andrasfuchs/BioBalanceDetector/Business/Bio_Balance_Detector_-_Business_Model_Canvas_v4.pdf

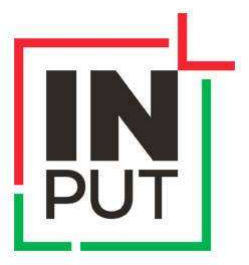
[picture p4: figure]

# Business Canvas Model

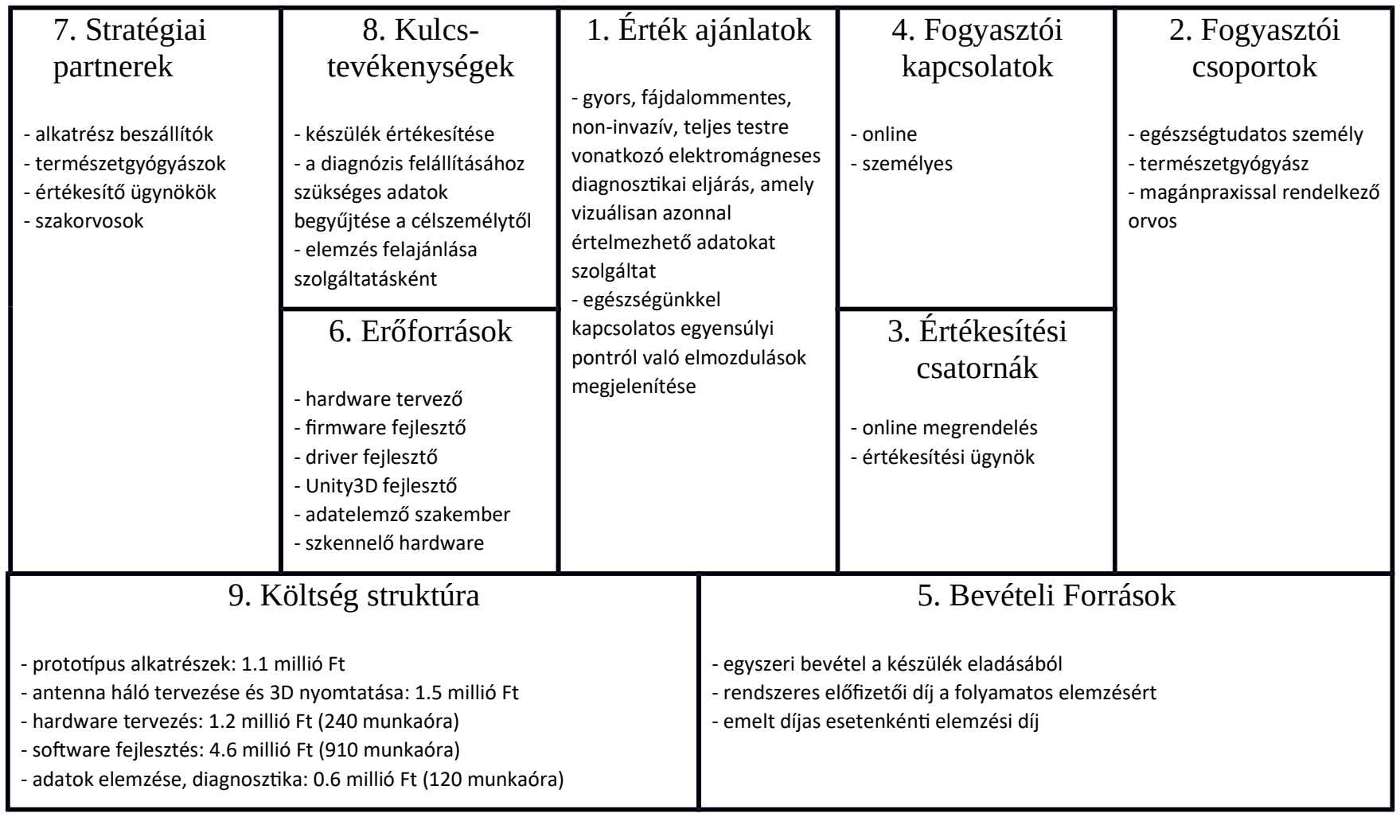
[picture p5: figure]
7. Stratégiai partnerek; - alkatrész beszállítók - természetgyógyászok - értékesítő ügynökök - szakorvosok; 8. Kulcs- tevékenységek; - készülék értékesítése - a diagnózis felállításához szükséges adatok begyűjtése a célszemélytől - elemzés felajánlása szolgáltatásként; 1. Érték ajánlatok; - gyors, fájdalommentes, non-invazív, teljes testre vonatkozó elektromágneses diagnoszkai eljárás, amely vizuálisan azonnal értelmezhető adatokat szolgáltat - egészségünkkel kapcsolatos egyensúlyi pontról való elmozdulások megjelenítése; 4. Fogyasztói kapcsolatok; - online - személyes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

- antenna háló tervezése és 3D nyomtatása: 1.5 millió Ft
- hardware tervezés: 1.2 millió Ft (240 munkaóra)
- soware fejlesztés: 4.6 millió Ft (910 munkaóra)
- adatok elemzése, diagnoszka: 0.6 millió Ft (120 munkaóra)
- egyszeri bevétel a készülék eladásából
- rendszeres előfizetői díj a folyamatos elemzésért
