andrasfuchs/BioBalanceDetector/Business/INPUT-BizDev_201804/INPUT-BizDev-Munkafuzet03_v1_KPI.pdf

### Végső célközönség: Természetgyógyászok

## KPI-ok

### Akvizíció

A fogyasztók figyelmének felkeltése, megszerzése, organikus és nem organikus módon.
Releváns KPIk: Forgalom, említések száma, kattintások költsége, keresési találatok, egy fogyasztó megszerzési költsége, megnyitása ráta

### Aktiváció

A látogatók aktív felhasználóvá tétele.
Releváns KPIk: Regisztrációk, bejelentkezések, befejezett onboarding folyamatok, szolgáltatás legalább egyszeri használata, feliratkozások, előfizetések

### Retention

A fogyasztók meggyőzése, hogy visszatérjenek, folyamatos felhasználói legyenek a terméknek/szolgáltatásnak.
Releváns KPIk: Engagement, legutóbbi látogatás óta eltelt idő, napi - heti aktív használók száma, lemorzsolódás.

### Bevétel

Az üzleti modell függvényében a bevétel keletkezése.
Releváns KPIk: Customer Lifetime Value, bevásárló kosár mérete, konverziós ráta, átkattintási ráta, sikeres vásárlások száma.

### Referálás

“Vírusos” Word of Mouth kommunikáció fogyasztók között. Egymásnak ajánlják a terméket. Releváns KPIk: Elküldött meghívók, Vírus terjedési ciklus, Vírus terjedési együttható?.

## Lean Canvas

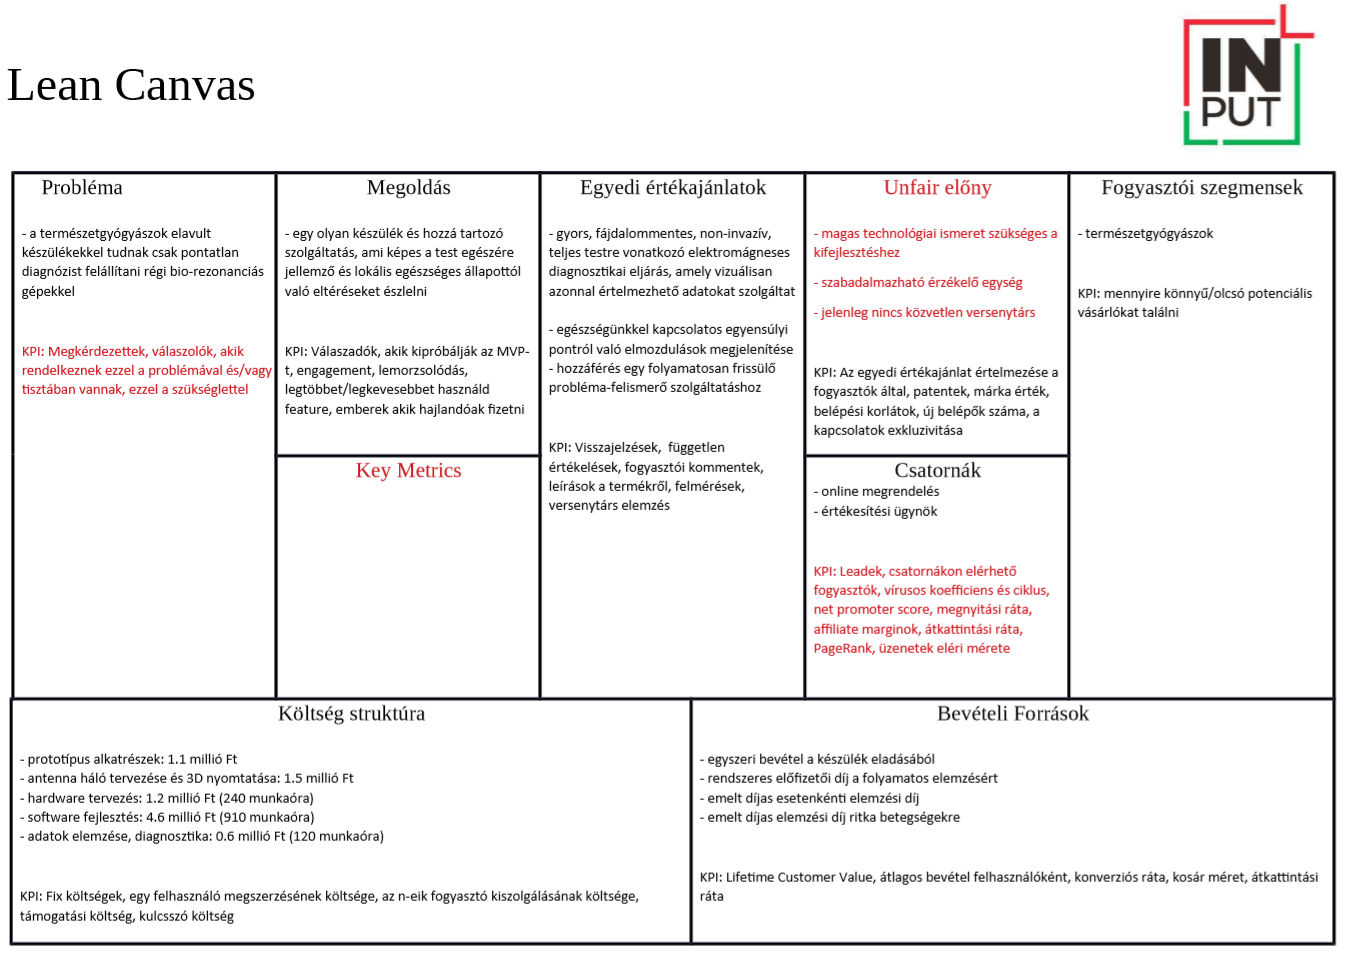
[picture p19: figure]

## Positioning

USP (Unique Selling Proposition)

Abszolút USP:
Gyors, fájdalommentes, non-invazív, teljes testre vonatkozó elektromágneses diagnosztikai eljárás, amely vizuálisan azonnal értelmezhető adatokat szolgáltat. A készülékhez tartozó szolgáltatás folyamatosan frissülő diagnosztikai paramétereknek köszönhetően egyre nagyobb biztonsággal egyre több betegséget egyre korábban képes felismerni.

Relatív UPS: a jelenleg versenytársnak tekinthető bio-rezonanciás készülékek nagyon drágák, 10 éves technológiára épülnek, lassúak, nem vizualizálják az eredményeket, és nem alkalmasak lokális diagnosztikára. Hozzájuk tartozó szolgáltatás nem létezik, vagy minimális hibajavítási ügyfélszolgálat.

## Online kampány
