andrasfuchs/BioBalanceDetector/Business/INPUT-BizDev_201804/INPUT-BizDev-Munkafuzet03_v3.pdf

### Elemek (Természetgyógyászok - magyar)

1. Főcím, alcím, emlékeztető (Unique Selling Proposition, USP)
a. Biorezonancia a jövőből
b. Megérkezett a biorezonanciás készülékek új generációja
2. Felnagyított Wacom tablet függőlegesen, előtte egy alak és mellette egy monitoron a hőkép a testről
3. Űrlap: Értesülj első kézből
Iratkozz fel, hogy megtudd, mi is a fizikai jelenség, amit megjelenítünk. Az akcióinkról is a listáról kapsz majd értesítést.
4. Ajánlat:

A forradalmi Bio Balance Detector fali érzékelő megállapítja, ha:
- Hőemelkedésed van, de nem tudod mitől?
- Fáradékony vagy és nem tudod az okát?
- Allergiás reakciód van és nem múlik el?
- Ki szeretnél gyógyulni az ételérzékenységből?
- Orvosról orvosra jársz, és nem tudják megmondani hol a baj?
- Kiváncsi vagy, hogy milyen állapotban van a tested, mire kell jobban figyelned?

Ha beállsz a Bio Balance Detector elé, a képernyőn egyből láthatod a figyelmet igénylő szerveidet! A készülékhez akkreditált szakembereink diagnózisát is kérheted egyetlen gombnyomással.
5. Bizonyíték
a. A számok magukért beszélnek.
Eddig 3’393 mérés készült, és 43’221 potenciális betegségre hívtuk fel a figyelmet. Benned vajon mennyi kórokozó lapul támadásra várva?
b. Nálunk a biztonság az első.
A Bio Balance Detector megfelel az ide vonatkozó ISO és IEEE szabványoknak, ráadásul teljesen passzív, non-invazív módon térképezi fel a testet körülvevő gyenge tereket.
c. Azonnali diagnózis Mesterséges Intelligenciával.
Az általunk fejlesztett, de mindenki által elérhető (és ellenőrizhető) mesterséges intelligencia segít a betegségek korai felfedezésében.
d. Távoli segítségnyújtás.
Ha bármilyen kérdés merül fel a mérés során, minősített szakembereink várják a kérdéseidet és kérésedre a mérései adatok alapján akár távoli diagnózist is fel tudnak állítani.

Template?
http://preview.themeforest.net/item/aonomy-app-landing-page/full_screen_preview/21460999

Paletta?
http://paletton.com/#uid=12x050k9GeI5jEL9bn6e07Lkl4n

### Elemek (Természetgyógyászok - angol)

6. Főcím, alcím, emlékeztető (Unique Selling Proposition, USP)
a. Bioresonance of the future
b. Next generation bioresonance device with Artificial Intelligence assisted diagnostics
7. Felnagyított Wacom tablet függőlegesen, előtte egy alak és mellette egy monitoron a hőkép a testről
8. Űrlap: Be the first to know
Subscribe to our newsletter to know more about the device and physical phenomena. You will be the first to know about our members-only discounts!
9. Ajánlat:

The revolutionary wall-mounted Bio Balance Detector can:
- Detect the part of your body where you have an inflammation
- Investigate the reason of your fatigue
- Find the focal point of your allergies
- Tell you if you have a food allergy/poisoning reaction
- Help with a diagnosis if the doctors can’t find the reason of your sickness
- Generate a report on your body’s current health condition

Step in front of the Bio Balance Detector and let the computer do work on the diagnostics. You will get a visual image of your organs with an indication of the places where attention is needed. If you need special assistance, you can send your data to our accredited specialists with just one click.
10. Bizonyíték
a. Our Numbers
We have successfully completed 3’393 measurements so far and potentially prevented 43’221 health issues. Are you curious what kinds of pathogens are living inside you waiting for the right moment to strike?
b. Safety First
Bio Balance Detector is certified by both ISO and IEEE, and to the top of that it works in a totally passive and non-invasive way to map out the weak electromagnetic field around our bodies.
c. Instant Diagnostics with AI
Our Artificial Intelligence algorithm is a product of our hard work and we made it open source. This level of transparency means that anybody can verify or extend our findings so it can detect more and more health issues as it matures.
d. Remote Assistance
Ha bármilyen kérdés merül fel a mérés során, minősített szakembereink várják a kérdéseidet és kérésedre a mérései adatok alapján akár távoli diagnózist is fel tudnak állítani.

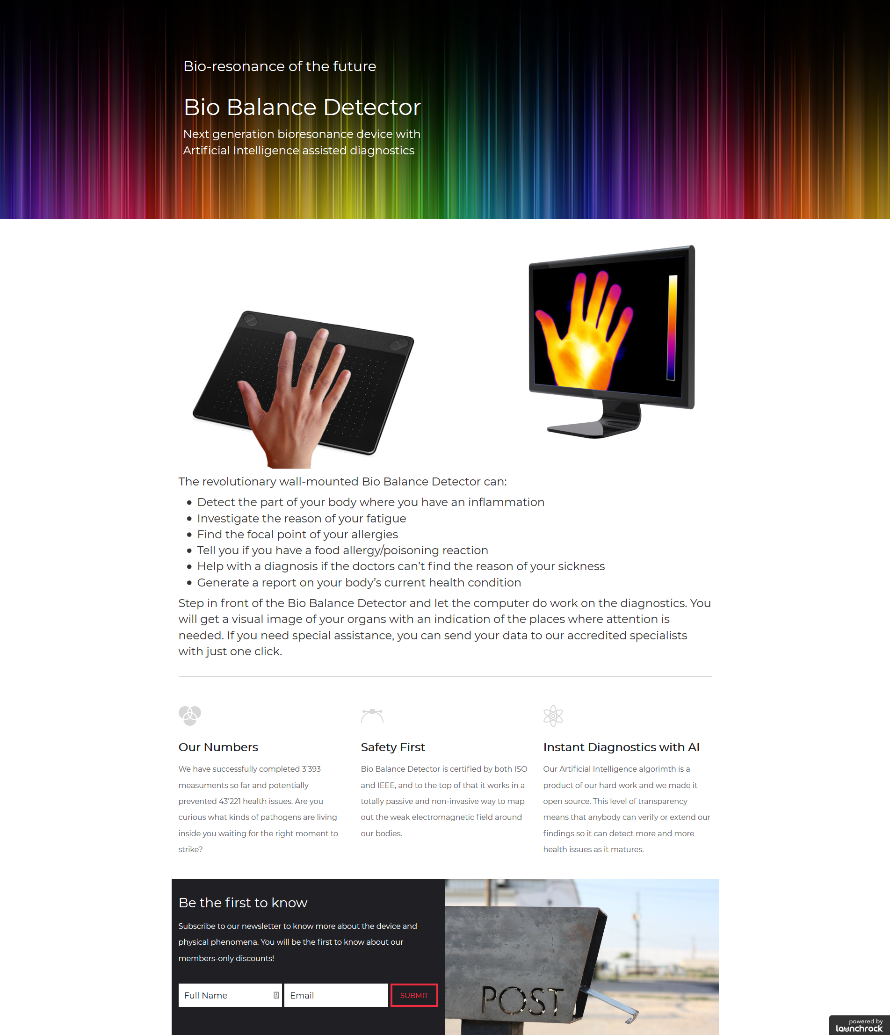
[picture p20: page 3]

http://biobalancedetector.launchrock.com/

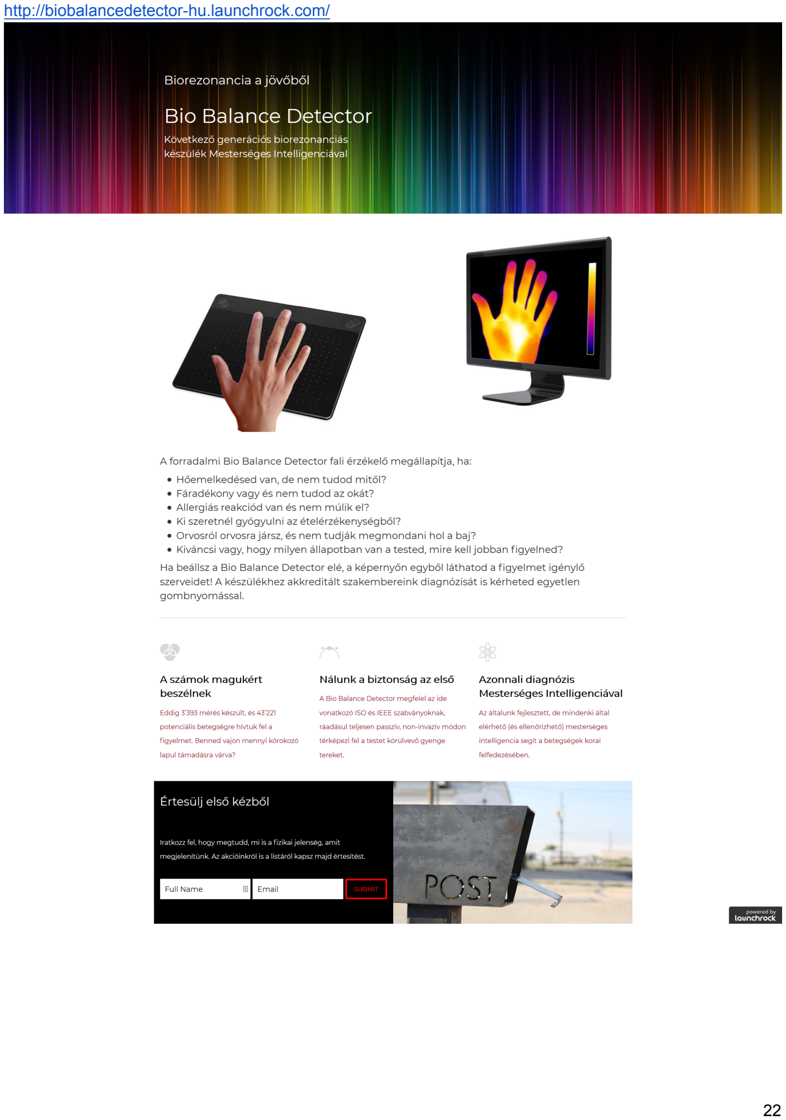
[picture p21: page 4]

http://biobalancedetector-hu.launchrock.com/

## KPI-ok

### Akvizíció

A fogyasztók figyelmének felkeltése, megszerzése, organikus és nem organikus módon.
Releváns KPIk: Forgalom, említések száma, kattintások költsége, keresési találatok, egy fogyasztó megszerzési költsége, megnyitása ráta

### Aktiváció

A látogatók aktív felhasználóvá tétele.
Releváns KPIk: Regisztrációk, bejelentkezések, befejezett onboarding folyamatok, szolgáltatás legalább egyszeri használata, feliratkozások, előfizetések

### Retention

A fogyasztók meggyőzése, hogy visszatérjenek, folyamatos felhasználói legyenek a terméknek/szolgáltatásnak.
Releváns KPIk: Engagement, legutóbbi látogatás óta eltelt idő, napi - heti aktív használók száma, lemorzsolódás.

### Bevétel

Az üzleti modell függvényében a bevétel keletkezése.
Releváns KPIk: Customer Lifetime Value, bevásárló kosár mérete, konverziós ráta, átkattintási ráta, sikeres vásárlások száma.

### Referálás

“Vírusos” Word of Mouth kommunikáció fogyasztók között. Egymásnak ajánlják a terméket. Releváns KPIk: Elküldött meghívók, Vírus terjedési ciklus, Vírus terjedési együttható?.

## Lean Canvas


## Positioning

USP (Unique Selling Proposition)

Abszolút USP:
Gyors, fájdalommentes, non-invazív, teljes testre vonatkozó elektromágneses diagnosztikai eljárás, amely vizuálisan azonnal értelmezhető adatokat szolgáltat. A készülékhez tartozó szolgáltatás folyamatosan frissülő diagnosztikai paramétereknek köszönhetően egyre nagyobb biztonsággal egyre több betegséget egyre korábban képes felismerni.

Relatív UPS: a jelenleg versenytársnak tekinthető bio-rezonanciás készülékek nagyon drágák, 10 éves technológiára épülnek, lassúak, nem vizualizálják az eredményeket, és nem alkalmasak lokális diagnosztikára. Hozzájuk tartozó szolgáltatás nem létezik, vagy minimális hibajavítási ügyfélszolgálat.

## Online kampány

### Google Adwords

Campaign: BBD LaunchRock Landing Page Test #1 [1,500.00 HUF/day]

Keywords (by Google Keyword Planner)
best bioresonance machine
bio resonance device
bio resonance testing machine bioresonance device
bioresonance machine
bioresonance machine for sale bioresonance machine price bioresonance scanning
bioresonance testing
bioresonance therapy
bioresonance therapy devices bioresonance therapy machine

Ad
biobalancedetector.launchrock.com/
Bio Balance Detector | Bioresonance Device
Quick, painless, non-invasive, whole body bio-resonance device with AI imaging

### Facebook Ads Manager

Az Ads Manager és a Power Editor most már egy alkalmazás és a jobb felső sarokban lévő háromszöggel lehet elővarázsolni.

TODO: Facebook Page is kell hozzá

TODO: fókuszáltabb célcsoport kellene: nem, életkor, érdeklődési körök -> vissza a Customer Persona Map-hez és Customer Empathy Map-hez

TODO: Facebook Form-oknál mik a jobban működő módszerek

Campaign:
BBD LaunchRock Landing Page Test #2

Ad Set ame:
US-UK - 45+ - Healthy Living (26M reach)

Audience
45-65+ Healthy living

Location:
United Kingdom, United States

Age:
45 - 65+

Language:
English (UK) or English (US)

People Who Match:
Interests: Organic food, Personal care, Healthy food, Living a Healthy Lifestyle, Health & wellness, Living Healthy, Detox, Diet food, Anti-aging cream, Healthy Life, Natural foods or Organic product, Behaviors: Natural and organics

Interest expansion:
Off

Ad

Text
Quick, painless, non-invasive, whole body bio-resonance device with AI imaging

Display Link
biobalancedetector.launchrock.com/

Headline
High-tech Bioresonance

News Feed Link Description Say no to drugs,get better faster!

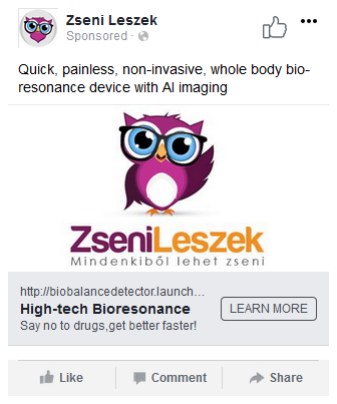
[picture p22: figure]
