andrasfuchs/BioBalanceDetector/Hardware/Design/BBD-Proto6-Functional_Diagram_v1.pdf

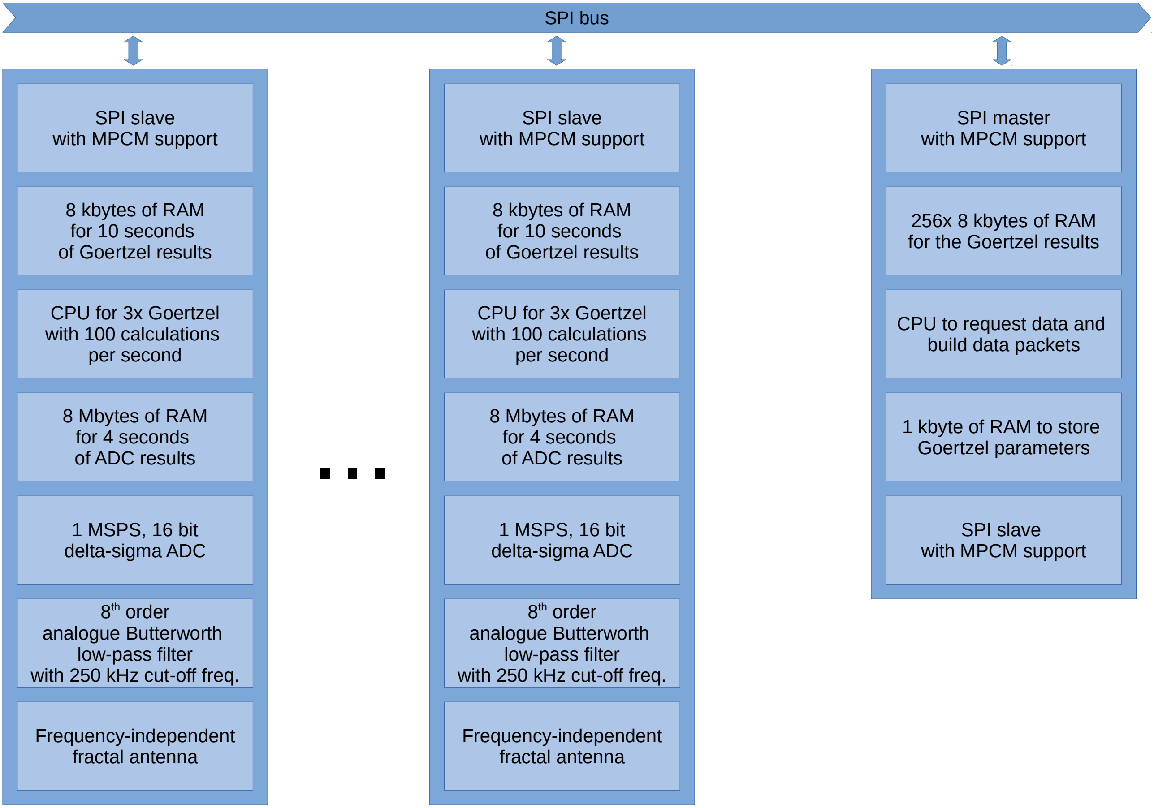
[picture p23: figure]
1 MSPS, 16 bit delta-sigma ADC; th order analogue Butterworth low-pass filter with 250 kHz cut-off freq.; Frequency-independent fractal antenna; 8 Mbytes of RAM for 4 seconds of ADC results; CPU for 3x Goertzel with 100 calculations per second; 8 kbytes of RAM for 10 seconds of Goertzel results; SPI slave with MPCM support; 1 kbyte of RAM to store Goertzel parameters; CPU to request data and build data packets; 256x 8 kbytes of RAM for the Goertzel results; SPI master with MPCM support; SPI bus
