andrasfuchs/BioBalanceDetector/Business/Bio_Balance_Detector_-_Business_Model_Canvas_v1.pdf

# Business Canvas Model

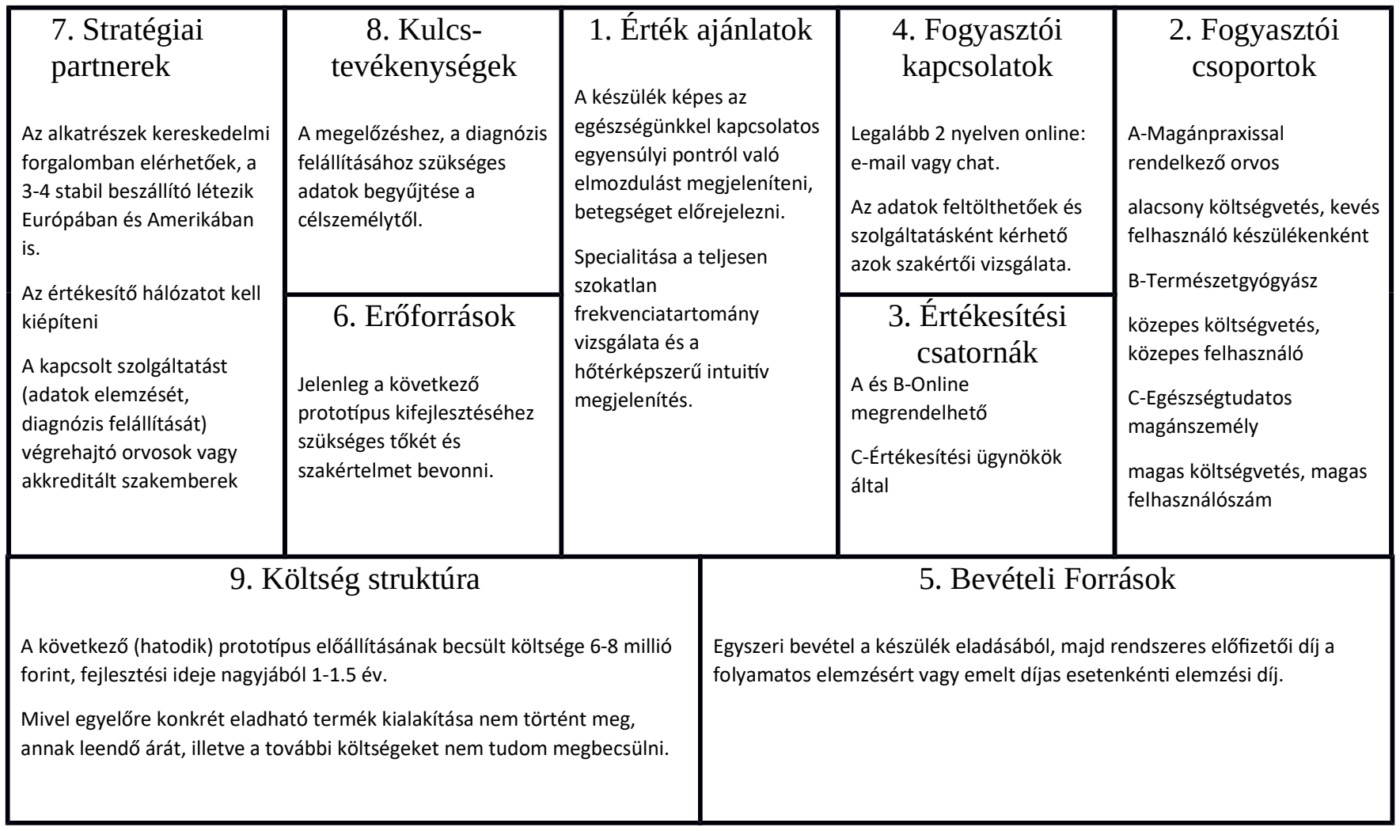
[picture p24: figure]
7. Stratégiai partnerek; Az alkatrészek kereskedelmi forgalomban elérhetőek, a 3-4 stabil beszállító létezik Európában és Amerikában is.; Az értékesítő hálózatot kell kiépíteni; A kapcsolt szolgáltatást (adatok elemzését, diagnózis felállítását) végrehajtó orvosok vagy akkreditált szakemberek; 8. Kulcs- tevékenységek; A megelőzéshez, a diagnózis felállításához szükséges adatok begyűjtése a célszemélytől.; 1. Érték ajánlatok; A készülék képes az egészségünkkel kapcsolatos egyensúlyi pontról való elmozdulást megjeleníteni, betegséget előrejelezni.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

A következő (hatodik) protopus előállításának becsült költsége 6-8 millió forint, fejlesztési ideje nagyjából 1-1.5 év.
Mivel egyelőre konkrét eladható termék kialakítása nem történt meg, annak leendő árát, illetve a további költségeket nem tudom megbecsülni.

Egyszeri bevétel a készülék eladásából, majd rendszeres előfizetői díj a folyamatos elemzésért vagy emelt díjas esetenkén elemzési díj.
