andrasfuchs/BioBalanceDetector/Business/Bio_Balance_Detector_-_Business_Model_Canvas_v2.pdf

# Business Canvas Model

### 7. Stratégiai partnerek

Az alkatrészek kereskedelmi forgalomban elérhetőek, 3-

### 4 stabil beszállító létezik

Európában és Amerikában
is.
Az értékesítő hálózatot kell kiépíteni, az ügynököket
jutalmazni.
A kapcsolt szolgáltatást
(adatok elemzését,
diagnózis felállítását)
végrehajtó orvosokat vagy
akkreditált szakembereket
ki kell képezni, és össze kell kötni az őket igénylőkkel.

### 8. Kulcstevékenységek

A megelőzéshez, a diagnózis felállításához szükséges
adatok begyűjtése a
célszemélytől.
Elemzés felajánlása
szolgáltatásként.

### 1. Érték ajánlatok

A készülék képes az
egészségünkkel kapcsolatos egyensúlyi pontról való
elmozdulást megjeleníteni, betegséget előrejelezni.
Specialitása a teljesen
szokatlan
frekvenciatartomány
vizsgálata és a
hőtérképszerű intuiv
megjelenítés.

### 4. Fogyasztói kapcsolatok

Több nyelven online: e-mailben vagy chat-en.
Az adatok feltölthetőek és szolgáltatásként kérhető
azok szakértői vizsgálata.


### 2. Fogyasztói csoportok

A-Egészségtudatos
magánszemély
alacsony költségvetés, kevés felhasználó készülékenként B-Természetgyógyász
közepes költségvetés,
közepes felhasználószám
C-Magánpraxissal
rendelkező orvos
magas költségvetés, magas
felhasználószám

### 6. Erőforrások

Jelenleg a következő
protopus kifejlesztéséhez szükséges tőkét és
szakértelmet szükséges
bevonni.

### 3. Értékesítési csatornák

A és B-Online
megrendelhető
C-Értékesítési ügynökök
segítségével (mint a
gyógyszereknél)

### 9. Költség struktúra

A következő (hatodik) protopus előállításának becsült költsége 6-8 millió forint, fejlesztési ideje nagyjából 1-1.5 év.
Mivel egyelőre konkrét eladható termék kialakítása nem történt meg, annak leendő árát, illetve a további költségeket nem tudom megbecsülni.

### 5. Bevételi Források

Egyszeri bevétel a készülék eladásából, majd rendszeres előfizetői díj a folyamatos elemzésért (nagy forgalmú helyeken, mint pl. orvosi rendelők) vagy emelt díjas esetenkén elemzési díj (magánszemélyeknek).
