andrasfuchs/BioBalanceDetector/Business/Bio_Balance_Detector_-_Pitch-deck_background.png

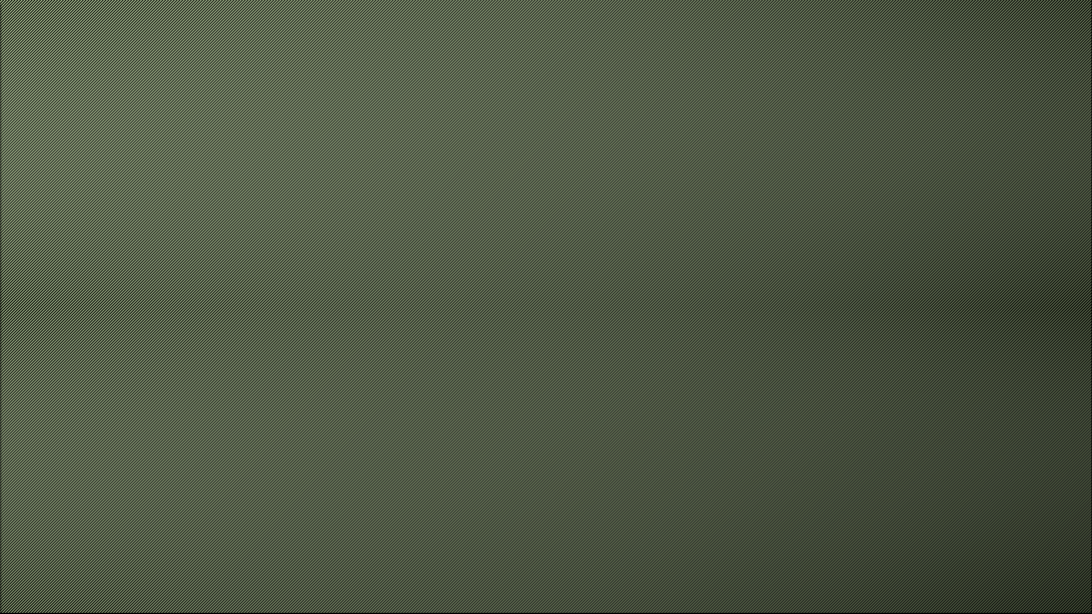
Business/Bio_Balance_Detector_-_Pitch-deck_background.png
