andrasfuchs/BioBalanceDetector/Business/INPUT-BizDev_201804/abstract-rainbow-colors.jpg

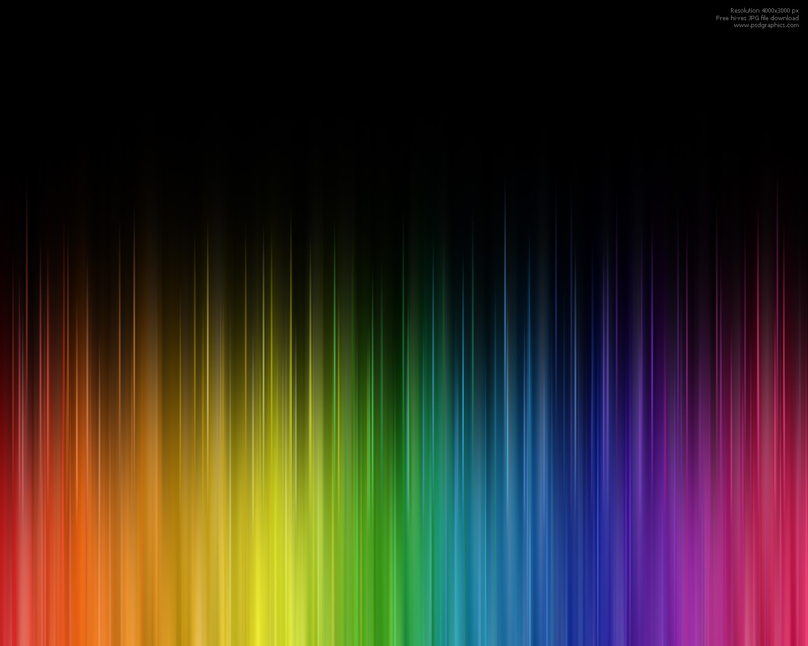
Business/INPUT-BizDev_201804/abstract-rainbow-colors.jpg
