andrasfuchs/BioBalanceDetector/Business/INPUT-BizDev_201804/TabletHandMonitor.jpg

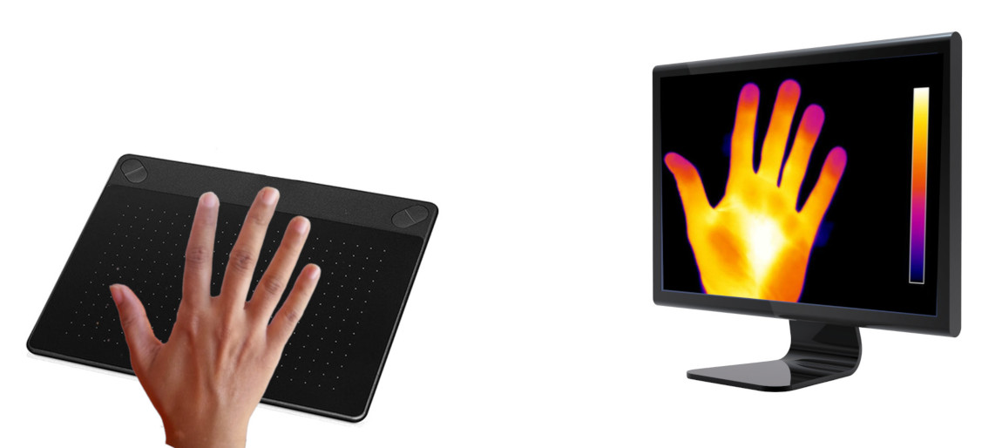
Business/INPUT-BizDev_201804/TabletHandMonitor.jpg
