andrasfuchs/BioBalanceDetector/Business/INPUT-BizDev_201804/TabletHandMonitor/InfraredHand.jpg

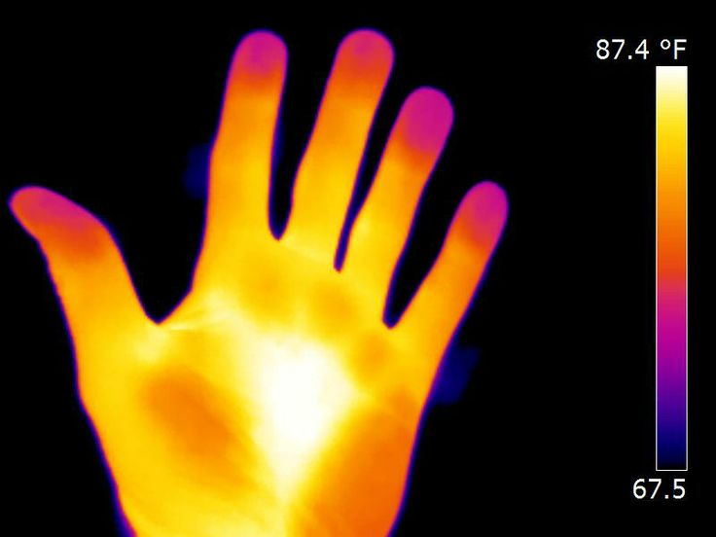
Business/INPUT-BizDev_201804/TabletHandMonitor/InfraredHand.jpg
