andrasfuchs/BioBalanceDetector/Hardware/Datasheets/Proto04/Arduino_Uno_Poster-1024x577.jpg

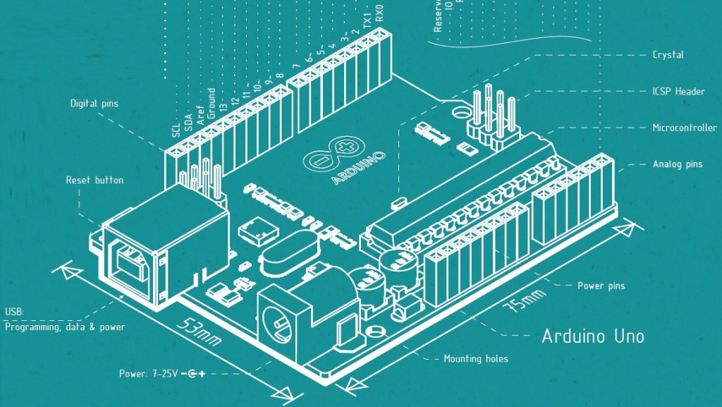
Hardware/Datasheets/Proto04/Arduino_Uno_Poster-1024x577.jpg
