andrasfuchs/BioBalanceDetector/Hardware/Datasheets/Proto04/BraveKit-AVR-ISPmk2-CL/USB_AVR_mkII_with_DIPprog-600x600.jpg

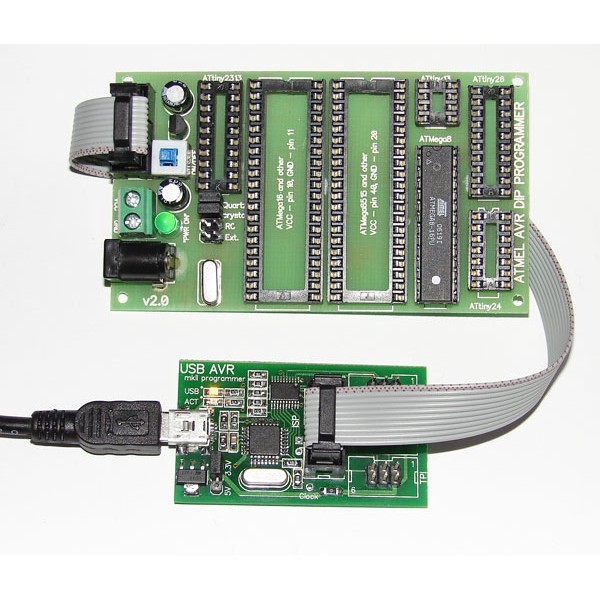
Hardware/Datasheets/Proto04/BraveKit-AVR-ISPmk2-CL/USB_AVR_mkII_with_DIPprog-600x600.jpg
