andrasfuchs/BioBalanceDetector/Hardware/Datasheets/Proto06/Analog_Devices_AD7616_functional_block_diagram.png

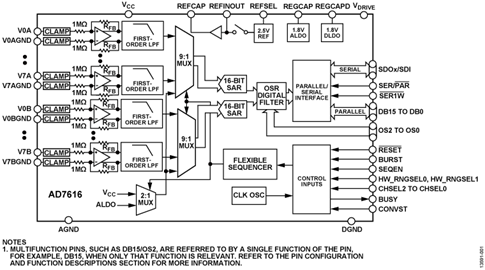
Hardware/Datasheets/Proto06/Analog_Devices_AD7616_functional_block_diagram.png
