andrasfuchs/BioBalanceDetector/Hardware/Design/Antenna/sierpinski_triangle_by_love1008.jpg

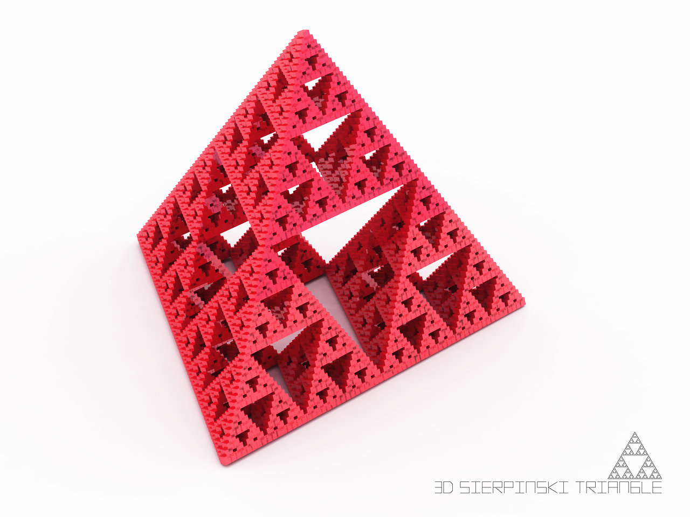
Hardware/Design/Antenna/sierpinski_triangle_by_love1008.jpg
