andrasfuchs/BioBalanceDetector/Hardware/Design/BBD-Proto6-Functional_Diagram_v2.png

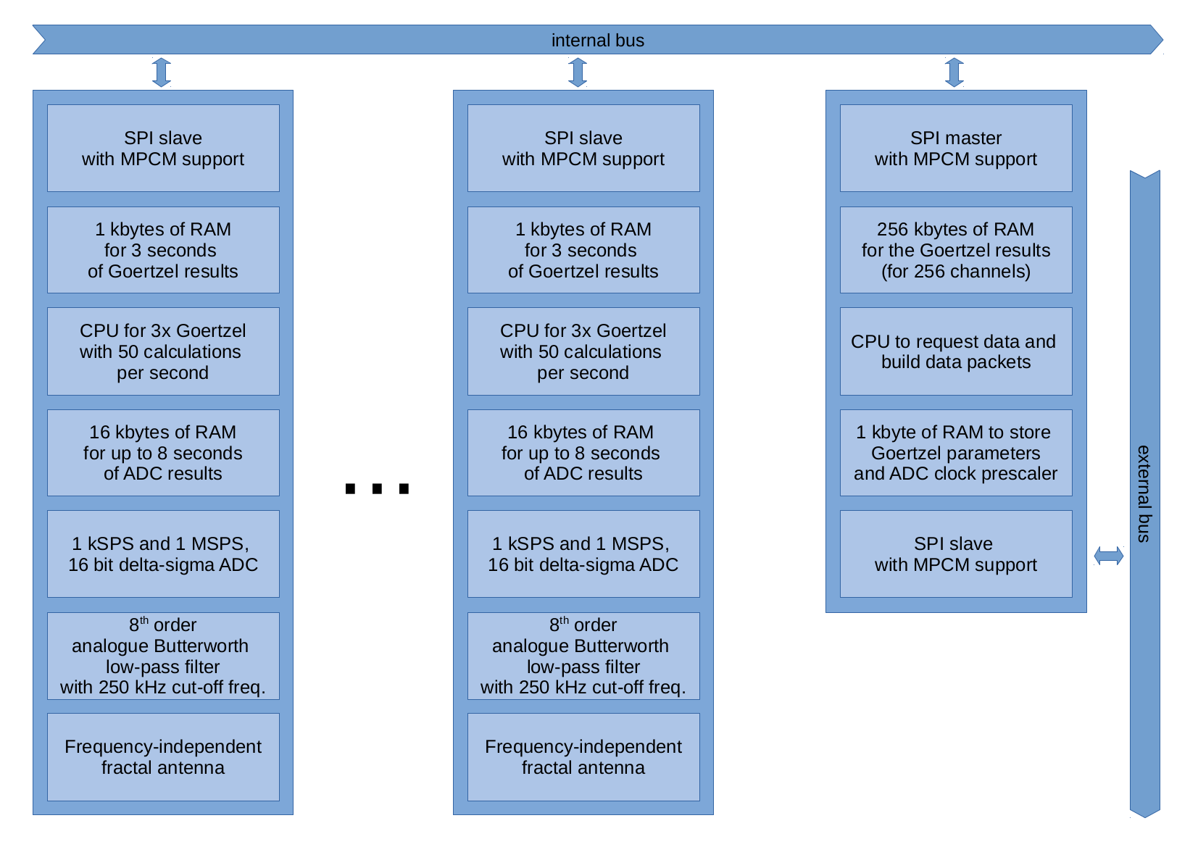
Hardware/Design/BBD-Proto6-Functional_Diagram_v2.png
