andrasfuchs/BioBalanceDetector/Hardware/Design/fractal-9-728.jpg

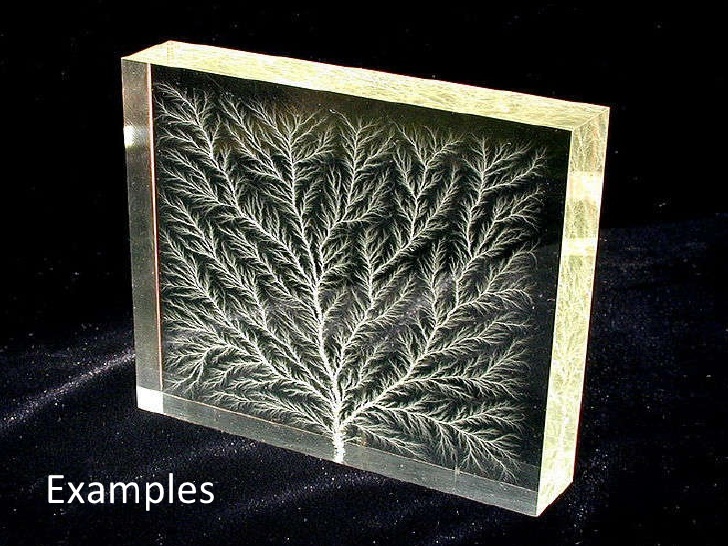
Hardware/Design/fractal-9-728.jpg
