andrasfuchs/BioBalanceDetector/Hardware/Design/fractals-in-nature-wallpapers-full-hd.jpg

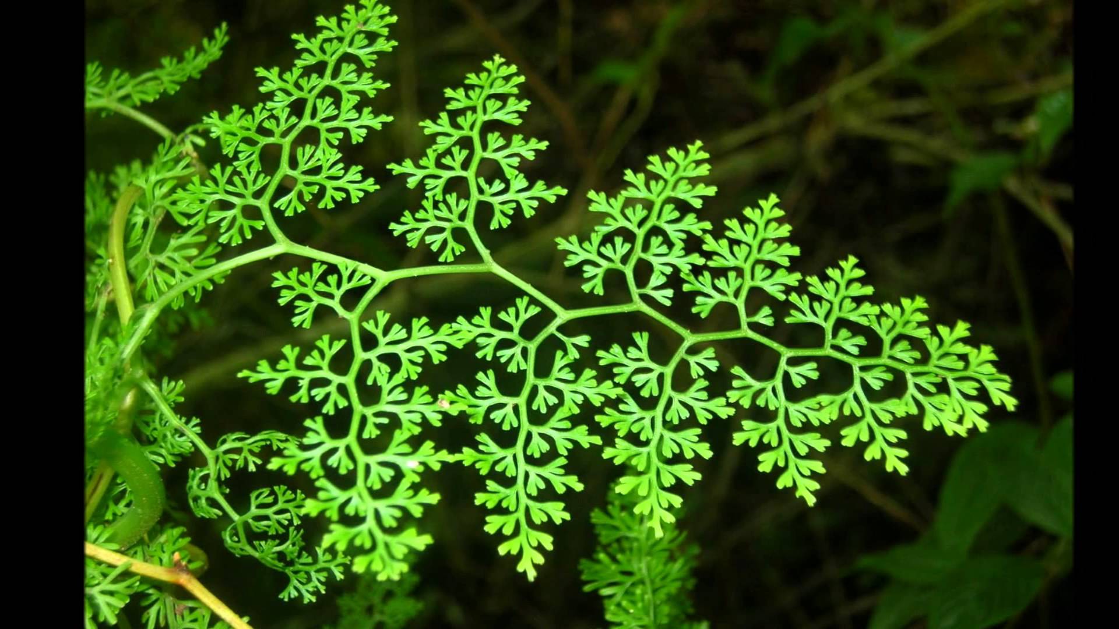
Hardware/Design/fractals-in-nature-wallpapers-full-hd.jpg
