andrasfuchs/BioBalanceDetector/Measurements/Spooky2/01_IrregularVoltageReport/02_AmbientRadiation-PowerAdapterDisconnected.png

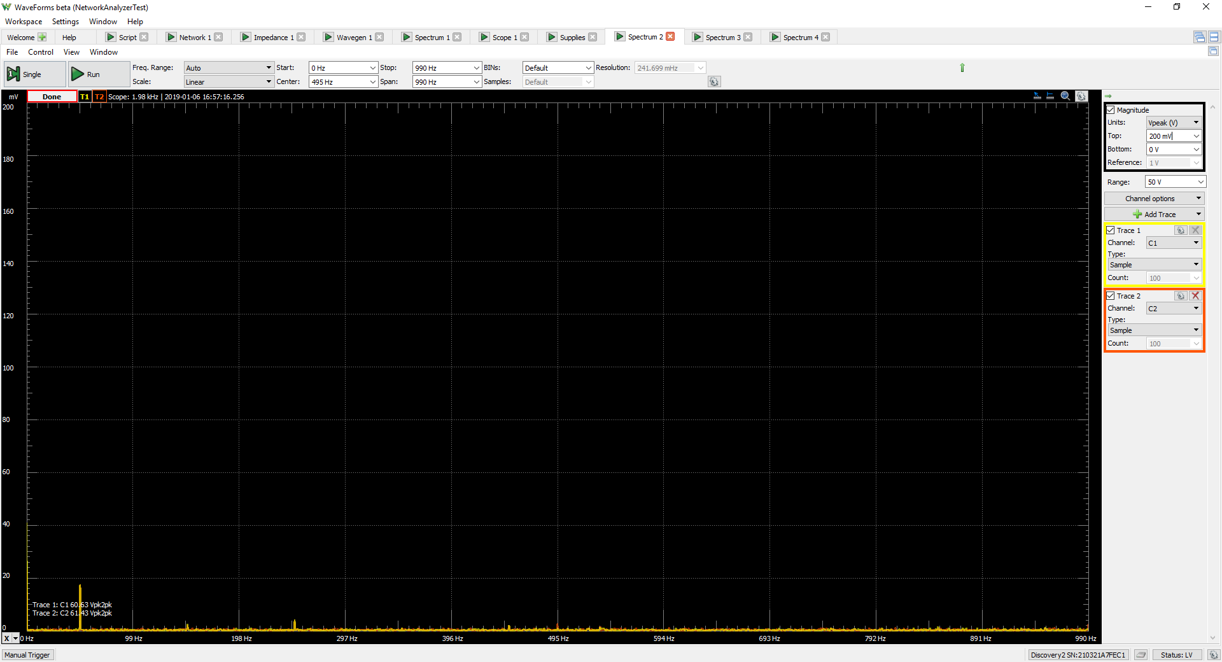
Measurements/Spooky2/01_IrregularVoltageReport/02_AmbientRadiation-PowerAdapterDisconnected.png
