andrasfuchs/BioBalanceDetector/Measurements/Spooky2/01_IrregularVoltageReport/04_PowerAdapterConnectedPoweredOff_200mV.png

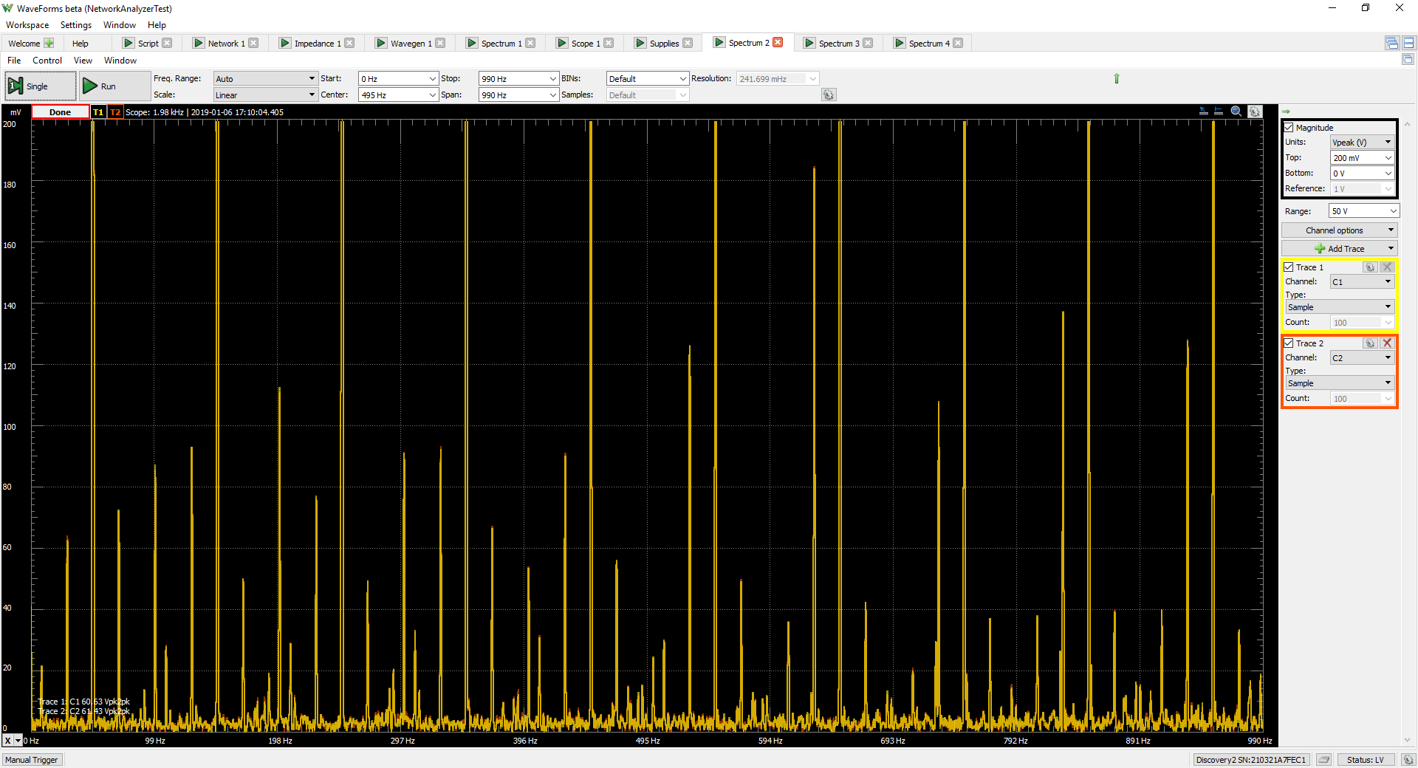
Measurements/Spooky2/01_IrregularVoltageReport/04_PowerAdapterConnectedPoweredOff_200mV.png
