andrasfuchs/BioBalanceDetector/Measurements/Spooky2/01_IrregularVoltageReport/05_PowerAdapterConnectedPoweredOff_25V.png

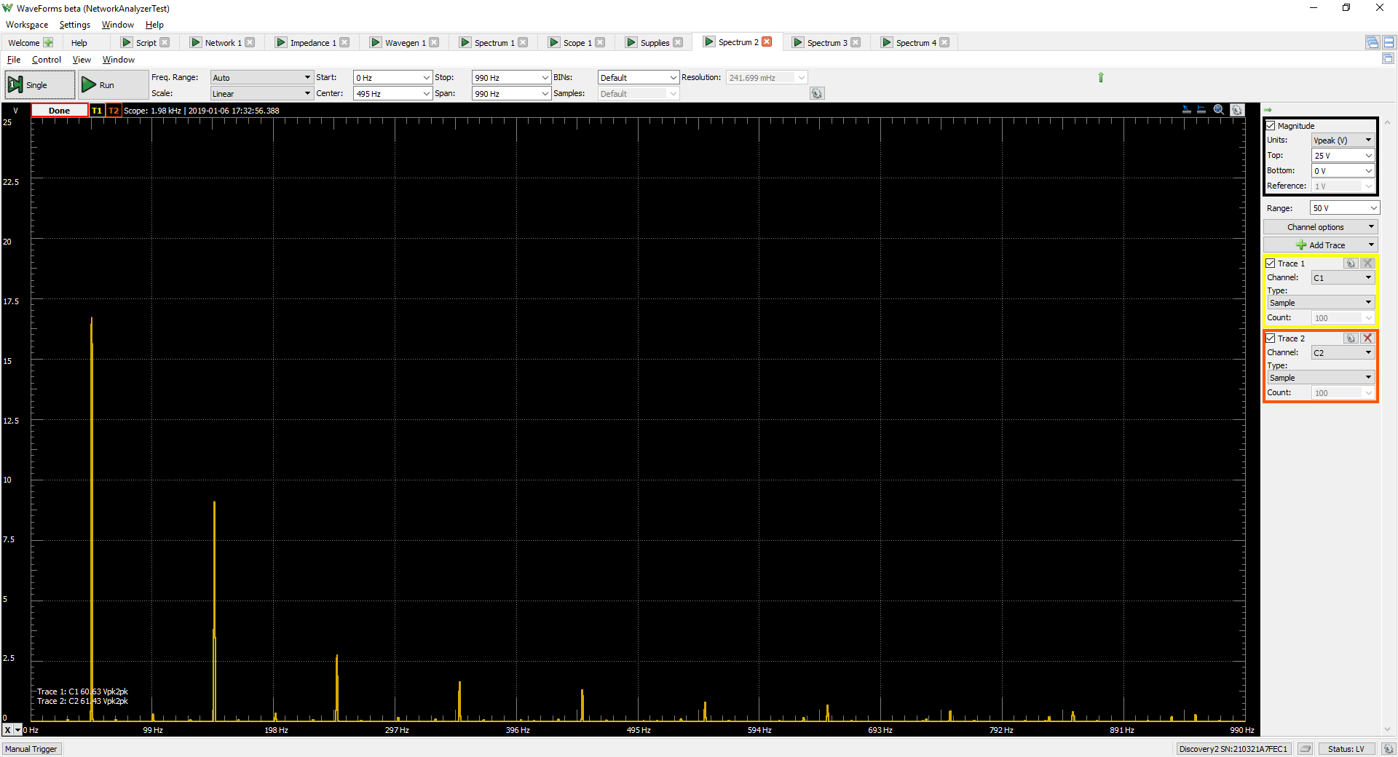
Measurements/Spooky2/01_IrregularVoltageReport/05_PowerAdapterConnectedPoweredOff_25V.png
