andrasfuchs/BioBalanceDetector/Measurements/Spooky2/01_IrregularVoltageReport/06_PowerAdapterConnectedPoweredOn_25V.png

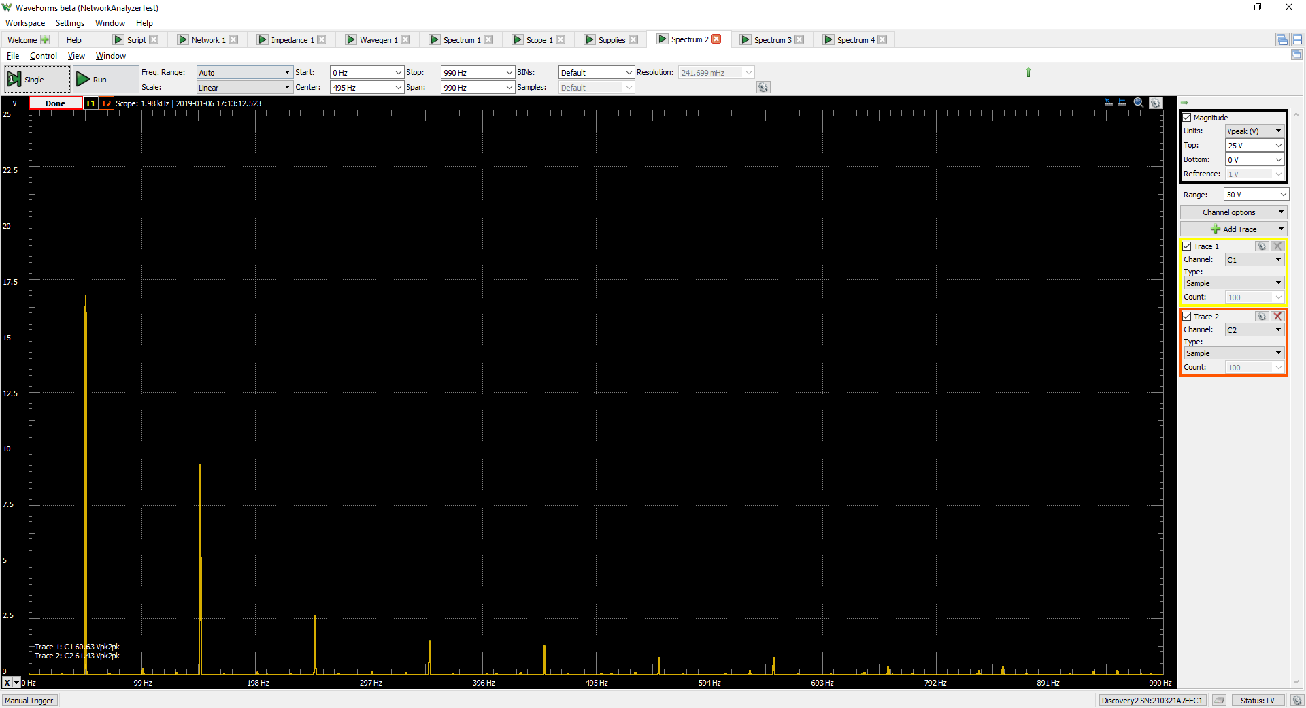
Measurements/Spooky2/01_IrregularVoltageReport/06_PowerAdapterConnectedPoweredOn_25V.png
