andrasfuchs/BioBalanceDetector/Measurements/Spooky2/01_IrregularVoltageReport/07_PowerAdapterConnectedPoweredOn_422-442Hz_2V.png

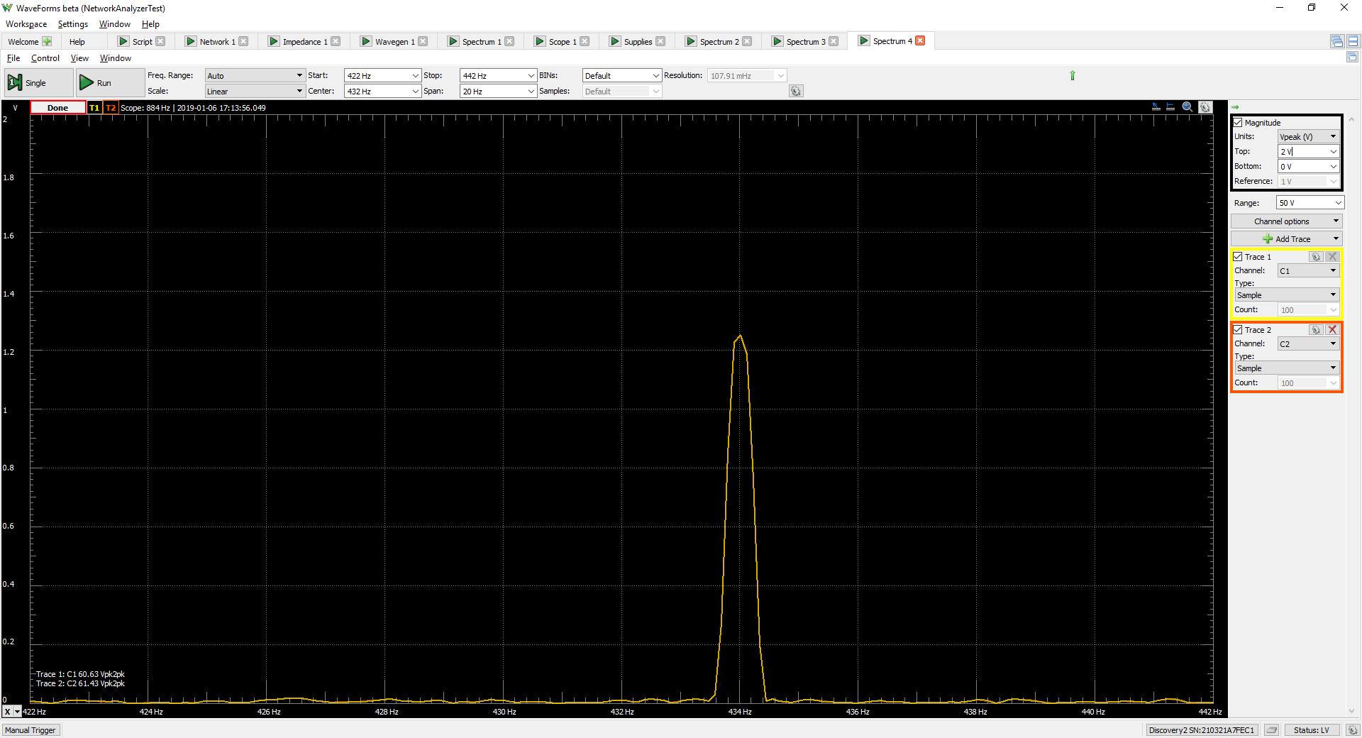
Measurements/Spooky2/01_IrregularVoltageReport/07_PowerAdapterConnectedPoweredOn_422-442Hz_2V.png
