andrasfuchs/BioBalanceDetector/Measurements/Spooky2/01_IrregularVoltageReport/08_Spooky2Settings.png

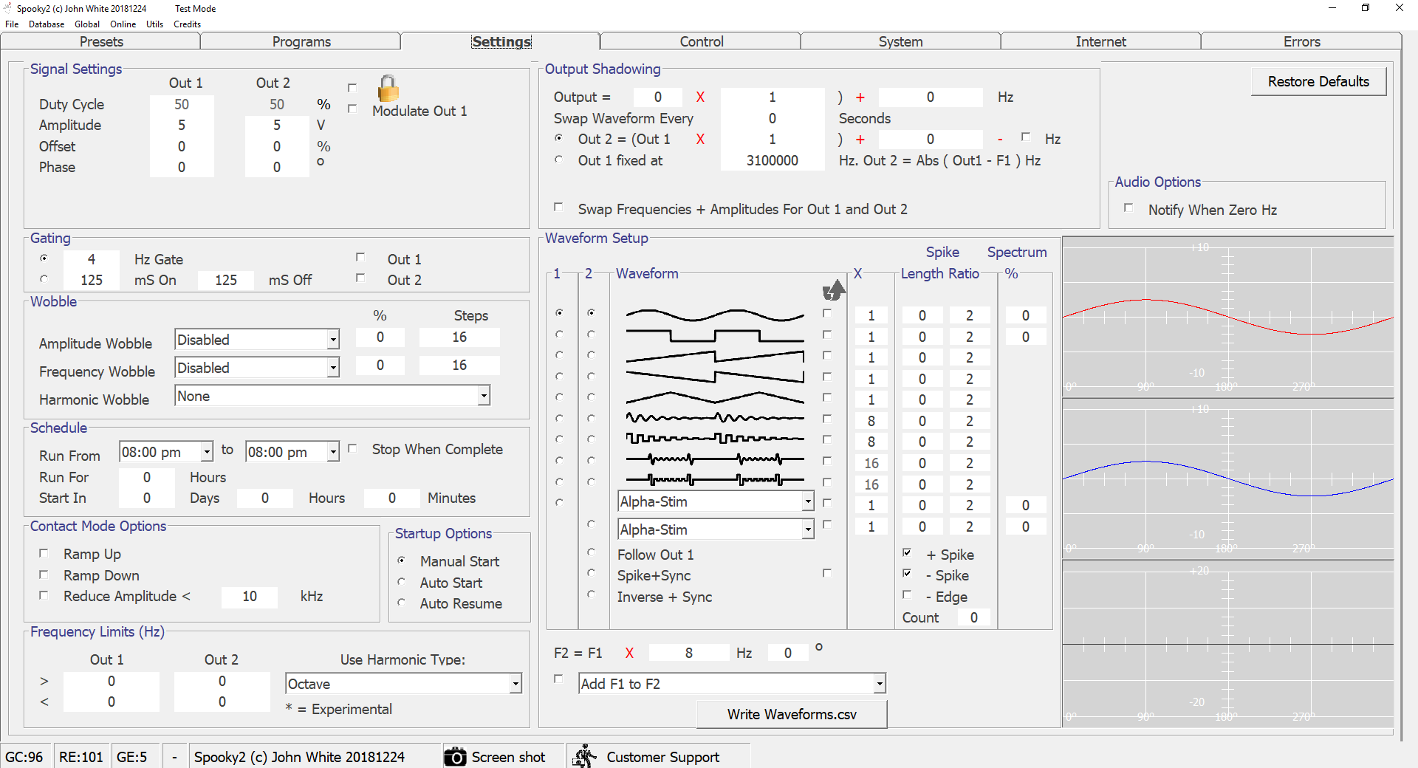
Measurements/Spooky2/01_IrregularVoltageReport/08_Spooky2Settings.png
