andrasfuchs/BioBalanceDetector/Measurements/Spooky2/01_IrregularVoltageReport/09_Spooky2Control_432Hz.png

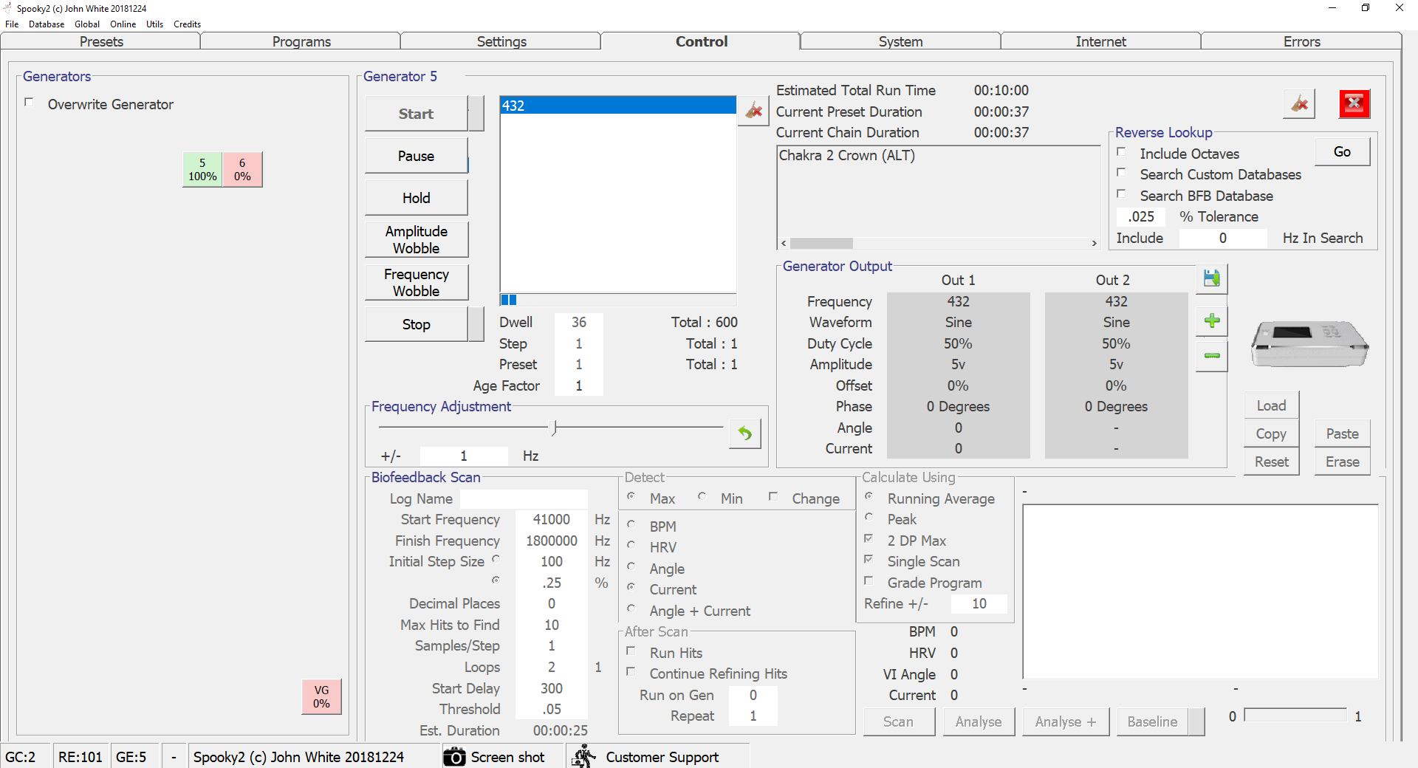
Measurements/Spooky2/01_IrregularVoltageReport/09_Spooky2Control_432Hz.png
