andrasfuchs/BioBalanceDetector/Measurements/Spooky2/01_IrregularVoltageReport/10_PowerAdapterConnectedPoweredOn-G1Sin432Hz_422-442Hz_2V.png

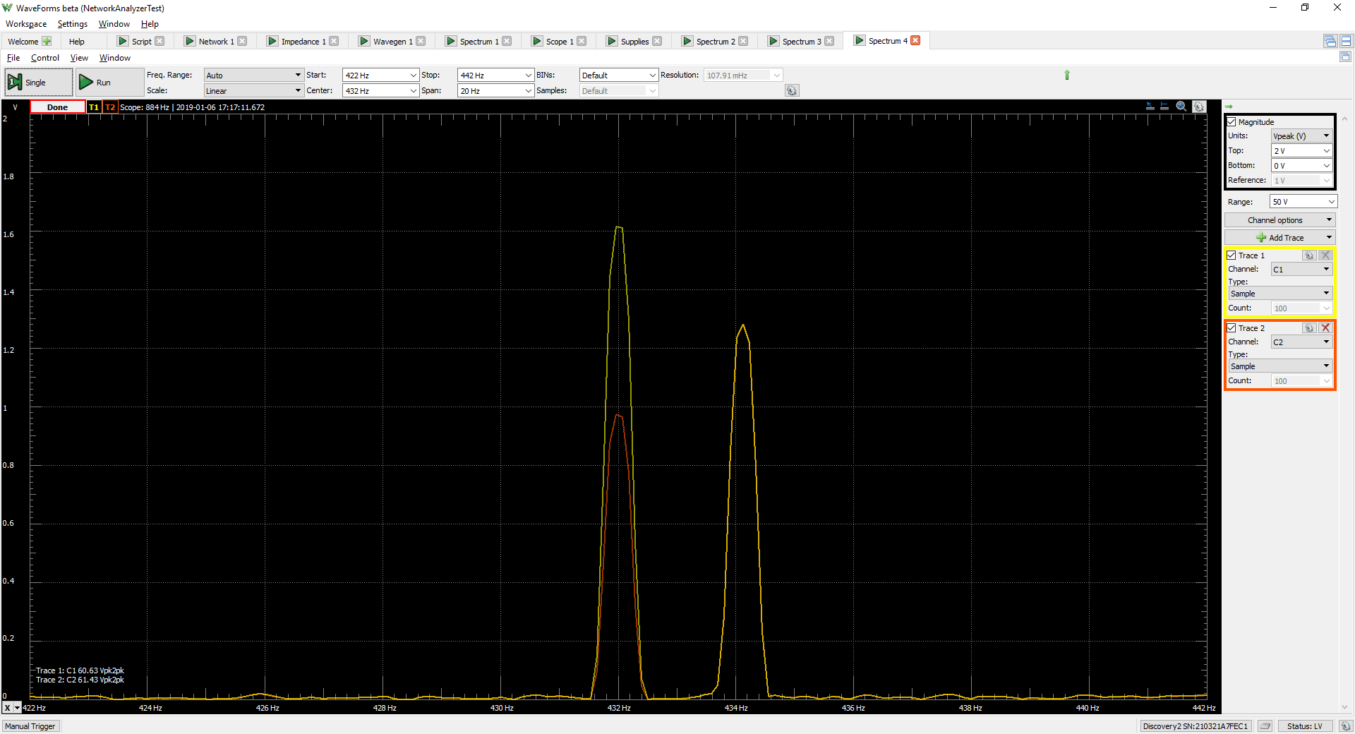
Measurements/Spooky2/01_IrregularVoltageReport/10_PowerAdapterConnectedPoweredOn-G1Sin432Hz_422-442Hz_2V.png
