andrasfuchs/BioBalanceDetector/Measurements/Spooky2/02_WithBatteryReport/01_BatteryConnectedPoweredOn_25V.png

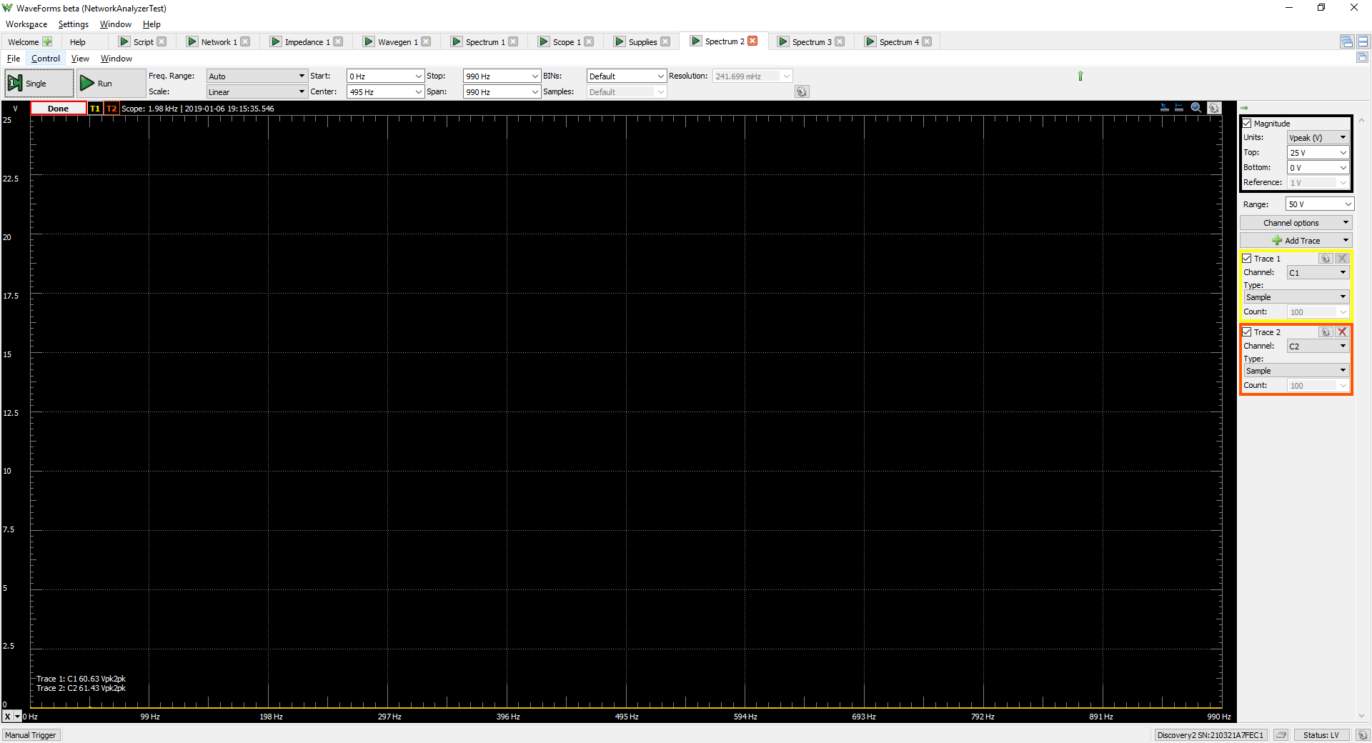
Measurements/Spooky2/02_WithBatteryReport/01_BatteryConnectedPoweredOn_25V.png
