andrasfuchs/BioBalanceDetector/Measurements/Spooky2/02_WithBatteryReport/03_BatteryConnectedPoweredOn_40-60Hz_200mV.png

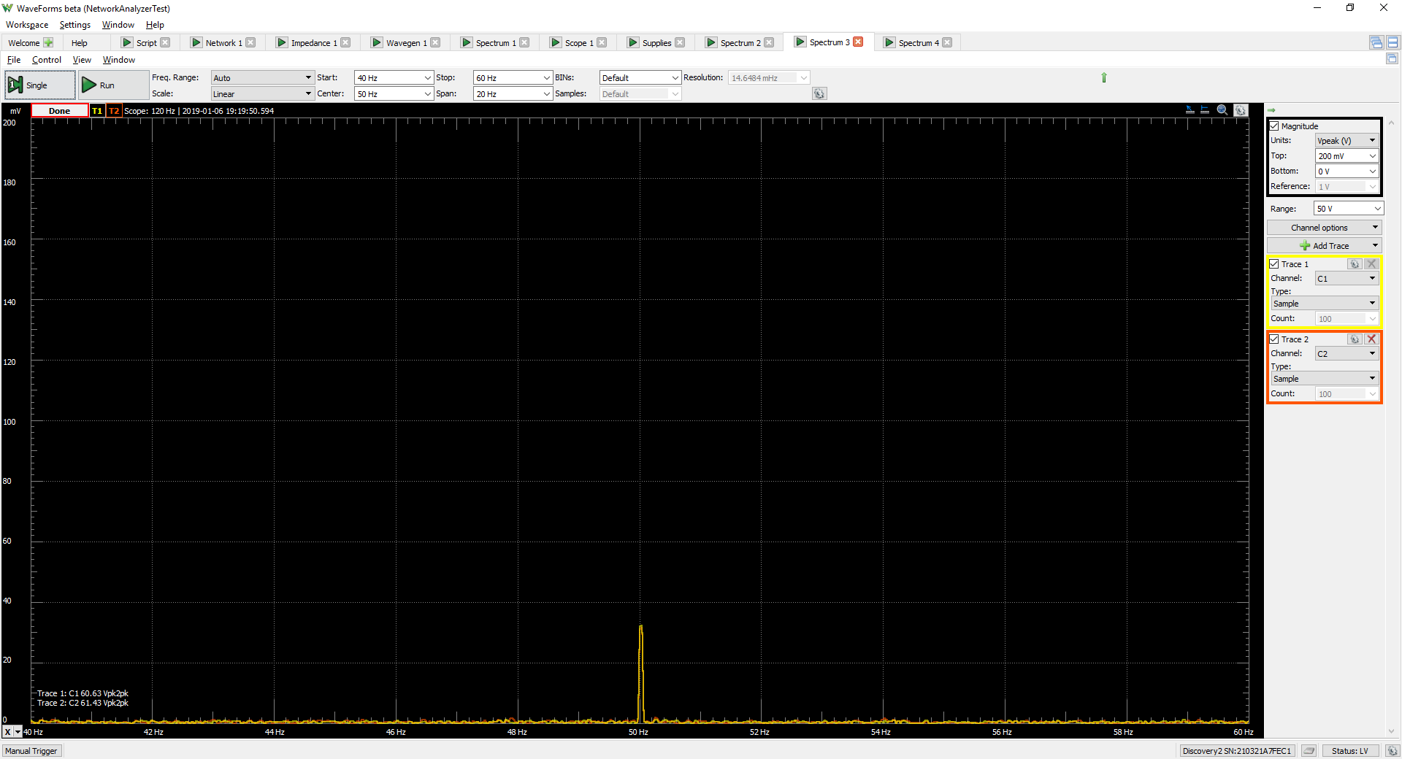
Measurements/Spooky2/02_WithBatteryReport/03_BatteryConnectedPoweredOn_40-60Hz_200mV.png
