andrasfuchs/BioBalanceDetector/Measurements/Spooky2/02_WithBatteryReport/07_BatteryConnectedPoweredOn-G1Sin432Hz_422-442Hz_2V.png

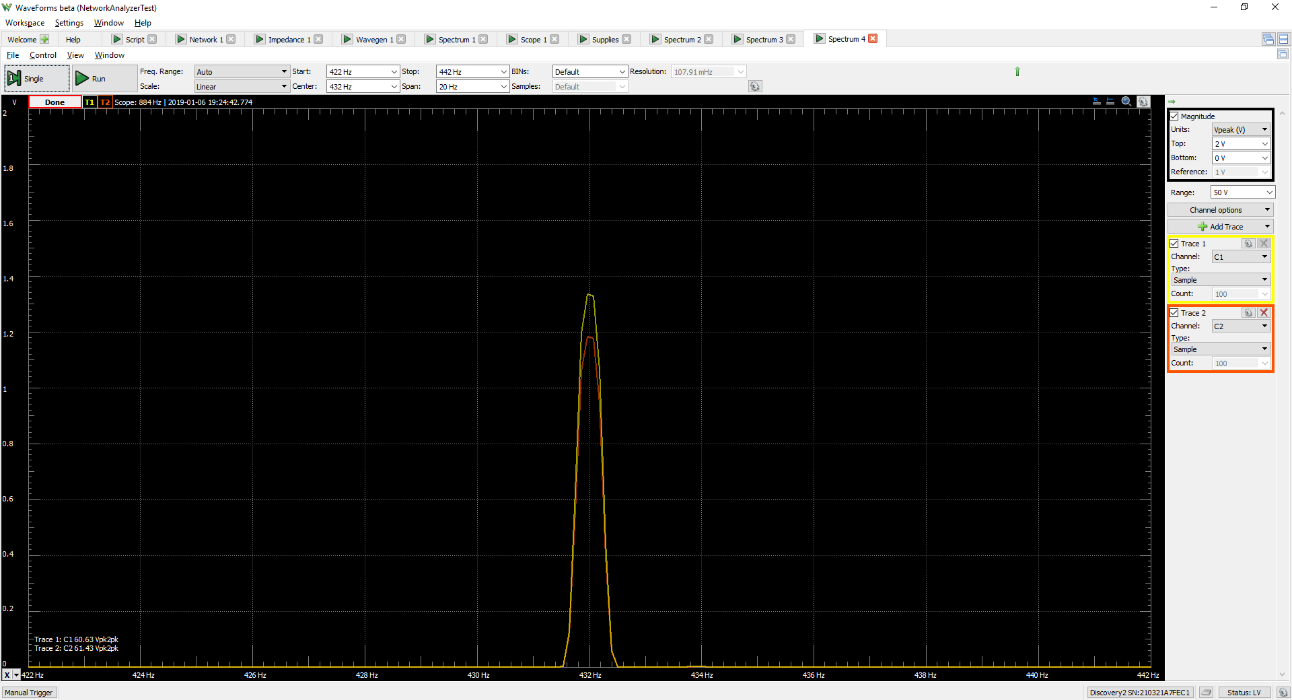
Measurements/Spooky2/02_WithBatteryReport/07_BatteryConnectedPoweredOn-G1Sin432Hz_422-442Hz_2V.png
