andrasfuchs/BioBalanceDetector/Measurements/Spooky2/02_WithBatteryReport/08_BatteryConnectedPoweredOn-G1BFB_10V.png

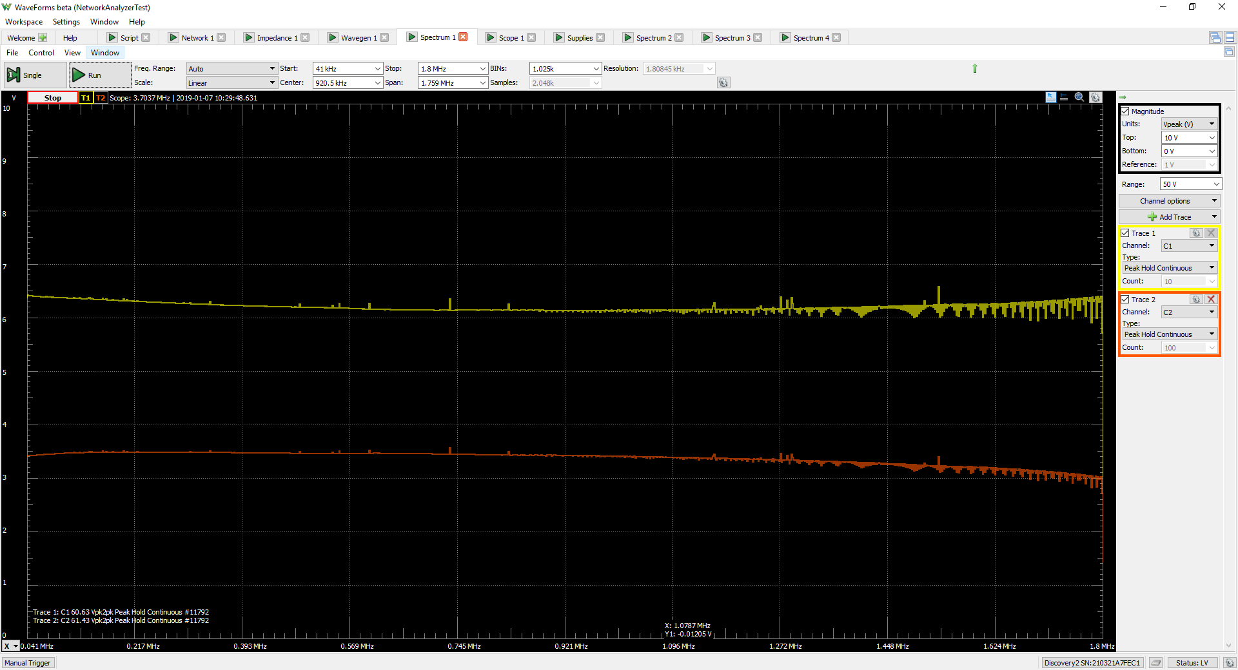
Measurements/Spooky2/02_WithBatteryReport/08_BatteryConnectedPoweredOn-G1BFB_10V.png
