andrasfuchs/BioBalanceDetector/Measurements/Spooky2/02_WithBatteryReport/09_ProfessionalSignalGenerator-BFBRange5V_10V.png

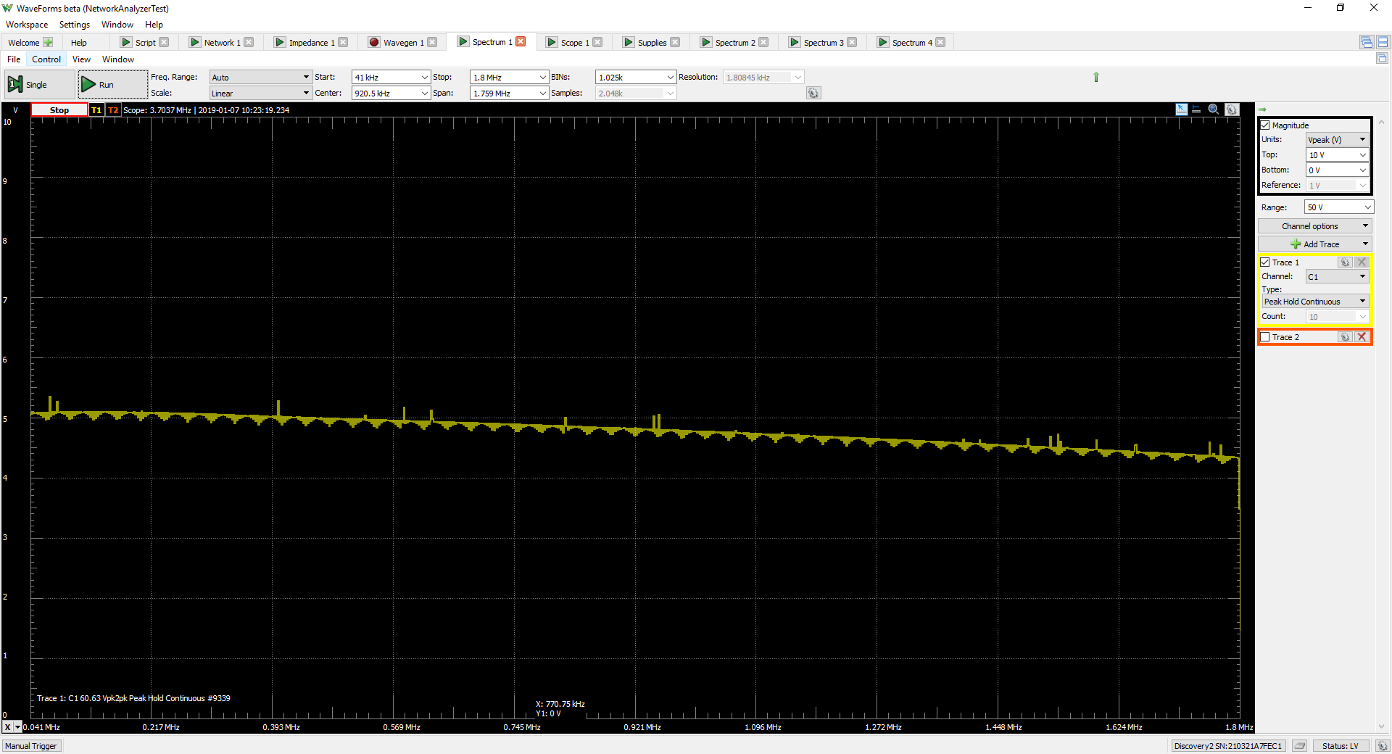
Measurements/Spooky2/02_WithBatteryReport/09_ProfessionalSignalGenerator-BFBRange5V_10V.png
