andrasfuchs/BioBalanceDetector/Measurements/Spooky2/02_WithBatteryReport/10_BatteryConnectedPoweredOn-G1BFB_GroundClipConnectedToCase_10V.png

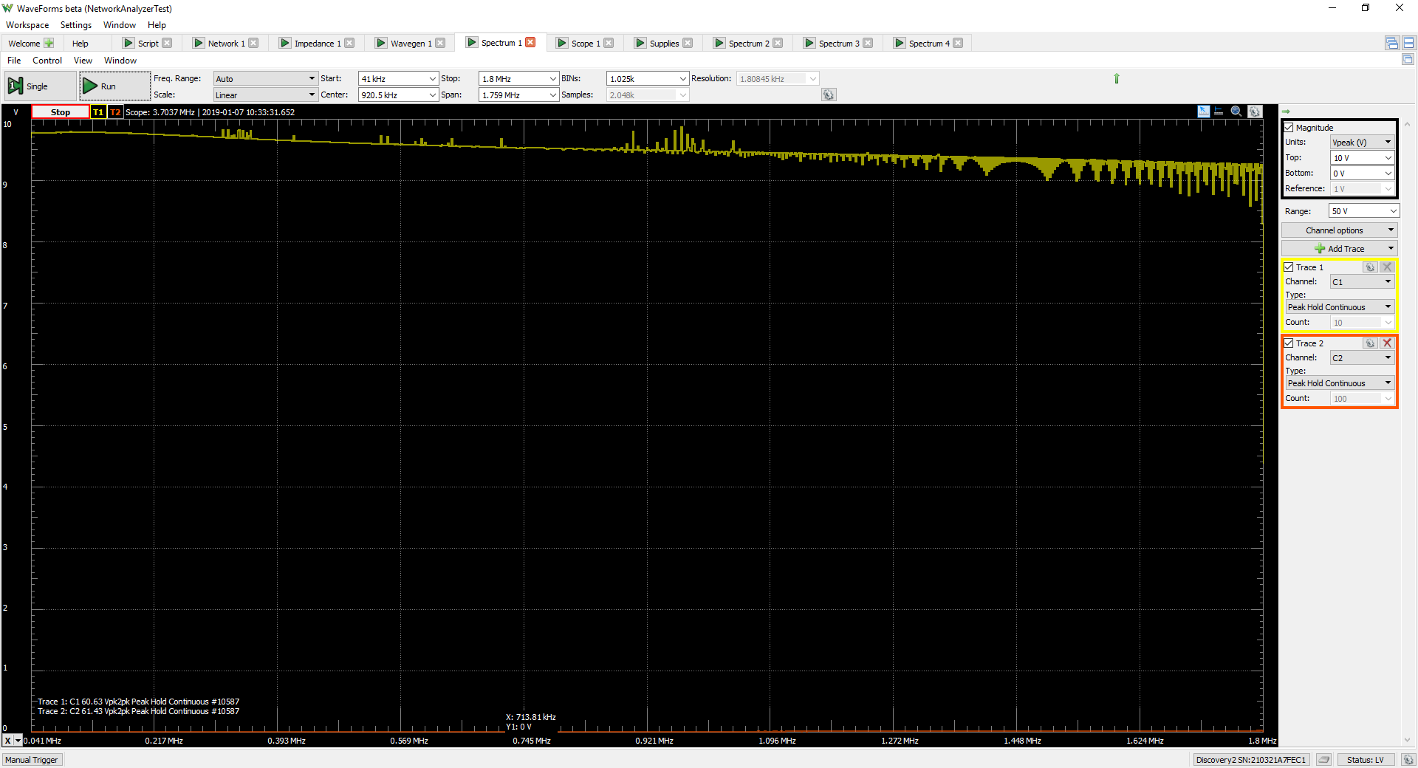
Measurements/Spooky2/02_WithBatteryReport/10_BatteryConnectedPoweredOn-G1BFB_GroundClipConnectedToCase_10V.png
