andrasfuchs/BioBalanceDetector/Measurements/Spooky2/02_WithBatteryReport/12_PowerAdapterConnectedPoweredOn-G1BFB_GroundClipConnectedToCase_10VZoomed.png

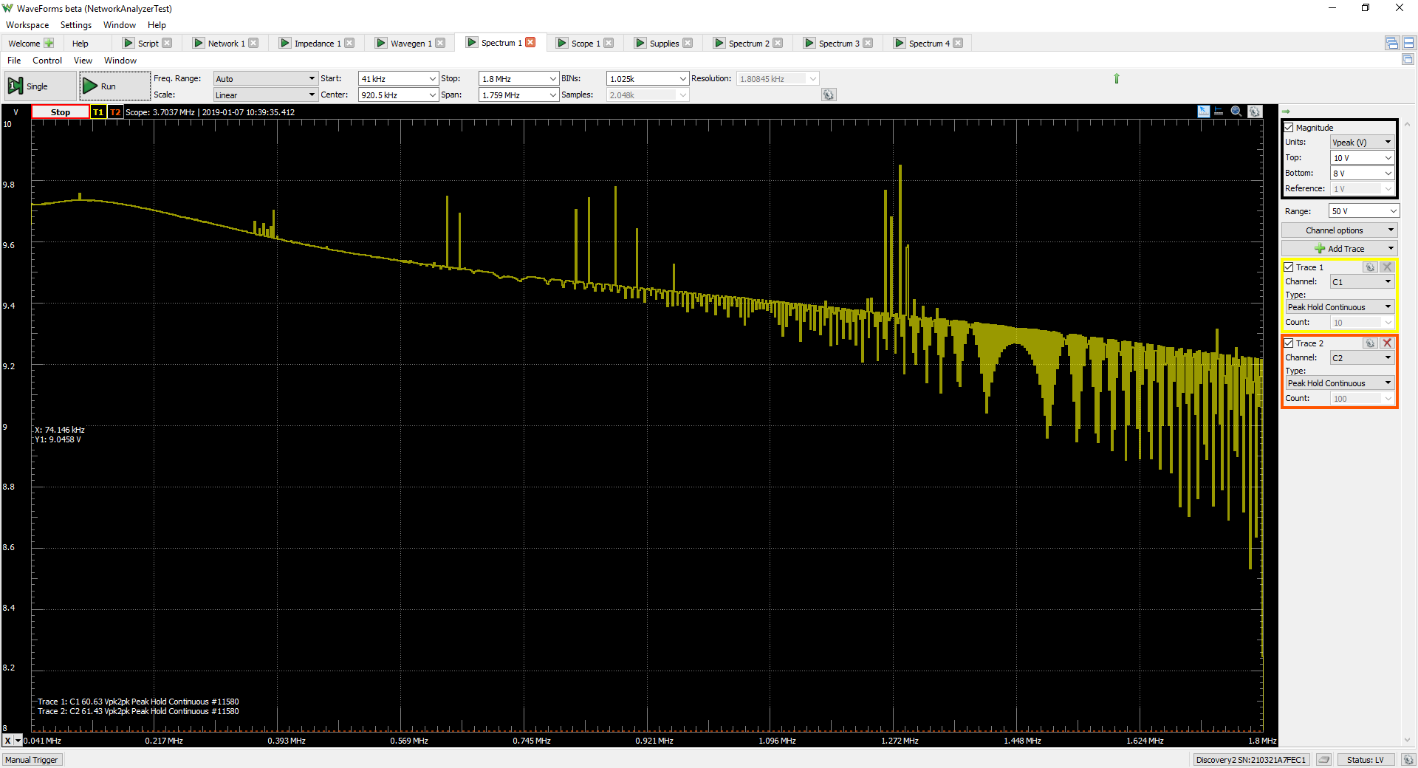
Measurements/Spooky2/02_WithBatteryReport/12_PowerAdapterConnectedPoweredOn-G1BFB_GroundClipConnectedToCase_10VZoomed.png
