andrasfuchs/BioBalanceDetector/Photos/Proto01/USBASP/IMG_20151212_162907.jpg

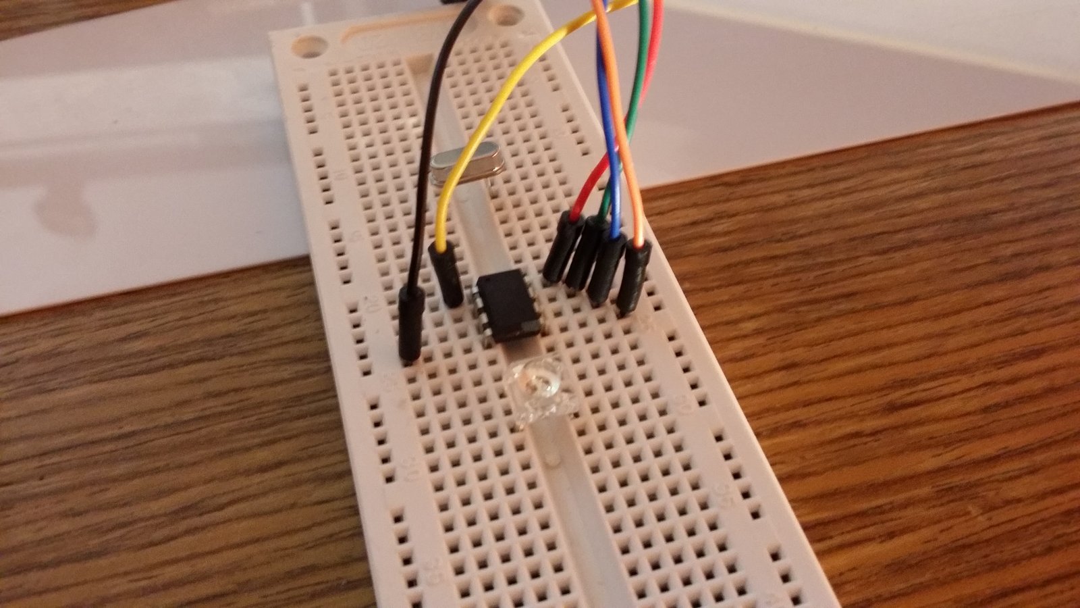
Photos/Proto01/USBASP/IMG_20151212_162907.jpg
