andrasfuchs/BioBalanceDetector/Photos/Proto01/USBASP/IMG_20151212_162941.jpg

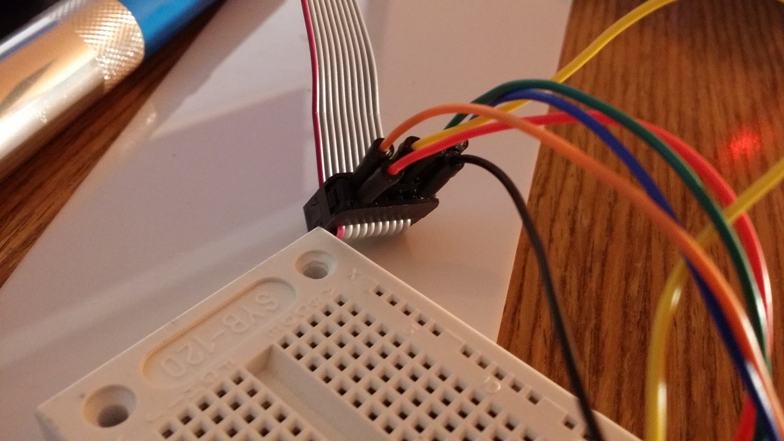
Photos/Proto01/USBASP/IMG_20151212_162941.jpg
