andrasfuchs/BioBalanceDetector/Photos/Proto01/USBASP/IMG_20151214_171512.jpg

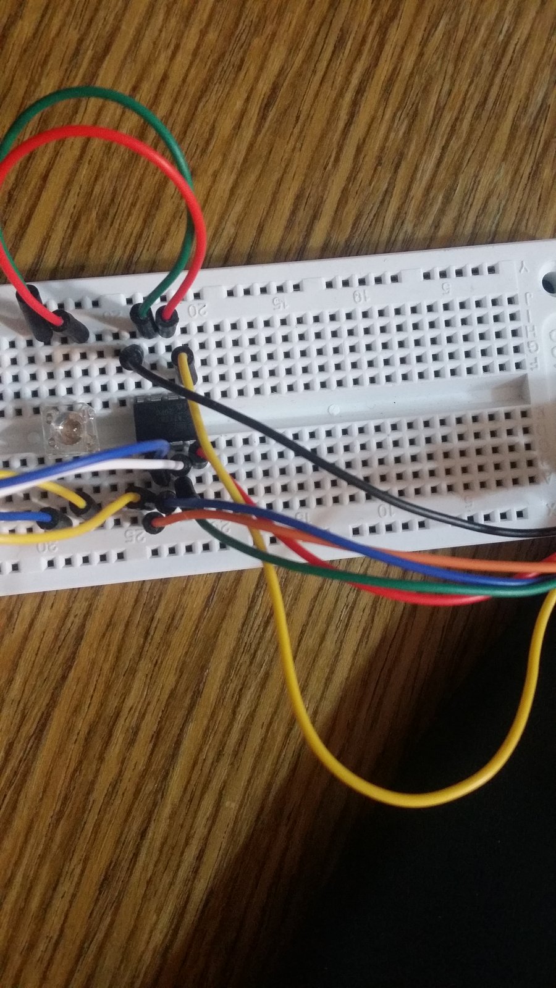
Photos/Proto01/USBASP/IMG_20151214_171512.jpg
