andrasfuchs/BioBalanceDetector/Photos/Proto01/USBASP/USBASP_ATtiny85.png

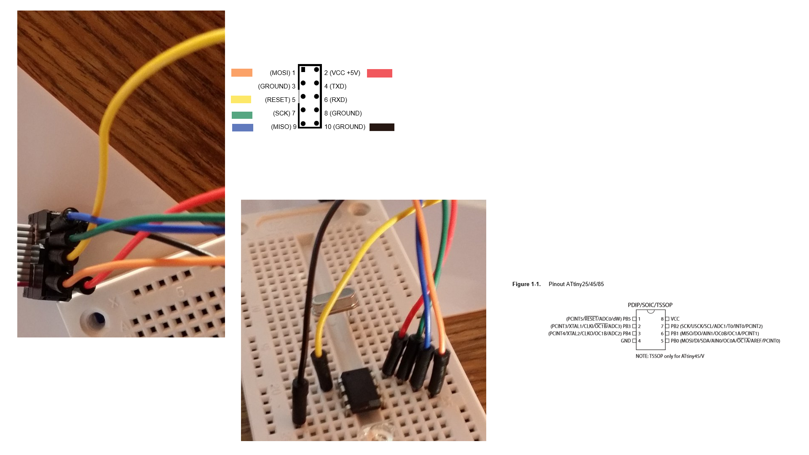
Photos/Proto01/USBASP/USBASP_ATtiny85.png
