andrasfuchs/BioBalanceDetector/Photos/Proto02/BreadBoard/IMG_20160310_215353.jpg

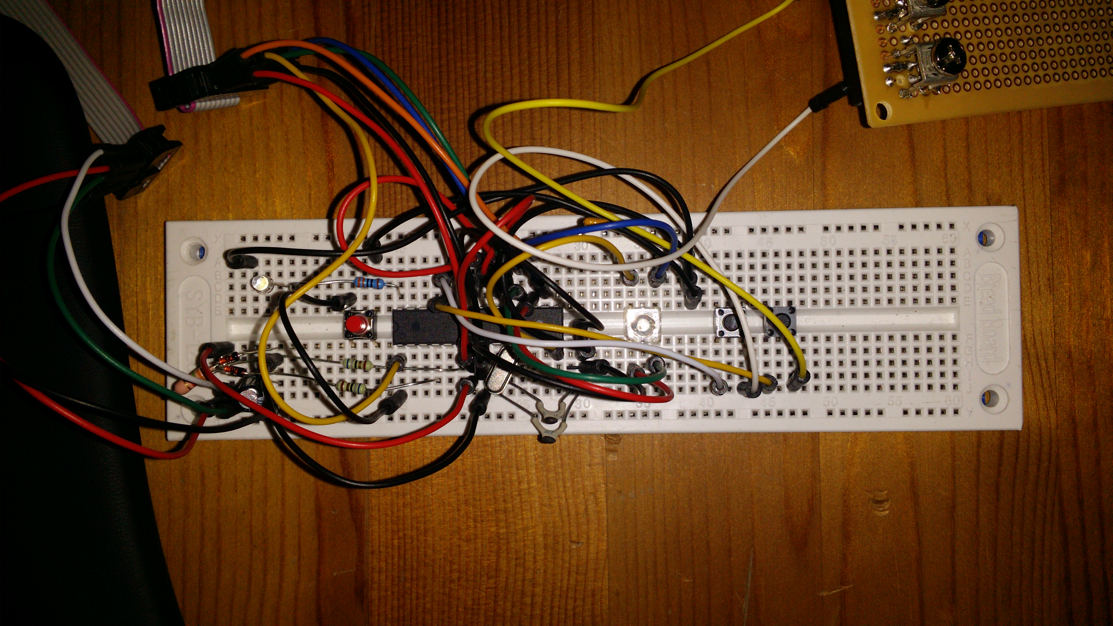
Photos/Proto02/BreadBoard/IMG_20160310_215353.jpg
