andrasfuchs/BioBalanceDetector/Photos/Proto02/BreadBoard/IMG_20160310_215741.jpg

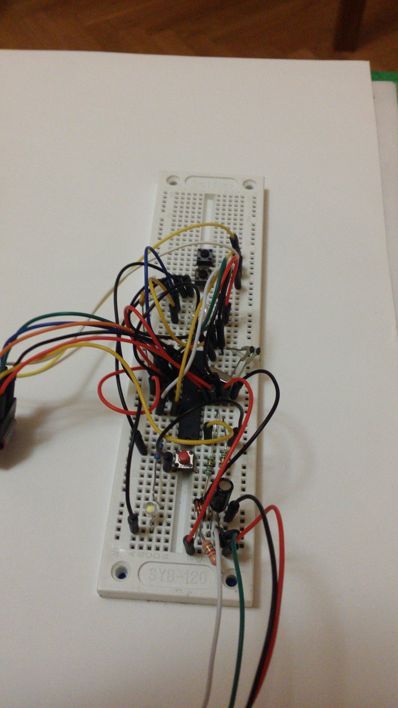
Photos/Proto02/BreadBoard/IMG_20160310_215741.jpg
