andrasfuchs/BioBalanceDetector/Photos/Proto02/BreadBoard/IMG_20160325_091432.jpg

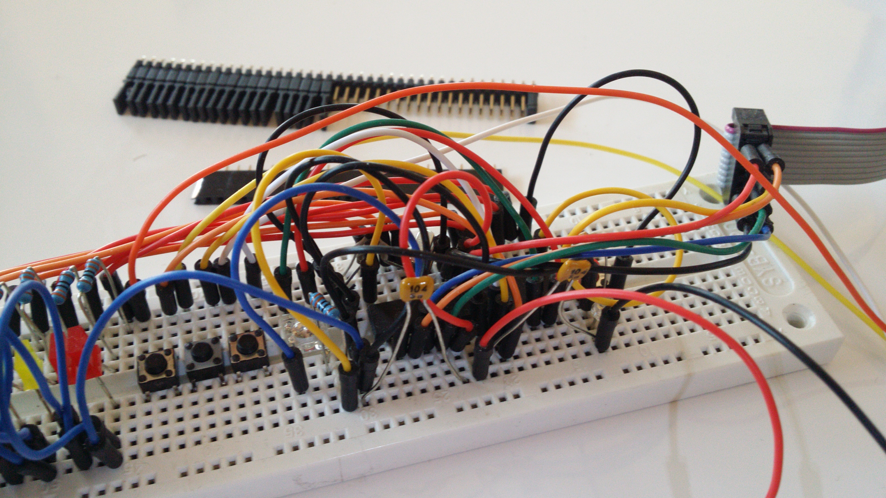
Photos/Proto02/BreadBoard/IMG_20160325_091432.jpg
