andrasfuchs/BioBalanceDetector/Photos/Proto02/BreadBoard/IMG_20160325_091438.jpg

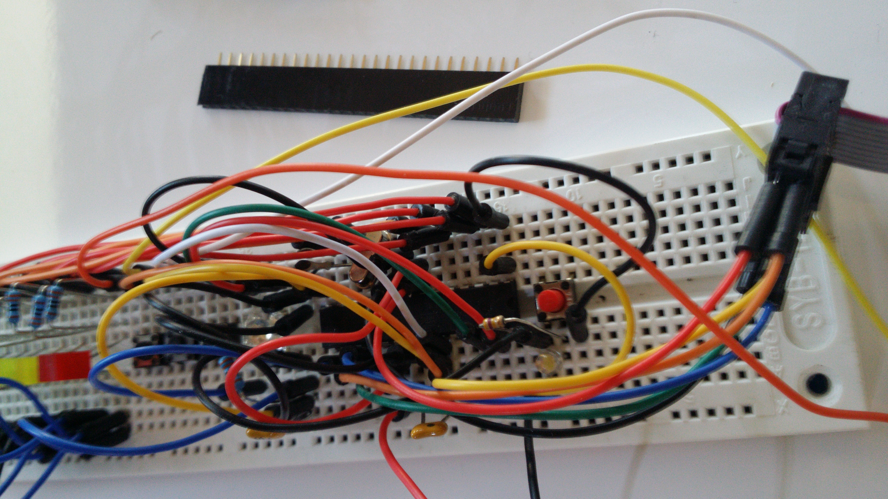
Photos/Proto02/BreadBoard/IMG_20160325_091438.jpg
