andrasfuchs/BioBalanceDetector/Photos/Proto02/BreadBoard/IMG_20160325_091447.jpg

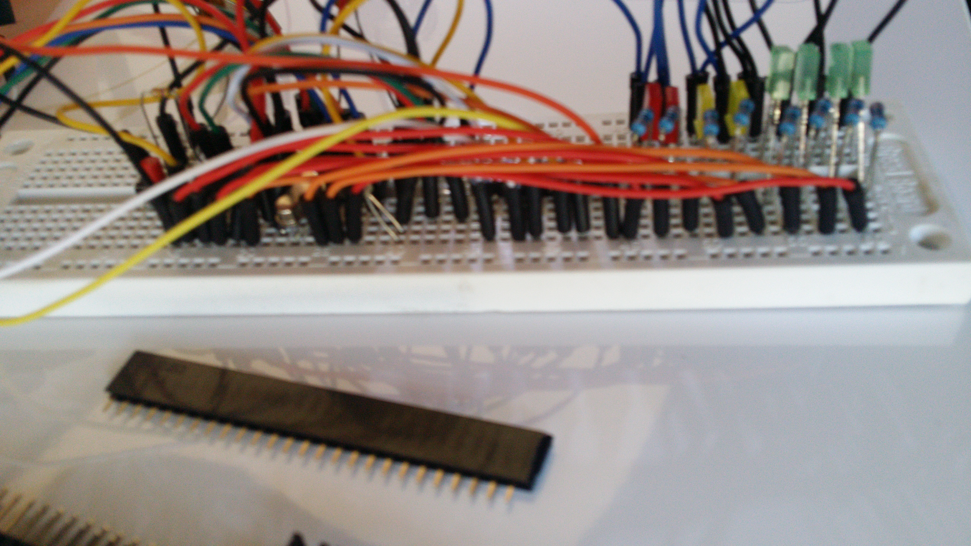
Photos/Proto02/BreadBoard/IMG_20160325_091447.jpg
