andrasfuchs/BioBalanceDetector/Photos/Proto02/BreadBoard/IMG_20160325_195515.jpg

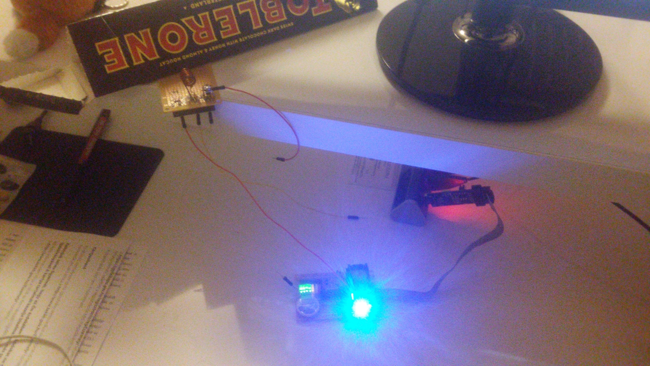
Photos/Proto02/BreadBoard/IMG_20160325_195515.jpg
