andrasfuchs/BioBalanceDetector/Photos/Proto02/IMG_20160329_140355.jpg

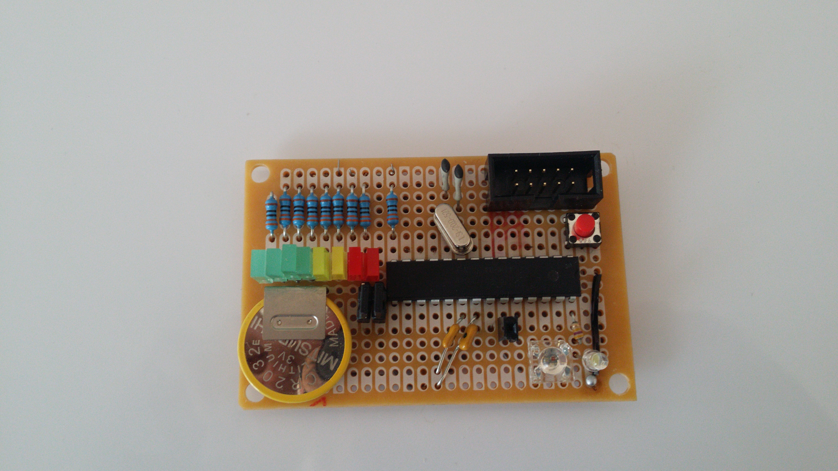
Photos/Proto02/IMG_20160329_140355.jpg
