andrasfuchs/BioBalanceDetector/Photos/Proto02/IMG_20160329_140425.jpg

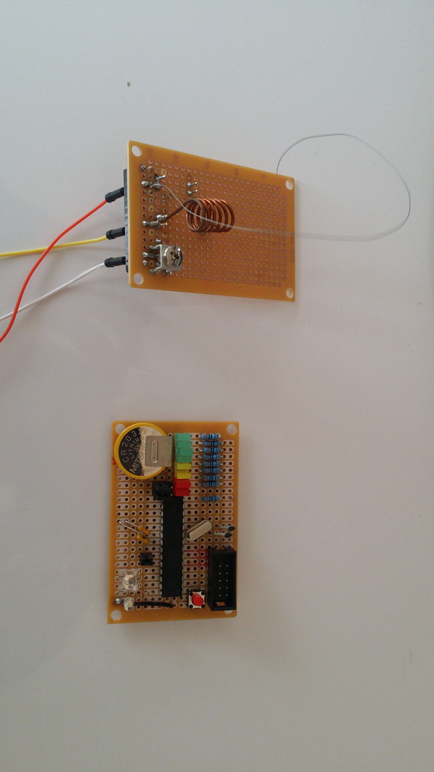
Photos/Proto02/IMG_20160329_140425.jpg
