andrasfuchs/BioBalanceDetector/Photos/Proto02/IMG_20170922_110225.jpg

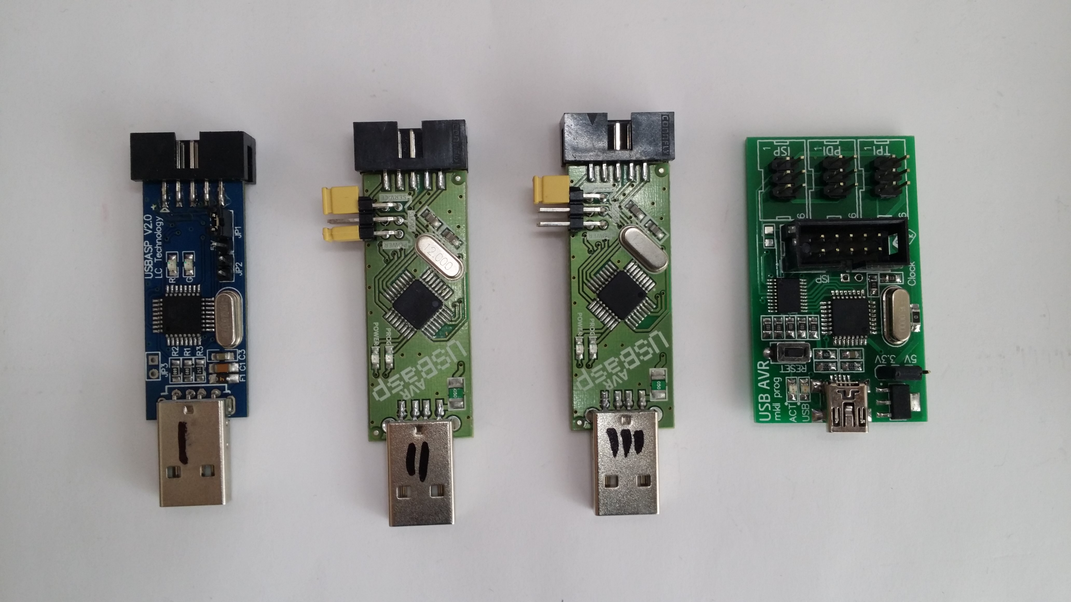
Photos/Proto02/IMG_20170922_110225.jpg
