andrasfuchs/BioBalanceDetector/Photos/Proto03/IMG_20160406_105313.jpg

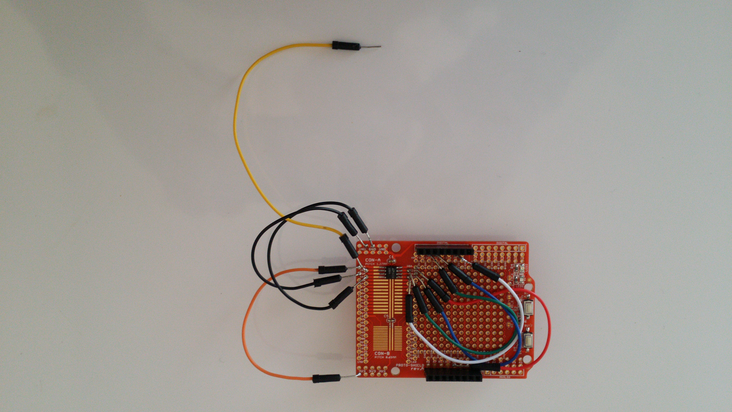
Photos/Proto03/IMG_20160406_105313.jpg
