andrasfuchs/BioBalanceDetector/Photos/Proto03/IMG_20160406_105322.jpg

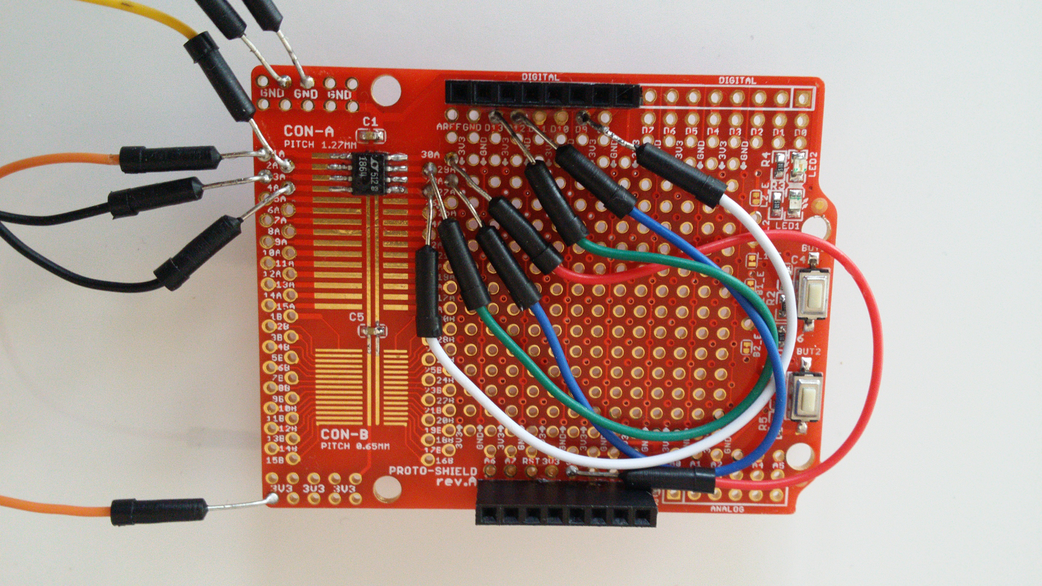
Photos/Proto03/IMG_20160406_105322.jpg
