andrasfuchs/BioBalanceDetector/Photos/Proto03/IMG_20160406_105342.jpg

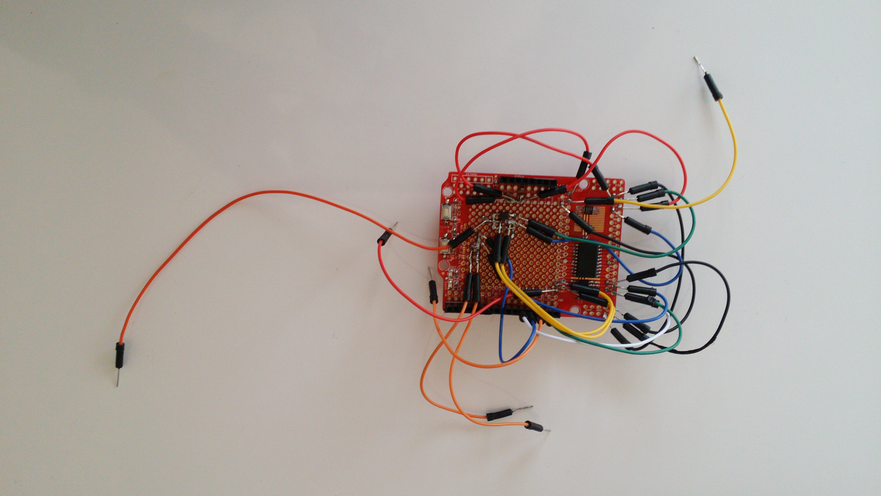
Photos/Proto03/IMG_20160406_105342.jpg
