andrasfuchs/BioBalanceDetector/Photos/Proto03/IMG_20160414_160012.jpg

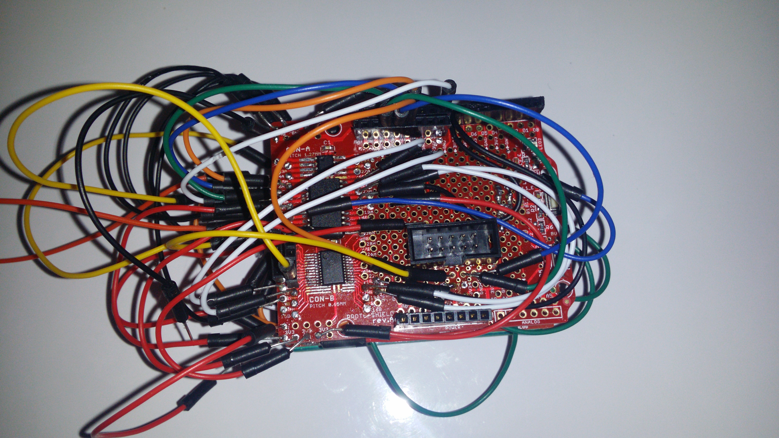
Photos/Proto03/IMG_20160414_160012.jpg
