andrasfuchs/BioBalanceDetector/Photos/Proto03/IMG_20170922_092604.jpg

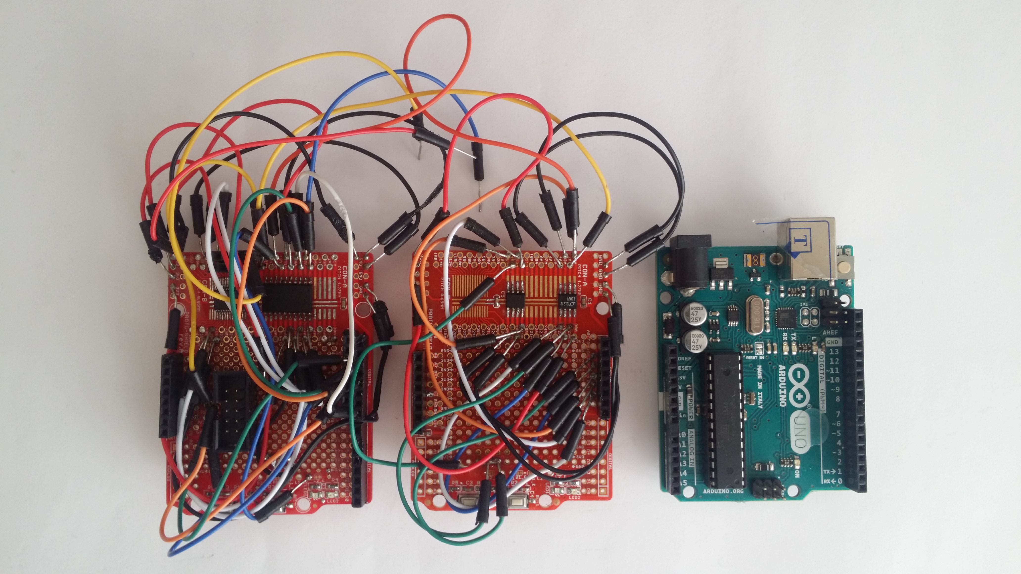
Photos/Proto03/IMG_20170922_092604.jpg
