andrasfuchs/BioBalanceDetector/Photos/Proto03/IMG_20170922_093355.jpg

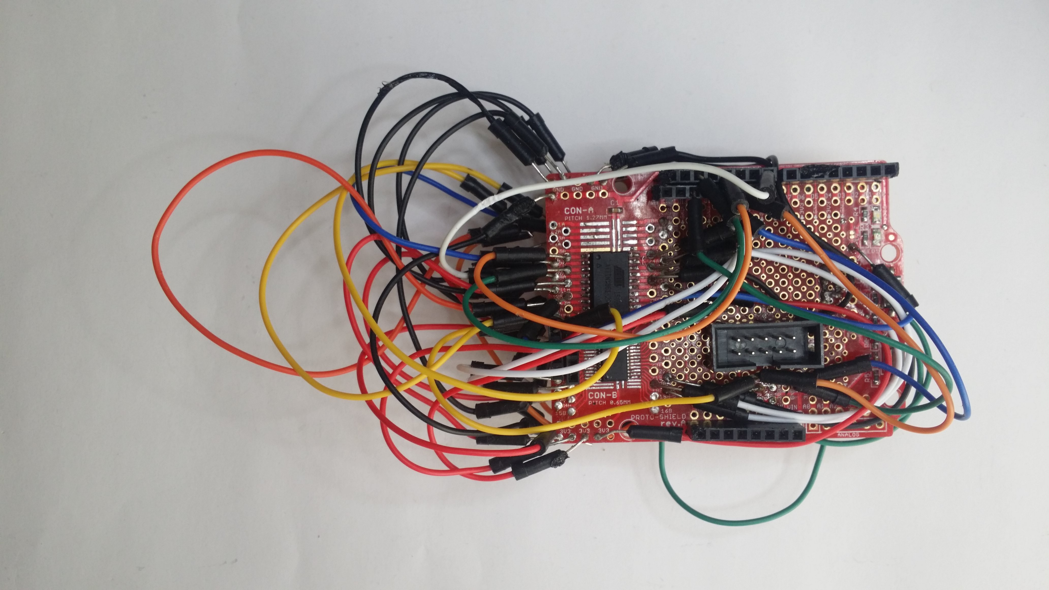
Photos/Proto03/IMG_20170922_093355.jpg
