andrasfuchs/BioBalanceDetector/Photos/Proto04/ArduinoMultiplexerServer_2016-07-13_08-02-05.png

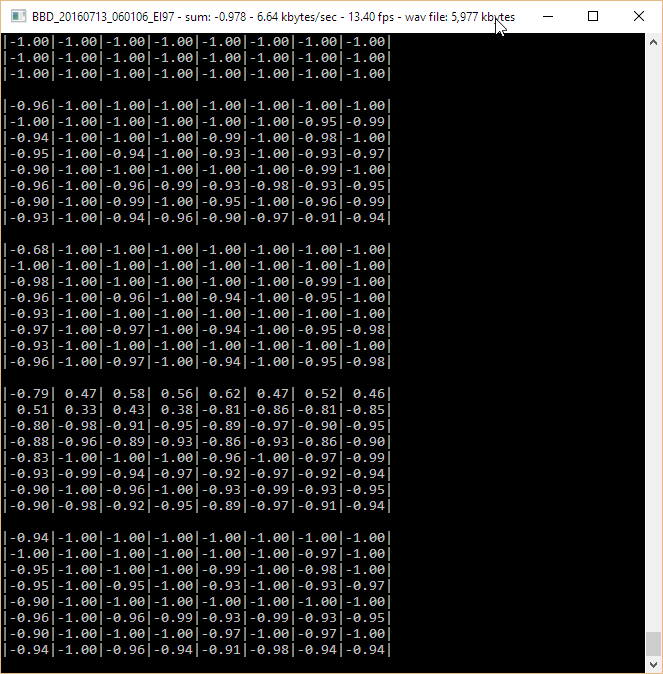
Photos/Proto04/ArduinoMultiplexerServer_2016-07-13_08-02-05.png
