andrasfuchs/BioBalanceDetector/Photos/Proto04/IMG_20160512_131815.jpg

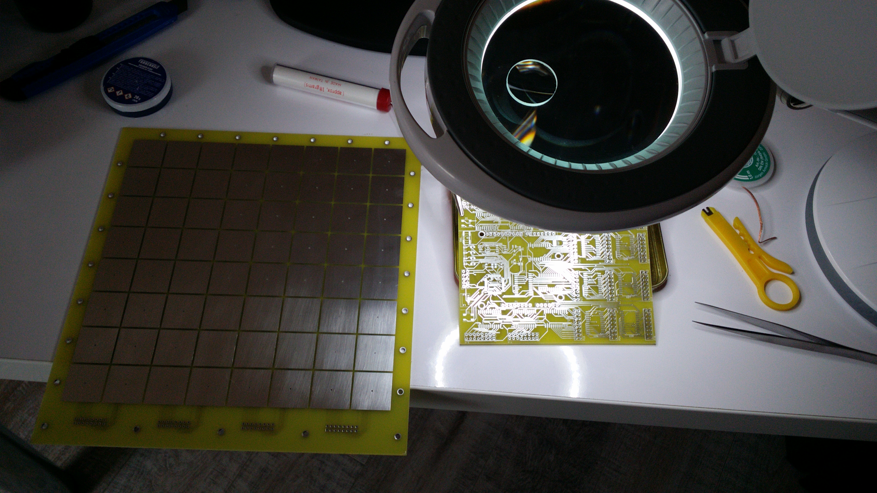
Photos/Proto04/IMG_20160512_131815.jpg
