andrasfuchs/BioBalanceDetector/Photos/Proto04/IMG_20160512_132254.jpg

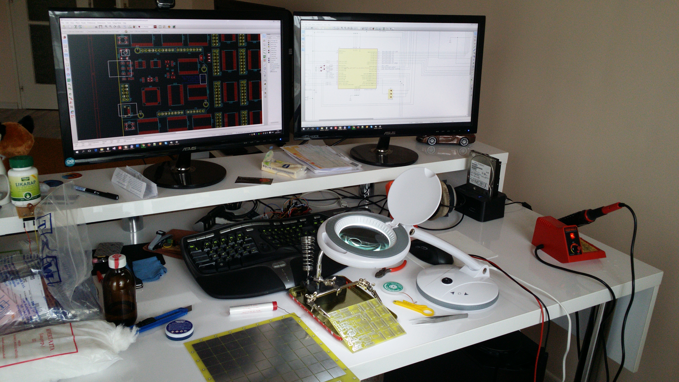
Photos/Proto04/IMG_20160512_132254.jpg
