andrasfuchs/BioBalanceDetector/Photos/Proto04/IMG_20160512_132303.jpg

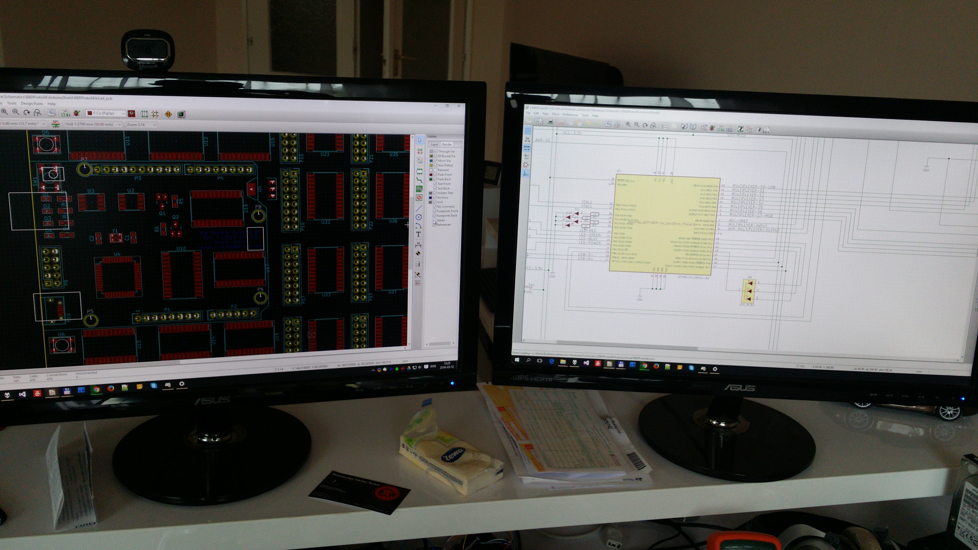
Photos/Proto04/IMG_20160512_132303.jpg
