andrasfuchs/BioBalanceDetector/Photos/Proto04/IMG_20160526_174205.jpg

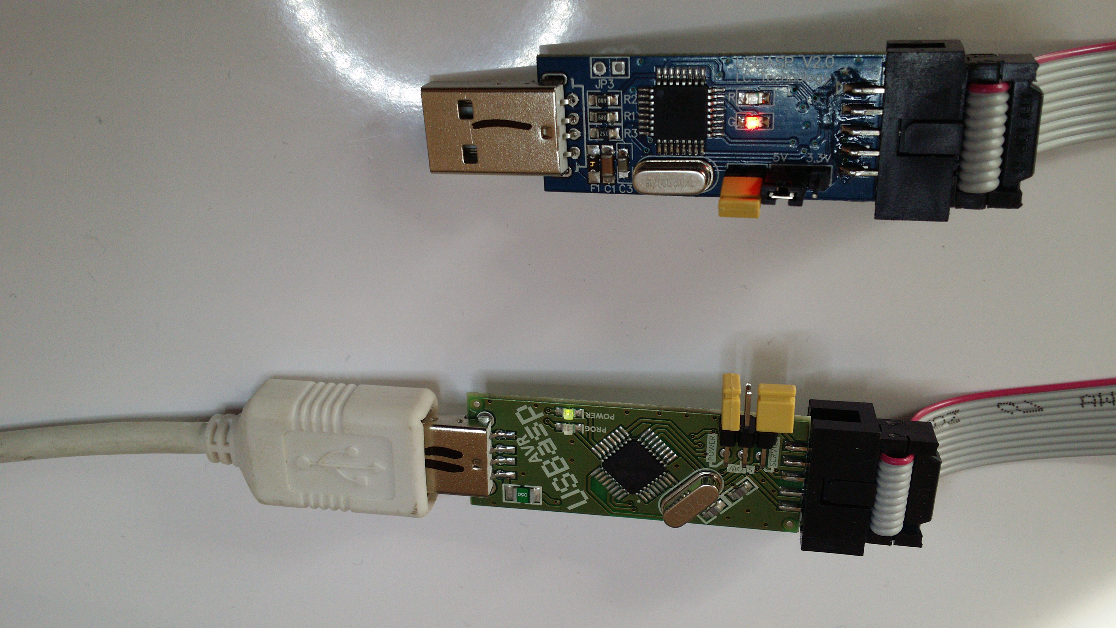
Photos/Proto04/IMG_20160526_174205.jpg
