andrasfuchs/BioBalanceDetector/Photos/Proto04/IMG_20160526_174216.jpg

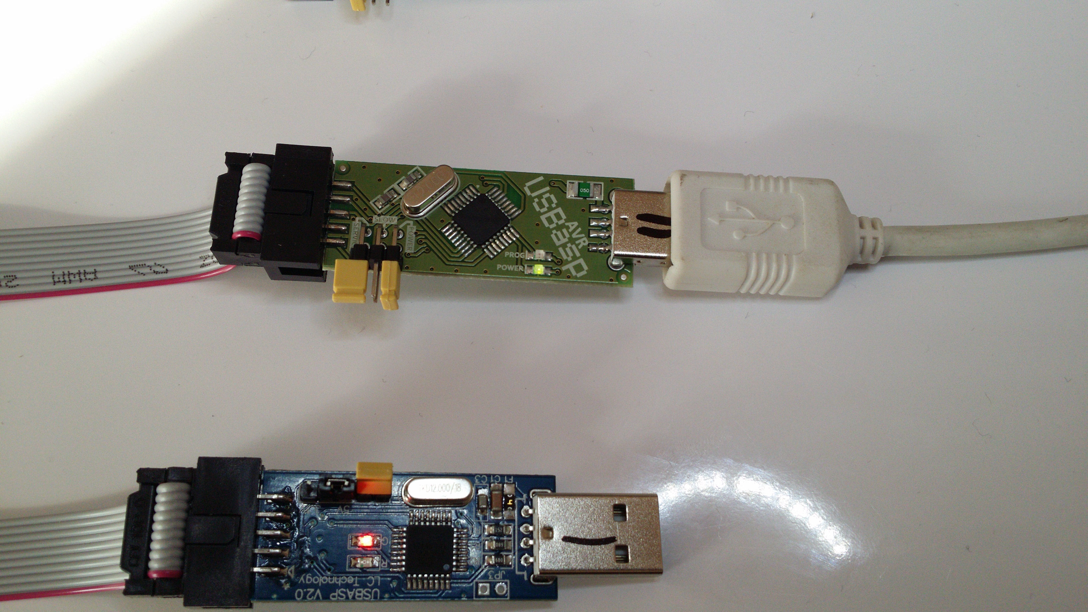
Photos/Proto04/IMG_20160526_174216.jpg
