andrasfuchs/BioBalanceDetector/Photos/Proto04/IMG_20160526_174216_cr.jpg

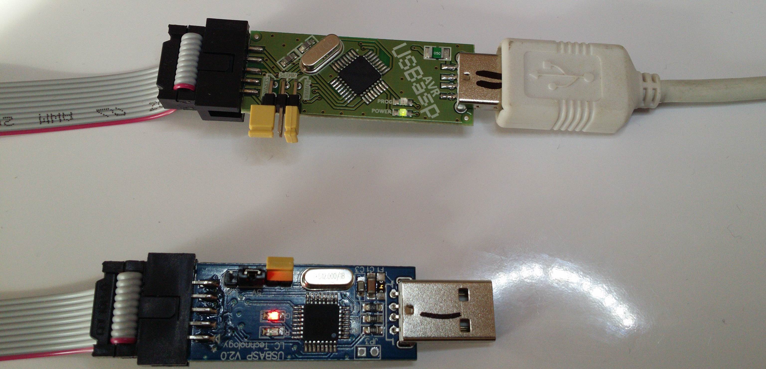
Photos/Proto04/IMG_20160526_174216_cr.jpg
