andrasfuchs/BioBalanceDetector/Photos/Proto04/IMG_20160530_192438.jpg

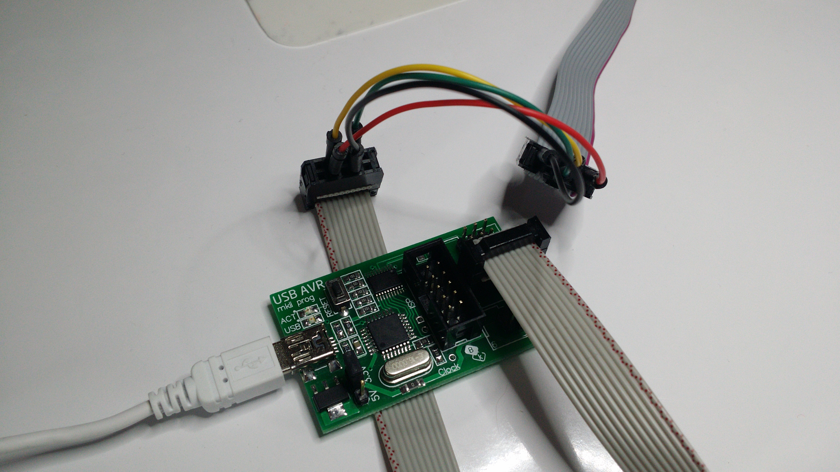
Photos/Proto04/IMG_20160530_192438.jpg
