andrasfuchs/BioBalanceDetector/Photos/Proto04/IMG_20160530_193244.jpg

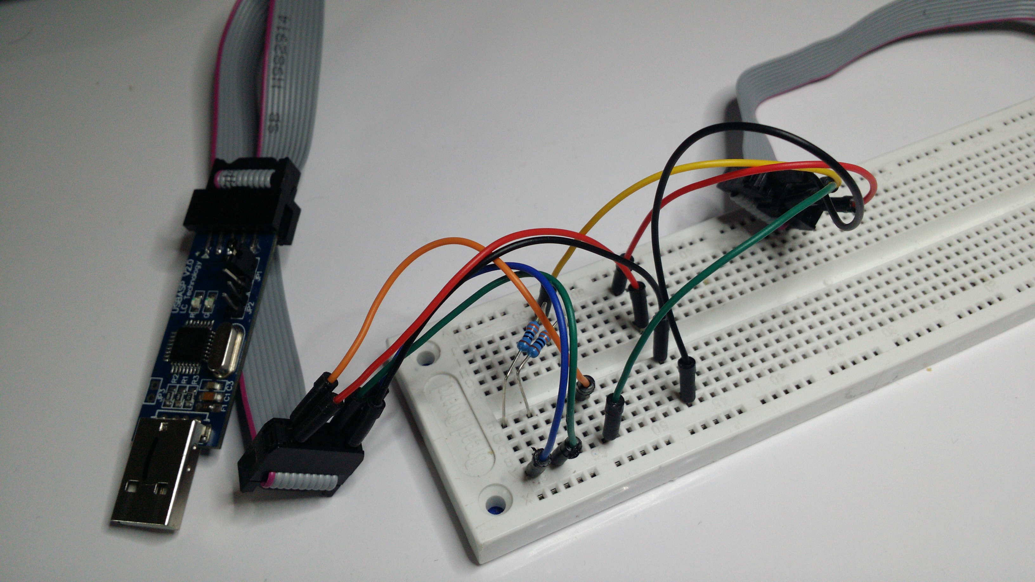
Photos/Proto04/IMG_20160530_193244.jpg
