andrasfuchs/BioBalanceDetector/Photos/Proto04/IMG_20160531_090039.jpg

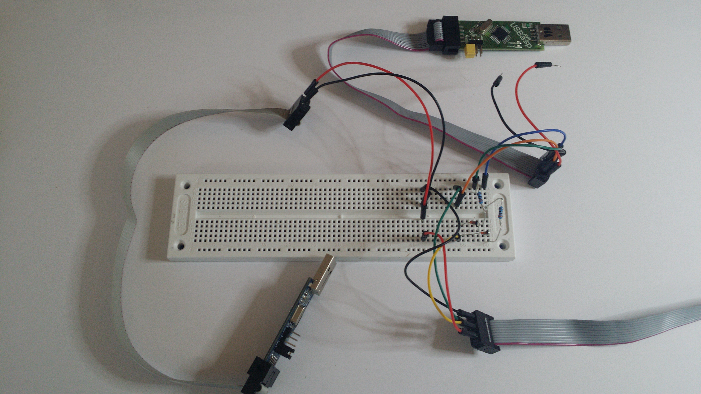
Photos/Proto04/IMG_20160531_090039.jpg
