andrasfuchs/BioBalanceDetector/Photos/Proto04/IMG_20160615_100055.jpg

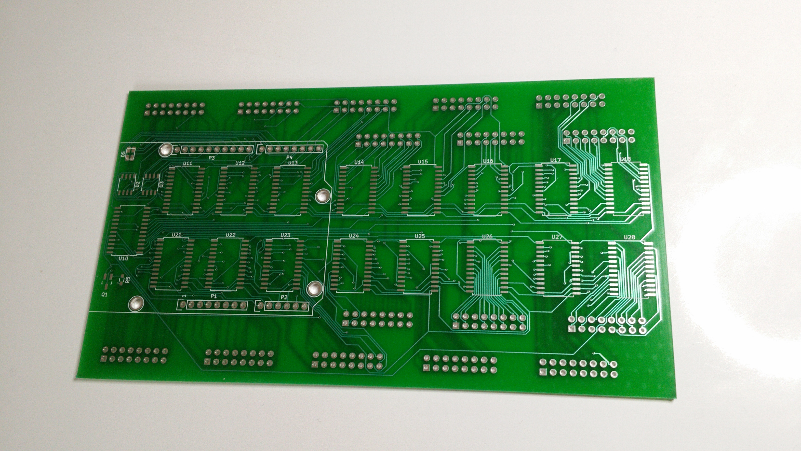
Photos/Proto04/IMG_20160615_100055.jpg
