andrasfuchs/BioBalanceDetector/Photos/Proto04/IMG_20160630_091957.jpg

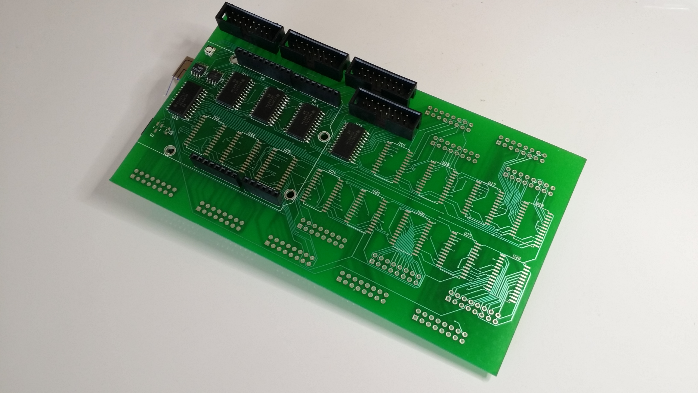
Photos/Proto04/IMG_20160630_091957.jpg
