andrasfuchs/BioBalanceDetector/Photos/Proto04/IMG_20160630_092011.jpg

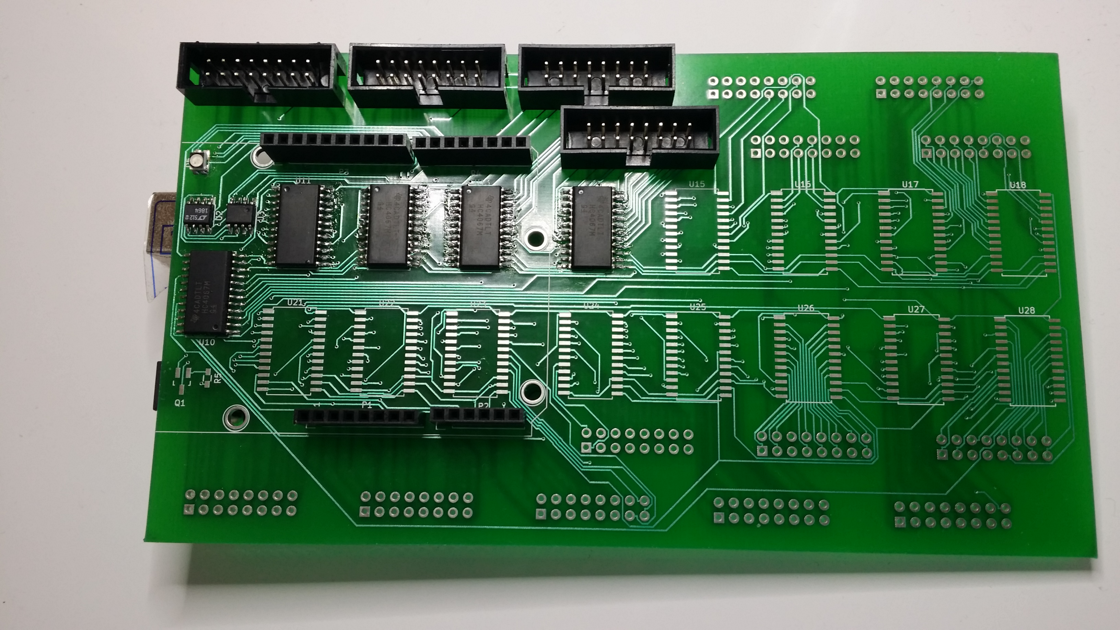
Photos/Proto04/IMG_20160630_092011.jpg
