andrasfuchs/BioBalanceDetector/Photos/Proto04/IMG_20160630_092029.jpg

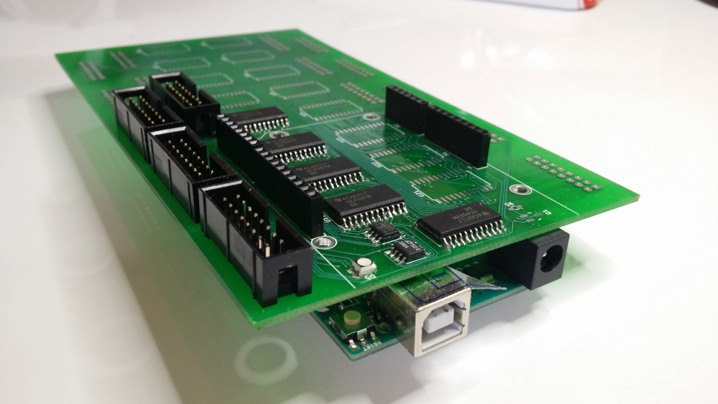
Photos/Proto04/IMG_20160630_092029.jpg
