andrasfuchs/BioBalanceDetector/Photos/Proto04/IMG_20160630_092126.jpg

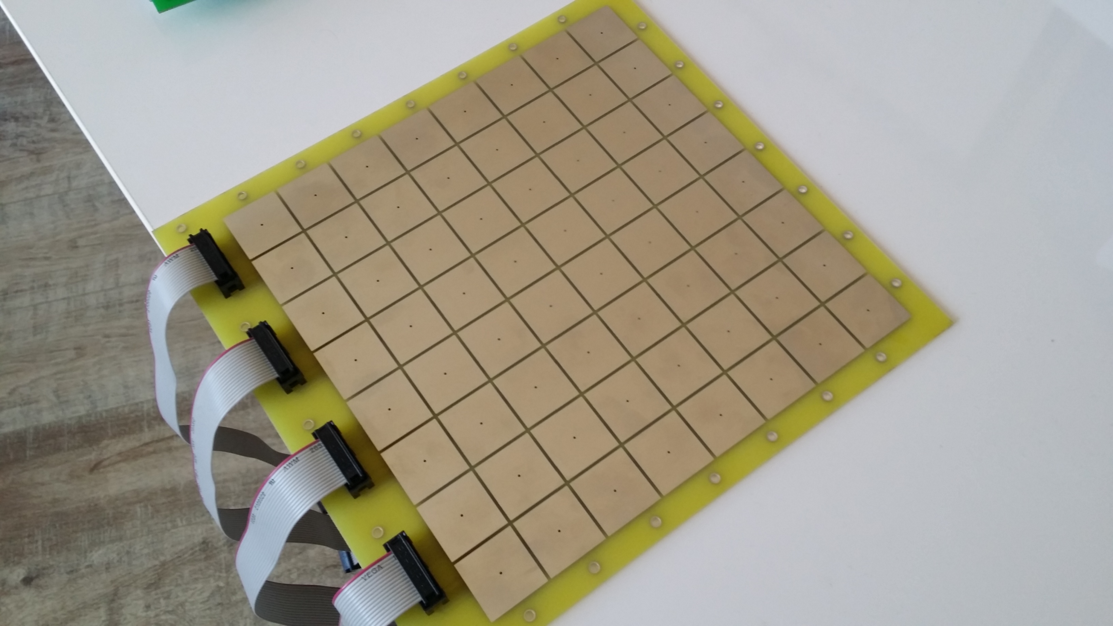
Photos/Proto04/IMG_20160630_092126.jpg
