andrasfuchs/BioBalanceDetector/Photos/Proto04/IMG_20160630_092212.jpg

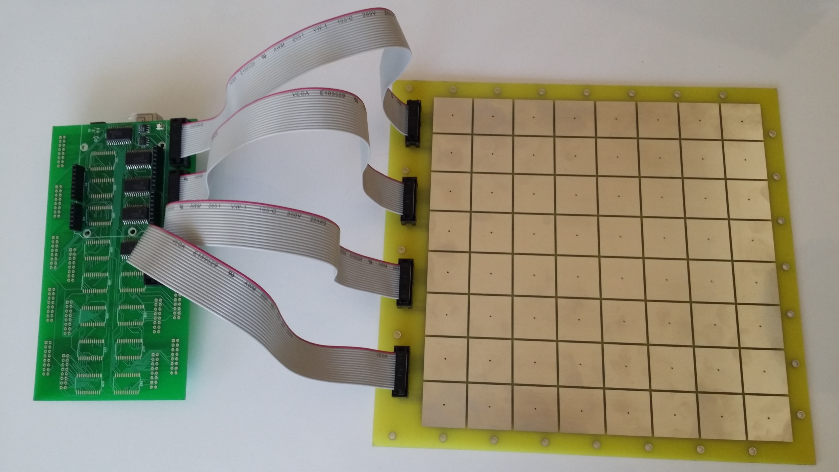
Photos/Proto04/IMG_20160630_092212.jpg
