andrasfuchs/BioBalanceDetector/Photos/Proto04/kicad_2016-07-13_08-10-16_DAC_ADC.png

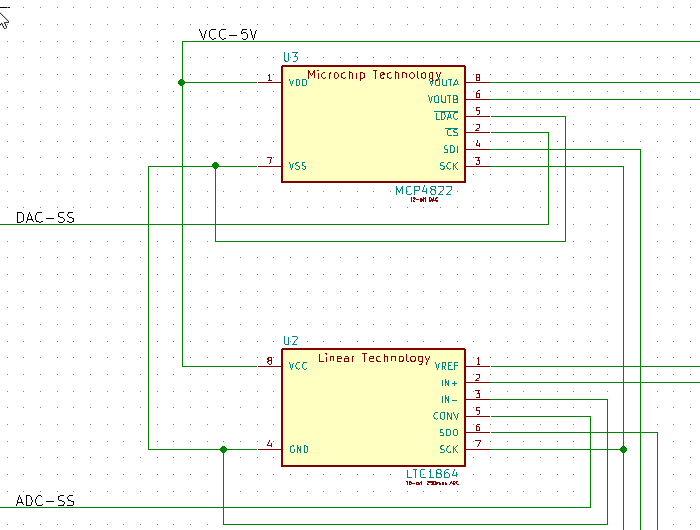
Photos/Proto04/kicad_2016-07-13_08-10-16_DAC_ADC.png
