andrasfuchs/BioBalanceDetector/Photos/Proto04/kicad_2016-07-13_08-11-18_Multiplexer.png

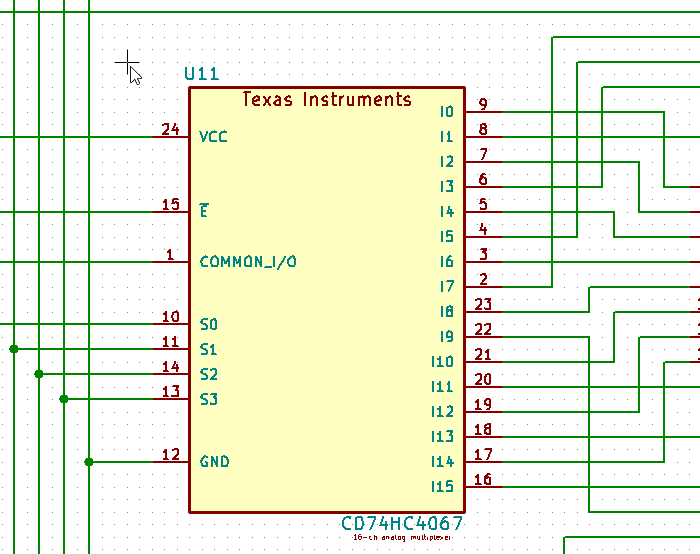
Photos/Proto04/kicad_2016-07-13_08-11-18_Multiplexer.png
