andrasfuchs/BioBalanceDetector/Photos/Proto04/kicad_2016-07-13_08-12-07_PCB.png

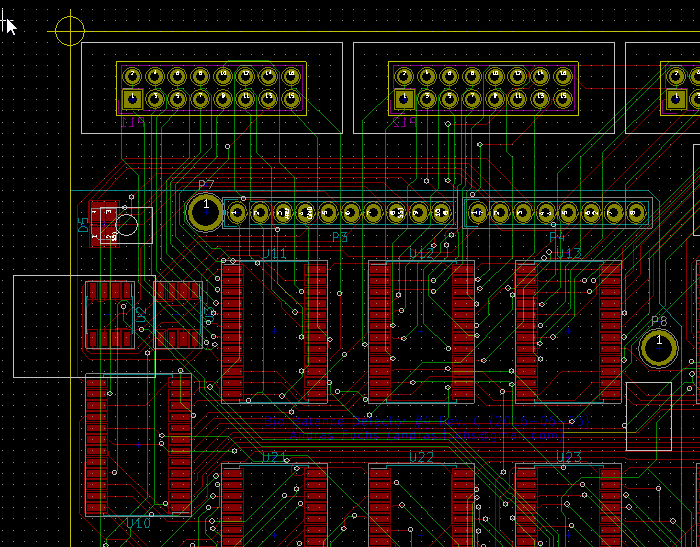
Photos/Proto04/kicad_2016-07-13_08-12-07_PCB.png
