andrasfuchs/BioBalanceDetector/Photos/Proto05/BBD_2D_Sensor_List.gif

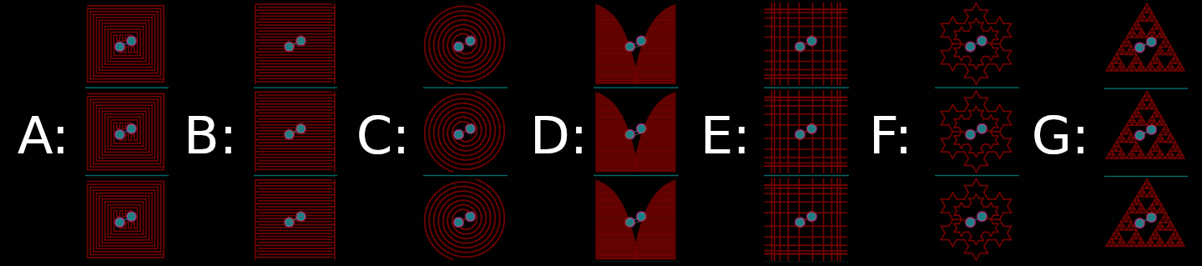
Photos/Proto05/BBD_2D_Sensor_List.gif
