andrasfuchs/BioBalanceDetector/Photos/Proto05/BBD_Flat_Panel_Detector_rev_A_PCB_v1.gif

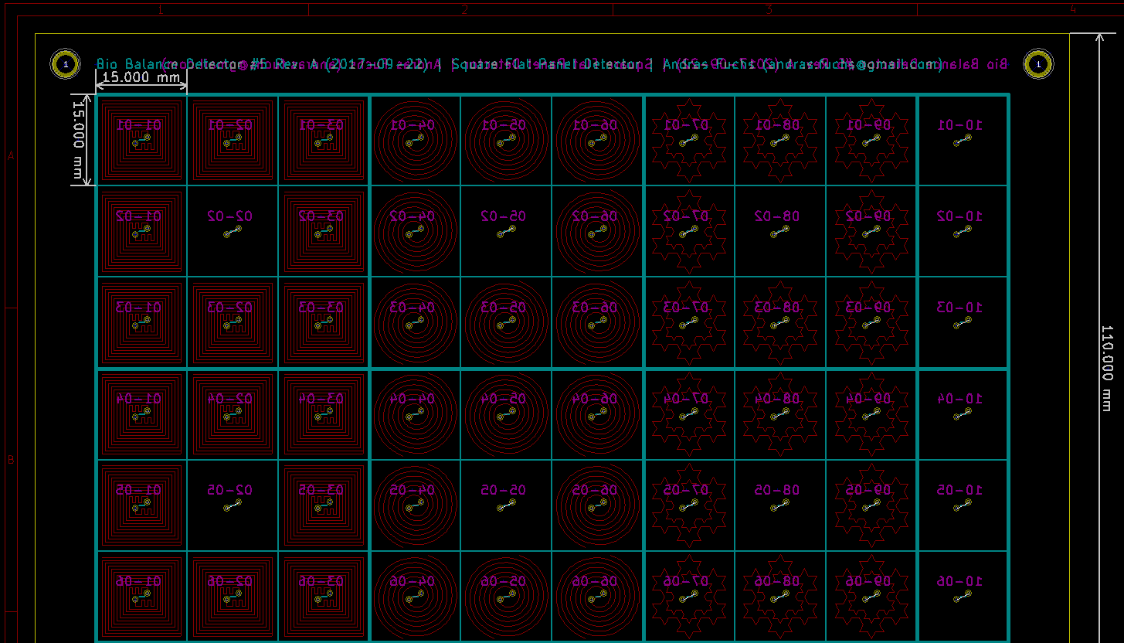
Photos/Proto05/BBD_Flat_Panel_Detector_rev_A_PCB_v1.gif
