andrasfuchs/BioBalanceDetector/Photos/Proto05/BBD_Flat_Panel_Detector_rev_A_PCB_v2.gif

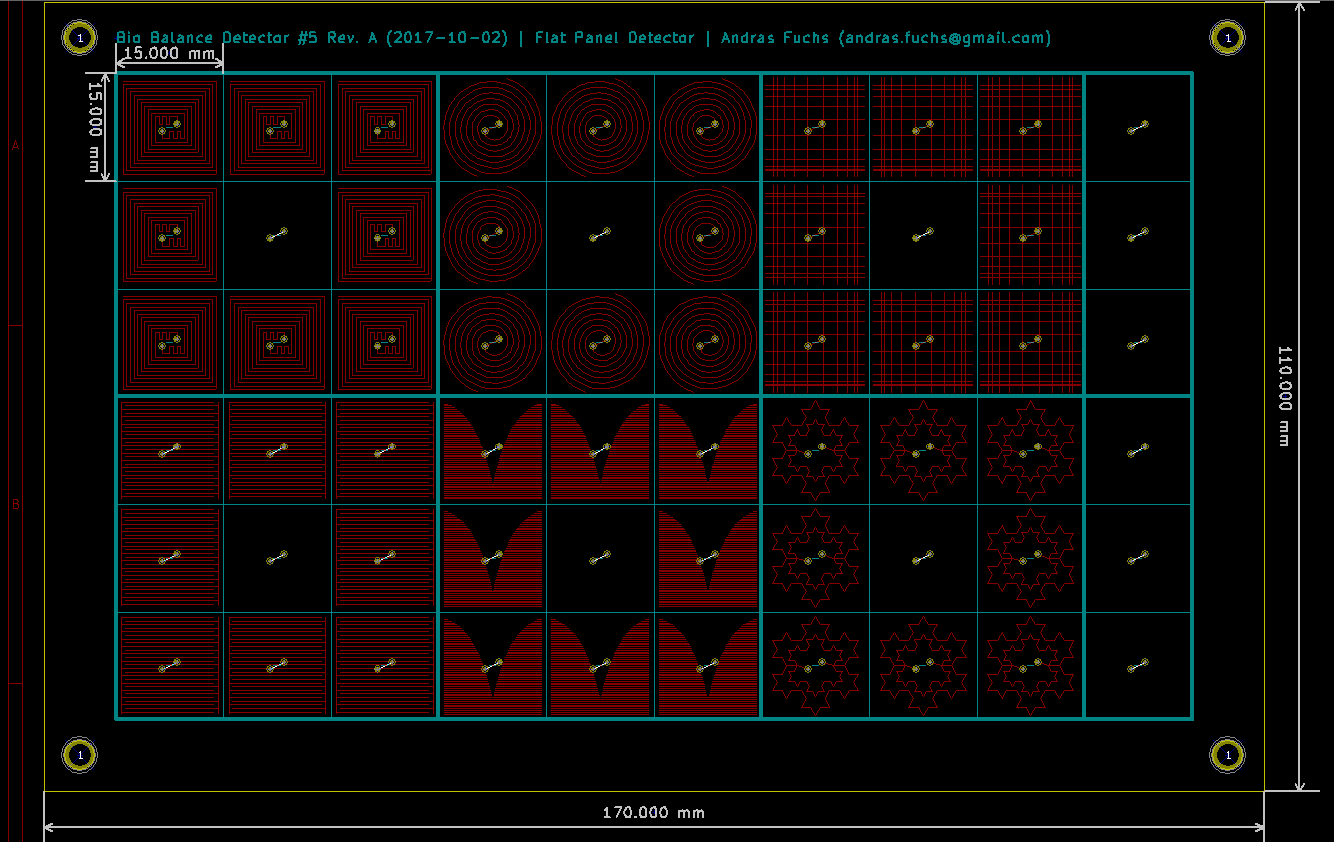
Photos/Proto05/BBD_Flat_Panel_Detector_rev_A_PCB_v2.gif
