andrasfuchs/BioBalanceDetector/Photos/Proto05/BBD_Interface_DominantMatrix-size_restricted.gif

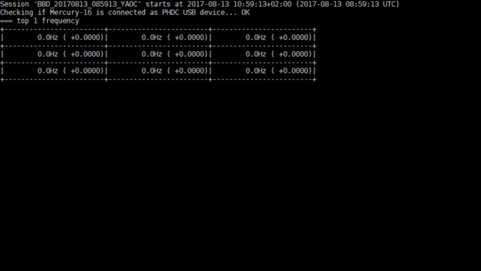
Photos/Proto05/BBD_Interface_DominantMatrix-size_restricted.gif
