andrasfuchs/BioBalanceDetector/Photos/Proto05/BBD_Interface_FFT-size_restricted.gif

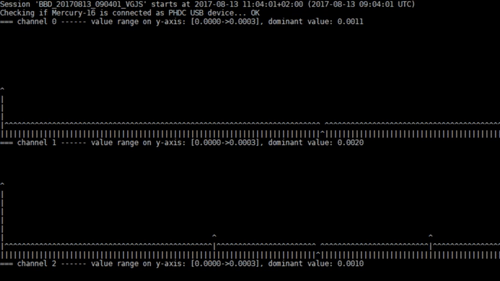
Photos/Proto05/BBD_Interface_FFT-size_restricted.gif
