andrasfuchs/BioBalanceDetector/Photos/Proto05/BBD_Interface_Waveform-size_restricted.gif

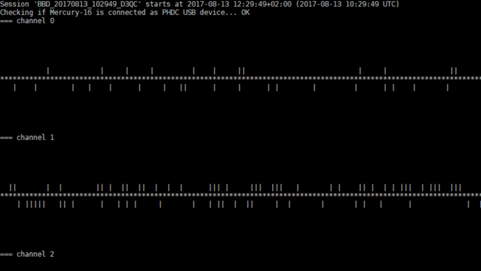
Photos/Proto05/BBD_Interface_Waveform-size_restricted.gif
