andrasfuchs/BioBalanceDetector/Photos/Proto05/BBD_Interface_Waveform.gif

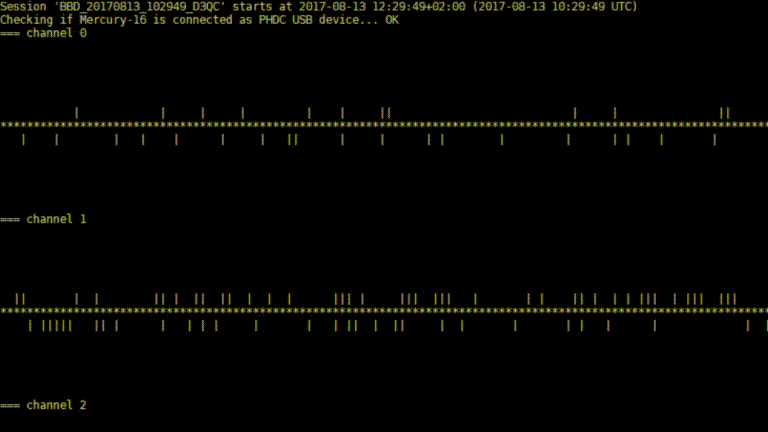
Photos/Proto05/BBD_Interface_Waveform.gif
