andrasfuchs/BioBalanceDetector/Photos/Proto05/BBD_Mercury-16_organizer_master_mode-size_restricted.gif

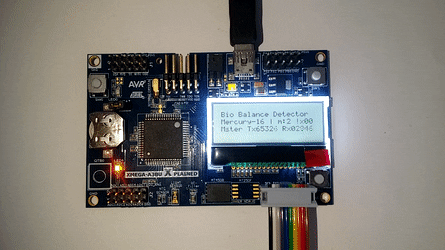
Photos/Proto05/BBD_Mercury-16_organizer_master_mode-size_restricted.gif
