andrasfuchs/BioBalanceDetector/Photos/Proto05/BBD_ParaViewScreenshot_01.png

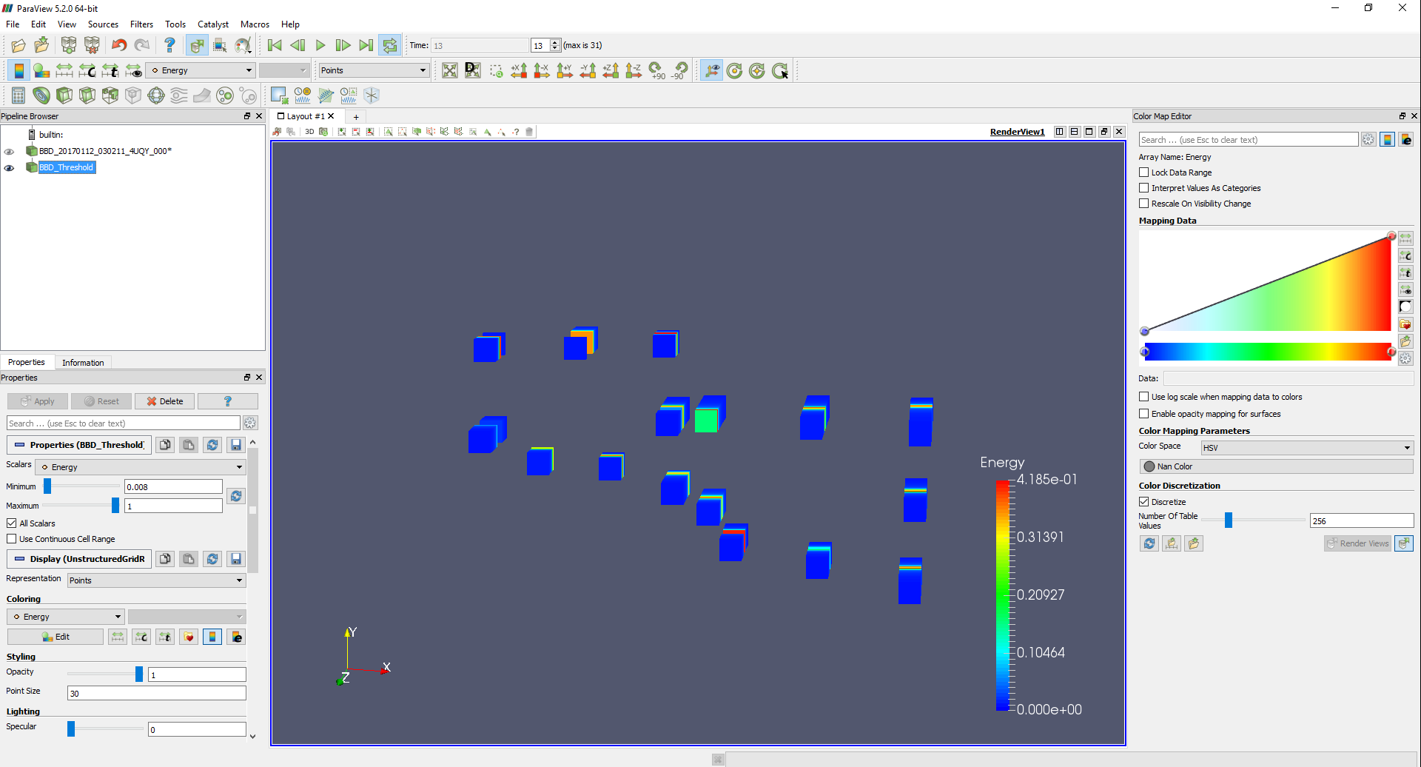
Photos/Proto05/BBD_ParaViewScreenshot_01.png
