andrasfuchs/BioBalanceDetector/Photos/Proto05/BBD_SciLabScreenshot.png

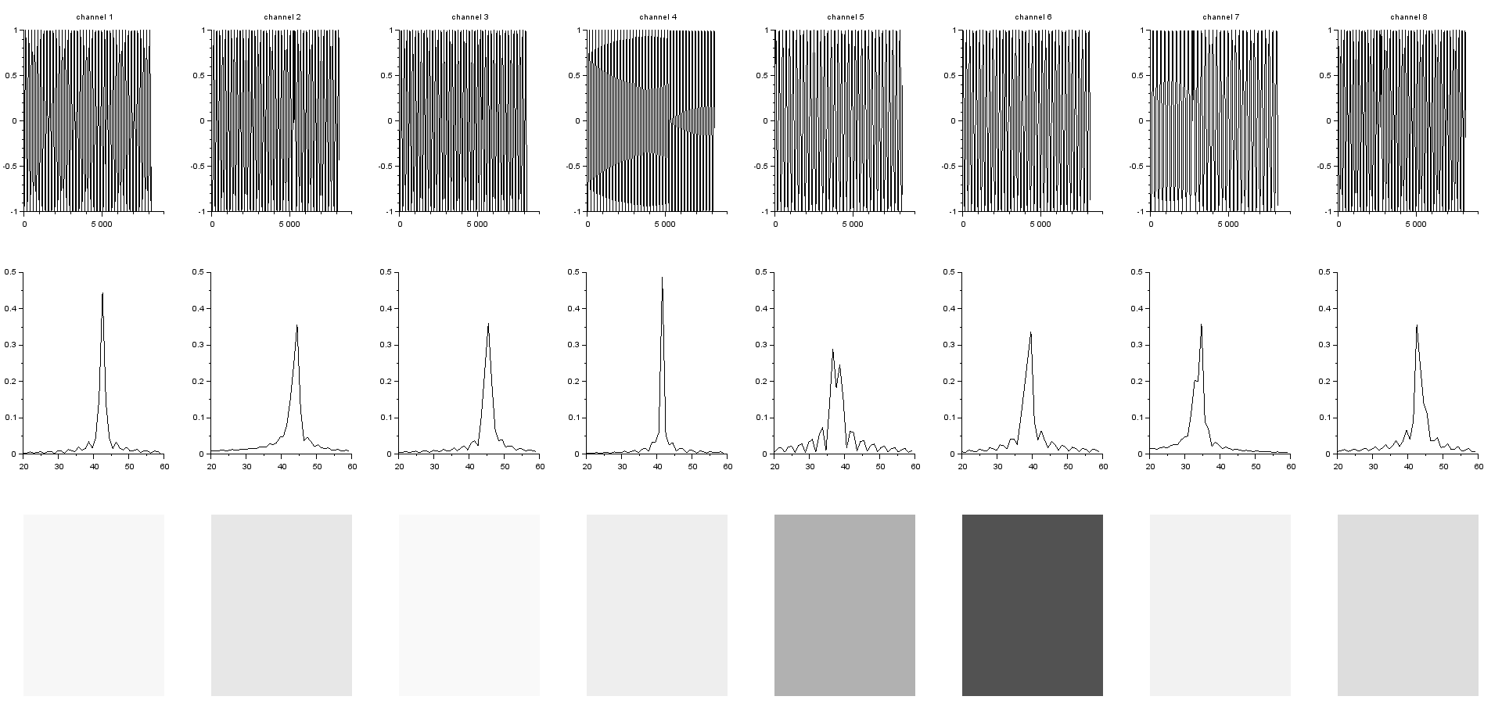
Photos/Proto05/BBD_SciLabScreenshot.png
