andrasfuchs/BioBalanceDetector/Photos/Proto05/IMG_20161221_140430_DigiKey_package.jpg

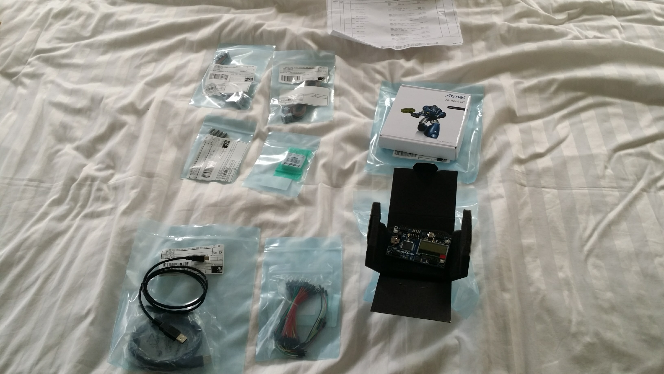
Photos/Proto05/IMG_20161221_140430_DigiKey_package.jpg
