andrasfuchs/BioBalanceDetector/Photos/Proto05/IMG_20161221_140506_Atmel-ICE.jpg

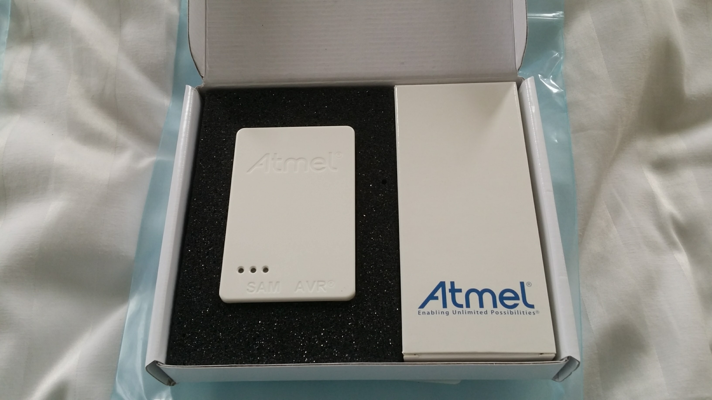
Photos/Proto05/IMG_20161221_140506_Atmel-ICE.jpg
