andrasfuchs/BioBalanceDetector/Photos/Proto05/IMG_20161221_140511_XMEGA-A3BU_Xplained.jpg

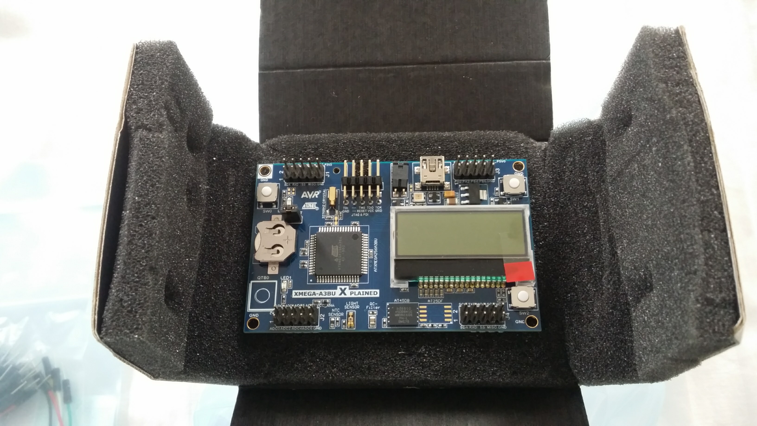
Photos/Proto05/IMG_20161221_140511_XMEGA-A3BU_Xplained.jpg
