andrasfuchs/BioBalanceDetector/Photos/Proto05/IMG_20161221_170827_Programming_PDI_breadboard.jpg

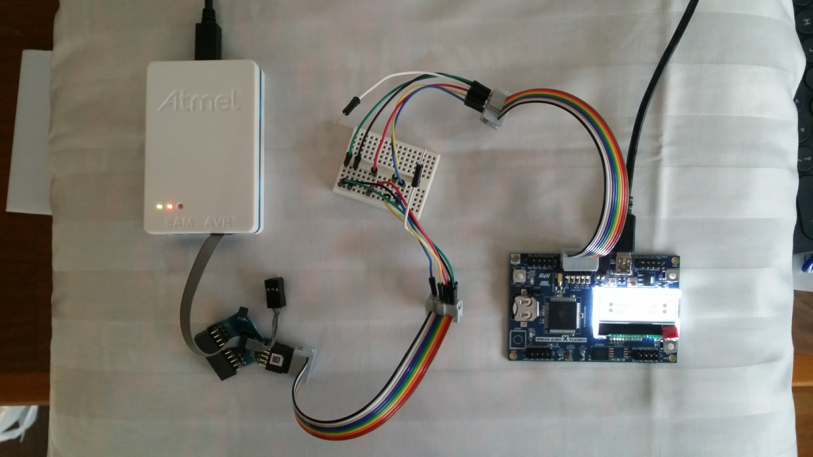
Photos/Proto05/IMG_20161221_170827_Programming_PDI_breadboard.jpg
