andrasfuchs/BioBalanceDetector/Photos/Proto05/IMG_20161221_172753_Programming_JTAG.jpg

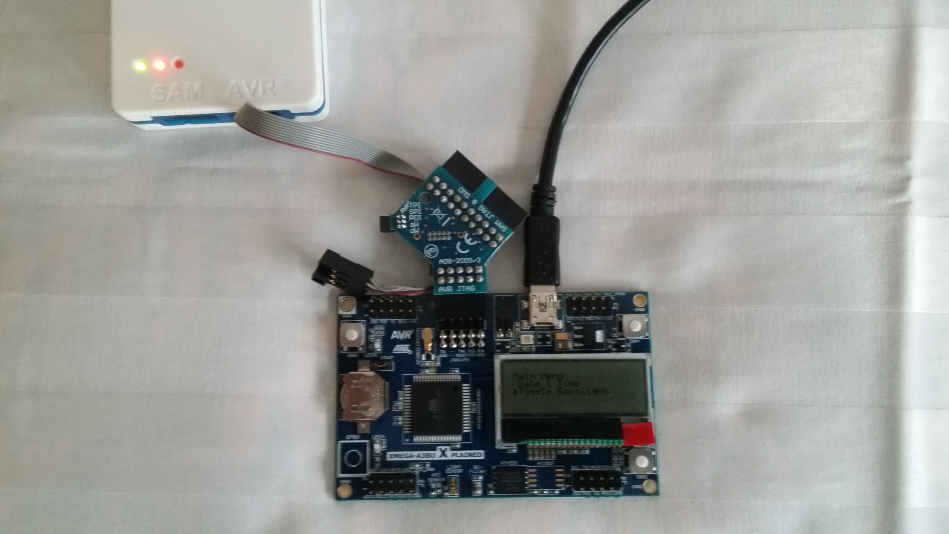
Photos/Proto05/IMG_20161221_172753_Programming_JTAG.jpg
