andrasfuchs/BioBalanceDetector/Photos/Proto05/IMG_20170813_140519_3_Kits.jpg

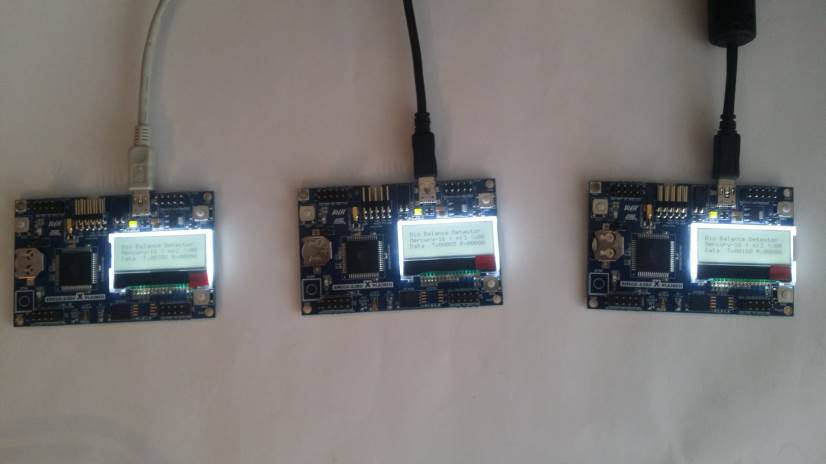
Photos/Proto05/IMG_20170813_140519_3_Kits.jpg
