andrasfuchs/BioBalanceDetector/Photos/Proto05/IMG_20171009_150356_BBD_Flat_Panel_Detector_rev_A.jpg

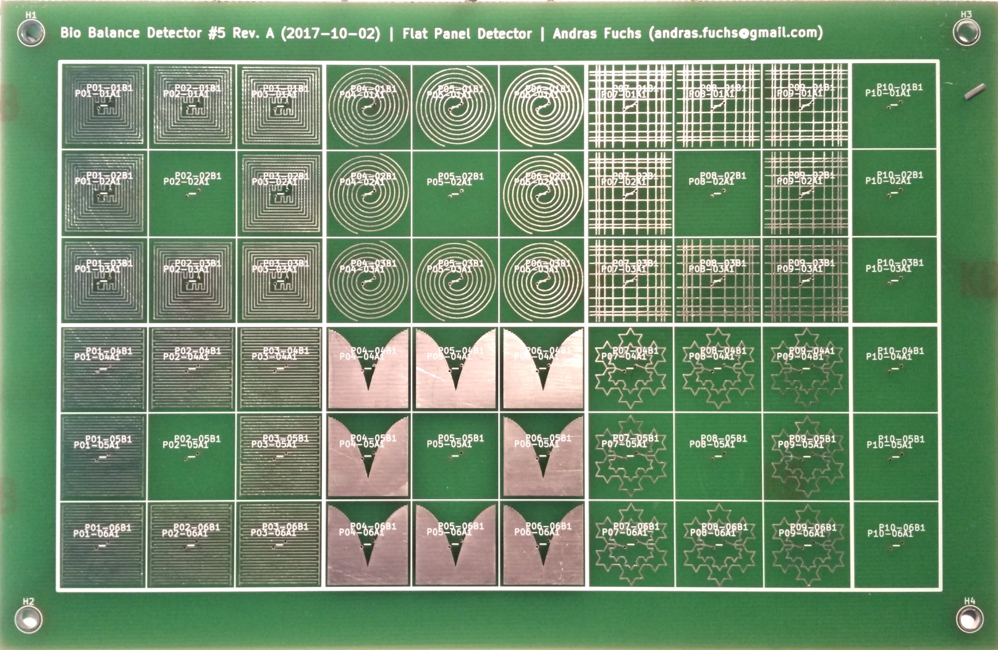
Photos/Proto05/IMG_20171009_150356_BBD_Flat_Panel_Detector_rev_A.jpg
