andrasfuchs/BioBalanceDetector/Photos/Proto05/IMG_20171116_144454_KIBU.jpg

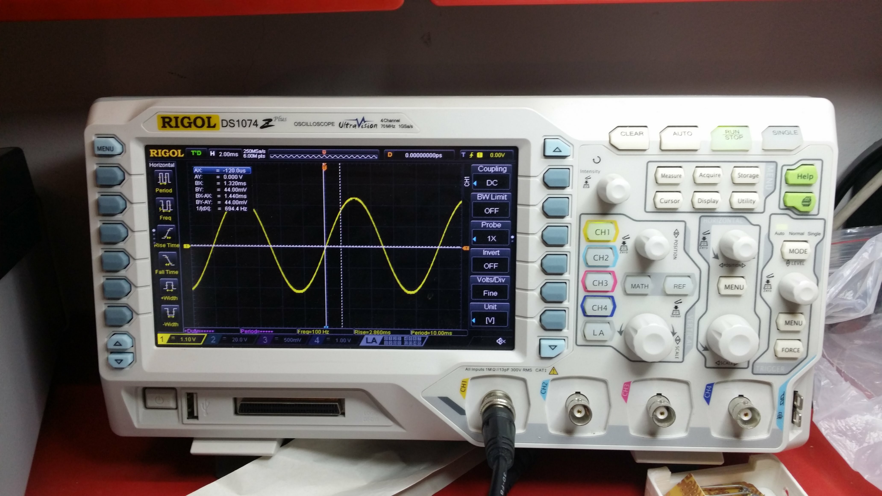
Photos/Proto05/IMG_20171116_144454_KIBU.jpg
