andrasfuchs/BioBalanceDetector/Photos/Proto05/IMG_20171121_160405_KIBU.jpg

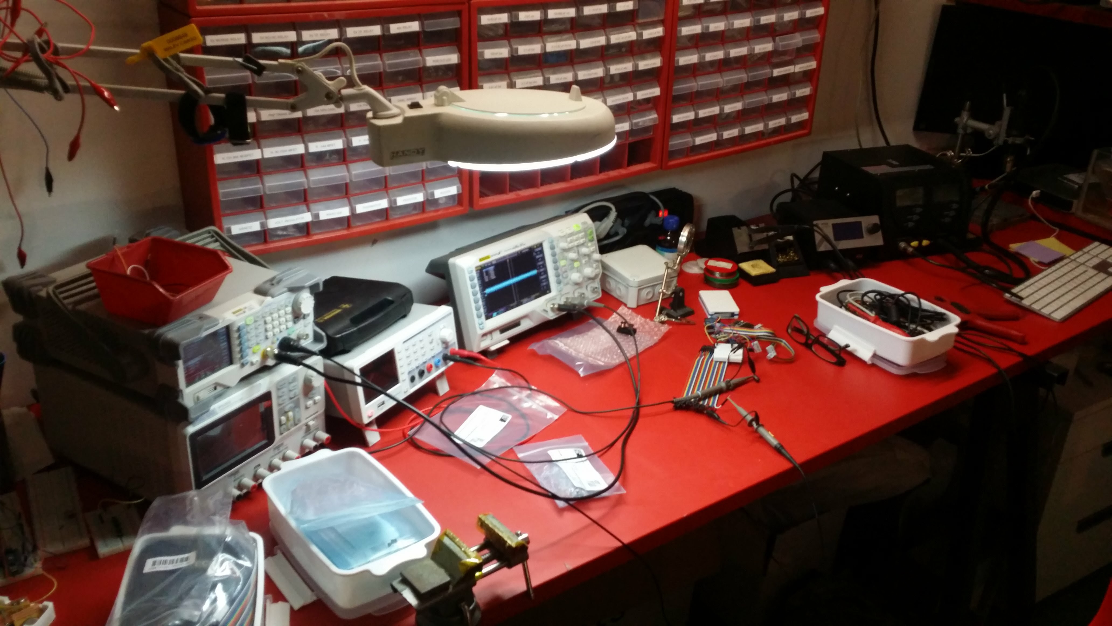
Photos/Proto05/IMG_20171121_160405_KIBU.jpg
