andrasfuchs/BioBalanceDetector/Photos/Proto05/IMG_20180326_150912_BBD_Flat_Panel_Detector_rev_B.jpg

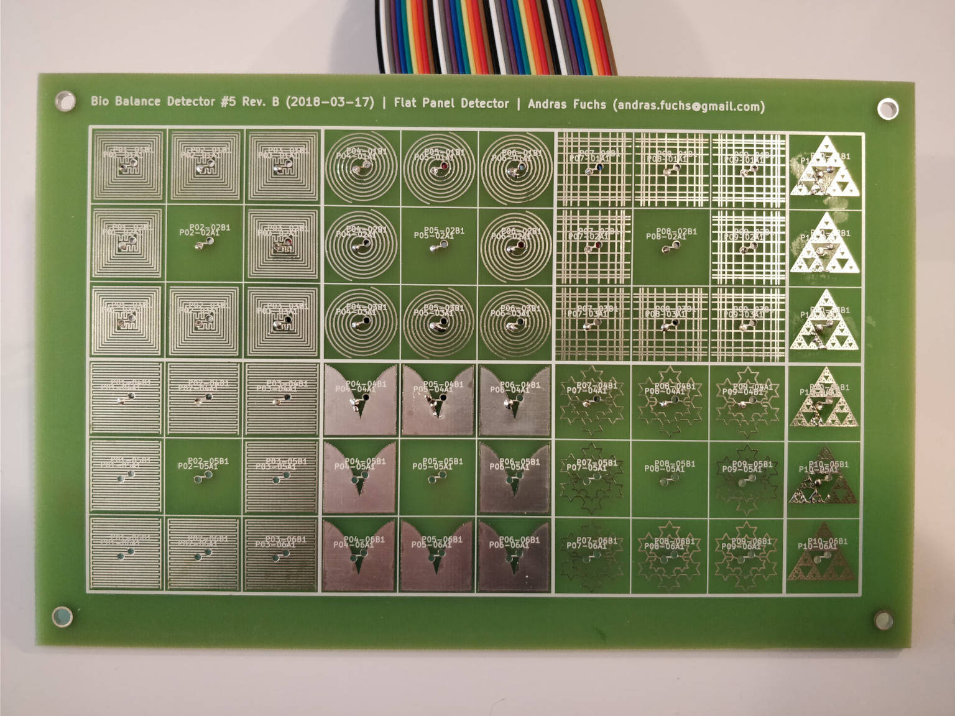
Photos/Proto05/IMG_20180326_150912_BBD_Flat_Panel_Detector_rev_B.jpg
