andrasfuchs/BioBalanceDetector/Photos/Proto05/SCR_20161221_151545_AtmelICEFirmwareUpgrade.png

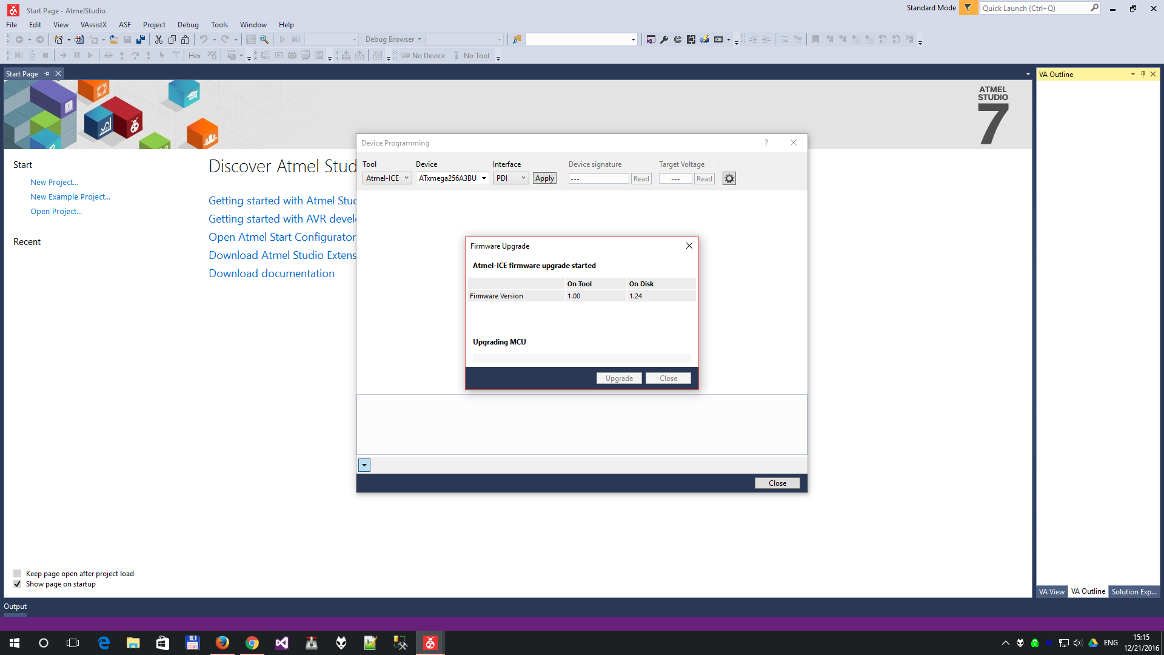
Photos/Proto05/SCR_20161221_151545_AtmelICEFirmwareUpgrade.png
