andrasfuchs/BioBalanceDetector/Photos/Proto05/SCR_20161221_210312_XplainedDemoApp.png

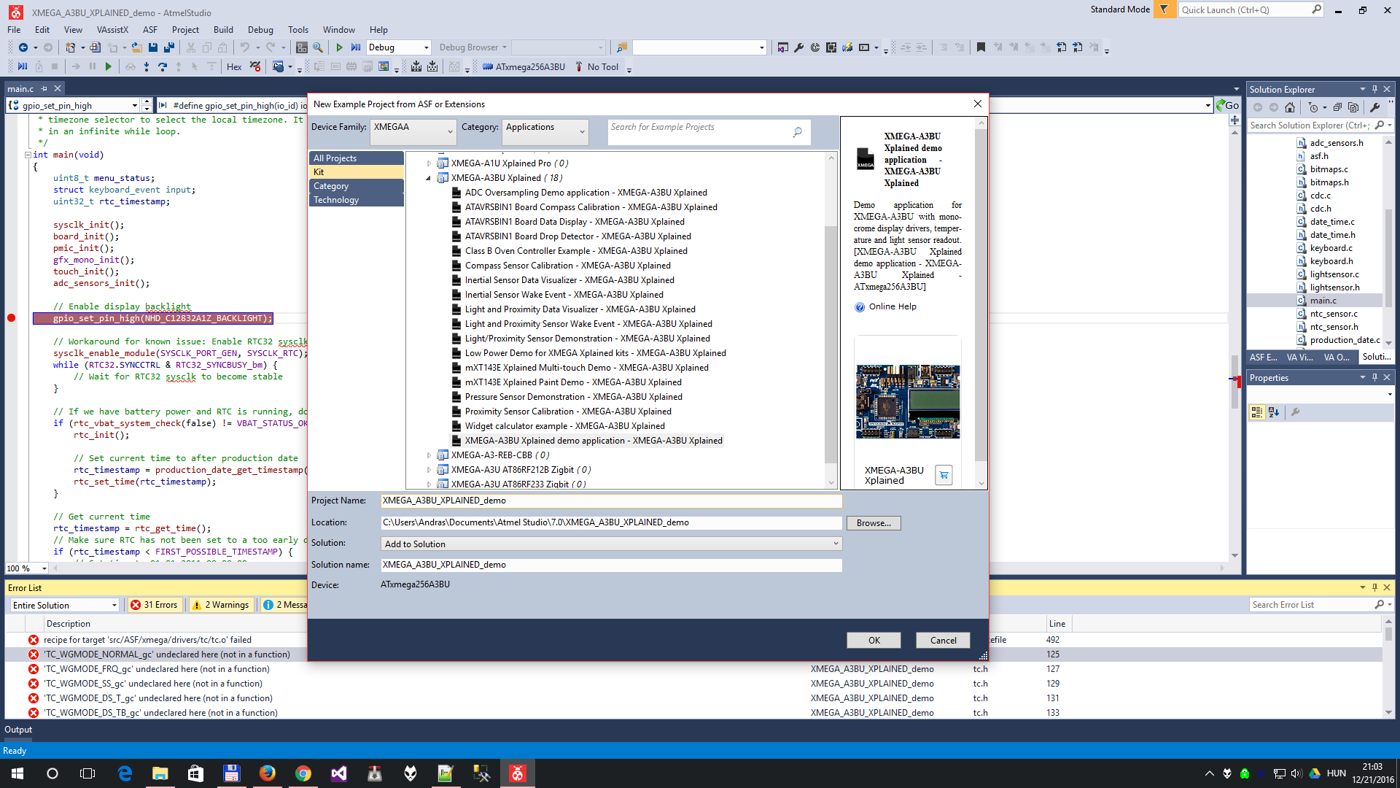
Photos/Proto05/SCR_20161221_210312_XplainedDemoApp.png
