andrasfuchs/BioBalanceDetector/Photos/Proto05/SCR_20161221_210656_XMEGA-A3BU_Xplained_errorlist.png

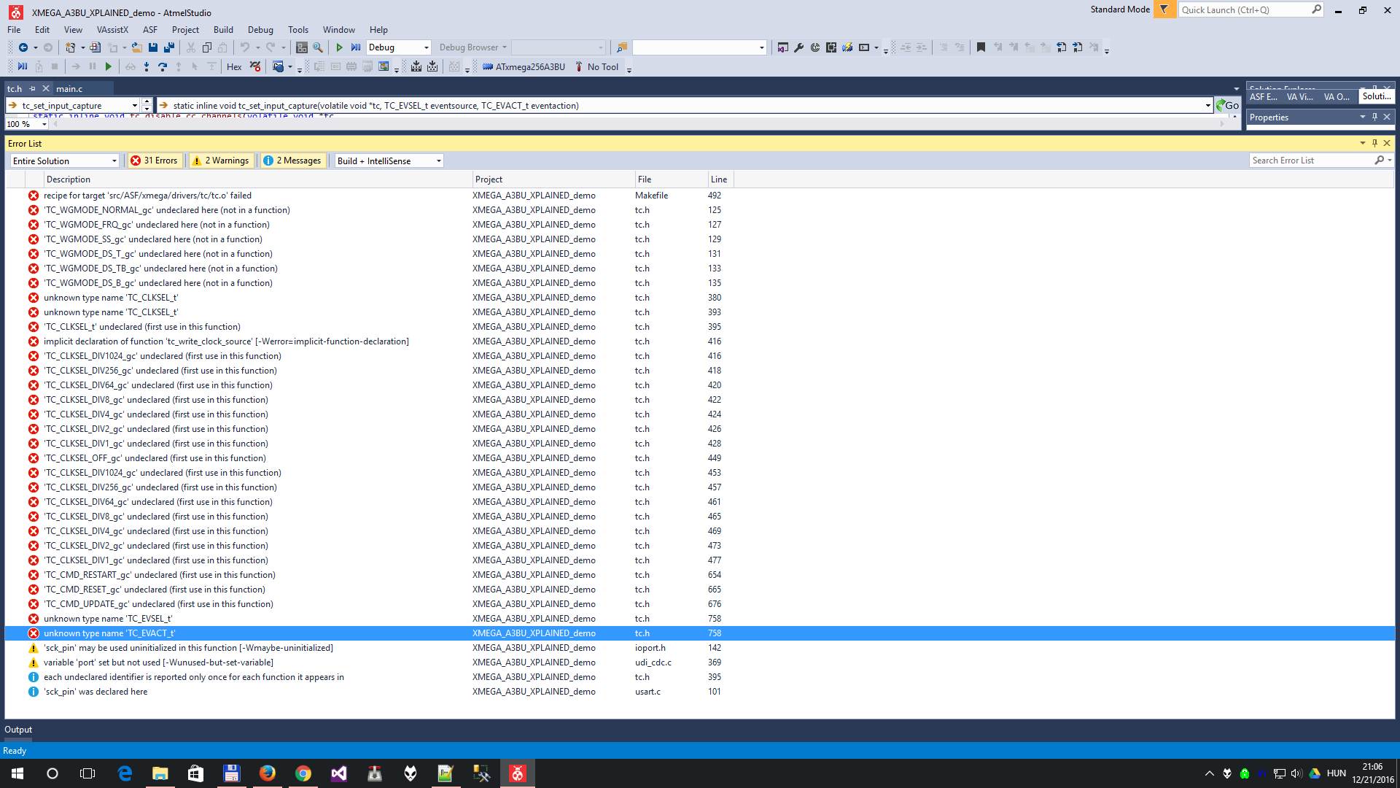
Photos/Proto05/SCR_20161221_210656_XMEGA-A3BU_Xplained_errorlist.png
