andrasfuchs/BioBalanceDetector/Photos/Proto06/20180511_BioBalanceDetector_Venus-256_RevA_PCB_render.png

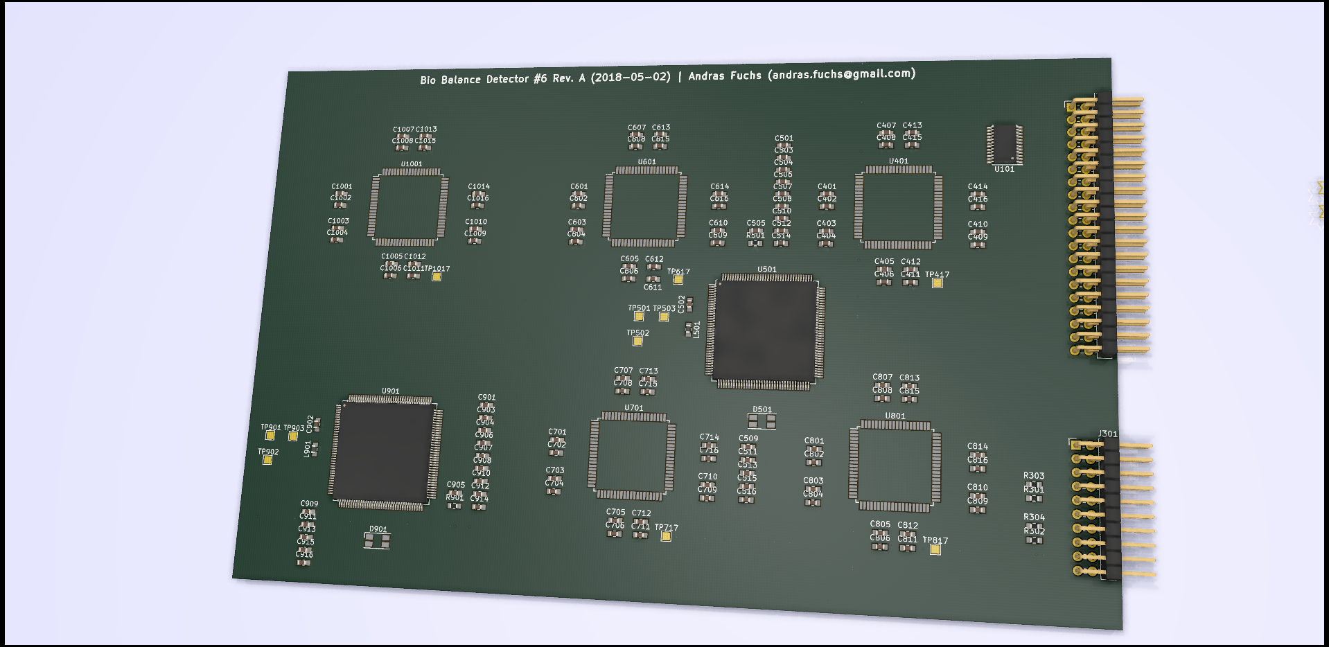
Photos/Proto06/20180511_BioBalanceDetector_Venus-256_RevA_PCB_render.png
