andrasfuchs/BioBalanceDetector/Photos/Proto06/IMG_20180410_101508_RaspberryPi3B+.jpg

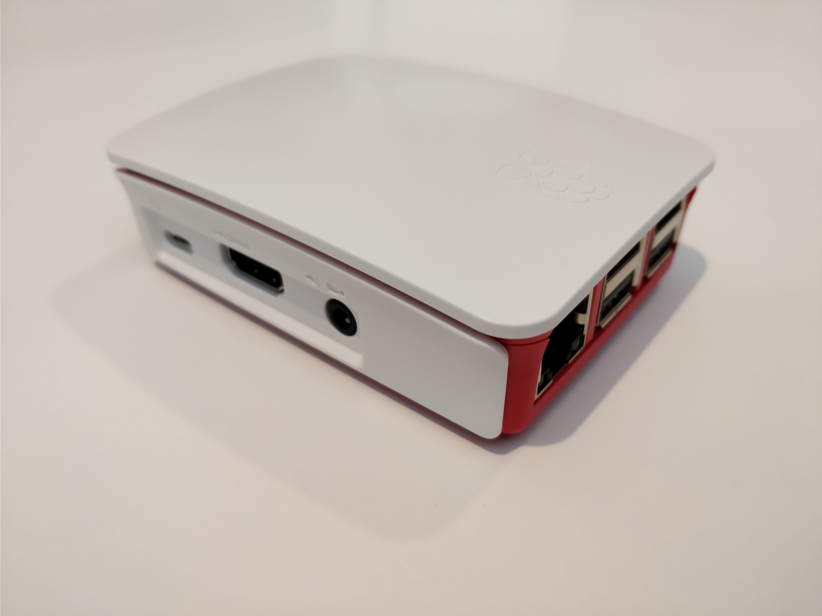
Photos/Proto06/IMG_20180410_101508_RaspberryPi3B+.jpg
