andrasfuchs/BioBalanceDetector/Photos/Proto06/IMG_20180410_121315_SAME70_Xplained.jpg

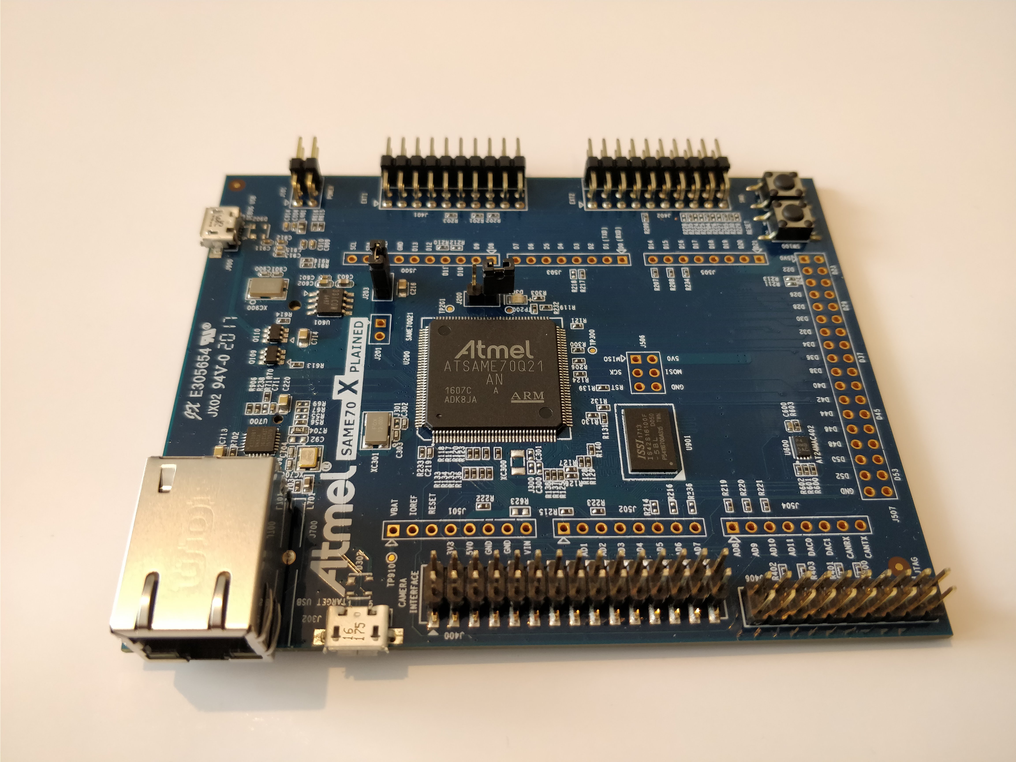
Photos/Proto06/IMG_20180410_121315_SAME70_Xplained.jpg
