andrasfuchs/BioBalanceDetector/Photos/Proto06/IMG_20180410_121455_SAME70Q21_AD7616.jpg

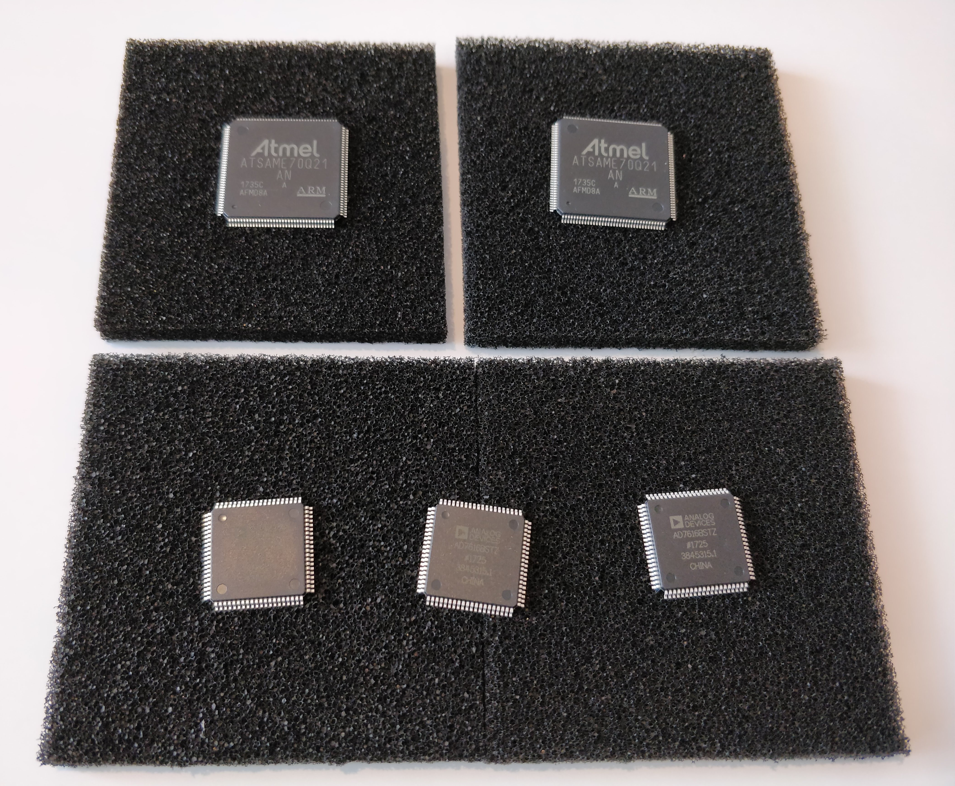
Photos/Proto06/IMG_20180410_121455_SAME70Q21_AD7616.jpg
