andrasfuchs/BioBalanceDetector/Photos/Proto06/IMG_20180427_170558_Merkaba_antennas.jpg

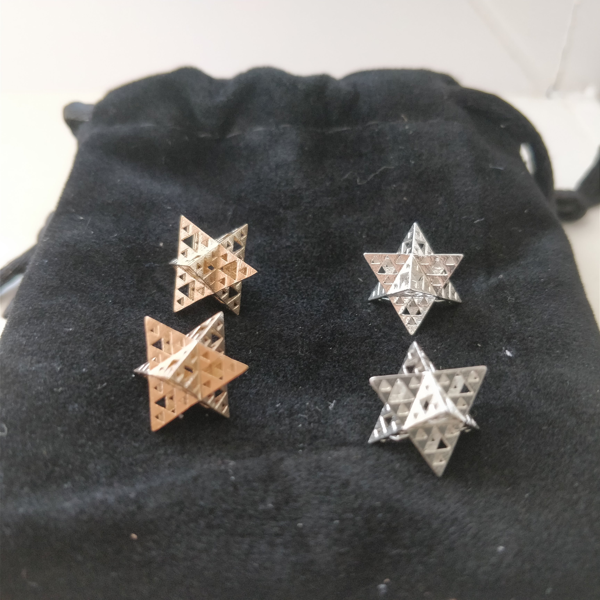
Photos/Proto06/IMG_20180427_170558_Merkaba_antennas.jpg
