andrasfuchs/BioBalanceDetector/Photos/Proto07/20200511-BioBalanceDetector_Mars-64_RevE_PCB_render-1.png

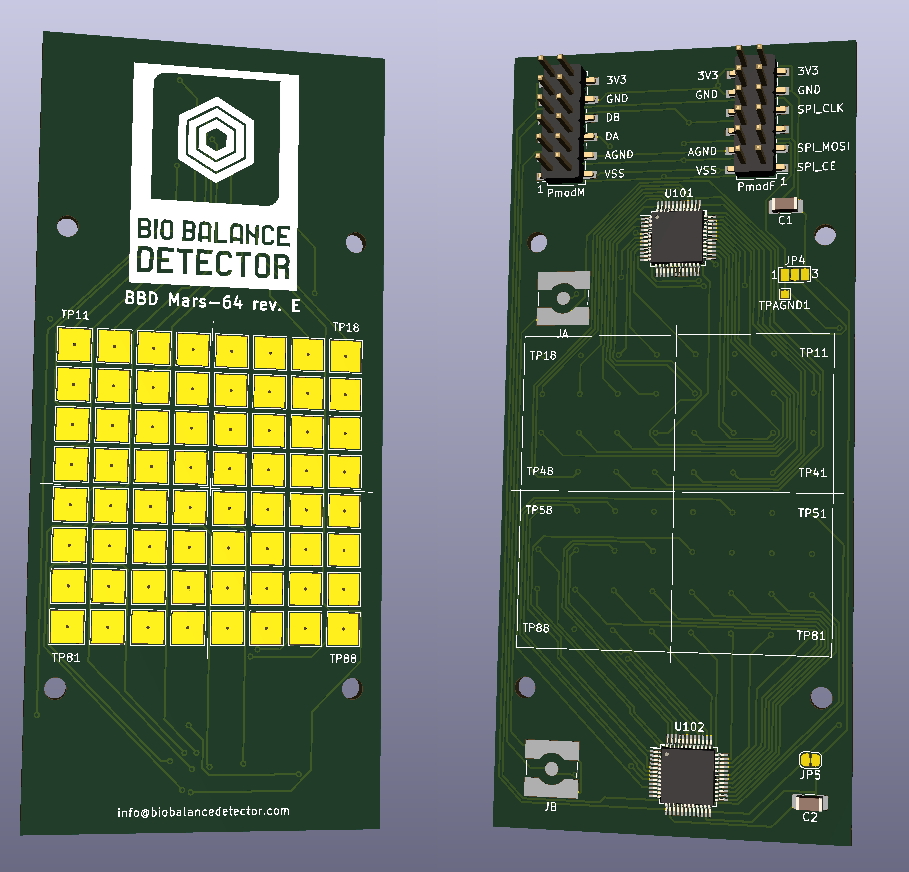
Photos/Proto07/20200511-BioBalanceDetector_Mars-64_RevE_PCB_render-1.png
