andrasfuchs/BioBalanceDetector/Photos/TrueSenseKit/IMG_20151217_164349.jpg

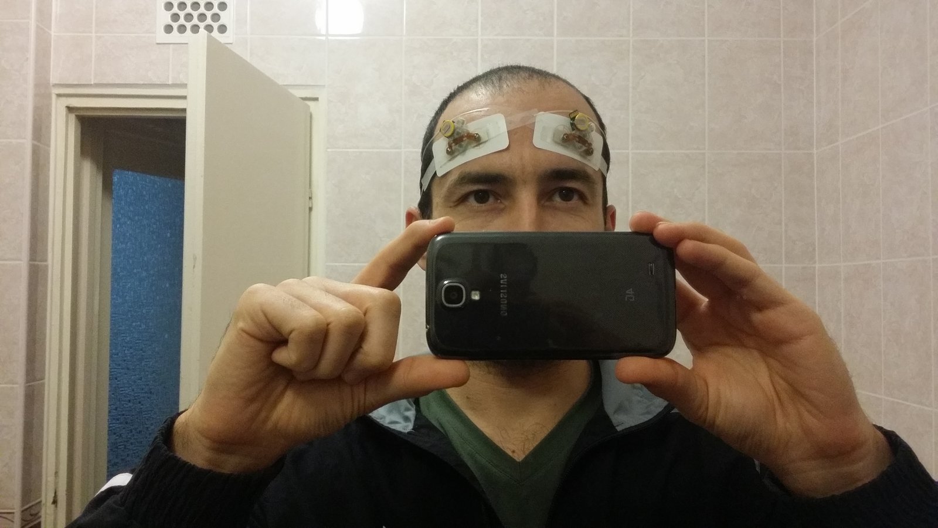
Photos/TrueSenseKit/IMG_20151217_164349.jpg
