andrasfuchs/BioBalanceDetector/Software/GUIDesign/cargo_ui_concept.jpg

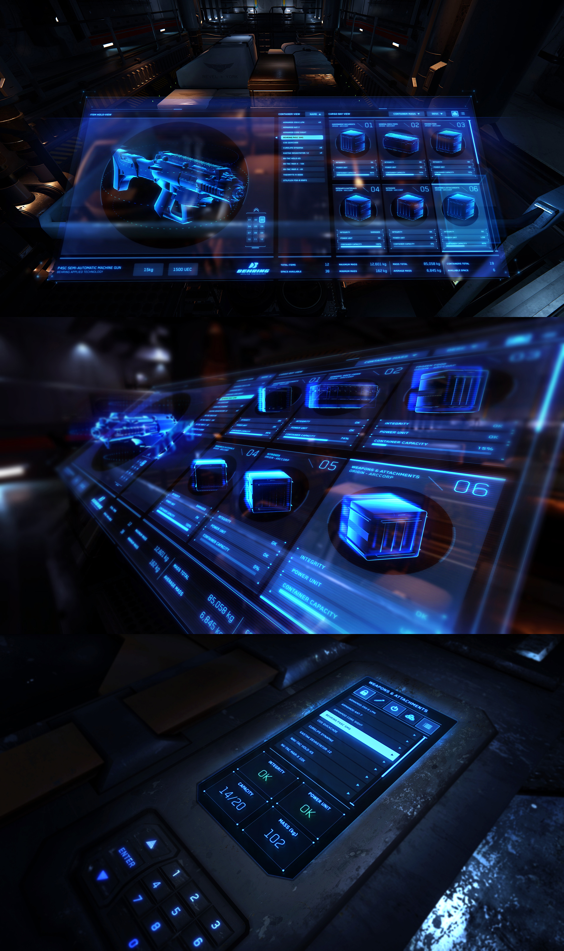
Software/GUIDesign/cargo_ui_concept.jpg
