andrasfuchs/BioBalanceDetector/Software/GUIDesign/stock-vector-abstract-future-concept-vector-futuristic-blue-virtual-graphic-touch-user-interface-hud-for-web-251223427.jpg

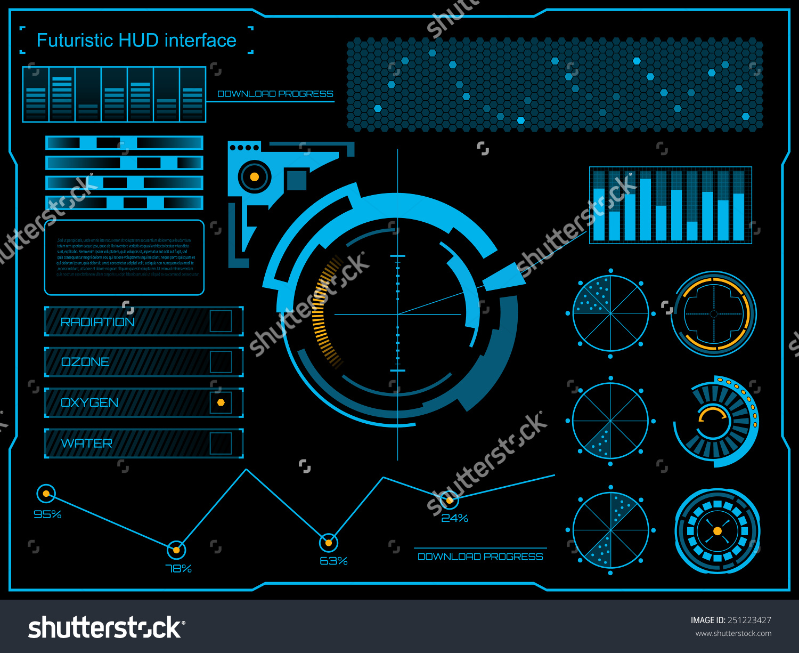
Software/GUIDesign/stock-vector-abstract-future-concept-vector-futuristic-blue-virtual-graphic-touch-user-interface-hud-for-web-251223427.jpg
