andrasfuchs/BioBalanceDetector/Website/Blog/02_Prominent_Figures/Albert_Szent-Gyorgyi.jpg

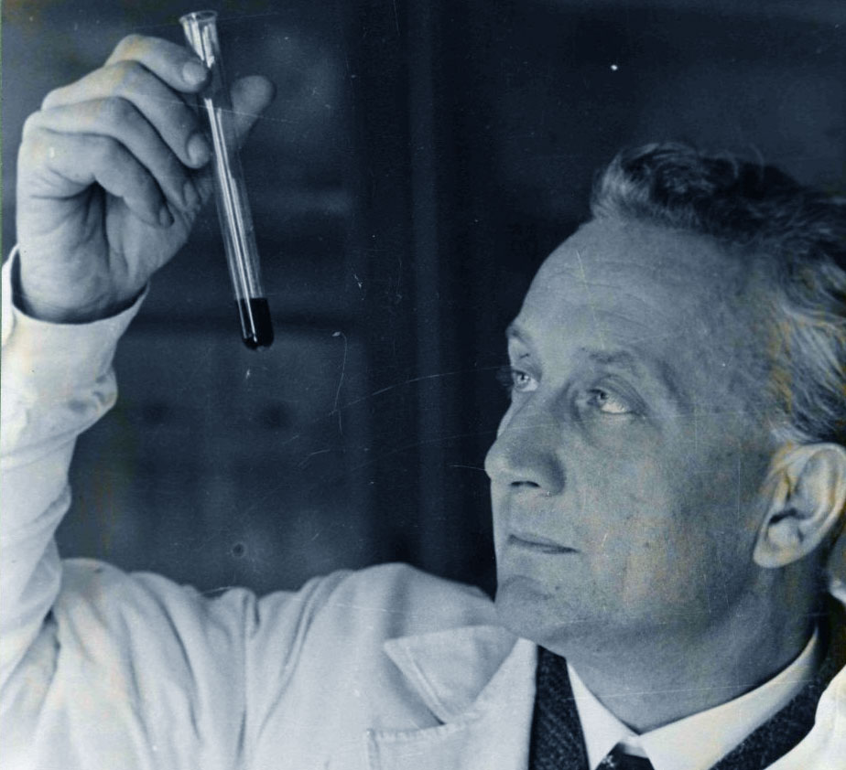
Website/Blog/02_Prominent_Figures/Albert_Szent-Gyorgyi.jpg
