andrasfuchs/BioBalanceDetector/Website/Blog/02_Prominent_Figures/Bruno_Groening.jpg

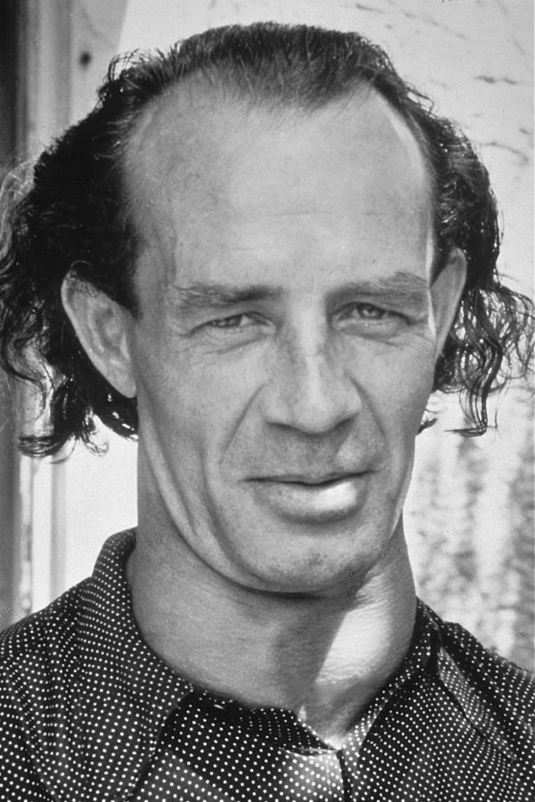
Website/Blog/02_Prominent_Figures/Bruno_Groening.jpg
