andrasfuchs/BioBalanceDetector/Website/Blog/02_Prominent_Figures/Hulda_Clark.jpg

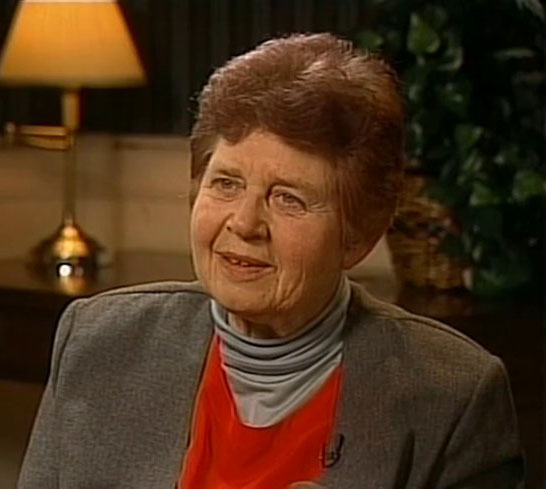
Website/Blog/02_Prominent_Figures/Hulda_Clark.jpg
