andrasfuchs/BioBalanceDetector/Website/Blog/02_Prominent_Figures/Nikola_Tesla.jpg

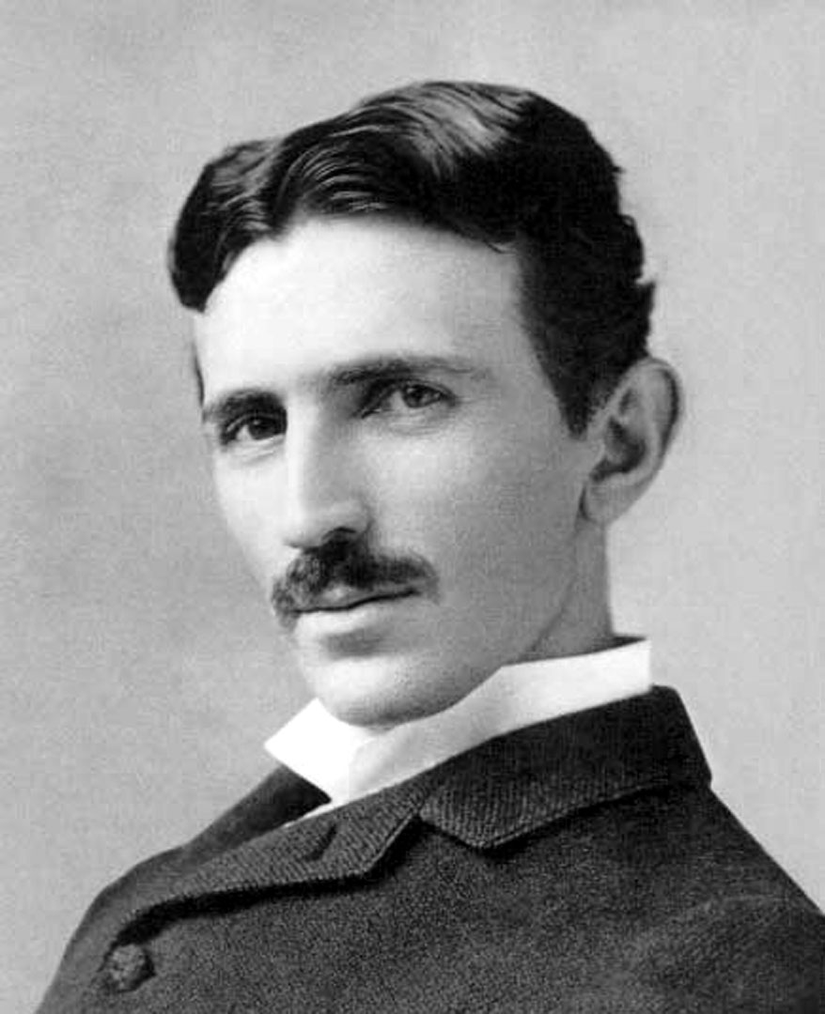
Website/Blog/02_Prominent_Figures/Nikola_Tesla.jpg
