andrasfuchs/BioBalanceDetector/Website/Blog/02_Prominent_Figures/Royal_Raymond_Rife.png

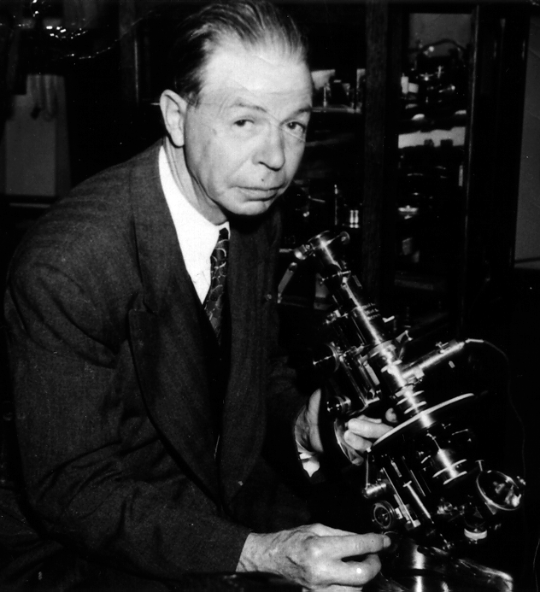
Website/Blog/02_Prominent_Figures/Royal_Raymond_Rife.png
