andrasfuchs/BioBalanceDetector/Website/Blog/02_Prominent_Figures/Wilhelm_Reich.jpg

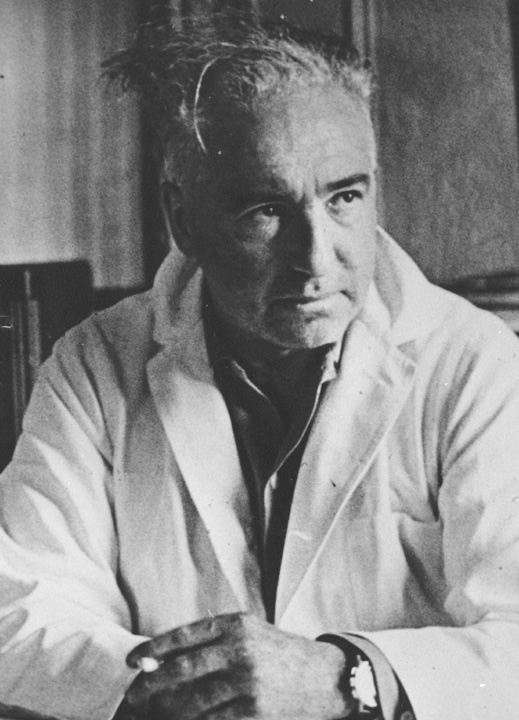
Website/Blog/02_Prominent_Figures/Wilhelm_Reich.jpg
