andrasfuchs/BioBalanceDetector/Website/Blog/03_Recent_Developments/Bryant_A_Meyers_-_PEMF_The_Fifth_Element_of_Health_(2013).jpg

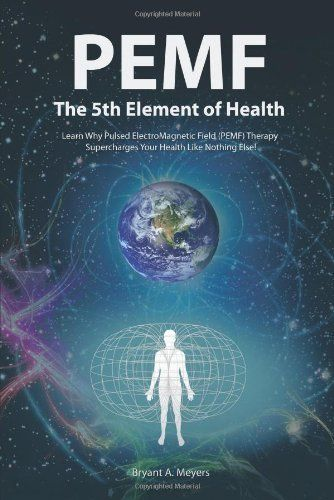
Website/Blog/03_Recent_Developments/Bryant_A_Meyers_-_PEMF_The_Fifth_Element_of_Health_(2013).jpg
