andrasfuchs/BioBalanceDetector/Website/Blog/03_Recent_Developments/Dean_Radin_-_Real_Magic_(2018)_340x500.jpg

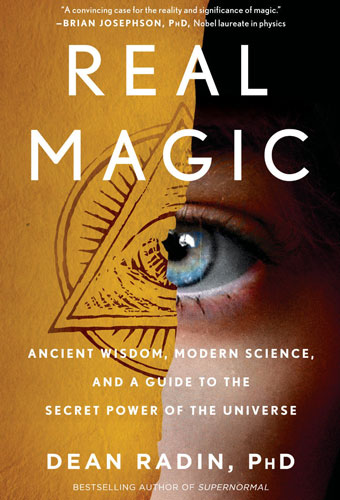
Website/Blog/03_Recent_Developments/Dean_Radin_-_Real_Magic_(2018)_340x500.jpg
