andrasfuchs/BioBalanceDetector/Website/Blog/03_Recent_Developments/Ildiko_Hodnik_-_The_body_of_the_soul_Auradynamics_(2015).jpg

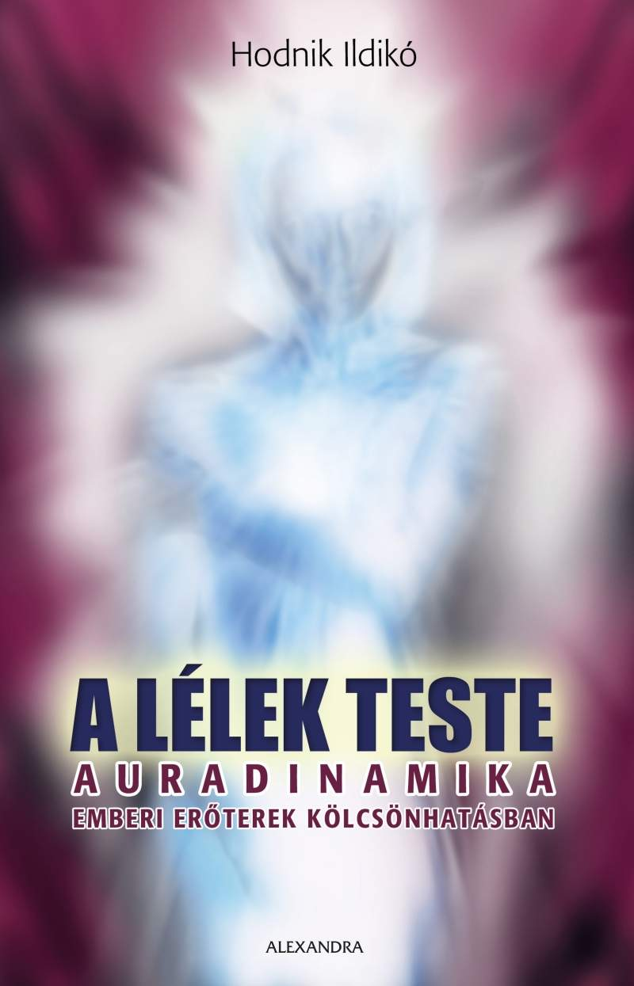
Website/Blog/03_Recent_Developments/Ildiko_Hodnik_-_The_body_of_the_soul_Auradynamics_(2015).jpg
