andrasfuchs/BioBalanceDetector/Website/Blog/03_Recent_Developments/Leonard_J_Ravitz_-_Electrodynamic_Man_(2002).jpg

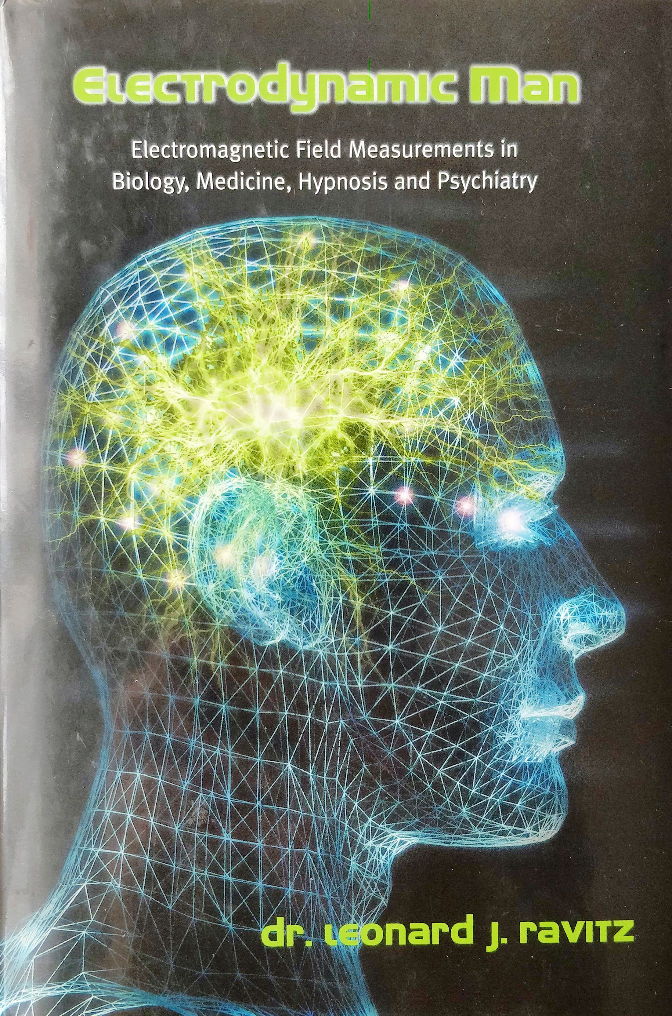
Website/Blog/03_Recent_Developments/Leonard_J_Ravitz_-_Electrodynamic_Man_(2002).jpg
