andrasfuchs/BioBalanceDetector/Website/Design/image-450w-223402249.jpg

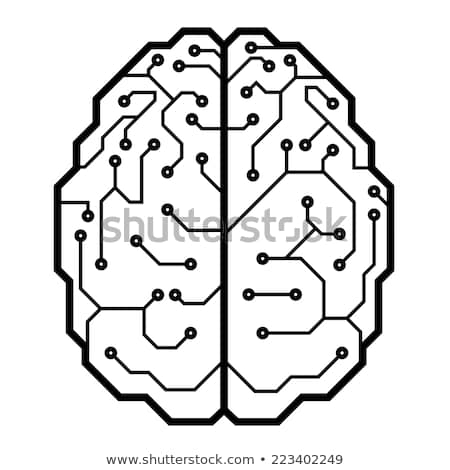
Website/Design/image-450w-223402249.jpg
