andrasfuchs/BioBalanceDetector/Website/Design/istockphoto-517969392-1024x1024.jpg

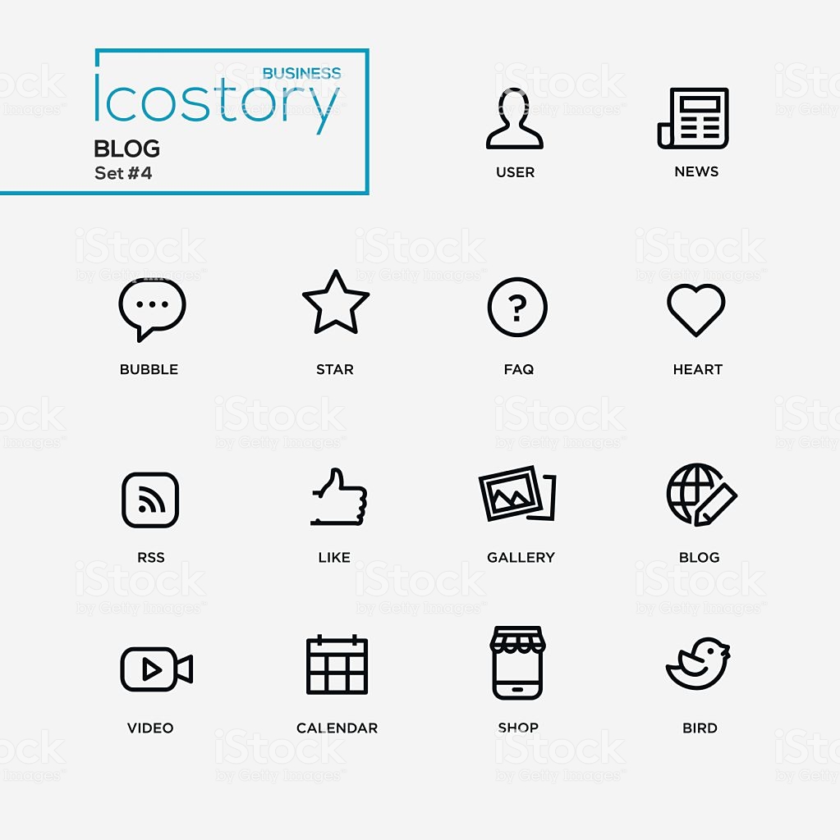
Website/Design/istockphoto-517969392-1024x1024.jpg
