andrasfuchs/BioBalanceDetector/Website/Version_2/img/Blog_450x450.png

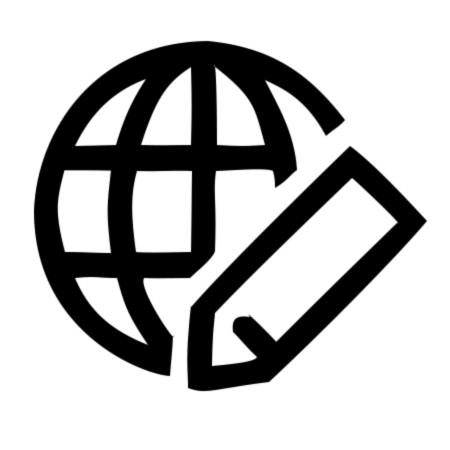
Website/Version_2/img/Blog_450x450.png
