andrasfuchs/BioBalanceDetector/Website/Version_2/img/GitHub-Mark_450x450.png

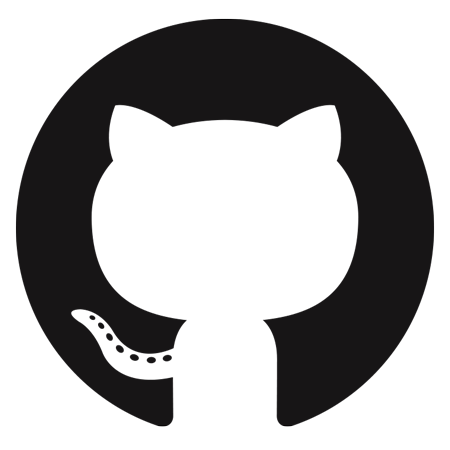
Website/Version_2/img/GitHub-Mark_450x450.png
