andrasfuchs/BioBalanceDetector/Research/fabrication/FOSDEM2020-Order_components.png

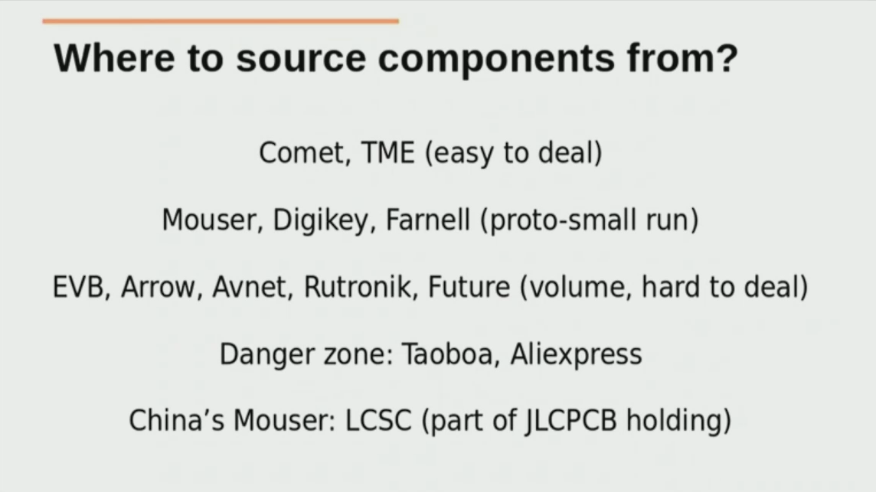
Research/fabrication/FOSDEM2020-Order_components.png
