andrasfuchs/BioBalanceDetector/Research/fabrication/FOSDEM2020-Order_PCB.png

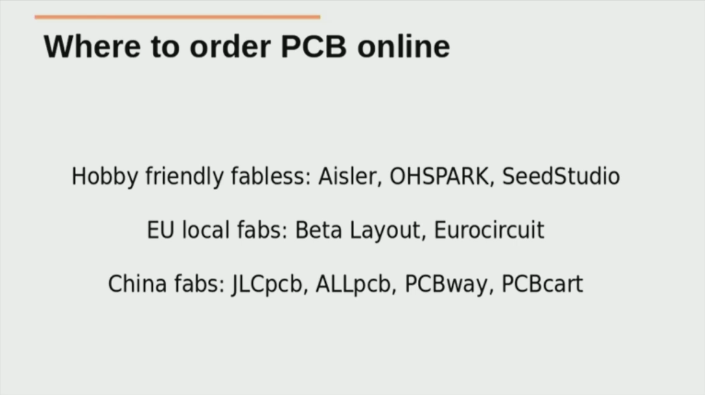
Research/fabrication/FOSDEM2020-Order_PCB.png
