andrasfuchs/BioBalanceDetector/Hardware/Fabrication/BBDProto06/BBDProto06_Venus-256_RevA_v1_173x110mm_F.jpg

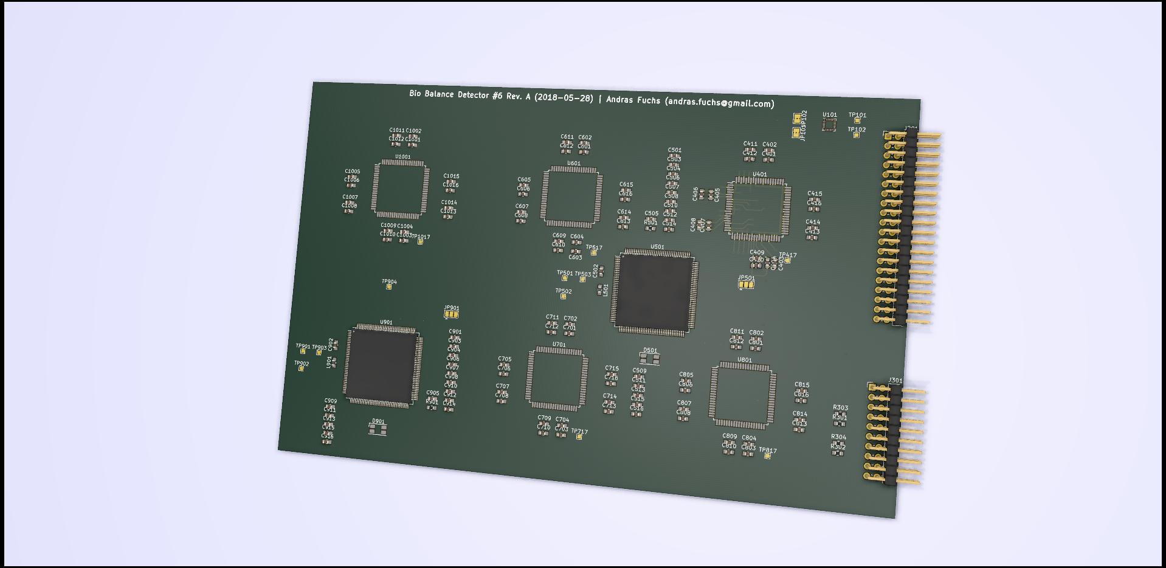
Hardware/Fabrication/BBDProto06/BBDProto06_Venus-256_RevA_v1_173x110mm_F.jpg
