andrasfuchs/BioBalanceDetector/Measurements/Spooky2/01_IrregularVoltageReport/01_Spooky2HardwareSetup.jpg

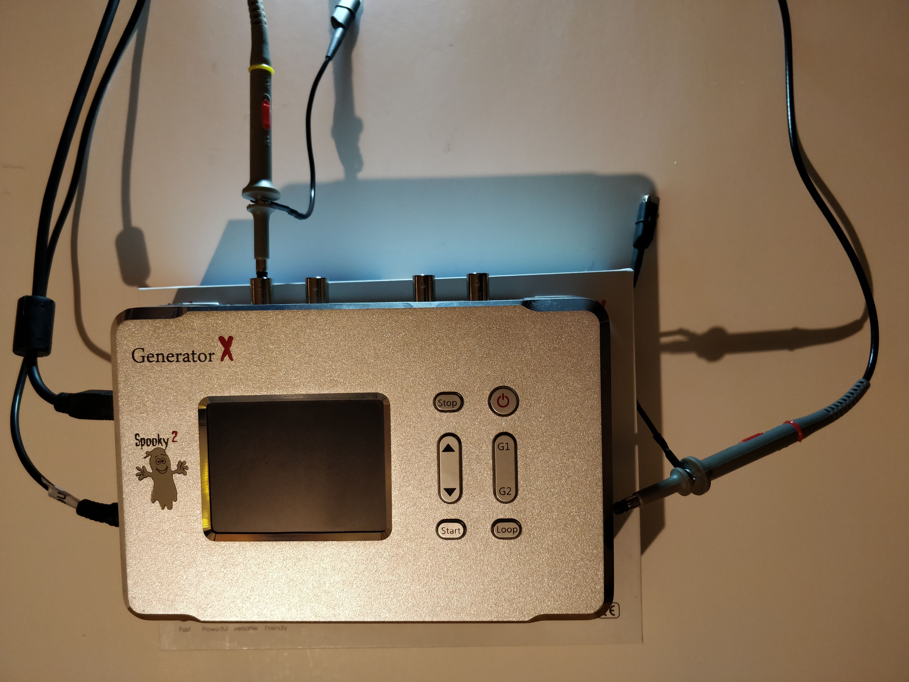
Measurements/Spooky2/01_IrregularVoltageReport/01_Spooky2HardwareSetup.jpg
