andrasfuchs/BioBalanceDetector/Measurements/Spooky2/99_OtherScans/Spooky2.20180503/ScanData/Disconnected/GeneratorX_G1_OUT1_TENSCable_HandCylinders_1SampleStep_1HzTo40MHz/ControlTab.png

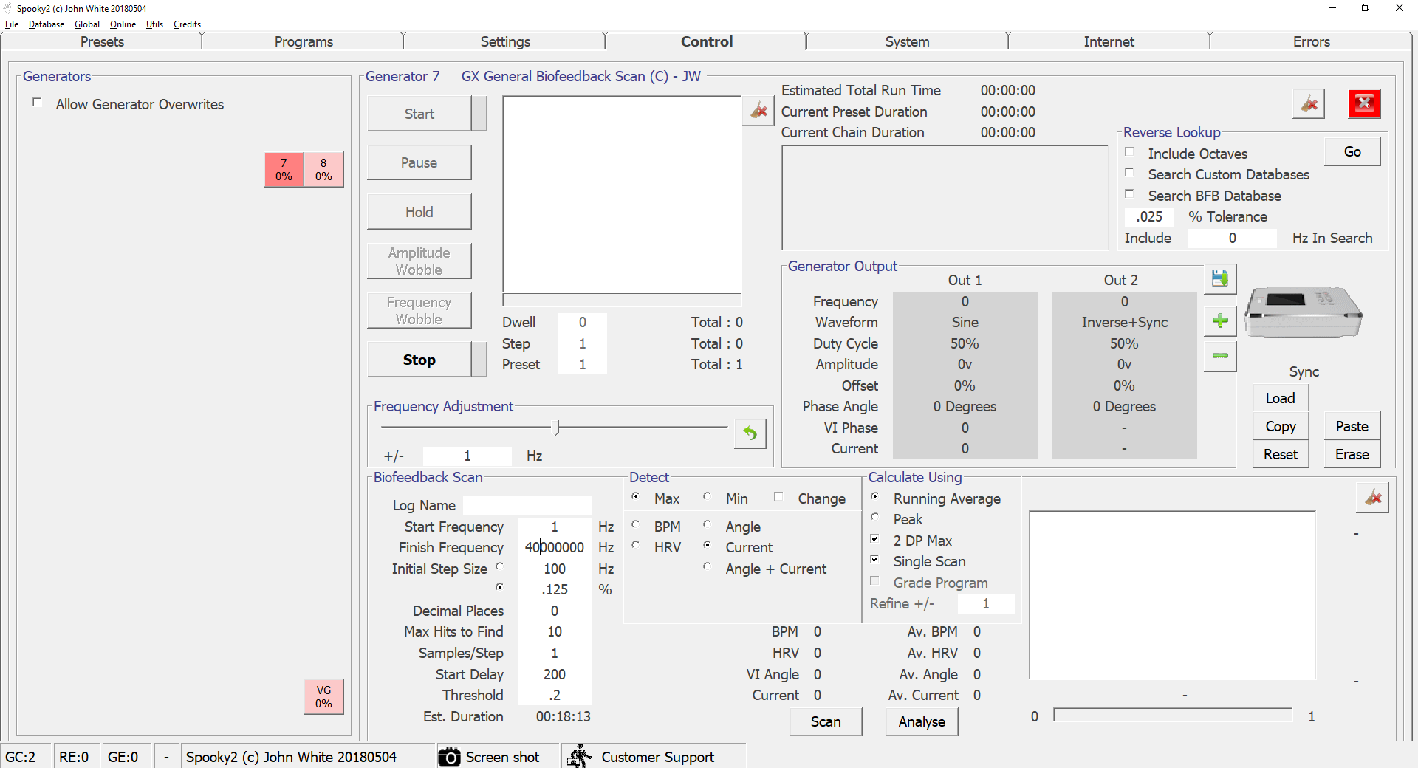
Measurements/Spooky2/99_OtherScans/Spooky2.20180503/ScanData/Disconnected/GeneratorX_G1_OUT1_TENSCable_HandCylinders_1SampleStep_1HzTo40MHz/ControlTab.png
