andrasfuchs/BioBalanceDetector/Measurements/WaveForms/Experiments/AcusticAmplifiedEgelyReactor/01_AcusticAmplifiedReactorT01-Setup.jpg

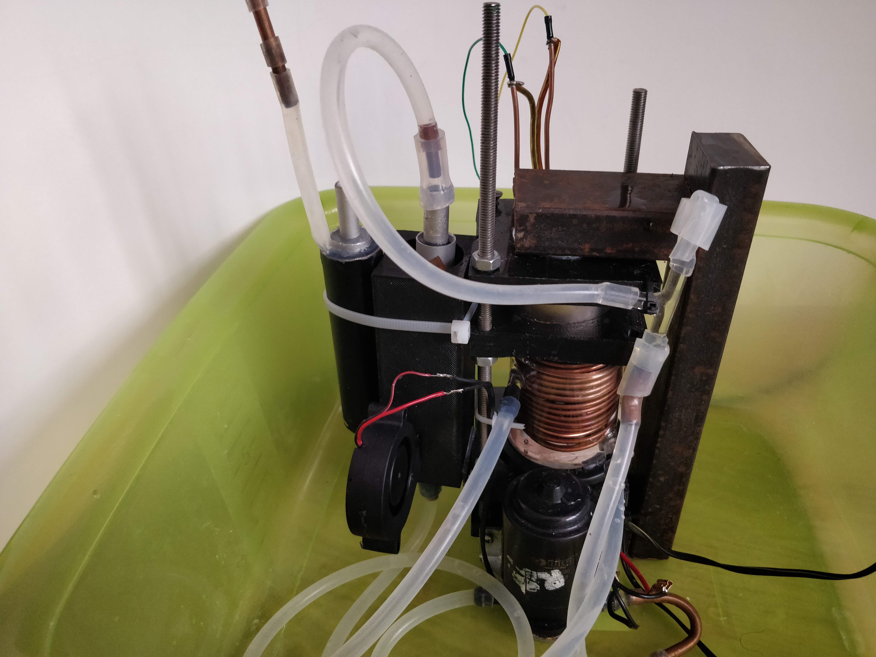
Measurements/WaveForms/Experiments/AcusticAmplifiedEgelyReactor/01_AcusticAmplifiedReactorT01-Setup.jpg
