andrasfuchs/BioBalanceDetector/Measurements/WaveForms/Experiments/AcusticAmplifiedEgelyReactor/05_AcusticAmplifiedReactorT04-Setup.jpg

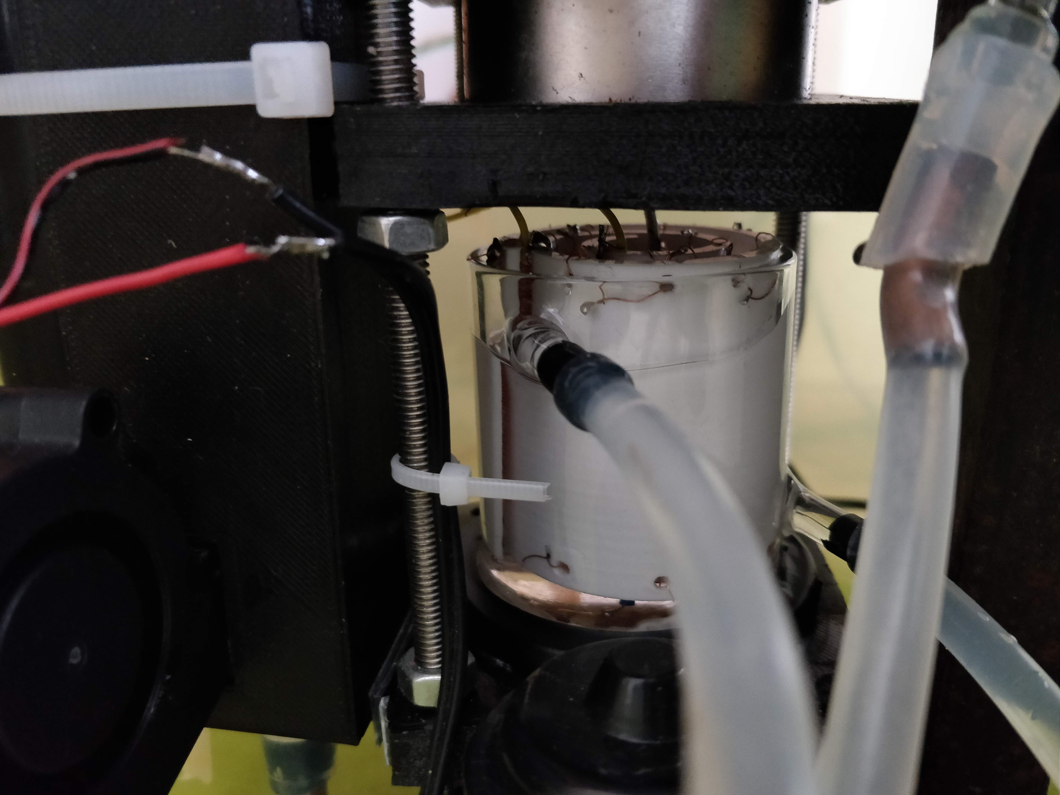
Measurements/WaveForms/Experiments/AcusticAmplifiedEgelyReactor/05_AcusticAmplifiedReactorT04-Setup.jpg
