andrasfuchs/BioBalanceDetector/Software/GUIDesign/0c667d22618599.56315aa35e2e5.jpg

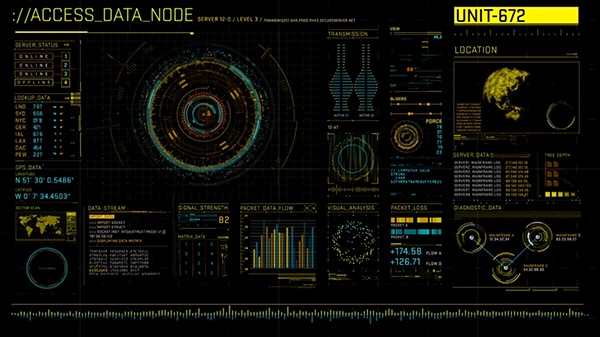
Software/GUIDesign/0c667d22618599.56315aa35e2e5.jpg
