andrasfuchs/BioBalanceDetector/Software/GUIDesign/45cdc49b15b93f33f528c50598b30af9.jpg

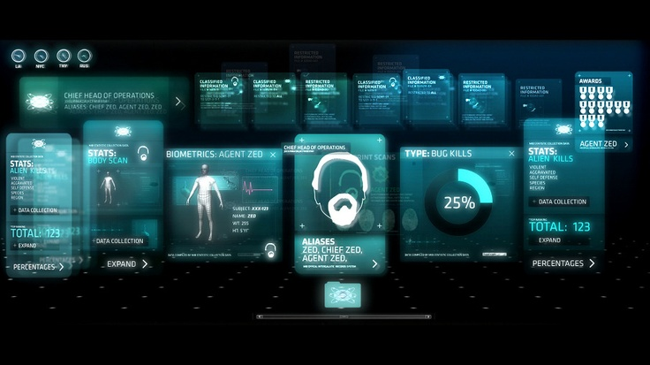
Software/GUIDesign/45cdc49b15b93f33f528c50598b30af9.jpg
