andrasfuchs/BioBalanceDetector/Software/GUIDesign/103734777.jpg

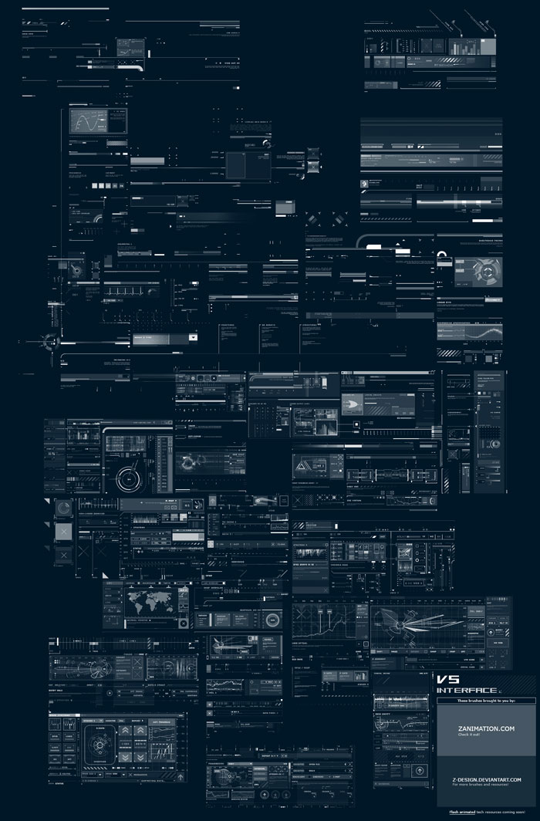
Software/GUIDesign/103734777.jpg
