andrasfuchs/BioBalanceDetector/Software/GUIDesign/hitech_scifi_medical_user_interface_by_s0nkite-d7frzey.jpg

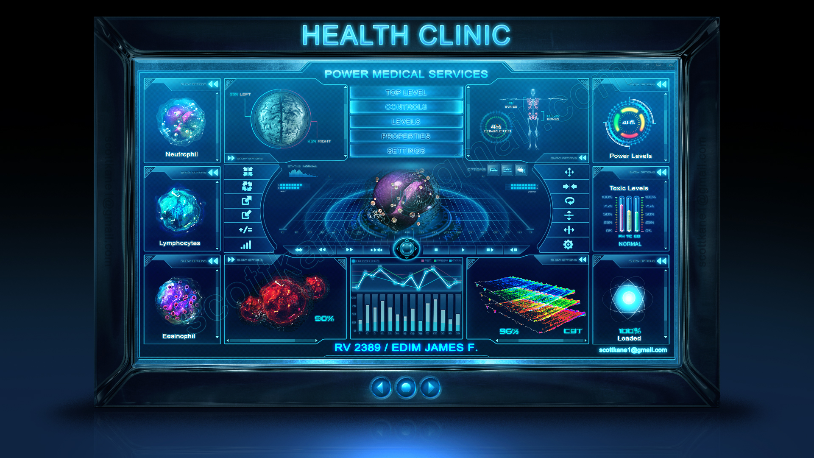
Software/GUIDesign/hitech_scifi_medical_user_interface_by_s0nkite-d7frzey.jpg
