andrasfuchs/BioBalanceDetector/Software/GUIDesign/image.jpg

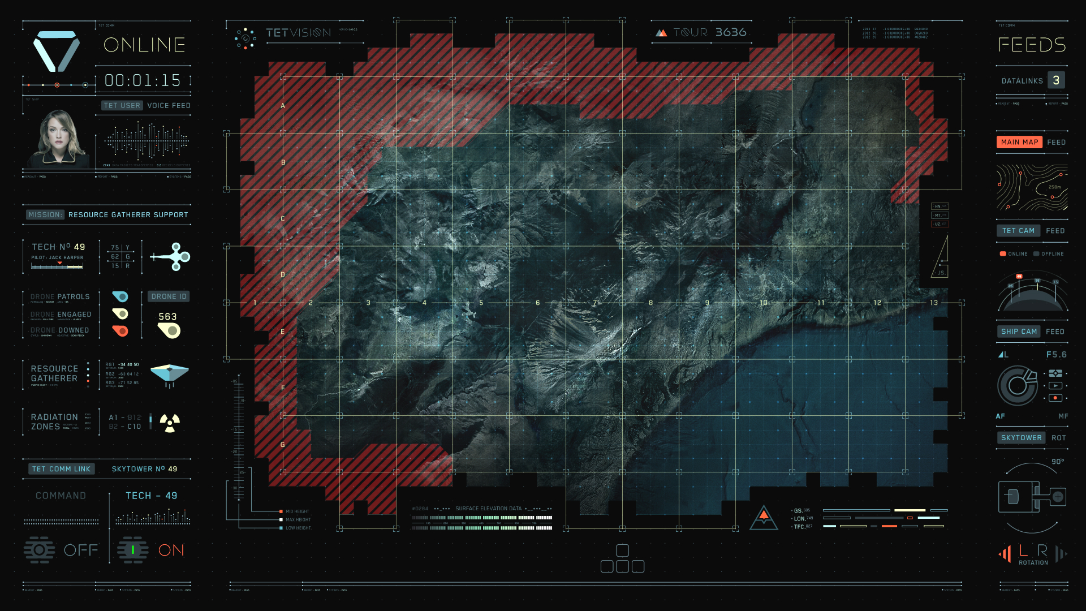
Software/GUIDesign/image.jpg
