andrasfuchs/BioBalanceDetector/Software/GUIDesign/merlin_hud.jpg

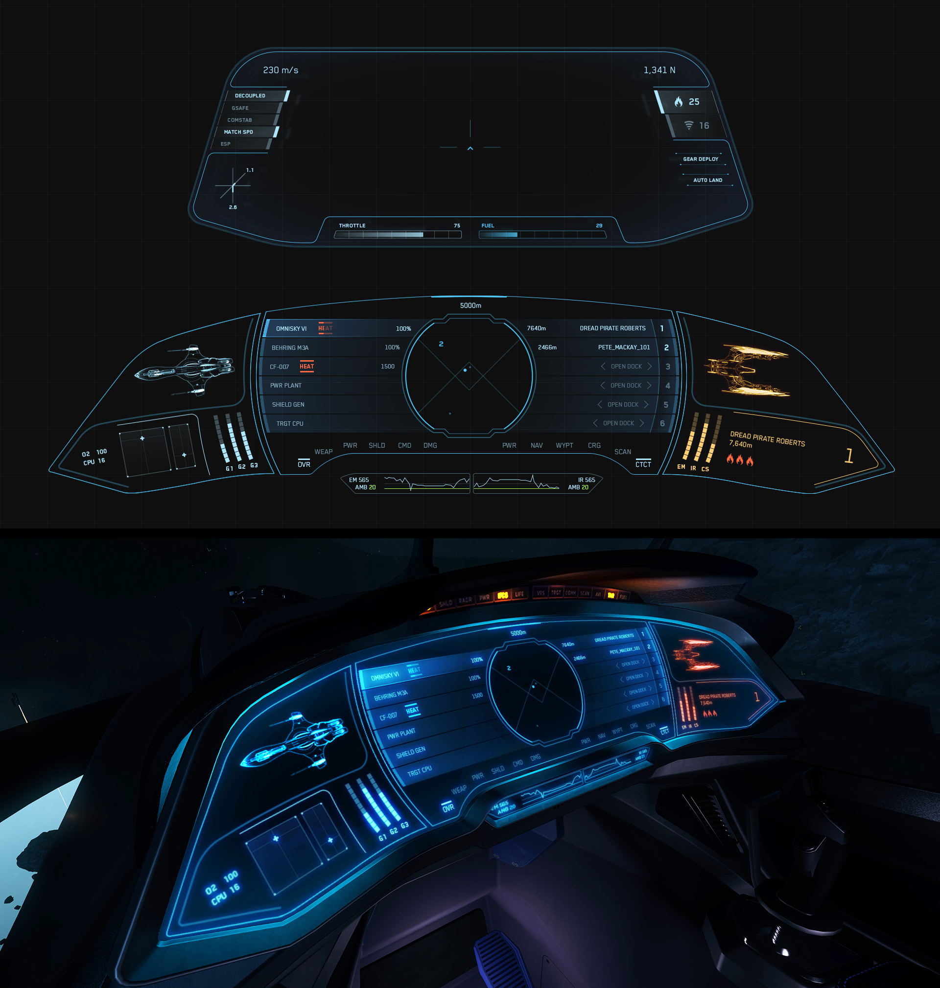
Software/GUIDesign/merlin_hud.jpg
