andrasfuchs/BioBalanceDetector/Software/GUIDesign/mobiglas.jpg

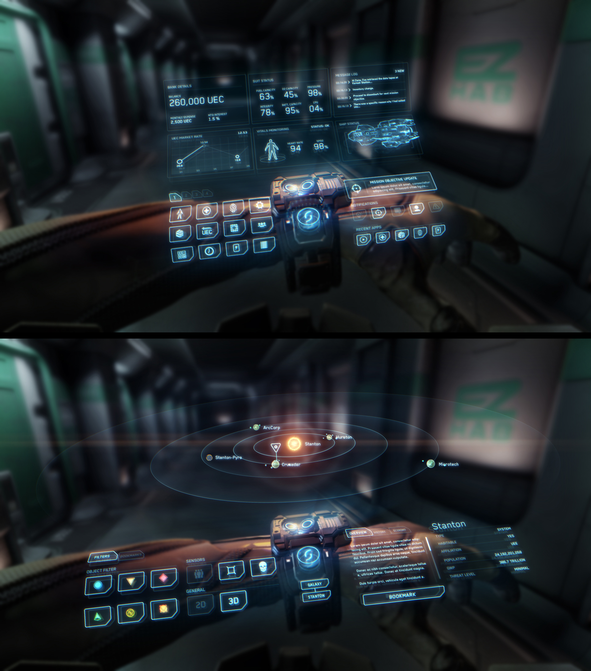
Software/GUIDesign/mobiglas.jpg
