andrasfuchs/BioBalanceDetector/Software/GUIDesign/starmap_contexts.jpg

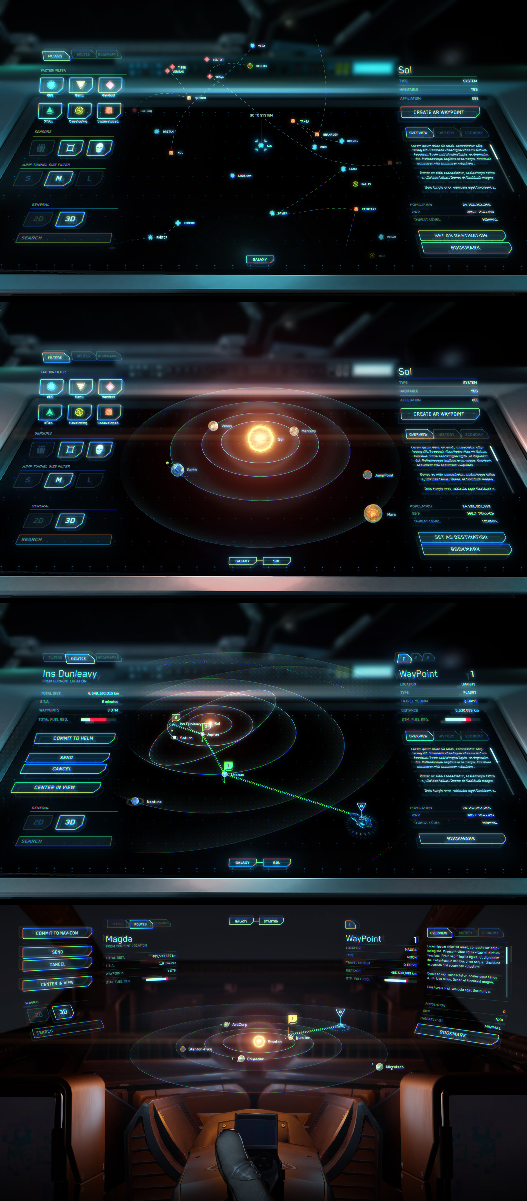
Software/GUIDesign/starmap_contexts.jpg
