andrasfuchs/BioBalanceDetector/Measurements/Spooky2/99_OtherScans/Spooky2.20180805/ScanData/Disconnected/GeneratorX_G1_1HzTo40MHz/BFB_20180807_0828_49.csv

Date_Time | Frequency | BPM | HRV | Angle | Current | Angle + Current | Spare | Spare | Spare | Spare | Spare
20180807_0829_10 | 1 | 0 | 0 | 638.69 | 391.42 | 1030.11 | 0 | 0 | 0 | 0 | 0
20180807_0829_10 | 1.00125 | 0 | 0 | 638.69 | 391.426666666667 | 1030.11666666667 | 0 | 0 | 0 | 0 | 0
20180807_0829_10 | 1.0025 | 0 | 0 | 638.69 | 391.44 | 1030.13 | 0 | 0 | 0 | 0 | 0
20180807_0829_10 | 1.00375 | 0 | 0 | 638.69 | 391.44 | 1030.13 | 0 | 0 | 0 | 0 | 0
20180807_0829_10 | 1.005 | 0 | 0 | 638.69 | 391.44 | 1030.13 | 0 | 0 | 0 | 0 | 0
20180807_0829_10 | 1.00626 | 0 | 0 | 638.69 | 391.44 | 1030.13 | 0 | 0 | 0 | 0 | 0
20180807_0829_11 | 1.00752 | 0 | 0 | 638.696666666667 | 391.44 | 1030.13666666667 | 0 | 0 | 0 | 0 | 0
20180807_0829_11 | 1.00878 | 0 | 0 | 638.71 | 391.44 | 1030.15 | 0 | 0 | 0 | 0 | 0
20180807_0829_11 | 1.01004 | 0 | 0 | 638.69 | 391.44 | 1030.13 | 0 | 0 | 0 | 0 | 0
20180807_0829_11 | 1.0113 | 0 | 0 | 638.69 | 391.433333333333 | 1030.12333333333 | 0 | 0 | 0 | 0 | 0
20180807_0829_11 | 1.01256 | 0 | 0 | 638.69 | 391.43 | 1030.12 | 0 | 0 | 0 | 0 | 0
20180807_0829_11 | 1.01383 | 0 | 0 | 638.69 | 391.45 | 1030.14 | 0 | 0 | 0 | 0 | 0
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
