andrasfuchs/BioBalanceDetector/Measurements/Spooky2/99_OtherScans/Spooky2.20180805/ScanData/Disconnected/GeneratorX_G1_1HzTo40MHz_DropletElectrode_None/BFB_20180807_0939_18.csv

Date_Time | Frequency | BPM | HRV | Angle | Current | Angle + Current | Spare | Spare | Spare | Spare | Spare
20180807_0939_31 | 1 | 0 | 0 | 68.92 | 409.63 | 478.55 | 0 | 0 | 0 | 0 | 0
20180807_0939_31 | 1.00125 | 0 | 0 | 65.2266666666667 | 403.9 | 469.126666666667 | 0 | 0 | 0 | 0 | 0
20180807_0939_32 | 1.0025 | 0 | 0 | 64.4566666666667 | 408.02 | 472.476666666667 | 0 | 0 | 0 | 0 | 0
20180807_0939_32 | 1.00375 | 0 | 0 | 66.61 | 405.706666666667 | 472.316666666667 | 0 | 0 | 0 | 0 | 0
20180807_0939_32 | 1.005 | 0 | 0 | 62.93 | 406.076666666667 | 469.006666666667 | 0 | 0 | 0 | 0 | 0
20180807_0939_32 | 1.00626 | 0 | 0 | 67.51 | 409.13 | 476.64 | 0 | 0 | 0 | 0 | 0
20180807_0939_32 | 1.00752 | 0 | 0 | 64.91 | 407.89 | 472.8 | 0 | 0 | 0 | 0 | 0
20180807_0939_33 | 1.00878 | 0 | 0 | 63.2566666666667 | 407.29 | 470.546666666667 | 0 | 0 | 0 | 0 | 0
20180807_0939_33 | 1.01004 | 0 | 0 | 62.9833333333333 | 407.55 | 470.533333333333 | 0 | 0 | 0 | 0 | 0
20180807_0939_33 | 1.0113 | 0 | 0 | 63.5233333333333 | 406.306666666667 | 469.83 | 0 | 0 | 0 | 0 | 0
20180807_0939_33 | 1.01256 | 0 | 0 | 62.39 | 408.36 | 470.75 | 0 | 0 | 0 | 0 | 0
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
