andrasfuchs/BioBalanceDetector/Measurements/Spooky2/99_OtherScans/Spooky2.20180805/ScanData/Disconnected/GeneratorX_G1_41kHzTo18MHz/BFB_20180807_1356_07.csv

Date_Time | Frequency | BPM | HRV | Angle | Current | Angle + Current | Spare | Spare | Spare | Spare | Spare
20180807_1356_22 | 41000 | 0 | 0 | 252.853333333333 | 481.8 | 734.653333333333 | 0 | 0 | 0 | 0 | 0
20180807_1356_22 | 41051.25 | 0 | 0 | 252.86 | 481.79 | 734.65 | 0 | 0 | 0 | 0 | 0
20180807_1356_22 | 41102.56 | 0 | 0 | 252.96 | 481.77 | 734.73 | 0 | 0 | 0 | 0 | 0
20180807_1356_22 | 41153.94 | 0 | 0 | 253.096666666667 | 481.79 | 734.886666666667 | 0 | 0 | 0 | 0 | 0
20180807_1356_22 | 41205.38 | 0 | 0 | 253.37 | 481.783333333333 | 735.153333333333 | 0 | 0 | 0 | 0 | 0
20180807_1356_22 | 41256.89 | 0 | 0 | 253.36 | 481.77 | 735.13 | 0 | 0 | 0 | 0 | 0
20180807_1356_23 | 41308.46 | 0 | 0 | 253.4 | 481.72 | 735.12 | 0 | 0 | 0 | 0 | 0
20180807_1356_23 | 41360.1 | 0 | 0 | 253.42 | 481.72 | 735.14 | 0 | 0 | 0 | 0 | 0
20180807_1356_23 | 41411.8 | 0 | 0 | 253.93 | 481.72 | 735.65 | 0 | 0 | 0 | 0 | 0
20180807_1356_23 | 41463.56 | 0 | 0 | 253.95 | 481.77 | 735.72 | 0 | 0 | 0 | 0 | 0
20180807_1356_23 | 41515.39 | 0 | 0 | 253.99 | 481.783333333333 | 735.773333333333 | 0 | 0 | 0 | 0 | 0
20180807_1356_23 | 41567.28 | 0 | 0 | 254.24 | 481.81 | 736.05 | 0 | 0 | 0 | 0 | 0
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
