andrasfuchs/BioBalanceDetector/Measurements/Spooky2/99_OtherScans/Spooky2.20180805/ScanData/Disconnected/GeneratorX_G1_41kHzTo18MHz/BFB_20180807_1657_29.csv

Date_Time | Frequency | BPM | HRV | Angle | Current | Angle + Current | Spare | Spare | Spare | Spare | Spare
20180807_1657_53 | 41000 | 0 | 0 | 638.71 | 390.726666666667 | 1029.43666666667 | 0 | 0 | 0 | 0 | 0
20180807_1657_55 | 41051.25 | 0 | 0 | 638.69 | 395.82 | 1034.51 | 0 | 0 | 0 | 0 | 0
20180807_1657_55 | 41102.56 | 0 | 0 | 638.69 | 395.82 | 1034.51 | 0 | 0 | 0 | 0 | 0
20180807_1657_55 | 41153.94 | 0 | 0 | 638.69 | 395.82 | 1034.51 | 0 | 0 | 0 | 0 | 0
20180807_1657_55 | 41205.38 | 0 | 0 | 638.69 | 395.82 | 1034.51 | 0 | 0 | 0 | 0 | 0
20180807_1657_56 | 41256.89 | 0 | 0 | 638.69 | 395.82 | 1034.51 | 0 | 0 | 0 | 0 | 0
20180807_1657_56 | 41308.46 | 0 | 0 | 638.69 | 395.82 | 1034.51 | 0 | 0 | 0 | 0 | 0
20180807_1657_56 | 41360.1 | 0 | 0 | 638.69 | 395.82 | 1034.51 | 0 | 0 | 0 | 0 | 0
20180807_1657_56 | 41411.8 | 0 | 0 | 638.69 | 395.82 | 1034.51 | 0 | 0 | 0 | 0 | 0
20180807_1657_56 | 41463.56 | 0 | 0 | 638.69 | 395.82 | 1034.51 | 0 | 0 | 0 | 0 | 0
20180807_1657_56 | 41515.39 | 0 | 0 | 638.69 | 395.823333333333 | 1034.51333333333 | 0 | 0 | 0 | 0 | 0
20180807_1657_56 | 41567.28 | 0 | 0 | 638.71 | 395.83 | 1034.54 | 0 | 0 | 0 | 0 | 0
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
