andrasfuchs/BioBalanceDetector/Measurements/Spooky2/99_OtherScans/Spooky2.20180805/ScanData/Disconnected/GeneratorX_G1_41kHzTo18MHz_DropletElectrode_AppleCiderVinergar5pct/BFB_20180807_1154_24.csv

Date_Time | Frequency | BPM | HRV | Angle | Current | Angle + Current | Spare | Spare | Spare | Spare | Spare
20180807_1154_38 | 41000 | 0 | 0 | 64.87 | 547.12 | 611.99 | 0 | 0 | 0 | 0 | 0
20180807_1154_38 | 41051.25 | 0 | 0 | 64.91 | 547.11 | 612.02 | 0 | 0 | 0 | 0 | 0
20180807_1154_38 | 41102.56 | 0 | 0 | 64.9 | 547.13 | 612.03 | 0 | 0 | 0 | 0 | 0
20180807_1154_38 | 41153.94 | 0 | 0 | 64.88 | 547.13 | 612.01 | 0 | 0 | 0 | 0 | 0
20180807_1154_38 | 41205.38 | 0 | 0 | 64.8733333333333 | 547.07 | 611.943333333333 | 0 | 0 | 0 | 0 | 0
20180807_1154_39 | 41256.89 | 0 | 0 | 64.87 | 547.083333333333 | 611.953333333333 | 0 | 0 | 0 | 0 | 0
20180807_1154_39 | 41308.46 | 0 | 0 | 64.82 | 547.09 | 611.91 | 0 | 0 | 0 | 0 | 0
20180807_1154_39 | 41360.1 | 0 | 0 | 64.8466666666667 | 547.1 | 611.946666666667 | 0 | 0 | 0 | 0 | 0
20180807_1154_39 | 41411.8 | 0 | 0 | 64.86 | 547.09 | 611.95 | 0 | 0 | 0 | 0 | 0
20180807_1154_39 | 41463.56 | 0 | 0 | 64.9 | 547.07 | 611.97 | 0 | 0 | 0 | 0 | 0
20180807_1154_39 | 41515.39 | 0 | 0 | 64.89 | 547.06 | 611.95 | 0 | 0 | 0 | 0 | 0
20180807_1154_39 | 41567.28 | 0 | 0 | 64.87 | 547.07 | 611.94 | 0 | 0 | 0 | 0 | 0
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
