andrasfuchs/BioBalanceDetector/Measurements/Spooky2/99_OtherScans/Spooky2.20180805/ScanData/Disconnected/GeneratorX_G1_41kHzTo18MHz_DropletElectrode_AppleCiderVinergar5pct/BFB_20180807_1210_53.csv

Date_Time | Frequency | BPM | HRV | Angle | Current | Angle + Current | Spare | Spare | Spare | Spare | Spare
20180807_1211_08 | 41000 | 0 | 0 | 64.9433333333333 | 547.13 | 612.073333333333 | 0 | 0 | 0 | 0 | 0
20180807_1211_08 | 41051.25 | 0 | 0 | 64.95 | 547.113333333333 | 612.063333333333 | 0 | 0 | 0 | 0 | 0
20180807_1211_08 | 41102.56 | 0 | 0 | 64.94 | 547.08 | 612.02 | 0 | 0 | 0 | 0 | 0
20180807_1211_08 | 41153.94 | 0 | 0 | 64.94 | 547.04 | 611.98 | 0 | 0 | 0 | 0 | 0
20180807_1211_09 | 41205.38 | 0 | 0 | 64.94 | 547.053333333333 | 611.993333333333 | 0 | 0 | 0 | 0 | 0
20180807_1211_09 | 41256.89 | 0 | 0 | 64.94 | 547.08 | 612.02 | 0 | 0 | 0 | 0 | 0
20180807_1211_09 | 41308.46 | 0 | 0 | 64.94 | 547.09 | 612.03 | 0 | 0 | 0 | 0 | 0
20180807_1211_09 | 41360.1 | 0 | 0 | 64.94 | 547.076666666667 | 612.016666666667 | 0 | 0 | 0 | 0 | 0
20180807_1211_09 | 41411.8 | 0 | 0 | 64.94 | 547.07 | 612.01 | 0 | 0 | 0 | 0 | 0
20180807_1211_09 | 41463.56 | 0 | 0 | 64.9433333333333 | 547.13 | 612.073333333333 | 0 | 0 | 0 | 0 | 0
20180807_1211_09 | 41515.39 | 0 | 0 | 64.95 | 547.116666666667 | 612.066666666667 | 0 | 0 | 0 | 0 | 0
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
