andrasfuchs/BioBalanceDetector/Measurements/Spooky2/99_OtherScans/Spooky2.20180805/ScanData/Disconnected/GeneratorX_G1_41kHzTo18MHz_DropletElectrode_AppleCiderVinergar5pct/BFB_20180807_1243_35.csv

Date_Time | Frequency | BPM | HRV | Angle | Current | Angle + Current | Spare | Spare | Spare | Spare | Spare
20180807_1243_50 | 41000 | 0 | 0 | 64.89 | 547.12 | 612.01 | 0 | 0 | 0 | 0 | 0
20180807_1243_50 | 41051.25 | 0 | 0 | 64.89 | 547.14 | 612.03 | 0 | 0 | 0 | 0 | 0
20180807_1243_50 | 41102.56 | 0 | 0 | 64.9 | 547.15 | 612.05 | 0 | 0 | 0 | 0 | 0
20180807_1243_50 | 41153.94 | 0 | 0 | 64.88 | 547.13 | 612.01 | 0 | 0 | 0 | 0 | 0
20180807_1243_50 | 41205.38 | 0 | 0 | 64.87 | 547.136666666667 | 612.006666666667 | 0 | 0 | 0 | 0 | 0
20180807_1243_50 | 41256.89 | 0 | 0 | 64.86 | 547.14 | 612 | 0 | 0 | 0 | 0 | 0
20180807_1243_50 | 41308.46 | 0 | 0 | 64.8733333333333 | 547.11 | 611.983333333333 | 0 | 0 | 0 | 0 | 0
20180807_1243_51 | 41360.1 | 0 | 0 | 64.88 | 547.123333333333 | 612.003333333333 | 0 | 0 | 0 | 0 | 0
20180807_1243_51 | 41411.8 | 0 | 0 | 64.88 | 547.13 | 612.01 | 0 | 0 | 0 | 0 | 0
20180807_1243_51 | 41463.56 | 0 | 0 | 64.85 | 547.13 | 611.98 | 0 | 0 | 0 | 0 | 0
20180807_1243_51 | 41515.39 | 0 | 0 | 64.85 | 547.11 | 611.96 | 0 | 0 | 0 | 0 | 0
20180807_1243_51 | 41567.28 | 0 | 0 | 64.86 | 547.11 | 611.97 | 0 | 0 | 0 | 0 | 0
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
