andrasfuchs/BioBalanceDetector/Measurements/Spooky2/99_OtherScans/Spooky2.20180805/ScanData/Disconnected/GeneratorX_G1_41kHzTo18MHz_DropletElectrode_FilteredWater/BFB_20180807_1102_41.csv

Date_Time | Frequency | BPM | HRV | Angle | Current | Angle + Current | Spare | Spare | Spare | Spare | Spare
20180807_1102_56 | 41000 | 0 | 0 | 64.93 | 546.32 | 611.25 | 0 | 0 | 0 | 0 | 0
20180807_1102_56 | 41051.25 | 0 | 0 | 64.93 | 546.29 | 611.22 | 0 | 0 | 0 | 0 | 0
20180807_1102_57 | 41102.56 | 0 | 0 | 64.93 | 546.296666666667 | 611.226666666667 | 0 | 0 | 0 | 0 | 0
20180807_1102_57 | 41153.94 | 0 | 0 | 64.93 | 546.296666666667 | 611.226666666667 | 0 | 0 | 0 | 0 | 0
20180807_1102_57 | 41205.38 | 0 | 0 | 64.93 | 546.29 | 611.22 | 0 | 0 | 0 | 0 | 0
20180807_1102_57 | 41256.89 | 0 | 0 | 64.93 | 546.31 | 611.24 | 0 | 0 | 0 | 0 | 0
20180807_1102_57 | 41308.46 | 0 | 0 | 64.93 | 546.32 | 611.25 | 0 | 0 | 0 | 0 | 0
20180807_1102_57 | 41360.1 | 0 | 0 | 64.93 | 546.29 | 611.22 | 0 | 0 | 0 | 0 | 0
20180807_1102_58 | 41411.8 | 0 | 0 | 64.93 | 546.296666666667 | 611.226666666667 | 0 | 0 | 0 | 0 | 0
20180807_1102_58 | 41463.56 | 0 | 0 | 64.93 | 546.3 | 611.23 | 0 | 0 | 0 | 0 | 0
20180807_1102_58 | 41515.39 | 0 | 0 | 64.93 | 546.28 | 611.21 | 0 | 0 | 0 | 0 | 0
20180807_1102_58 | 41567.28 | 0 | 0 | 64.93 | 546.3 | 611.23 | 0 | 0 | 0 | 0 | 0
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
