andrasfuchs/BioBalanceDetector/Measurements/Spooky2/99_OtherScans/Spooky2.20180805/ScanData/Disconnected/GeneratorX_G1_41kHzTo18MHz_DropletElectrode_None/BFB_20180807_1024_41.csv

Date_Time | Frequency | BPM | HRV | Angle | Current | Angle + Current | Spare | Spare | Spare | Spare | Spare
20180807_1024_58 | 41000 | 0 | 0 | 64.3 | 546.3 | 610.6 | 0 | 0 | 0 | 0 | 0
20180807_1024_58 | 41051.25 | 0 | 0 | 64.3 | 546.3 | 610.6 | 0 | 0 | 0 | 0 | 0
20180807_1024_59 | 41102.56 | 0 | 0 | 64.3 | 546.3 | 610.6 | 0 | 0 | 0 | 0 | 0
20180807_1024_59 | 41153.94 | 0 | 0 | 64.3 | 546.3 | 610.6 | 0 | 0 | 0 | 0 | 0
20180807_1024_59 | 41205.38 | 0 | 0 | 64.3 | 546.3 | 610.6 | 0 | 0 | 0 | 0 | 0
20180807_1024_59 | 41256.89 | 0 | 0 | 64.3 | 546.3 | 610.6 | 0 | 0 | 0 | 0 | 0
20180807_1024_59 | 41308.46 | 0 | 0 | 64.3 | 546.3 | 610.6 | 0 | 0 | 0 | 0 | 0
20180807_1024_59 | 41360.1 | 0 | 0 | 64.3 | 546.3 | 610.6 | 0 | 0 | 0 | 0 | 0
20180807_1024_59 | 41411.8 | 0 | 0 | 64.3 | 546.3 | 610.6 | 0 | 0 | 0 | 0 | 0
20180807_1025_00 | 41463.56 | 0 | 0 | 64.3 | 546.3 | 610.6 | 0 | 0 | 0 | 0 | 0
20180807_1025_00 | 41515.39 | 0 | 0 | 64.3 | 546.3 | 610.6 | 0 | 0 | 0 | 0 | 0
20180807_1025_00 | 41567.28 | 0 | 0 | 64.3 | 546.3 | 610.6 | 0 | 0 | 0 | 0 | 0
20180807_1025_00 | 41619.24 | 0 | 0 | 64.3 | 546.3 | 610.6 | 0 | 0 | 0 | 0 | 0
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
