andrasfuchs/BioBalanceDetector/Measurements/Spooky2/99_OtherScans/Spooky2.20180805/ScanData/Disconnected/GeneratorX_G1_41kHzTo18MHz_DropletElectrode_None/BFB_20180807_1449_35.csv

Date_Time | Frequency | BPM | HRV | Angle | Current | Angle + Current | Spare | Spare | Spare | Spare | Spare
20180807_1449_47 | 41000 | 0 | 0 | 638.583333333333 | 395.76 | 1034.34333333333 | 0 | 0 | 0 | 0 | 0
20180807_1449_47 | 41051.25 | 0 | 0 | 638.583333333333 | 395.75 | 1034.33333333333 | 0 | 0 | 0 | 0 | 0
20180807_1449_47 | 41102.56 | 0 | 0 | 638.57 | 395.746666666667 | 1034.31666666667 | 0 | 0 | 0 | 0 | 0
20180807_1449_47 | 41153.94 | 0 | 0 | 638.55 | 395.74 | 1034.29 | 0 | 0 | 0 | 0 | 0
20180807_1449_48 | 41205.38 | 0 | 0 | 638.556666666667 | 395.746666666667 | 1034.30333333333 | 0 | 0 | 0 | 0 | 0
20180807_1449_48 | 41256.89 | 0 | 0 | 638.57 | 395.746666666667 | 1034.31666666667 | 0 | 0 | 0 | 0 | 0
20180807_1449_48 | 41308.46 | 0 | 0 | 638.55 | 395.74 | 1034.29 | 0 | 0 | 0 | 0 | 0
20180807_1449_48 | 41360.1 | 0 | 0 | 638.55 | 395.74 | 1034.29 | 0 | 0 | 0 | 0 | 0
20180807_1449_48 | 41411.8 | 0 | 0 | 638.55 | 395.74 | 1034.29 | 0 | 0 | 0 | 0 | 0
20180807_1449_48 | 41463.56 | 0 | 0 | 638.6 | 395.77 | 1034.37 | 0 | 0 | 0 | 0 | 0
20180807_1449_48 | 41515.39 | 0 | 0 | 638.593333333333 | 395.76 | 1034.35333333333 | 0 | 0 | 0 | 0 | 0
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
