andrasfuchs/BioBalanceDetector/Measurements/Spooky2/99_OtherScans/Spooky2.20180805/ScanData/Disconnected/GeneratorX_G1_41kHzTo18MHz_DropletElectrode_RiceMilk/BFB_20180807_1502_32.csv

Date_Time | Frequency | BPM | HRV | Angle | Current | Angle + Current | Spare | Spare | Spare | Spare | Spare
20180807_1502_44 | 41000 | 0 | 0 | 638.583333333333 | 396.39 | 1034.97333333333 | 0 | 0 | 0 | 0 | 0
20180807_1502_44 | 41051.25 | 0 | 0 | 638.6 | 396.383333333333 | 1034.98333333333 | 0 | 0 | 0 | 0 | 0
20180807_1502_45 | 41102.56 | 0 | 0 | 638.59 | 396.37 | 1034.96 | 0 | 0 | 0 | 0 | 0
20180807_1502_45 | 41153.94 | 0 | 0 | 638.53 | 396.35 | 1034.88 | 0 | 0 | 0 | 0 | 0
20180807_1502_45 | 41205.38 | 0 | 0 | 638.53 | 396.31 | 1034.84 | 0 | 0 | 0 | 0 | 0
20180807_1502_45 | 41256.89 | 0 | 0 | 638.43 | 396.29 | 1034.72 | 0 | 0 | 0 | 0 | 0
20180807_1502_45 | 41308.46 | 0 | 0 | 638.51 | 396.36 | 1034.87 | 0 | 0 | 0 | 0 | 0
20180807_1502_45 | 41360.1 | 0 | 0 | 638.556666666667 | 396.366666666667 | 1034.92333333333 | 0 | 0 | 0 | 0 | 0
20180807_1502_45 | 41411.8 | 0 | 0 | 638.57 | 396.37 | 1034.94 | 0 | 0 | 0 | 0 | 0
20180807_1502_46 | 41463.56 | 0 | 0 | 638.583333333333 | 396.38 | 1034.96333333333 | 0 | 0 | 0 | 0 | 0
20180807_1502_46 | 41515.39 | 0 | 0 | 638.59 | 396.38 | 1034.97 | 0 | 0 | 0 | 0 | 0
20180807_1502_46 | 41567.28 | 0 | 0 | 638.59 | 396.36 | 1034.95 | 0 | 0 | 0 | 0 | 0
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
