andrasfuchs/BioBalanceDetector/Measurements/Spooky2/99_OtherScans/Spooky2.20180805/ScanData/Disconnected/GeneratorX_G1_41kHzTo18MHz_DropletElectrode_RiceMilk/BFB_20180807_1629_21.csv

Date_Time | Frequency | BPM | HRV | Angle | Current | Angle + Current | Spare | Spare | Spare | Spare | Spare
20180807_1629_34 | 41000 | 0 | 0 | 638.71 | 395.85 | 1034.56 | 0 | 0 | 0 | 0 | 0
20180807_1629_34 | 41051.25 | 0 | 0 | 638.71 | 395.92 | 1034.63 | 0 | 0 | 0 | 0 | 0
20180807_1629_34 | 41102.56 | 0 | 0 | 638.71 | 395.903333333333 | 1034.61333333333 | 0 | 0 | 0 | 0 | 0
20180807_1629_34 | 41153.94 | 0 | 0 | 638.71 | 395.87 | 1034.58 | 0 | 0 | 0 | 0 | 0
20180807_1629_34 | 41205.38 | 0 | 0 | 638.703333333333 | 395.9 | 1034.60333333333 | 0 | 0 | 0 | 0 | 0
20180807_1629_34 | 41256.89 | 0 | 0 | 638.69 | 395.886666666667 | 1034.57666666667 | 0 | 0 | 0 | 0 | 0
20180807_1629_35 | 41308.46 | 0 | 0 | 638.703333333333 | 395.86 | 1034.56333333333 | 0 | 0 | 0 | 0 | 0
20180807_1629_35 | 41360.1 | 0 | 0 | 638.71 | 395.866666666667 | 1034.57666666667 | 0 | 0 | 0 | 0 | 0
20180807_1629_35 | 41411.8 | 0 | 0 | 638.71 | 395.896666666667 | 1034.60666666667 | 0 | 0 | 0 | 0 | 0
20180807_1629_35 | 41463.56 | 0 | 0 | 638.71 | 395.95 | 1034.66 | 0 | 0 | 0 | 0 | 0
20180807_1629_35 | 41515.39 | 0 | 0 | 638.71 | 395.86 | 1034.57 | 0 | 0 | 0 | 0 | 0
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
