andrasfuchs/BioBalanceDetector/Measurements/Spooky2/99_OtherScans/Spooky2.20180805/ScanData/Disconnected/GeneratorX_G1_41kHzTo18MHz_DropletElectrode_RiceMilk/BFB_20180807_1642_20.csv

Date_Time | Frequency | BPM | HRV | Angle | Current | Angle + Current | Spare | Spare | Spare | Spare | Spare
20180807_1642_32 | 41000 | 0 | 0 | 638.71 | 395.85 | 1034.56 | 0 | 0 | 0 | 0 | 0
20180807_1642_32 | 41051.25 | 0 | 0 | 638.71 | 395.85 | 1034.56 | 0 | 0 | 0 | 0 | 0
20180807_1642_32 | 41102.56 | 0 | 0 | 638.71 | 395.85 | 1034.56 | 0 | 0 | 0 | 0 | 0
20180807_1642_33 | 41153.94 | 0 | 0 | 638.71 | 395.87 | 1034.58 | 0 | 0 | 0 | 0 | 0
20180807_1642_33 | 41205.38 | 0 | 0 | 638.71 | 395.85 | 1034.56 | 0 | 0 | 0 | 0 | 0
20180807_1642_33 | 41256.89 | 0 | 0 | 638.71 | 395.876666666667 | 1034.58666666667 | 0 | 0 | 0 | 0 | 0
20180807_1642_33 | 41308.46 | 0 | 0 | 638.71 | 395.89 | 1034.6 | 0 | 0 | 0 | 0 | 0
20180807_1642_33 | 41360.1 | 0 | 0 | 638.71 | 395.876666666667 | 1034.58666666667 | 0 | 0 | 0 | 0 | 0
20180807_1642_33 | 41411.8 | 0 | 0 | 638.71 | 395.903333333333 | 1034.61333333333 | 0 | 0 | 0 | 0 | 0
20180807_1642_33 | 41463.56 | 0 | 0 | 638.71 | 395.97 | 1034.68 | 0 | 0 | 0 | 0 | 0
20180807_1642_34 | 41515.39 | 0 | 0 | 638.71 | 395.86 | 1034.57 | 0 | 0 | 0 | 0 | 0
20180807_1642_34 | 41567.28 | 0 | 0 | 638.71 | 395.86 | 1034.57 | 0 | 0 | 0 | 0 | 0
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
