andrasfuchs/BioBalanceDetector/Measurements/Spooky2/99_OtherScans/Spooky2.20180805/ScanData/Disconnected/GeneratorX_G1_41kHzTo18MHz_DropletElectrode_Saliva/BFB_20180807_1132_10.csv

Date_Time | Frequency | BPM | HRV | Angle | Current | Angle + Current | Spare | Spare | Spare | Spare | Spare
20180807_1132_25 | 41000 | 0 | 0 | 64.35 | 546.96 | 611.31 | 0 | 0 | 0 | 0 | 0
20180807_1132_25 | 41051.25 | 0 | 0 | 64.35 | 546.96 | 611.31 | 0 | 0 | 0 | 0 | 0
20180807_1132_25 | 41102.56 | 0 | 0 | 64.35 | 546.96 | 611.31 | 0 | 0 | 0 | 0 | 0
20180807_1132_25 | 41153.94 | 0 | 0 | 64.35 | 546.963333333333 | 611.313333333333 | 0 | 0 | 0 | 0 | 0
20180807_1132_25 | 41205.38 | 0 | 0 | 64.3566666666667 | 546.97 | 611.326666666667 | 0 | 0 | 0 | 0 | 0
20180807_1132_25 | 41256.89 | 0 | 0 | 64.3533333333333 | 546.97 | 611.323333333333 | 0 | 0 | 0 | 0 | 0
20180807_1132_26 | 41308.46 | 0 | 0 | 64.34 | 546.97 | 611.31 | 0 | 0 | 0 | 0 | 0
20180807_1132_26 | 41360.1 | 0 | 0 | 64.35 | 546.97 | 611.32 | 0 | 0 | 0 | 0 | 0
20180807_1132_26 | 41411.8 | 0 | 0 | 64.35 | 546.96 | 611.31 | 0 | 0 | 0 | 0 | 0
20180807_1132_26 | 41463.56 | 0 | 0 | 64.35 | 546.963333333333 | 611.313333333333 | 0 | 0 | 0 | 0 | 0
20180807_1132_26 | 41515.39 | 0 | 0 | 64.34 | 546.97 | 611.31 | 0 | 0 | 0 | 0 | 0
20180807_1132_26 | 41567.28 | 0 | 0 | 64.3366666666667 | 546.99 | 611.326666666667 | 0 | 0 | 0 | 0 | 0
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
