andrasfuchs/BioBalanceDetector/Measurements/Spooky2/99_OtherScans/Spooky2.20180503/ScanData/Connected/Andras_Fuchs_1981/TENSPadsLeftRightTorso/Nonstandard/BFB_20180424_0914_05_TENSPadsLeftRightTorso_BioCleanse_9nap.csv

Date_Time | Frequency | BPM | HRV | Angle | Current | Angle + Current | Spare | Spare | Spare | Spare | Spare
20180424_0914_21 | 20000 | 0 | 0 | 171.71 | 520.15 | 691.86 | 0 | 0 | 0 | 0 | 0
20180424_0914_21 | 20025 | 0 | 0 | 171.71 | 521.06 | 692.77 | 0 | 0 | 0 | 0 | 0
20180424_0914_21 | 20050.03125 | 0 | 0 | 171.69 | 521.06 | 692.75 | 0 | 0 | 0 | 0 | 0
20180424_0914_21 | 20075.09379 | 0 | 0 | 171.69 | 521.06 | 692.75 | 0 | 0 | 0 | 0 | 0
20180424_0914_21 | 20100.18766 | 0 | 0 | 171.25 | 521.38 | 692.63 | 0 | 0 | 0 | 0 | 0
20180424_0914_21 | 20125.31289 | 0 | 0 | 171.25 | 521.38 | 692.63 | 0 | 0 | 0 | 0 | 0
20180424_0914_22 | 20150.46953 | 0 | 0 | 171.25 | 521.99 | 693.24 | 0 | 0 | 0 | 0 | 0
20180424_0914_22 | 20175.65762 | 0 | 0 | 171.16 | 521.99 | 693.15 | 0 | 0 | 0 | 0 | 0
20180424_0914_22 | 20200.87719 | 0 | 0 | 171.16 | 521.99 | 693.15 | 0 | 0 | 0 | 0 | 0
20180424_0914_22 | 20226.12829 | 0 | 0 | 171.16 | 522.49 | 693.65 | 0 | 0 | 0 | 0 | 0
20180424_0914_22 | 20251.41095 | 0 | 0 | 171.12 | 522.49 | 693.61 | 0 | 0 | 0 | 0 | 0
20180424_0914_22 | 20276.72521 | 0 | 0 | 171.12 | 522.7 | 693.82 | 0 | 0 | 0 | 0 | 0
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
