andrasfuchs/BioBalanceDetector/Measurements/Spooky2/99_OtherScans/Spooky2.20180301/ScanData/Andras_Fuchs_1981/BFB_20180427_0855_04_TENSPadsLeftRightTorso_3samples_4HoursSleep_LittleBreakfast.csv

Date_Time | Frequency | BPM | HRV | Angle | Current | Angle + Current | Spare | Spare | Spare | Spare | Spare
20180427_0855_19 | 41000 | 0 | 0 | 130.416666666667 | 534.136666666667 | 664.553333333333 | 0 | 0 | 0 | 0 | 0
20180427_0855_19 | 41051.25 | 0 | 0 | 130.423333333333 | 534.193333333333 | 664.616666666667 | 0 | 0 | 0 | 0 | 0
20180427_0855_20 | 41102.56 | 0 | 0 | 130.43 | 534.183333333333 | 664.613333333333 | 0 | 0 | 0 | 0 | 0
20180427_0855_20 | 41153.94 | 0 | 0 | 130.41 | 534.156666666667 | 664.566666666667 | 0 | 0 | 0 | 0 | 0
20180427_0855_20 | 41205.38 | 0 | 0 | 130.43 | 534.193333333333 | 664.623333333333 | 0 | 0 | 0 | 0 | 0
20180427_0855_20 | 41256.89 | 0 | 0 | 130.42 | 534.16 | 664.58 | 0 | 0 | 0 | 0 | 0
20180427_0855_20 | 41308.46 | 0 | 0 | 130.413333333333 | 534.11 | 664.523333333333 | 0 | 0 | 0 | 0 | 0
20180427_0855_21 | 41360.1 | 0 | 0 | 130.416666666667 | 534.18 | 664.596666666667 | 0 | 0 | 0 | 0 | 0
20180427_0855_21 | 41411.8 | 0 | 0 | 130.42 | 534.17 | 664.59 | 0 | 0 | 0 | 0 | 0
20180427_0855_21 | 41463.56 | 0 | 0 | 130.413333333333 | 534.176666666667 | 664.59 | 0 | 0 | 0 | 0 | 0
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
