andrasfuchs/BioBalanceDetector/Measurements/Spooky2/99_OtherScans/Spooky2.20180503/ScanData/Connected/Andras_Fuchs_1981/TENSPadsLeftRightTorso/Nonstandard/BFB_20180505_0756_00_TENSPadsLeftRightTorso_LowCurrent.csv

Date_Time | Frequency | BPM | HRV | Angle | Current | Angle + Current | Spare | Spare | Spare | Spare | Spare
20180505_0756_15 | 41000 | 0 | 0 | 71.79 | 515.12 | 586.91 | 0 | 0 | 0 | 0 | 0
20180505_0756_15 | 41051.25 | 0 | 0 | 71.79 | 515.12 | 586.91 | 0 | 0 | 0 | 0 | 0
20180505_0756_15 | 41102.56 | 0 | 0 | 71.79 | 515.14 | 586.93 | 0 | 0 | 0 | 0 | 0
20180505_0756_15 | 41153.94 | 0 | 0 | 71.7 | 515.14 | 586.84 | 0 | 0 | 0 | 0 | 0
20180505_0756_15 | 41205.38 | 0 | 0 | 71.7 | 515.14 | 586.84 | 0 | 0 | 0 | 0 | 0
20180505_0756_15 | 41256.89 | 0 | 0 | 71.7 | 515.13 | 586.83 | 0 | 0 | 0 | 0 | 0
20180505_0756_15 | 41308.46 | 0 | 0 | 71.69 | 515.13 | 586.82 | 0 | 0 | 0 | 0 | 0
20180505_0756_15 | 41360.1 | 0 | 0 | 71.69 | 515.13 | 586.82 | 0 | 0 | 0 | 0 | 0
20180505_0756_15 | 41411.8 | 0 | 0 | 71.69 | 515.16 | 586.85 | 0 | 0 | 0 | 0 | 0
20180505_0756_15 | 41463.56 | 0 | 0 | 71.68 | 515.16 | 586.84 | 0 | 0 | 0 | 0 | 0
20180505_0756_15 | 41515.39 | 0 | 0 | 71.68 | 515.16 | 586.84 | 0 | 0 | 0 | 0 | 0
20180505_0756_16 | 41567.28 | 0 | 0 | 71.68 | 515.27 | 586.95 | 0 | 0 | 0 | 0 | 0
20180505_0756_16 | 41619.24 | 0 | 0 | 71.5 | 515.27 | 586.77 | 0 | 0 | 0 | 0 | 0
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
