andrasfuchs/BioBalanceDetector/Measurements/Spooky2/99_OtherScans/Spooky2.20180301/ScanData/Andras_Fuchs_1981/BFB_20180425_0817_07_TENSPadsLeftRightTorso.csv

Date_Time | Frequency | BPM | HRV | Angle | Current | Angle + Current | Spare | Spare | Spare | Spare | Spare
20180425_0817_31 | 41000 | 0 | 0 | 141.1 | 532.17 | 673.27 | 0 | 0 | 0 | 0 | 0
20180425_0817_31 | 41051.25 | 0 | 0 | 141.1 | 532.17 | 673.27 | 0 | 0 | 0 | 0 | 0
20180425_0817_32 | 41102.56 | 0 | 0 | 141.1 | 532.22 | 673.32 | 0 | 0 | 0 | 0 | 0
20180425_0817_32 | 41153.94 | 0 | 0 | 141.2 | 532.22 | 673.42 | 0 | 0 | 0 | 0 | 0
20180425_0817_32 | 41205.38 | 0 | 0 | 141.2 | 532.22 | 673.42 | 0 | 0 | 0 | 0 | 0
20180425_0817_32 | 41256.89 | 0 | 0 | 141.2 | 532.27 | 673.47 | 0 | 0 | 0 | 0 | 0
20180425_0817_32 | 41308.46 | 0 | 0 | 140.89 | 532.27 | 673.16 | 0 | 0 | 0 | 0 | 0
20180425_0817_32 | 41360.1 | 0 | 0 | 140.89 | 532.27 | 673.16 | 0 | 0 | 0 | 0 | 0
20180425_0817_32 | 41411.8 | 0 | 0 | 140.89 | 532.3 | 673.19 | 0 | 0 | 0 | 0 | 0
20180425_0817_32 | 41463.56 | 0 | 0 | 140.76 | 532.3 | 673.06 | 0 | 0 | 0 | 0 | 0
20180425_0817_32 | 41515.39 | 0 | 0 | 140.76 | 532.3 | 673.06 | 0 | 0 | 0 | 0 | 0
20180425_0817_32 | 41567.28 | 0 | 0 | 140.76 | 532.19 | 672.95 | 0 | 0 | 0 | 0 | 0
20180425_0817_32 | 41619.24 | 0 | 0 | 140.67 | 532.19 | 672.86 | 0 | 0 | 0 | 0 | 0
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
