andrasfuchs/BioBalanceDetector/Measurements/Spooky2/99_OtherScans/Spooky2.20180301/ScanData/Andras_Fuchs_1981/BFB_20180425_0828_20_HandCyclinders.csv

Date_Time | Frequency | BPM | HRV | Angle | Current | Angle + Current | Spare | Spare | Spare | Spare | Spare
20180425_0828_35 | 41000 | 0 | 0 | 72.34 | 517.63 | 589.97 | 0 | 0 | 0 | 0 | 0
20180425_0828_35 | 41051.25 | 0 | 0 | 72.34 | 517.63 | 589.97 | 0 | 0 | 0 | 0 | 0
20180425_0828_35 | 41102.56 | 0 | 0 | 72.34 | 517.63 | 589.97 | 0 | 0 | 0 | 0 | 0
20180425_0828_35 | 41153.94 | 0 | 0 | 72.34 | 517.57 | 589.91 | 0 | 0 | 0 | 0 | 0
20180425_0828_35 | 41205.38 | 0 | 0 | 72.33 | 517.57 | 589.9 | 0 | 0 | 0 | 0 | 0
20180425_0828_35 | 41256.89 | 0 | 0 | 72.33 | 517.57 | 589.9 | 0 | 0 | 0 | 0 | 0
20180425_0828_35 | 41308.46 | 0 | 0 | 72.33 | 517.54 | 589.87 | 0 | 0 | 0 | 0 | 0
20180425_0828_35 | 41360.1 | 0 | 0 | 72.32 | 517.54 | 589.86 | 0 | 0 | 0 | 0 | 0
20180425_0828_35 | 41411.8 | 0 | 0 | 72.32 | 517.54 | 589.86 | 0 | 0 | 0 | 0 | 0
20180425_0828_35 | 41463.56 | 0 | 0 | 72.32 | 517.56 | 589.88 | 0 | 0 | 0 | 0 | 0
20180425_0828_36 | 41515.39 | 0 | 0 | 72.32 | 517.56 | 589.88 | 0 | 0 | 0 | 0 | 0
20180425_0828_36 | 41567.28 | 0 | 0 | 72.32 | 517.56 | 589.88 | 0 | 0 | 0 | 0 | 0
20180425_0828_36 | 41619.24 | 0 | 0 | 72.32 | 517.56 | 589.88 | 0 | 0 | 0 | 0 | 0
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
