andrasfuchs/BioBalanceDetector/Measurements/Spooky2/99_OtherScans/Spooky2.20180301/ScanData/Andras_Fuchs_1981/BFB_20180426_0757_23_TENSPadsLeftRightTorso.csv

Date_Time | Frequency | BPM | HRV | Angle | Current | Angle + Current | Spare | Spare | Spare | Spare | Spare
20180426_0757_48 | 41000 | 0 | 0 | 155.53 | 532.09 | 687.62 | 0 | 0 | 0 | 0 | 0
20180426_0757_48 | 41051.25 | 0 | 0 | 155.53 | 532.12 | 687.65 | 0 | 0 | 0 | 0 | 0
20180426_0757_48 | 41102.56 | 0 | 0 | 155.04 | 532.12 | 687.16 | 0 | 0 | 0 | 0 | 0
20180426_0757_48 | 41153.94 | 0 | 0 | 155.04 | 532.12 | 687.16 | 0 | 0 | 0 | 0 | 0
20180426_0757_48 | 41205.38 | 0 | 0 | 155.04 | 532.13 | 687.17 | 0 | 0 | 0 | 0 | 0
20180426_0757_48 | 41256.89 | 0 | 0 | 154.97 | 532.13 | 687.1 | 0 | 0 | 0 | 0 | 0
20180426_0757_48 | 41308.46 | 0 | 0 | 154.97 | 532.13 | 687.1 | 0 | 0 | 0 | 0 | 0
20180426_0757_48 | 41360.1 | 0 | 0 | 154.97 | 532.07 | 687.04 | 0 | 0 | 0 | 0 | 0
20180426_0757_48 | 41411.8 | 0 | 0 | 154.95 | 532.07 | 687.02 | 0 | 0 | 0 | 0 | 0
20180426_0757_48 | 41463.56 | 0 | 0 | 154.95 | 532.07 | 687.02 | 0 | 0 | 0 | 0 | 0
20180426_0757_48 | 41515.39 | 0 | 0 | 154.95 | 532.1 | 687.05 | 0 | 0 | 0 | 0 | 0
20180426_0757_48 | 41567.28 | 0 | 0 | 154.96 | 532.1 | 687.06 | 0 | 0 | 0 | 0 | 0
20180426_0757_49 | 41619.24 | 0 | 0 | 154.96 | 532.1 | 687.06 | 0 | 0 | 0 | 0 | 0
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
