andrasfuchs/BioBalanceDetector/Measurements/Spooky2/99_OtherScans/Spooky2.20180301/ScanData/Andras_Fuchs_1981/BFB_20180427_0830_22_TENSPadsLeftRightTorso_2samples_4HoursSleep_BeforeBreakfast.csv

Date_Time | Frequency | BPM | HRV | Angle | Current | Angle + Current | Spare | Spare | Spare | Spare | Spare
20180427_0830_37 | 41000 | 0 | 0 | 138.36 | 534.76 | 673.12 | 0 | 0 | 0 | 0 | 0
20180427_0830_37 | 41051.25 | 0 | 0 | 138.36 | 534.76 | 673.12 | 0 | 0 | 0 | 0 | 0
20180427_0830_37 | 41102.56 | 0 | 0 | 138.36 | 534.75 | 673.11 | 0 | 0 | 0 | 0 | 0
20180427_0830_37 | 41153.94 | 0 | 0 | 138.36 | 534.76 | 673.12 | 0 | 0 | 0 | 0 | 0
20180427_0830_38 | 41205.38 | 0 | 0 | 138.38 | 534.77 | 673.15 | 0 | 0 | 0 | 0 | 0
20180427_0830_38 | 41256.89 | 0 | 0 | 138.38 | 534.76 | 673.14 | 0 | 0 | 0 | 0 | 0
20180427_0830_38 | 41308.46 | 0 | 0 | 138.36 | 534.75 | 673.11 | 0 | 0 | 0 | 0 | 0
20180427_0830_38 | 41360.1 | 0 | 0 | 138.36 | 534.77 | 673.13 | 0 | 0 | 0 | 0 | 0
20180427_0830_38 | 41411.8 | 0 | 0 | 138.36 | 534.77 | 673.13 | 0 | 0 | 0 | 0 | 0
20180427_0830_38 | 41463.56 | 0 | 0 | 138.36 | 534.77 | 673.13 | 0 | 0 | 0 | 0 | 0
20180427_0830_38 | 41515.39 | 0 | 0 | 138.36 | 534.75 | 673.11 | 0 | 0 | 0 | 0 | 0
20180427_0830_38 | 41567.28 | 0 | 0 | 138.36 | 534.75 | 673.11 | 0 | 0 | 0 | 0 | 0
20180427_0830_39 | 41619.24 | 0 | 0 | 138.36 | 534.75 | 673.11 | 0 | 0 | 0 | 0 | 0
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
