andrasfuchs/BioBalanceDetector/Measurements/Spooky2/03_HandCylinders/01_GeneratorXAdapterConnectedReferenceTensGloves.png

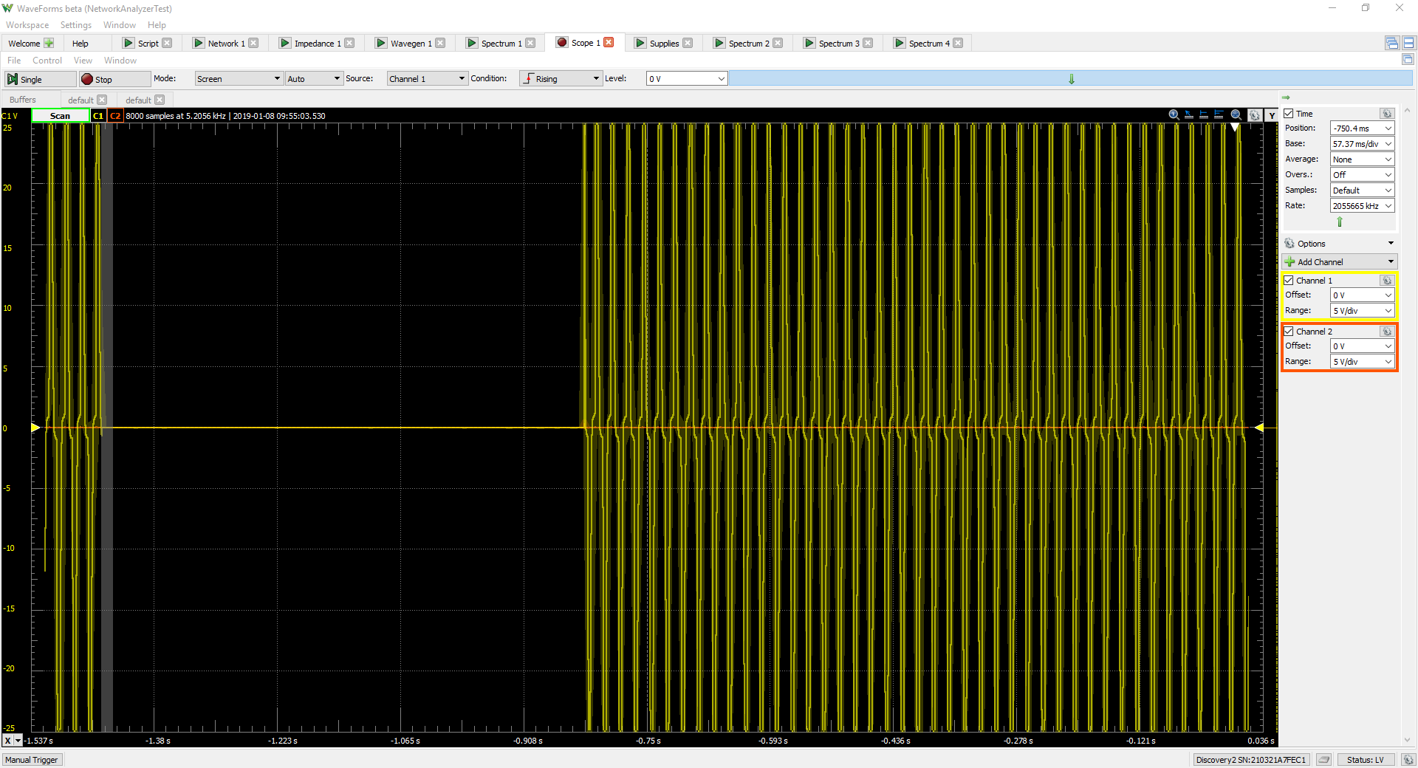
Measurements/Spooky2/03_HandCylinders/01_GeneratorXAdapterConnectedReferenceTensGloves.png
