andrasfuchs/BioBalanceDetector/Measurements/Spooky2/99_OtherScans/Spooky2.20180503/ScanData/Charts/v11/Chart - Noise 2MHz 40Mhz.png

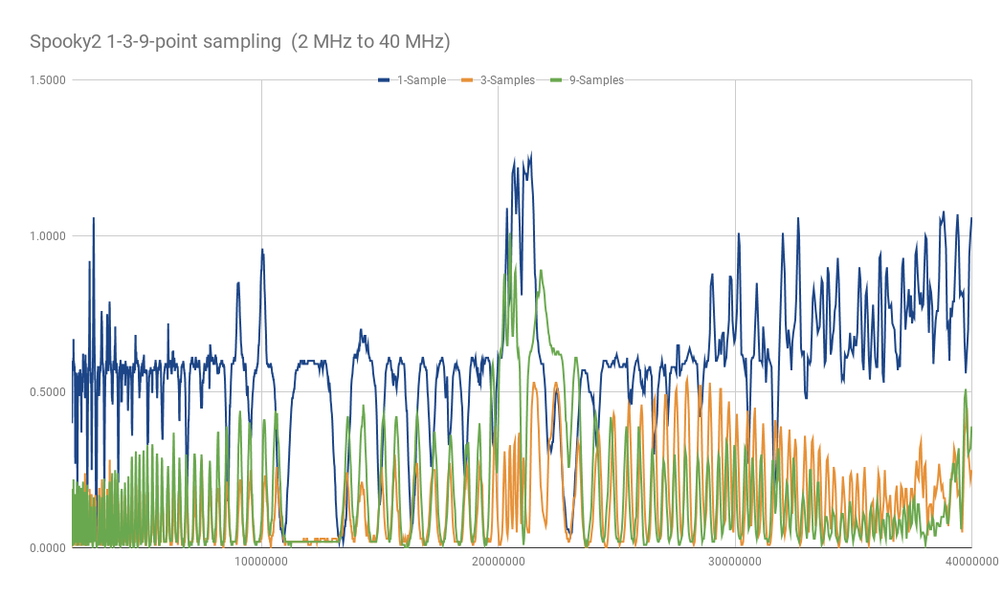
Measurements/Spooky2/99_OtherScans/Spooky2.20180503/ScanData/Charts/v11/Chart - Noise 2MHz 40Mhz.png
