andrasfuchs/BioBalanceDetector/Measurements/Spooky2/99_OtherScans/Spooky2.20180503/ScanData/Charts/v11/Chart - Noise 100kHz 2MHz.png

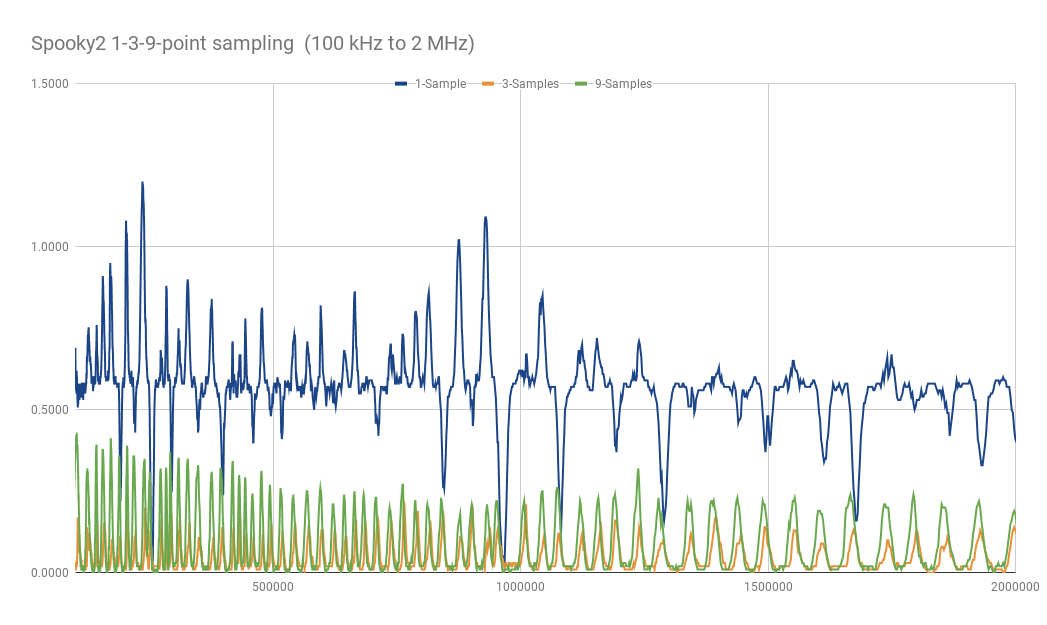
Measurements/Spooky2/99_OtherScans/Spooky2.20180503/ScanData/Charts/v11/Chart - Noise 100kHz 2MHz.png
