andrasfuchs/BioBalanceDetector/Measurements/Spooky2/99_OtherScans/Spooky2.20180805/ScanData/Charts/v13/DropletElectrodes-ScanDEF.png

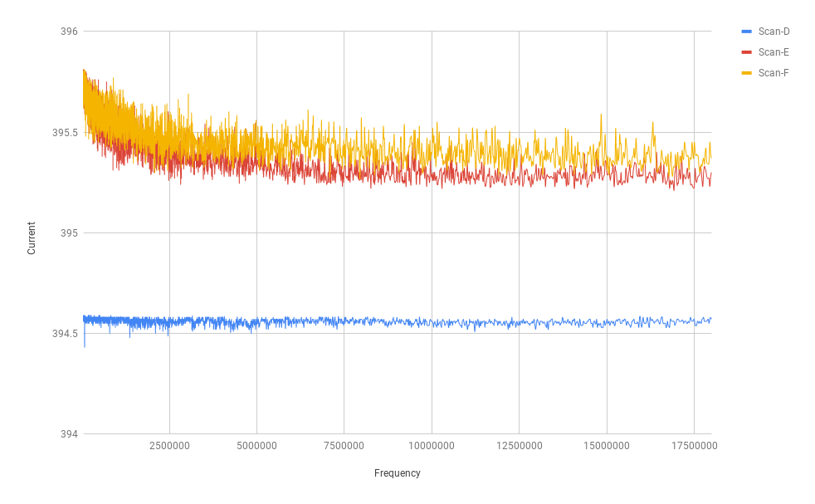
Measurements/Spooky2/99_OtherScans/Spooky2.20180805/ScanData/Charts/v13/DropletElectrodes-ScanDEF.png
