andrasfuchs/BioBalanceDetector/Measurements/Spooky2/99_OtherScans/Spooky2.20180805/ScanData/Disconnected/GeneratorX_G1_1HzTo40MHz/IMG_20180807_082931.jpg

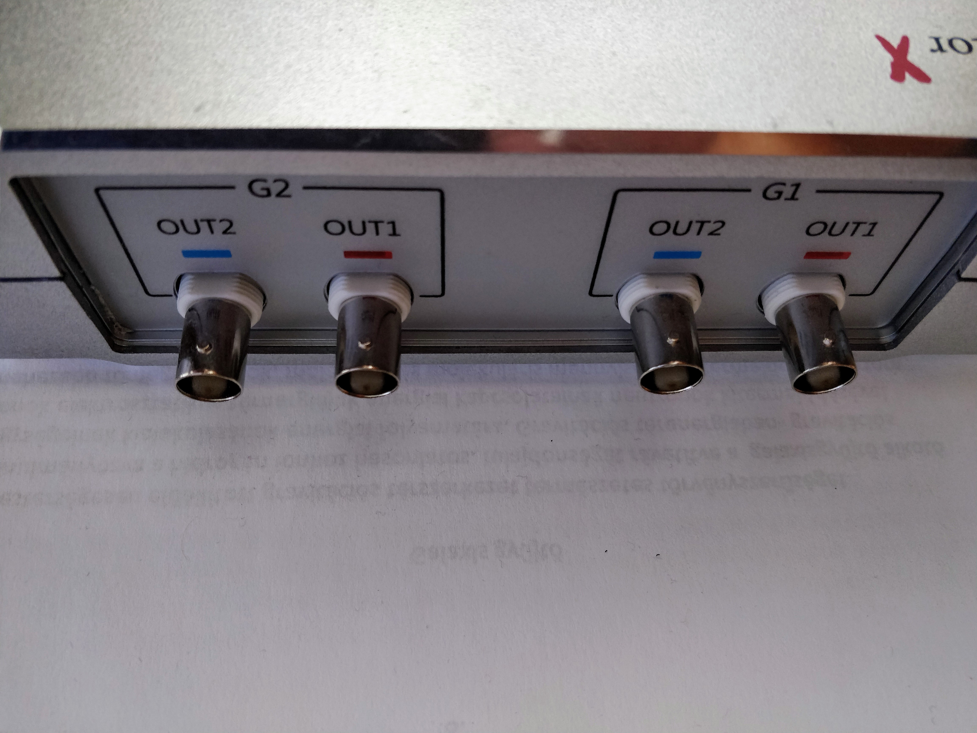
Measurements/Spooky2/99_OtherScans/Spooky2.20180805/ScanData/Disconnected/GeneratorX_G1_1HzTo40MHz/IMG_20180807_082931.jpg
