andrasfuchs/BioBalanceDetector/Measurements/WaveForms/Experiments/AcusticAmplifiedEgelyReactor/02_AcusticAmplifiedReactorT01-InputOutputSignals.png

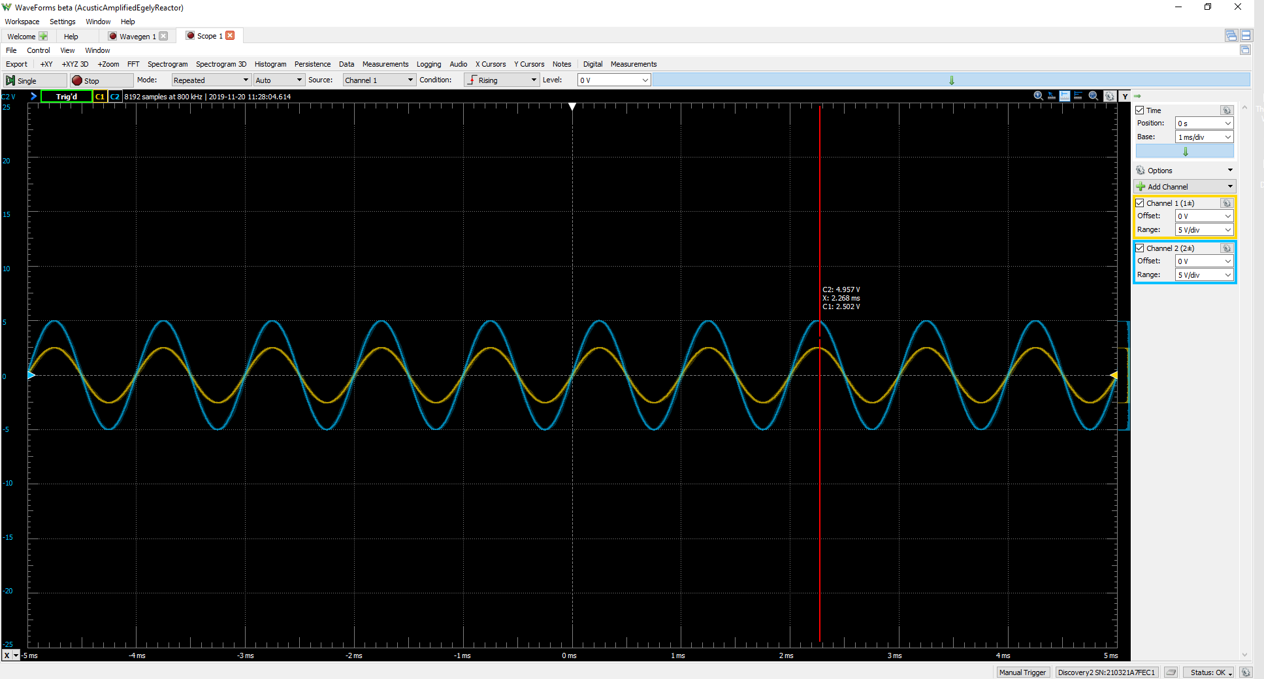
Measurements/WaveForms/Experiments/AcusticAmplifiedEgelyReactor/02_AcusticAmplifiedReactorT01-InputOutputSignals.png
