andrasfuchs/BioBalanceDetector/Measurements/WaveForms/Experiments/AcusticAmplifiedEgelyReactor/03_AcusticAmplifiedReactorT02-InputOutputSignals.png

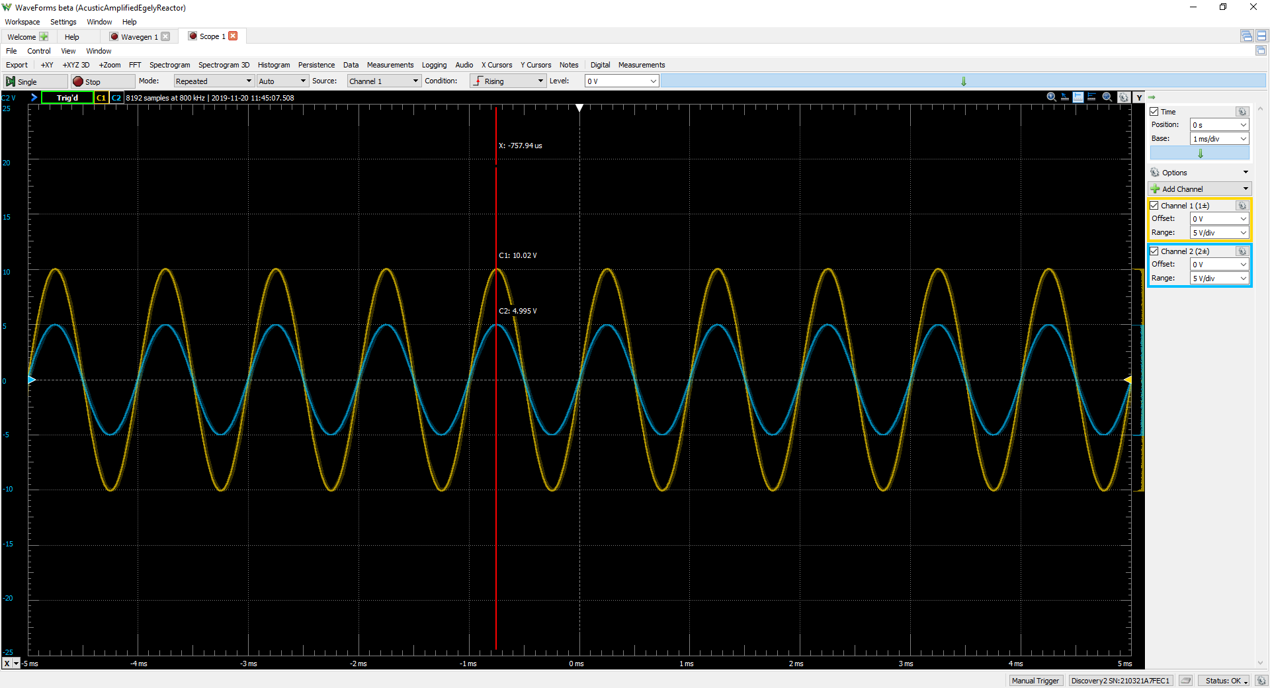
Measurements/WaveForms/Experiments/AcusticAmplifiedEgelyReactor/03_AcusticAmplifiedReactorT02-InputOutputSignals.png
