andrasfuchs/BioBalanceDetector/Measurements/WaveForms/Experiments/AcusticAmplifiedEgelyReactor/04_AcusticAmplifiedReactorT03-InputOutputSignals.png

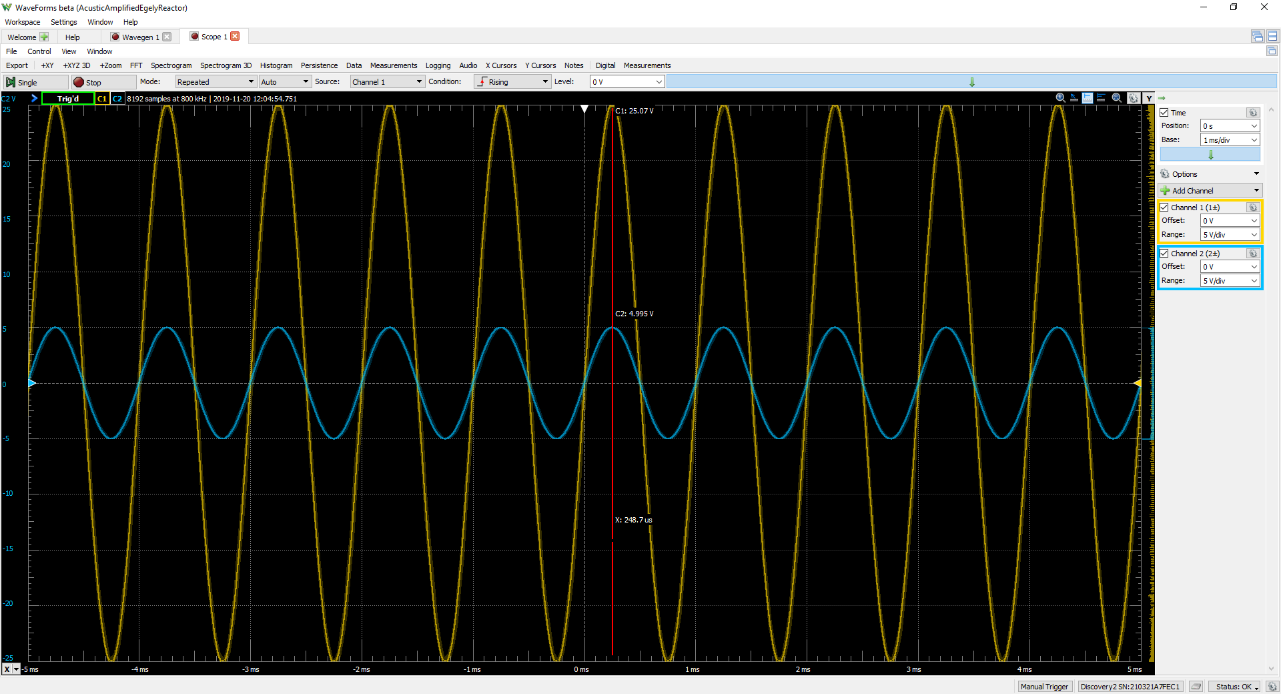
Measurements/WaveForms/Experiments/AcusticAmplifiedEgelyReactor/04_AcusticAmplifiedReactorT03-InputOutputSignals.png
