andrasfuchs/BioBalanceDetector/Measurements/WaveForms/Experiments/AcusticAmplifiedEgelyReactor/06_AcusticAmplifiedReactorT04-InputOutputSignals.png

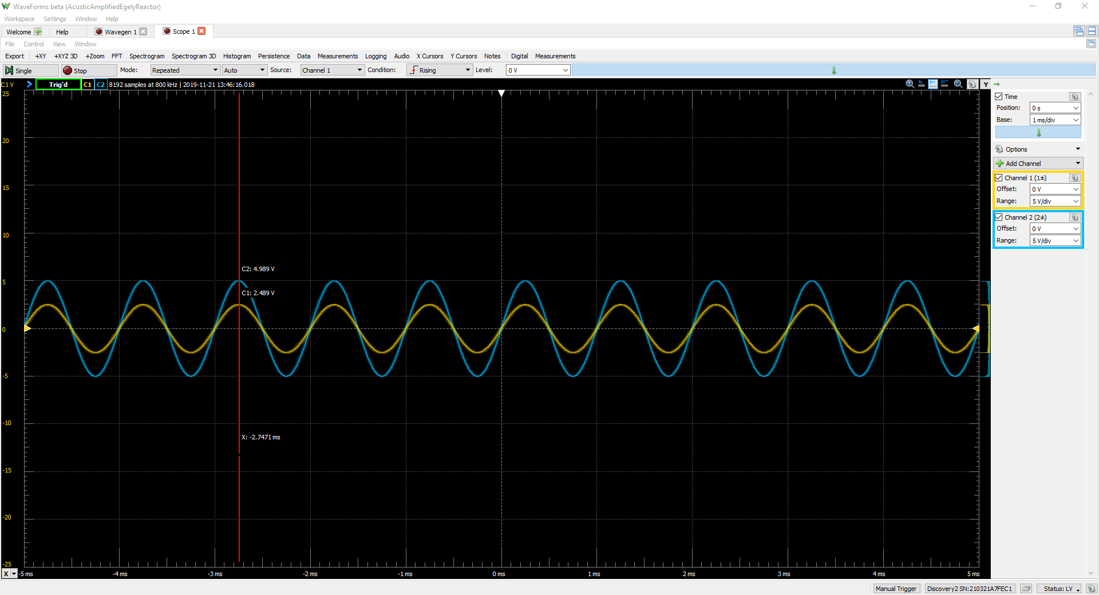
Measurements/WaveForms/Experiments/AcusticAmplifiedEgelyReactor/06_AcusticAmplifiedReactorT04-InputOutputSignals.png
