andrasfuchs/BioBalanceDetector/Measurements/WaveForms/Experiments/AcusticAmplifiedEgelyReactor/07_AcusticAmplifiedReactorT05-InputOutputSignals.png

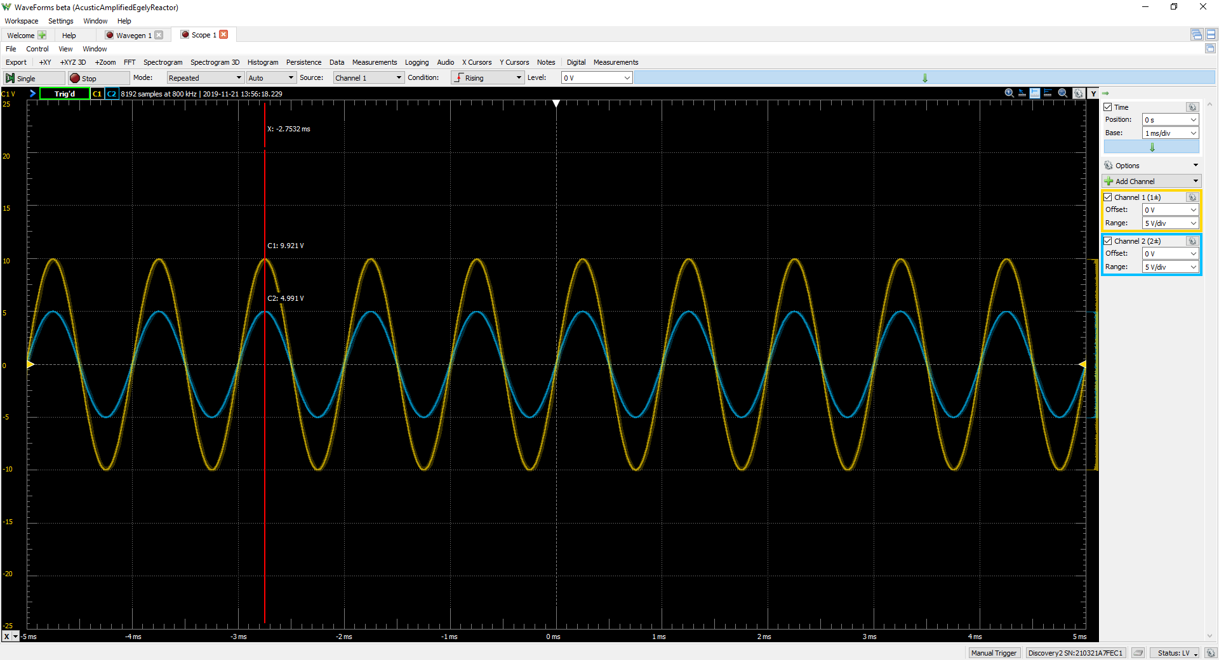
Measurements/WaveForms/Experiments/AcusticAmplifiedEgelyReactor/07_AcusticAmplifiedReactorT05-InputOutputSignals.png
