andrasfuchs/BioBalanceDetector/Measurements/WaveForms/Experiments/AcusticAmplifiedEgelyReactor/08_AcusticAmplifiedReactorT06-InputOutputSignals.png

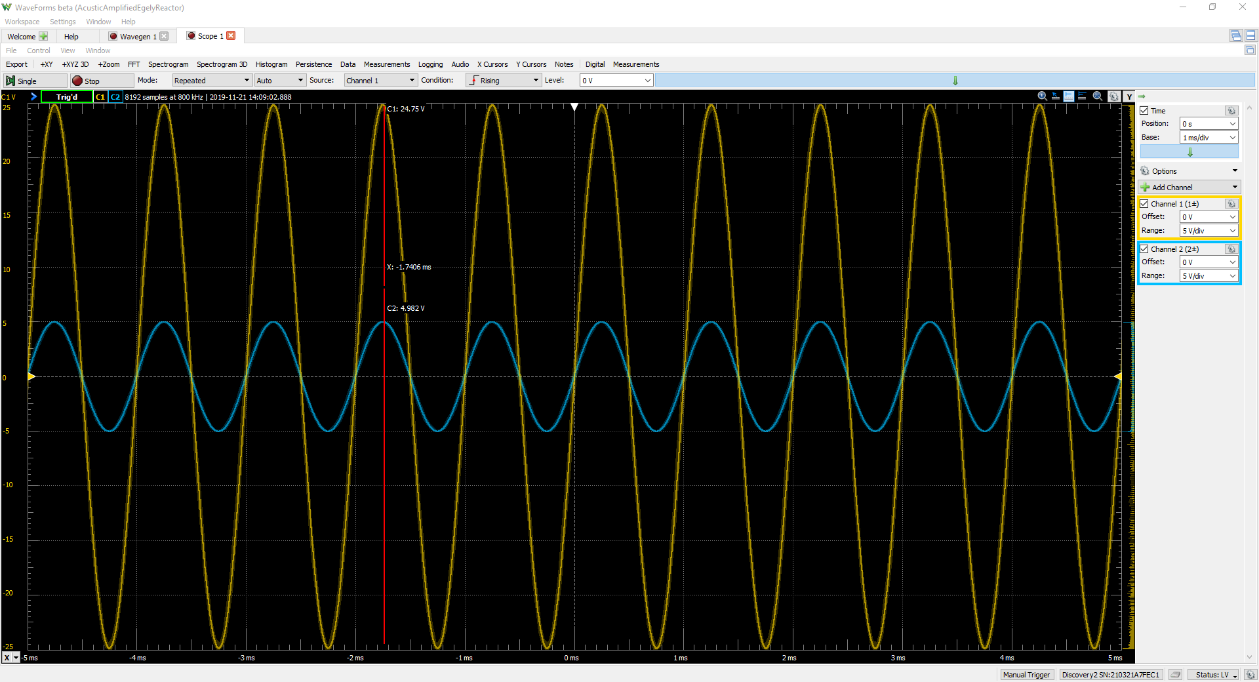
Measurements/WaveForms/Experiments/AcusticAmplifiedEgelyReactor/08_AcusticAmplifiedReactorT06-InputOutputSignals.png
