andrasfuchs/BioBalanceDetector/Measurements/WaveForms/Experiments/AcusticAmplifiedEgelyReactor/09_AcusticAmplifiedReactorT06-MeltedThinCopperSpiral.png

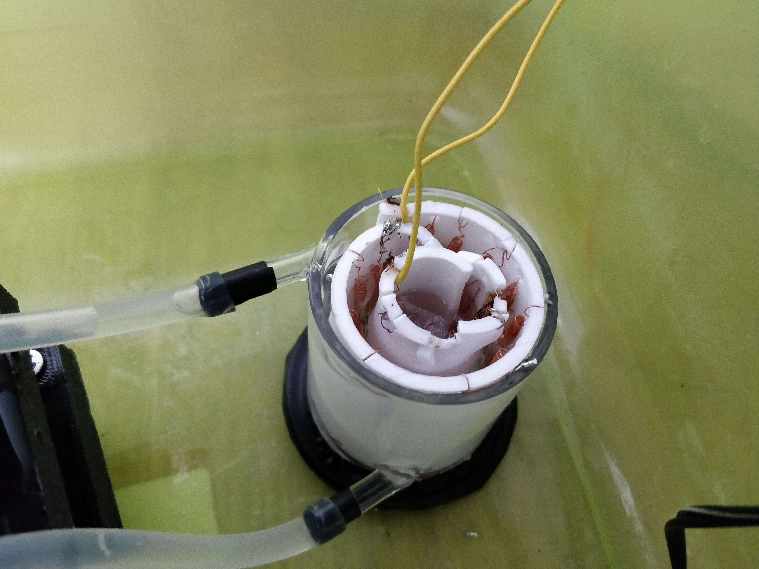
Measurements/WaveForms/Experiments/AcusticAmplifiedEgelyReactor/09_AcusticAmplifiedReactorT06-MeltedThinCopperSpiral.png
