andrasfuchs/BioBalanceDetector/Measurements/WaveForms/Experiments/AcusticAmplifiedEgelyReactor/10_AcusticAmplifiedReactorT12-FluidImpedance.png

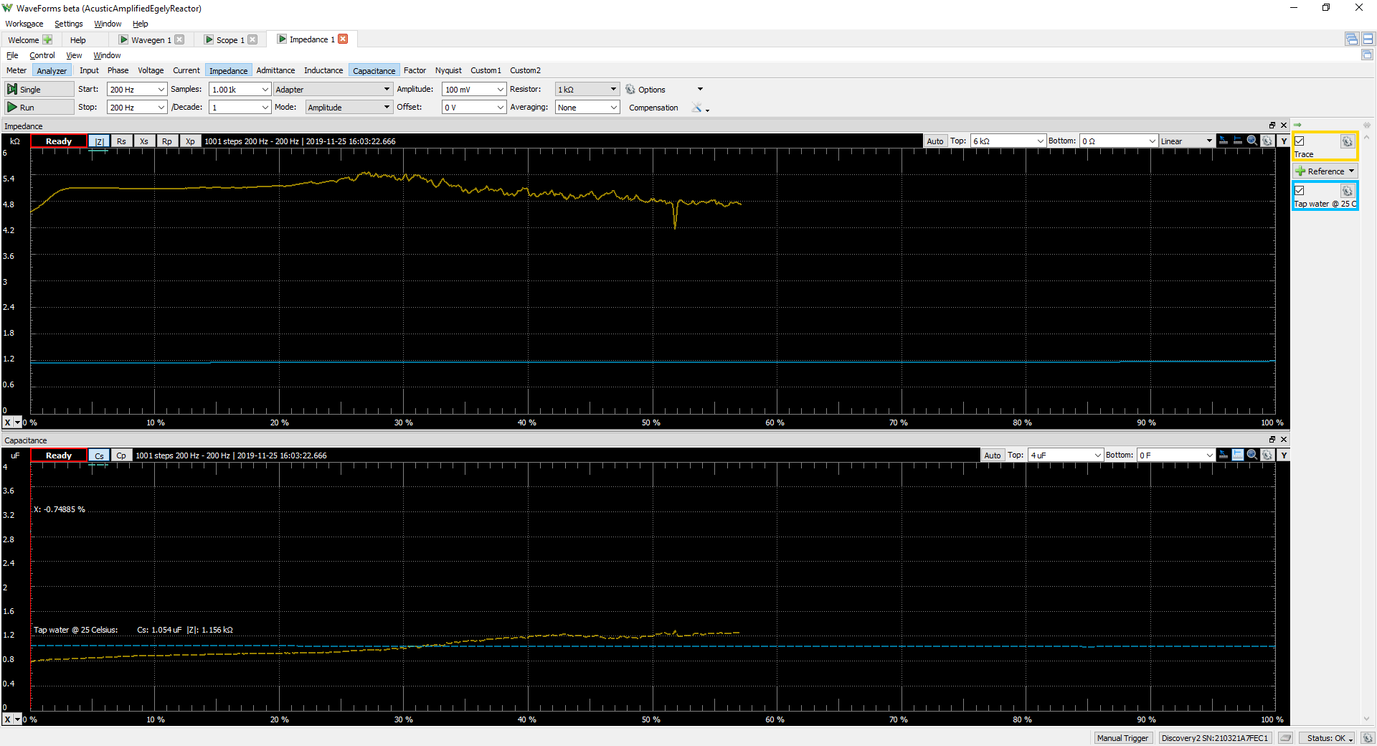
Measurements/WaveForms/Experiments/AcusticAmplifiedEgelyReactor/10_AcusticAmplifiedReactorT12-FluidImpedance.png
