andrasfuchs/BioBalanceDetector/Measurements/WaveForms/Experiments/AcusticAmplifiedEgelyReactor/11_AcusticAmplifiedReactorT16-FluidImpedance.png

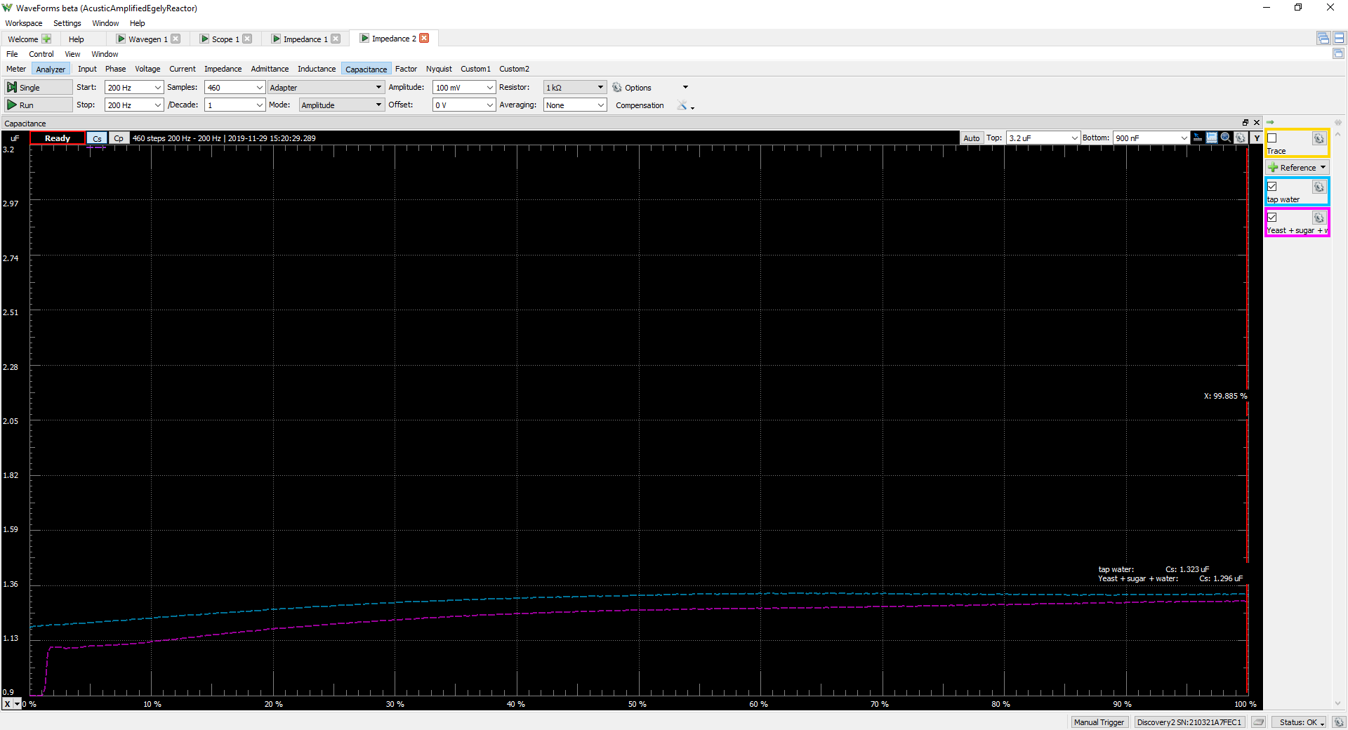
Measurements/WaveForms/Experiments/AcusticAmplifiedEgelyReactor/11_AcusticAmplifiedReactorT16-FluidImpedance.png
