andrasfuchs/BioBalanceDetector/Measurements/WaveForms/Experiments/AcusticAmplifiedEgelyReactor/12_AcusticAmplifiedReactorT18-FluidImpedance.png

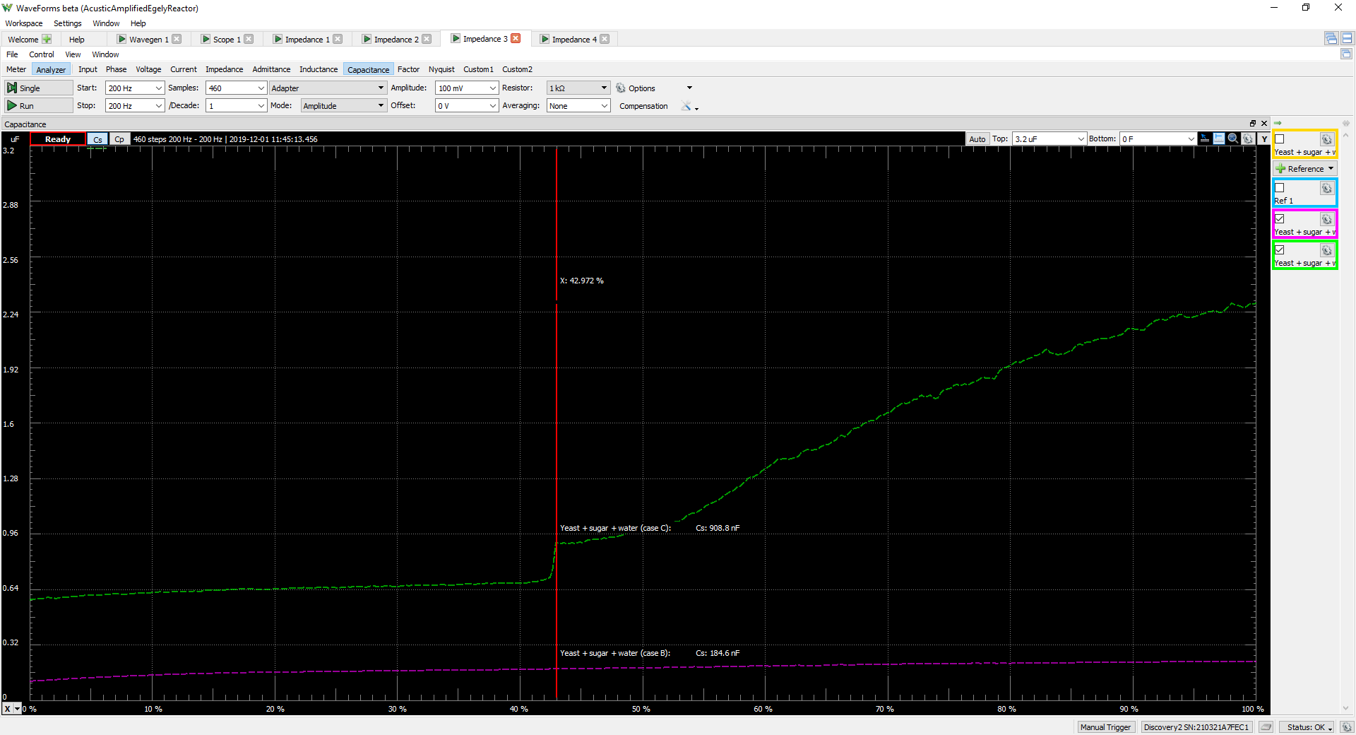
Measurements/WaveForms/Experiments/AcusticAmplifiedEgelyReactor/12_AcusticAmplifiedReactorT18-FluidImpedance.png
