andrasfuchs/BioBalanceDetector/Measurements/WaveForms/Experiments/AcusticAmplifiedEgelyReactor/13_AcusticAmplifiedReactorT19-FluidImpedance.png

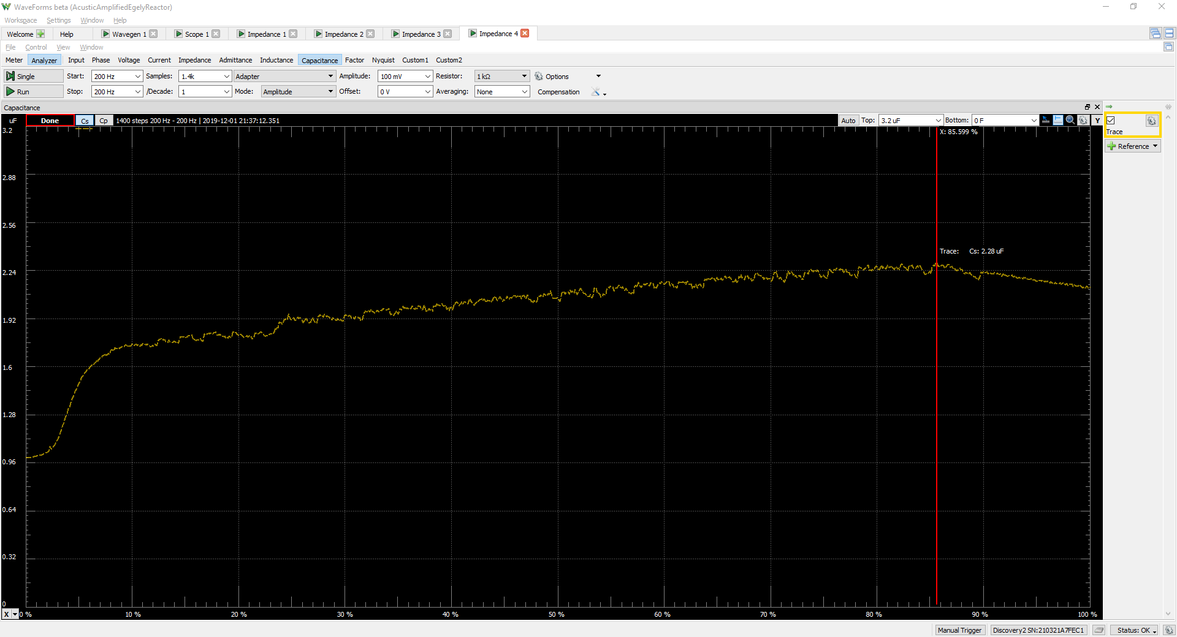
Measurements/WaveForms/Experiments/AcusticAmplifiedEgelyReactor/13_AcusticAmplifiedReactorT19-FluidImpedance.png
