andrasfuchs/BioBalanceDetector/Measurements/WaveForms/Experiments/AcusticAmplifiedEgelyReactor/14_AcusticAmplifiedReactorT21-FluidImpedance.png

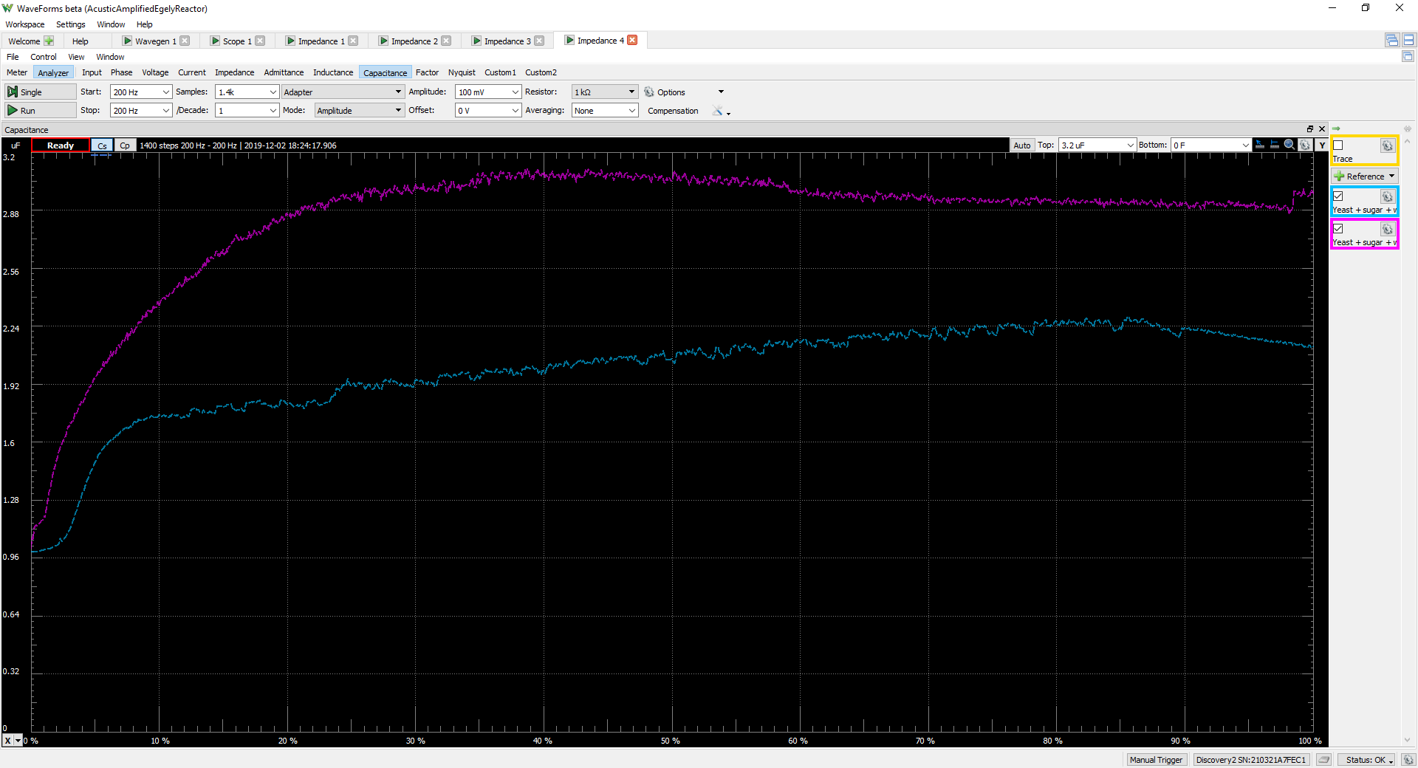
Measurements/WaveForms/Experiments/AcusticAmplifiedEgelyReactor/14_AcusticAmplifiedReactorT21-FluidImpedance.png
