andrasfuchs/BioBalanceDetector/Measurements/WaveForms/Experiments/AcusticAmplifiedEgelyReactor/15_AcusticAmplifiedReactorT22-FluidImpedance.png

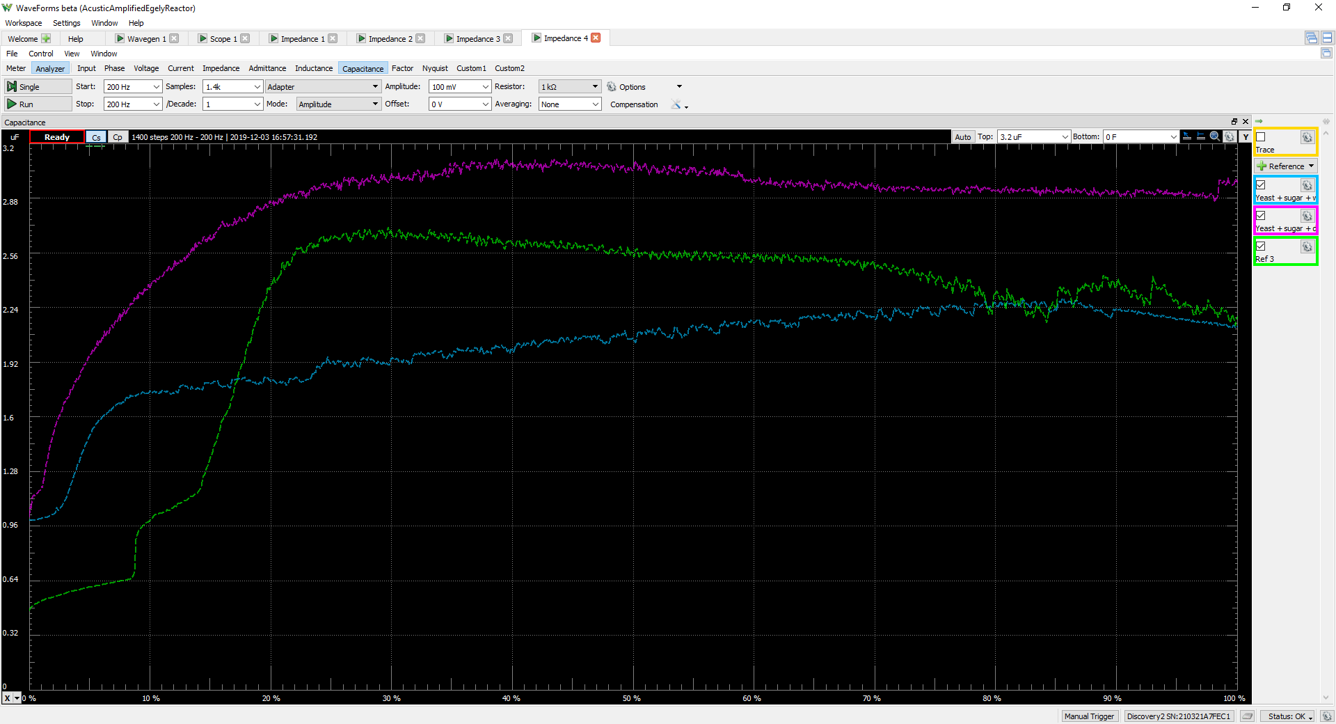
Measurements/WaveForms/Experiments/AcusticAmplifiedEgelyReactor/15_AcusticAmplifiedReactorT22-FluidImpedance.png
