andrasfuchs/BioBalanceDetector/Measurements/WaveForms/Experiments/AcusticAmplifiedEgelyReactor/16_AcusticAmplifiedReactorT24-FluidImpedance.png

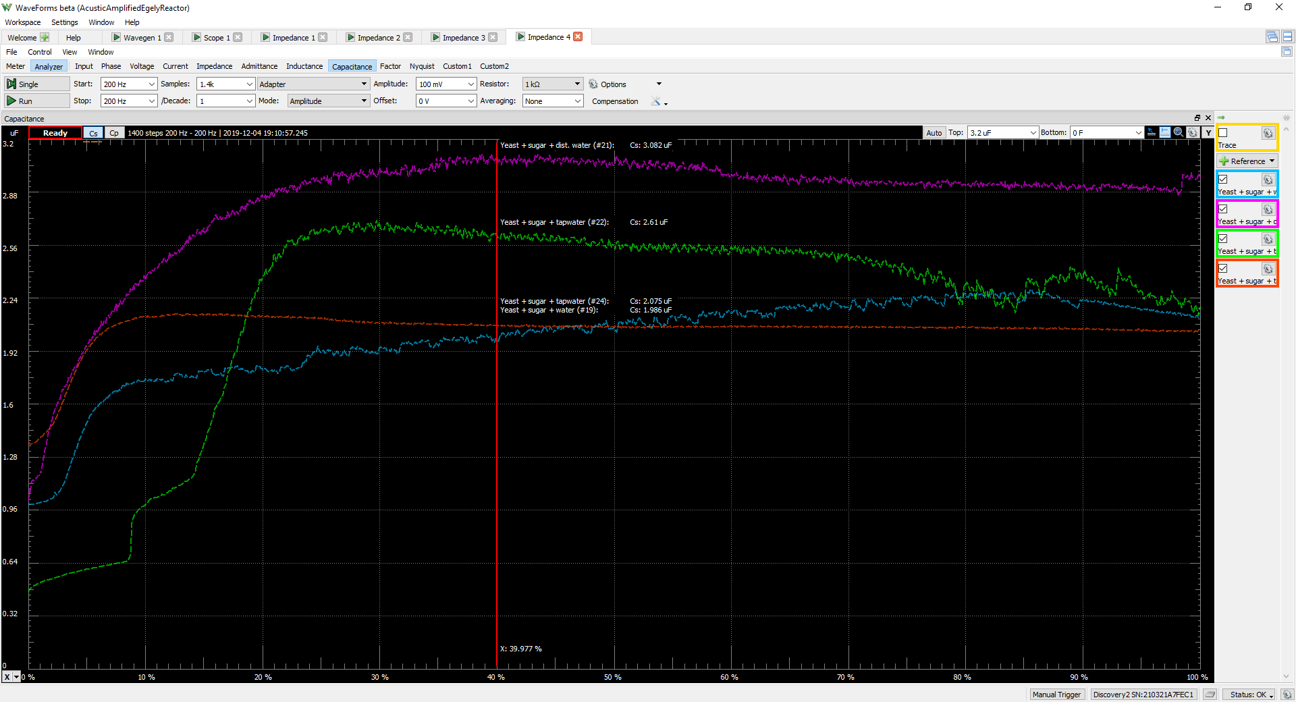
Measurements/WaveForms/Experiments/AcusticAmplifiedEgelyReactor/16_AcusticAmplifiedReactorT24-FluidImpedance.png
