andrasfuchs/BioBalanceDetector/Measurements/WaveForms/Experiments/AcusticAmplifiedEgelyReactor/17_AcusticAmplifiedReactorT27-FluidImpedance.png

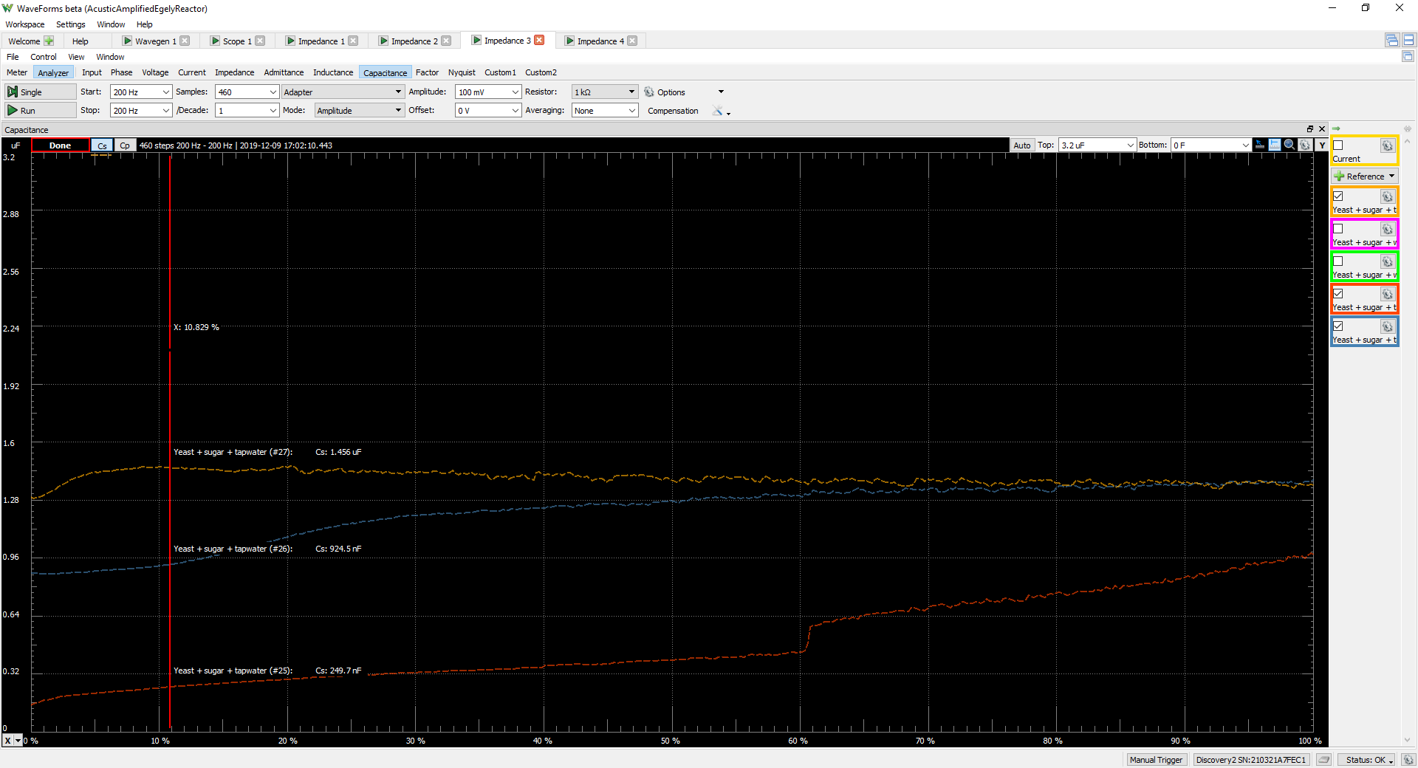
Measurements/WaveForms/Experiments/AcusticAmplifiedEgelyReactor/17_AcusticAmplifiedReactorT27-FluidImpedance.png
