andrasfuchs/BioBalanceDetector/Measurements/WaveForms/Experiments/AcusticAmplifiedEgelyReactor/18_AcusticAmplifiedReactorT28-FluidImpedance.png

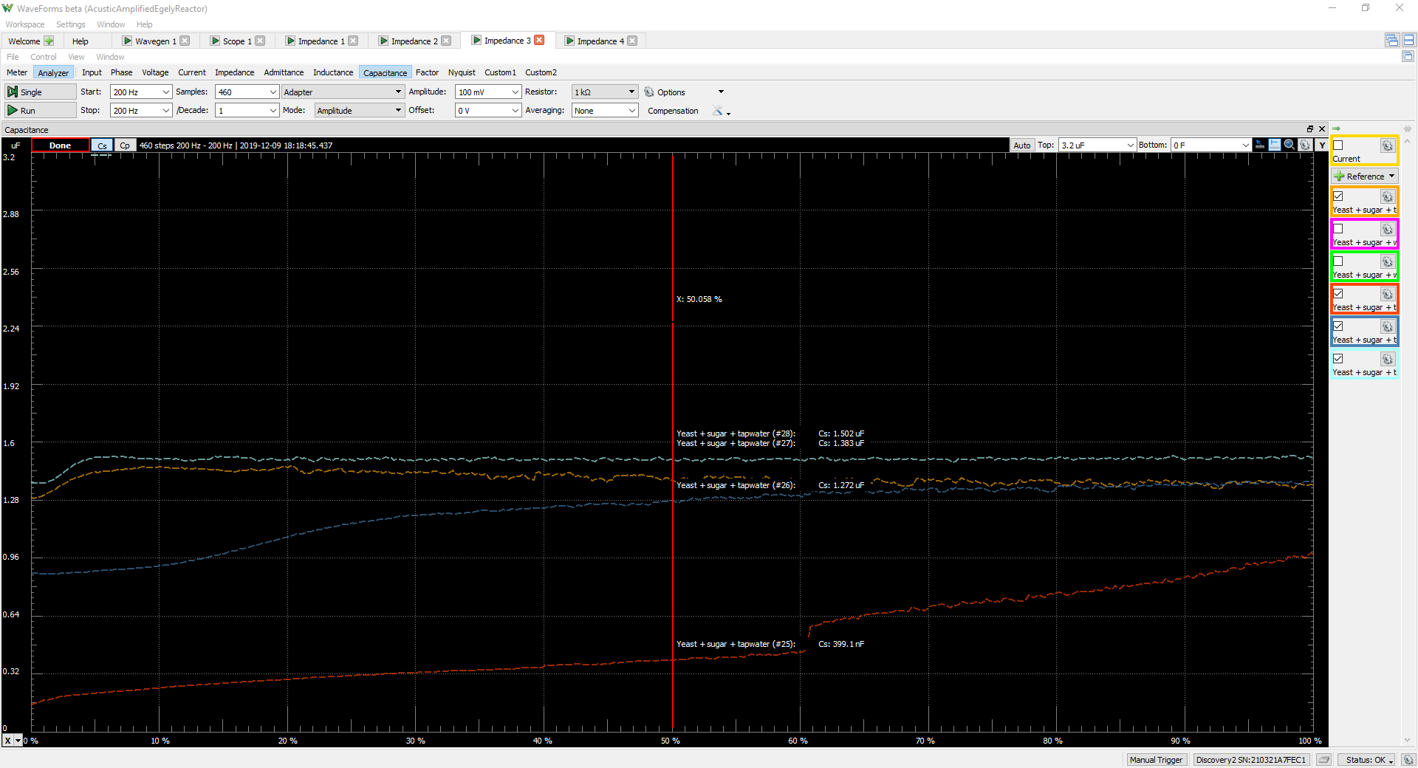
Measurements/WaveForms/Experiments/AcusticAmplifiedEgelyReactor/18_AcusticAmplifiedReactorT28-FluidImpedance.png
