andrasfuchs/BioBalanceDetector/Measurements/WaveForms/Experiments/AcusticAmplifiedEgelyReactor/19_AcusticAmplifiedReactorT29-FluidImpedance.png

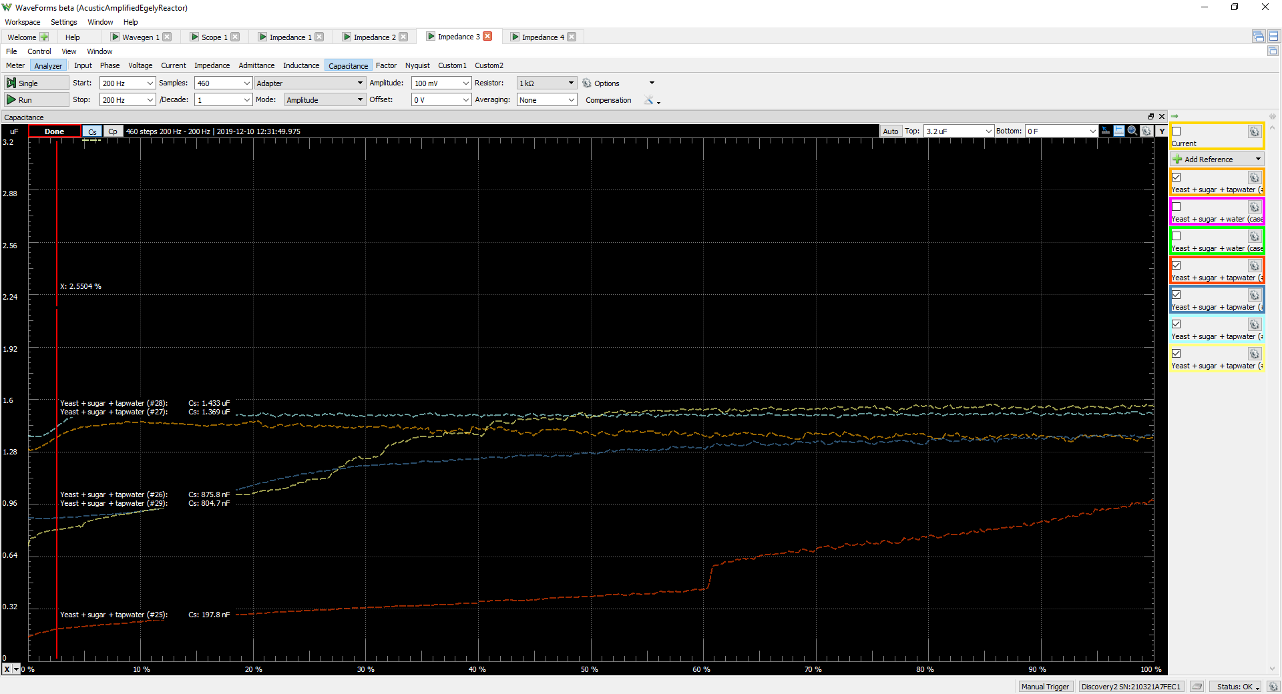
Measurements/WaveForms/Experiments/AcusticAmplifiedEgelyReactor/19_AcusticAmplifiedReactorT29-FluidImpedance.png
