andrasfuchs/BioBalanceDetector/Measurements/WaveForms/Experiments/AcusticAmplifiedEgelyReactor/20_AcusticAmplifiedReactorT31-FluidImpedance.png

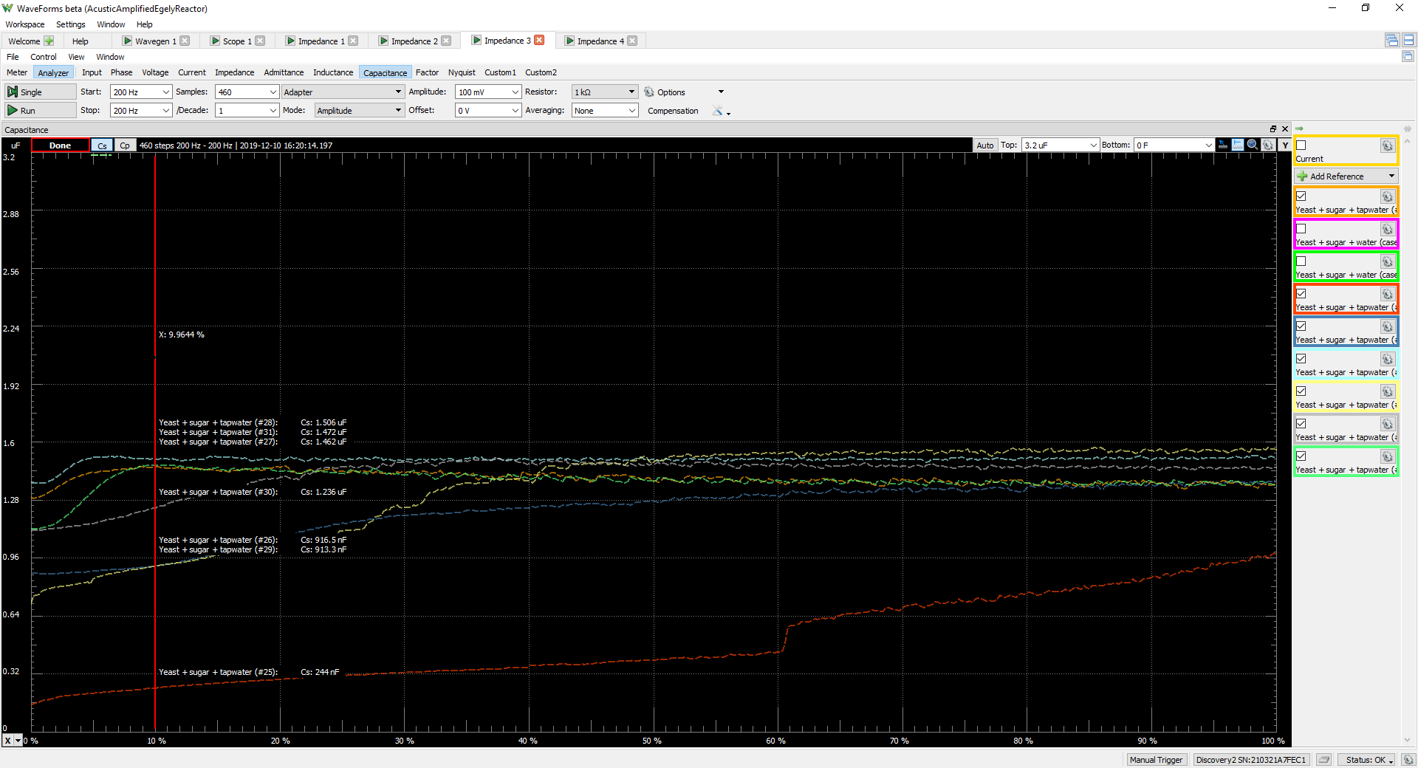
Measurements/WaveForms/Experiments/AcusticAmplifiedEgelyReactor/20_AcusticAmplifiedReactorT31-FluidImpedance.png
