andrasfuchs/BioBalanceDetector/Measurements/WaveForms/Experiments/AcusticAmplifiedEgelyReactor/22_AcusticAmplifiedReactorT32-AmplifierOutput1kHz.png

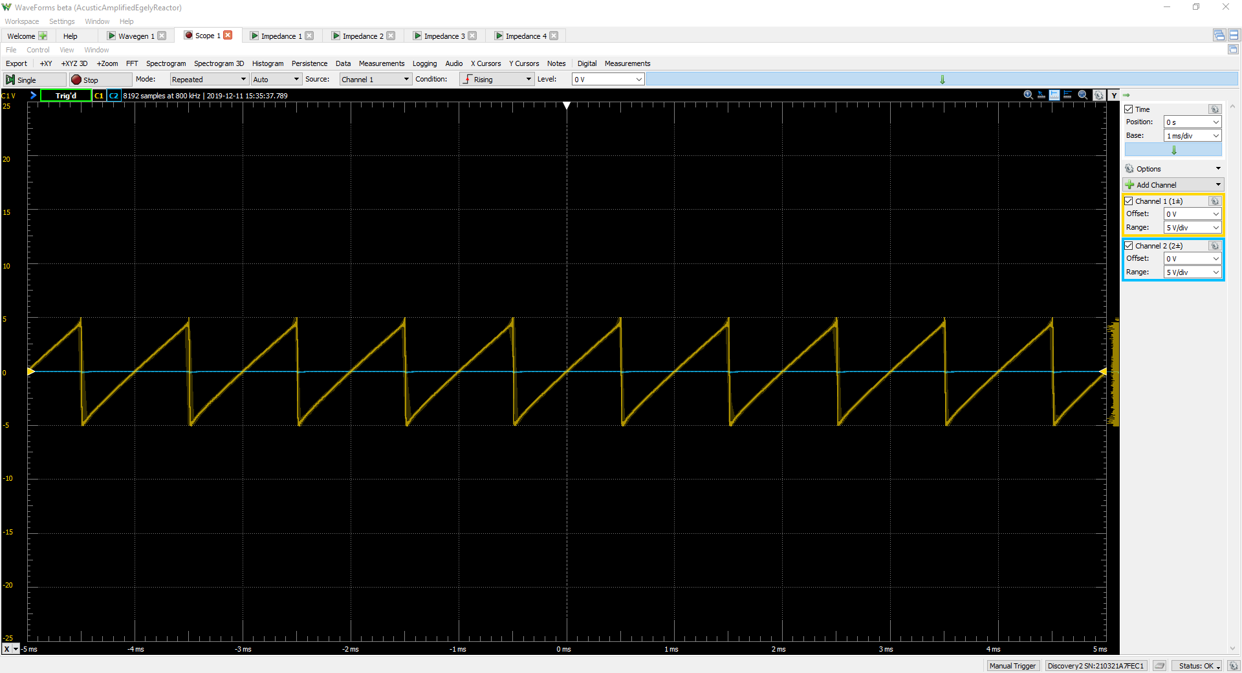
Measurements/WaveForms/Experiments/AcusticAmplifiedEgelyReactor/22_AcusticAmplifiedReactorT32-AmplifierOutput1kHz.png
