andrasfuchs/BioBalanceDetector/Measurements/WaveForms/Experiments/AcusticAmplifiedEgelyReactor/23_AcusticAmplifiedReactorT37-FluidImpedance.png

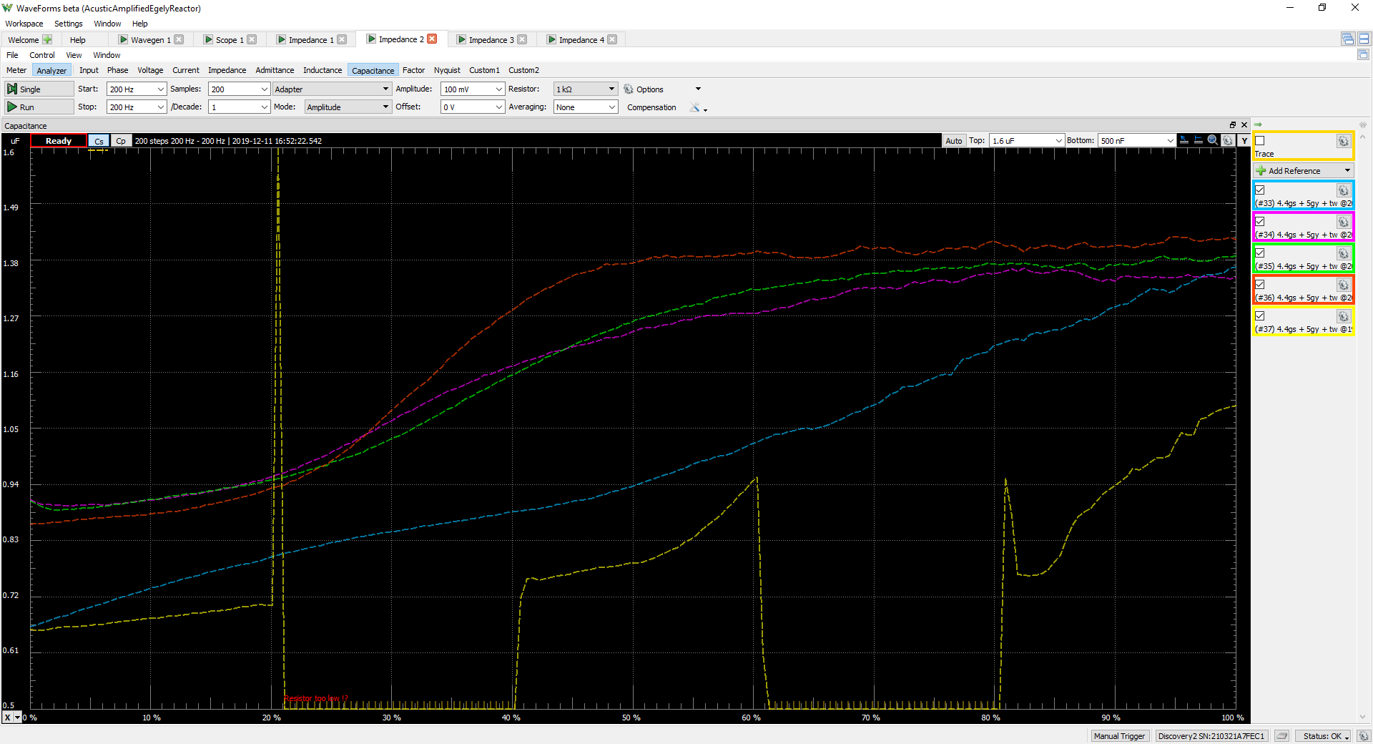
Measurements/WaveForms/Experiments/AcusticAmplifiedEgelyReactor/23_AcusticAmplifiedReactorT37-FluidImpedance.png
