andrasfuchs/BioBalanceDetector/Measurements/WaveForms/Experiments/AcusticAmplifiedEgelyReactor/24_AcusticAmplifiedReactorT47-FluidImpedance.png

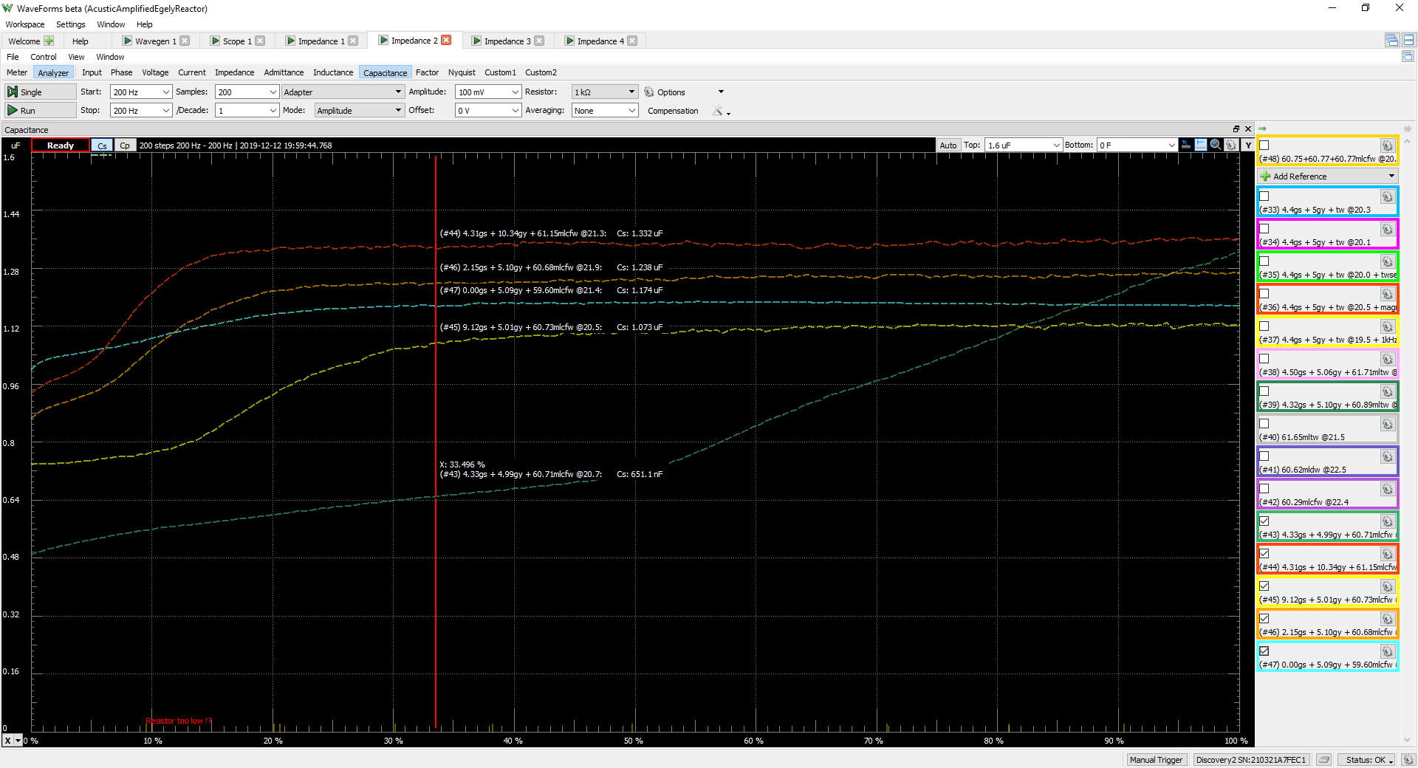
Measurements/WaveForms/Experiments/AcusticAmplifiedEgelyReactor/24_AcusticAmplifiedReactorT47-FluidImpedance.png
