andrasfuchs/BioBalanceDetector/Measurements/WaveForms/Experiments/AcusticAmplifiedEgelyReactor/25_AcusticAmplifiedReactorT48-FluidImpedance.png

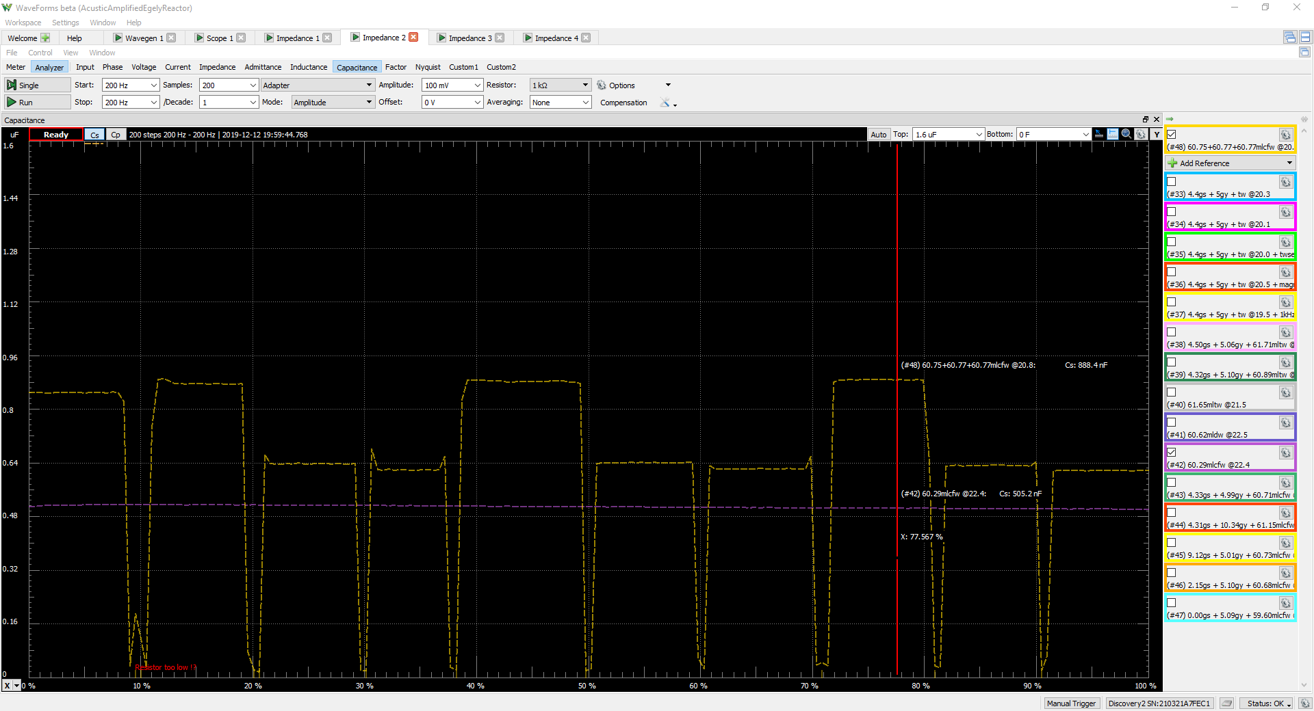
Measurements/WaveForms/Experiments/AcusticAmplifiedEgelyReactor/25_AcusticAmplifiedReactorT48-FluidImpedance.png
