andrasfuchs/BioBalanceDetector/Measurements/WaveForms/Experiments/AcusticAmplifiedEgelyReactor/26_AcusticAmplifiedReactorT52-FluidImpedance.png

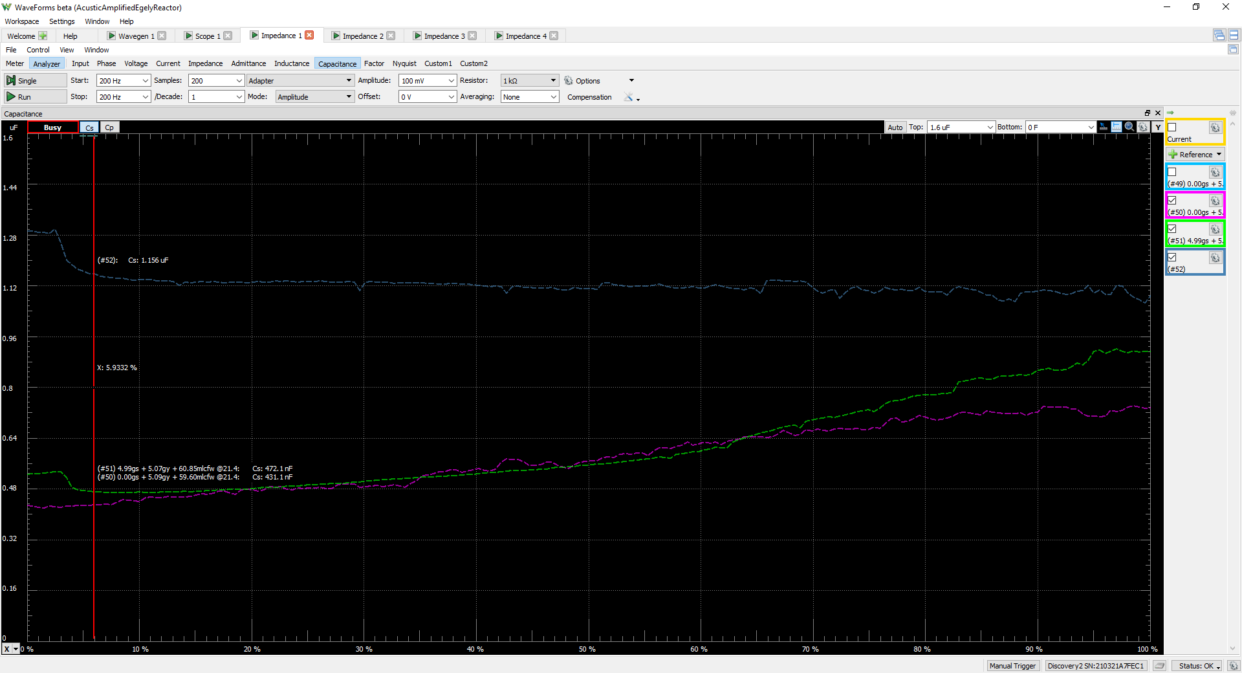
Measurements/WaveForms/Experiments/AcusticAmplifiedEgelyReactor/26_AcusticAmplifiedReactorT52-FluidImpedance.png
