andrasfuchs/BioBalanceDetector/Measurements/WaveForms/Experiments/AcusticAmplifiedEgelyReactor/27_AcusticAmplifiedReactorT53-FluidImpedance.png

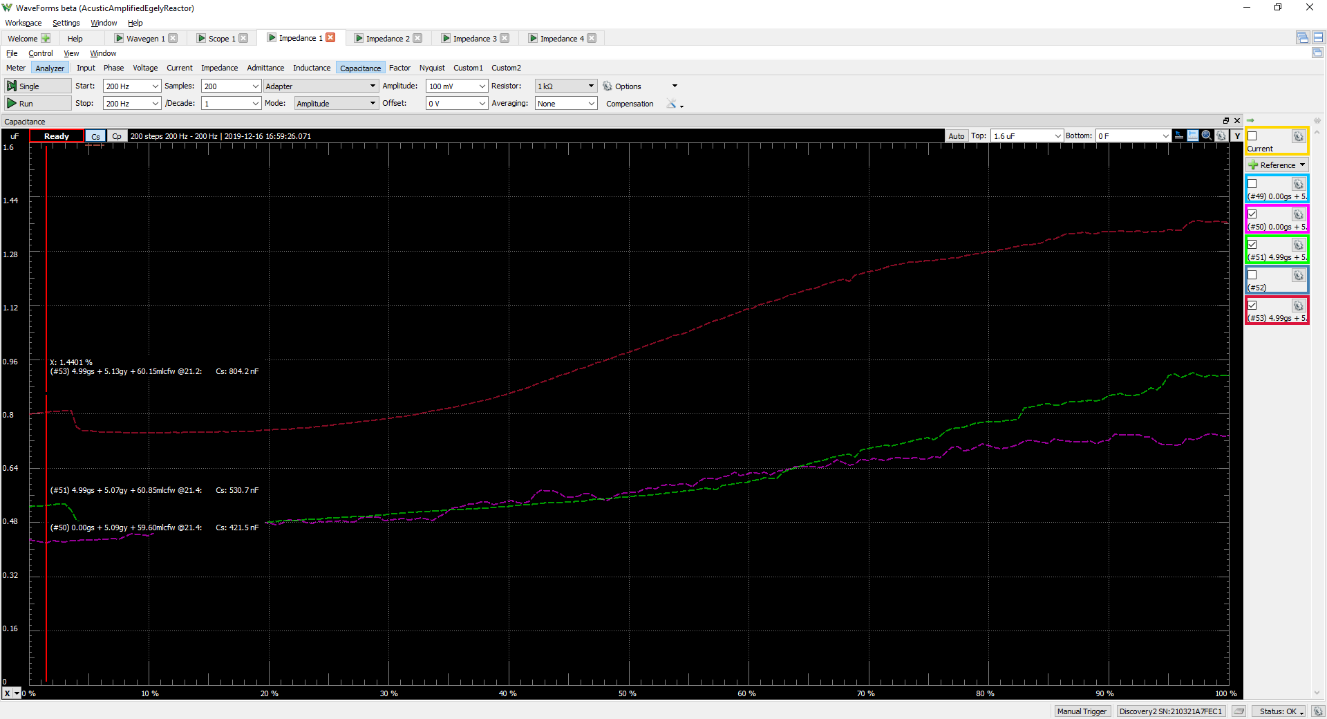
Measurements/WaveForms/Experiments/AcusticAmplifiedEgelyReactor/27_AcusticAmplifiedReactorT53-FluidImpedance.png
