andrasfuchs/BioBalanceDetector/Measurements/WaveForms/Experiments/AcusticAmplifiedEgelyReactor/28_AcusticAmplifiedReactorT54-FluidImpedance.png

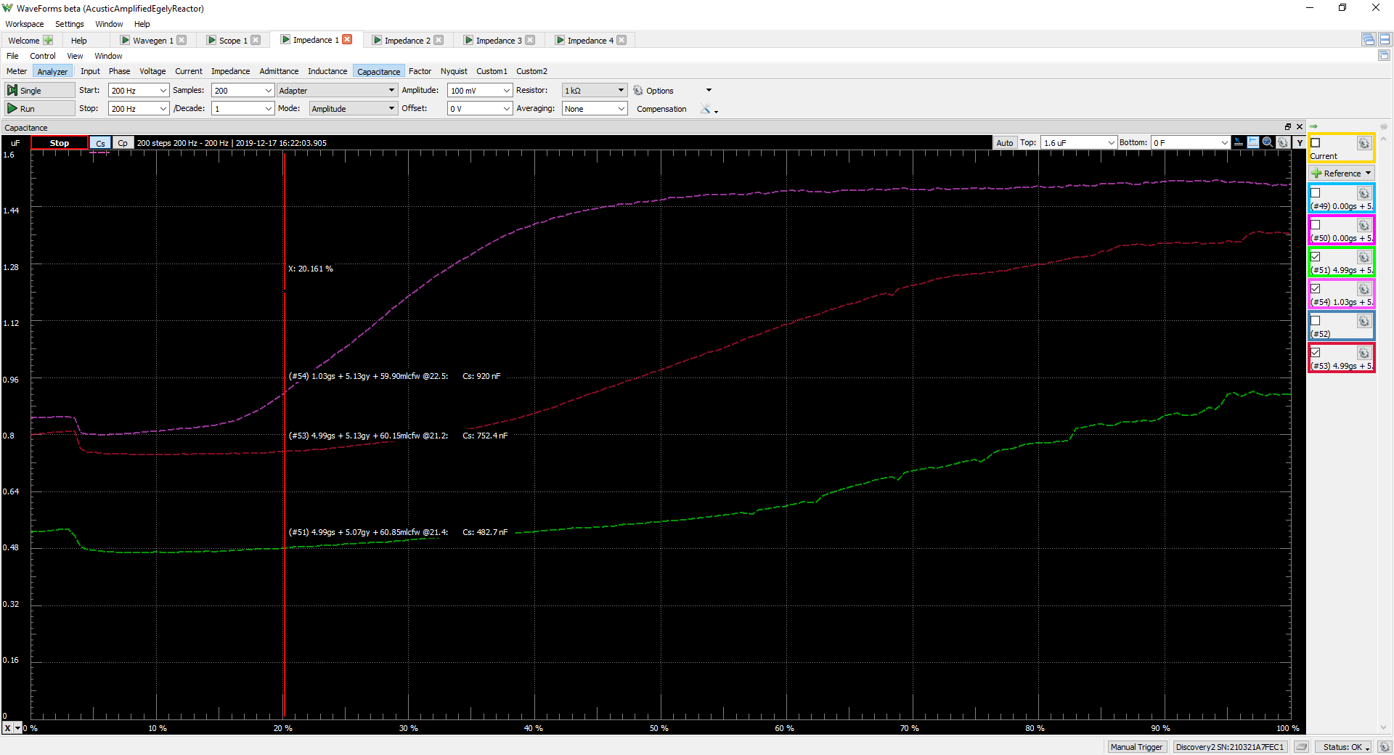
Measurements/WaveForms/Experiments/AcusticAmplifiedEgelyReactor/28_AcusticAmplifiedReactorT54-FluidImpedance.png
