andrasfuchs/BioBalanceDetector/Measurements/WaveForms/Experiments/AcusticAmplifiedEgelyReactor/29_AcusticAmplifiedReactorT56-FluidImpedance.png

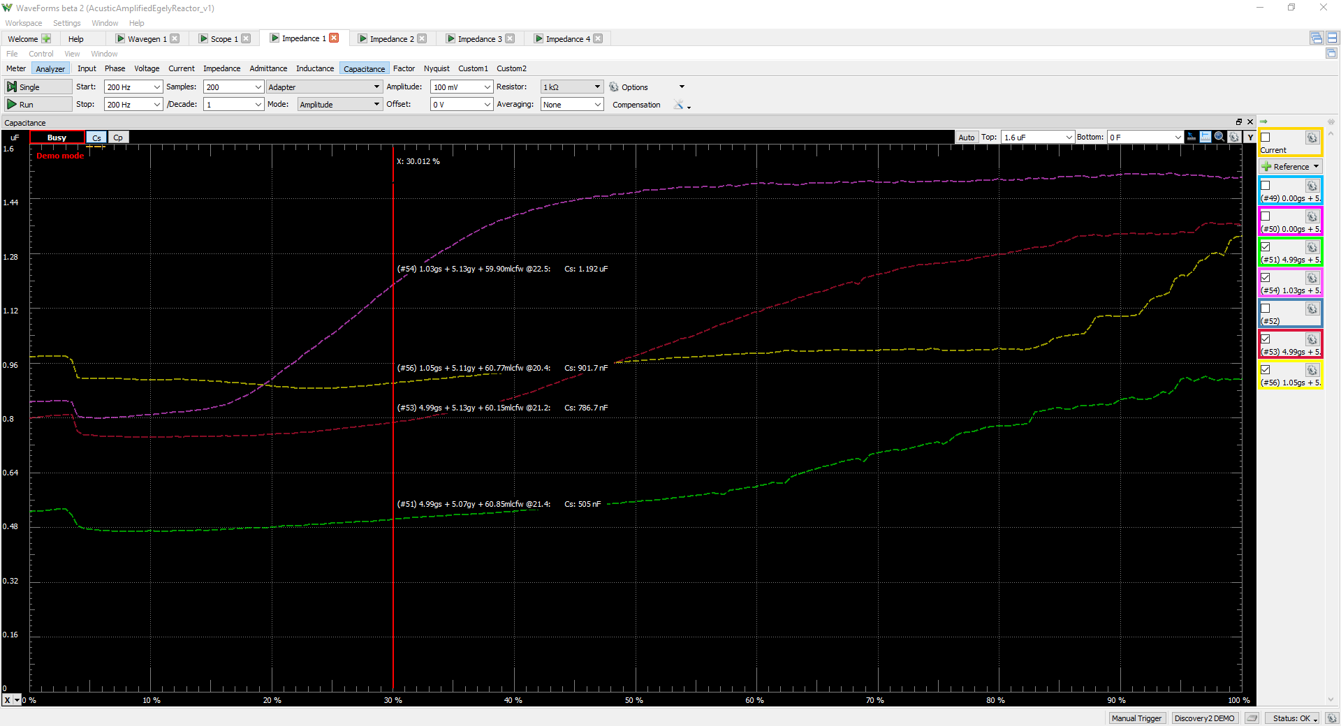
Measurements/WaveForms/Experiments/AcusticAmplifiedEgelyReactor/29_AcusticAmplifiedReactorT56-FluidImpedance.png
