andrasfuchs/BioBalanceDetector/Measurements/WaveForms/Experiments/AcusticAmplifiedEgelyReactor/30_AcusticAmplifiedReactorT57-FluidImpedance.png

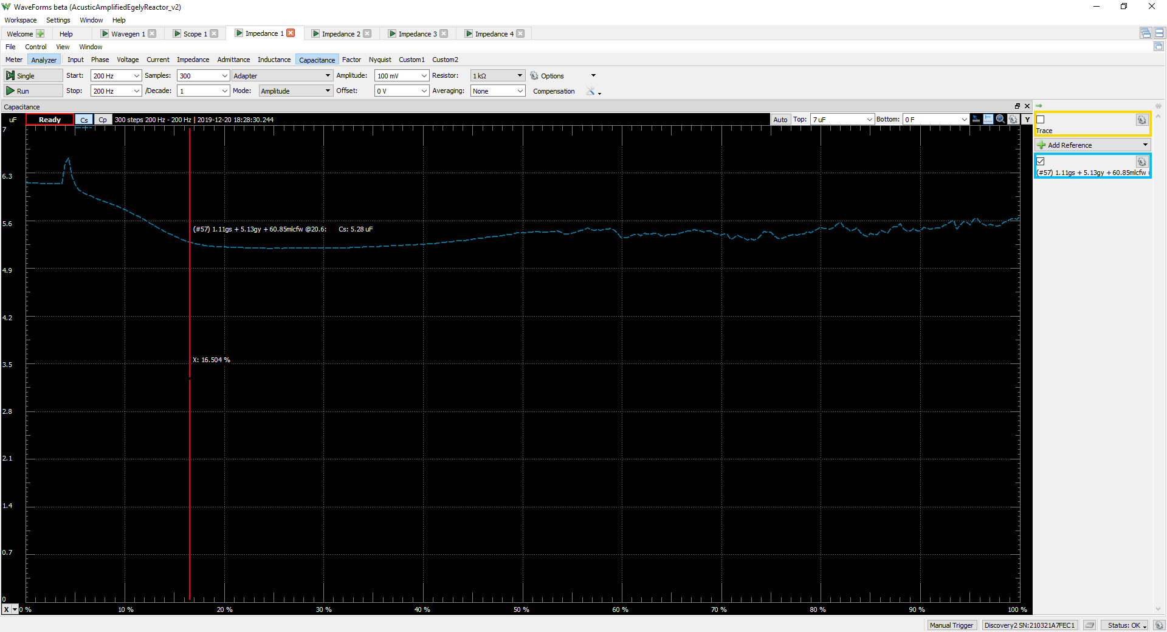
Measurements/WaveForms/Experiments/AcusticAmplifiedEgelyReactor/30_AcusticAmplifiedReactorT57-FluidImpedance.png
