andrasfuchs/BioBalanceDetector/Measurements/WaveForms/Experiments/AcusticAmplifiedEgelyReactor/IMG_20191119_120206.jpg

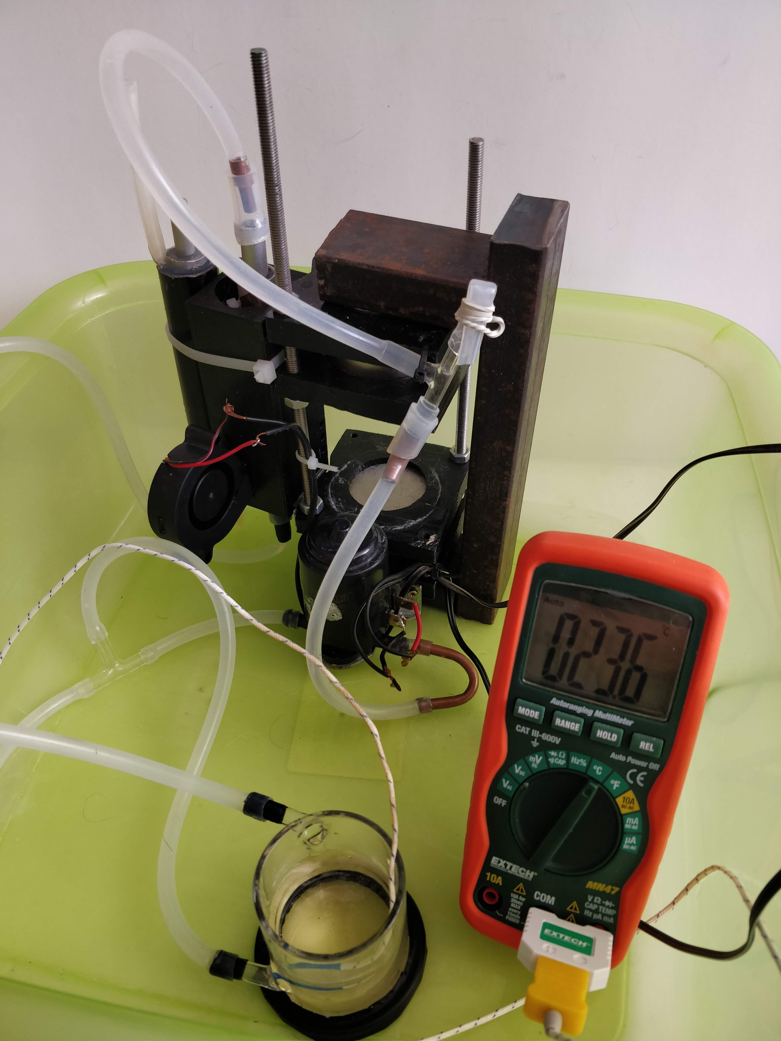
Measurements/WaveForms/Experiments/AcusticAmplifiedEgelyReactor/IMG_20191119_120206.jpg
