andrasfuchs/BioBalanceDetector/Measurements/WaveForms/Experiments/AcusticAmplifiedEgelyReactor/IMG_20191120_084306-ThinCopperSpiral.jpg

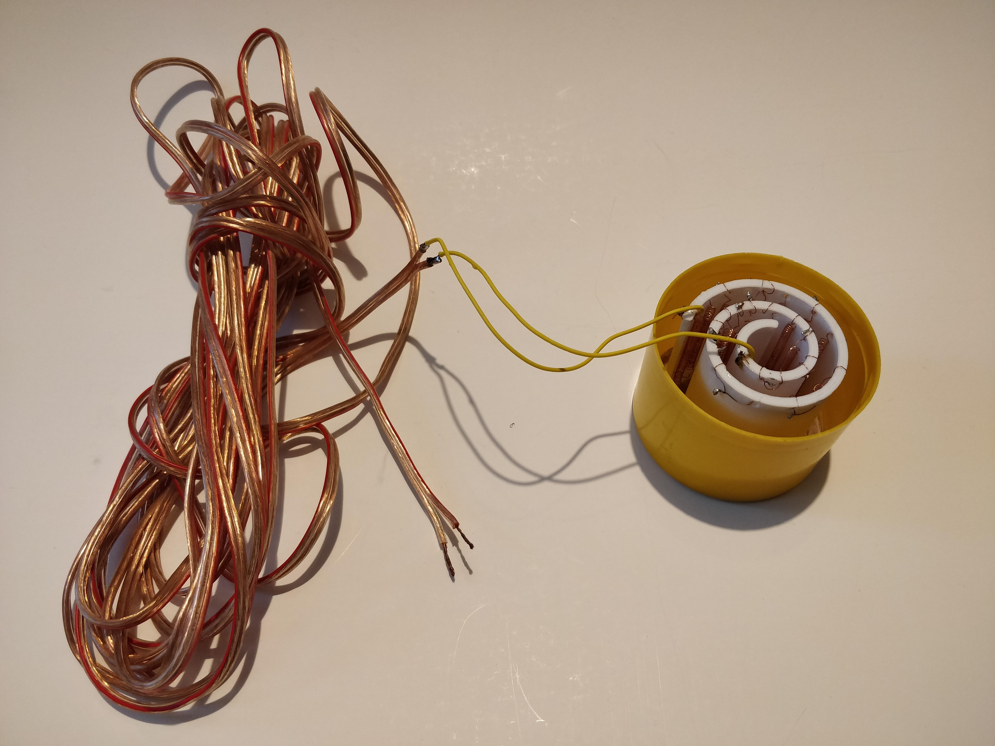
Measurements/WaveForms/Experiments/AcusticAmplifiedEgelyReactor/IMG_20191120_084306-ThinCopperSpiral.jpg
