andrasfuchs/BioBalanceDetector/Measurements/WaveForms/Experiments/AcusticAmplifiedEgelyReactor/IMG_20191120_084517-ThickCopperCoilWithResistance.jpg

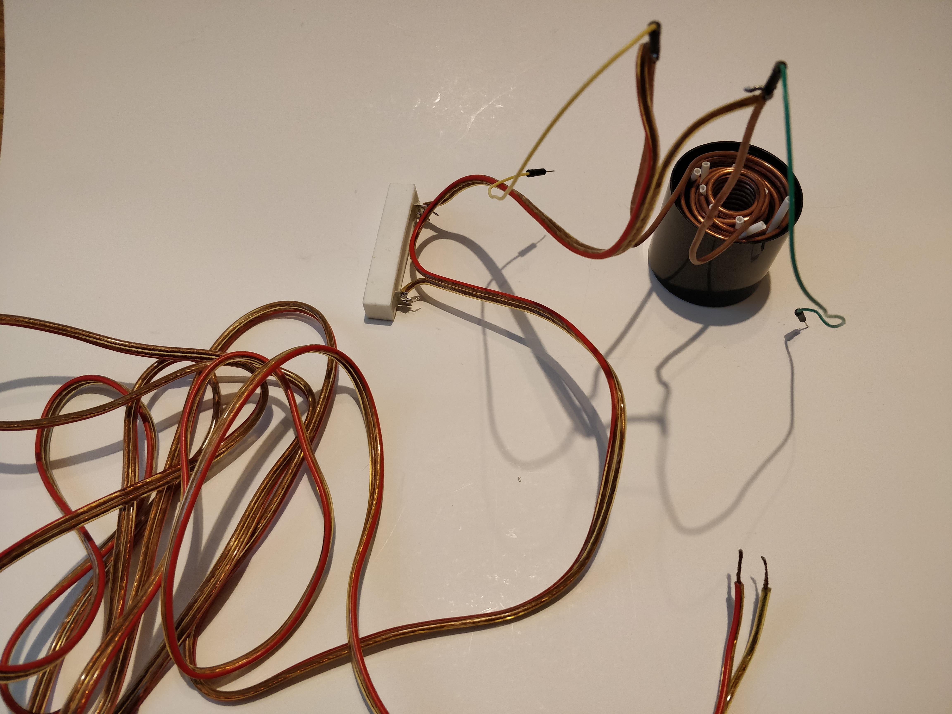
Measurements/WaveForms/Experiments/AcusticAmplifiedEgelyReactor/IMG_20191120_084517-ThickCopperCoilWithResistance.jpg
