andrasfuchs/BioBalanceDetector/Measurements/WaveForms/Experiments/AcusticAmplifiedEgelyReactor/IMG_20191120_084606-Container.jpg

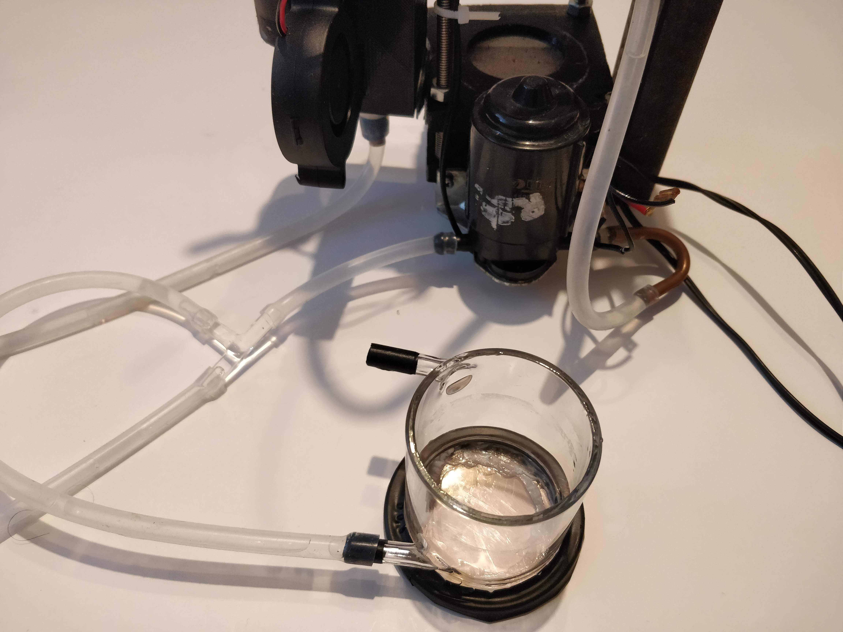
Measurements/WaveForms/Experiments/AcusticAmplifiedEgelyReactor/IMG_20191120_084606-Container.jpg
