andrasfuchs/BioBalanceDetector/Measurements/WaveForms/Experiments/AcusticAmplifiedEgelyReactor/IMG_20191120_084617-WaterAndAirCoolers.jpg

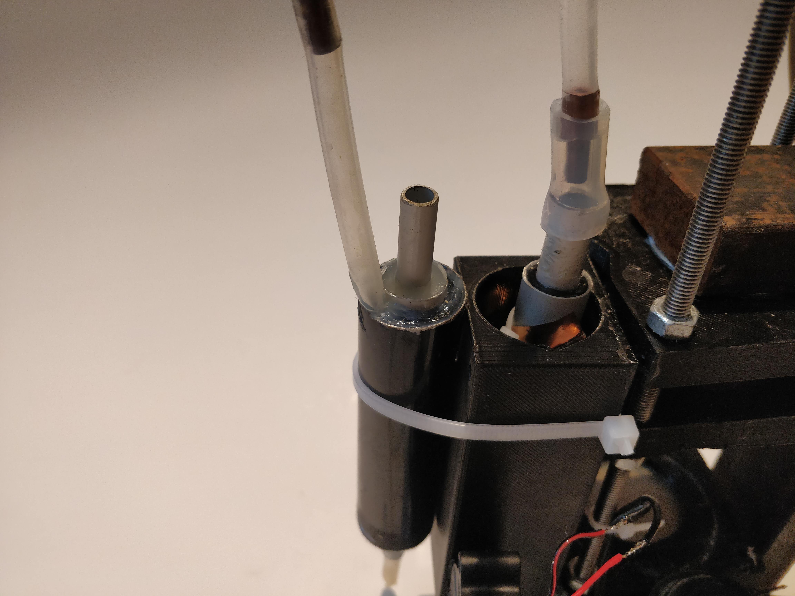
Measurements/WaveForms/Experiments/AcusticAmplifiedEgelyReactor/IMG_20191120_084617-WaterAndAirCoolers.jpg
