andrasfuchs/BioBalanceDetector/Measurements/WaveForms/Experiments/AmplifiedSignalMagnetYeast/01_1Vp2p-Signal_x1Gain.png

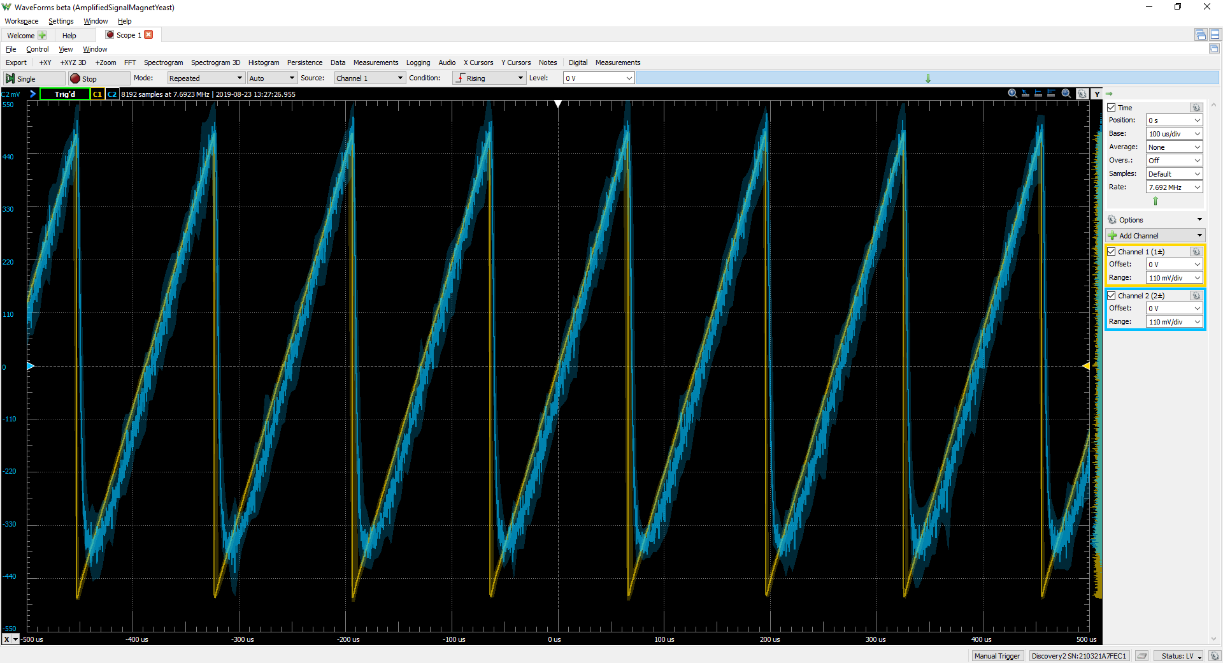
Measurements/WaveForms/Experiments/AmplifiedSignalMagnetYeast/01_1Vp2p-Signal_x1Gain.png
