andrasfuchs/BioBalanceDetector/Measurements/WaveForms/Experiments/AmplifiedSignalMagnetYeast/02_5Vp2p-Signal_Vrms.png

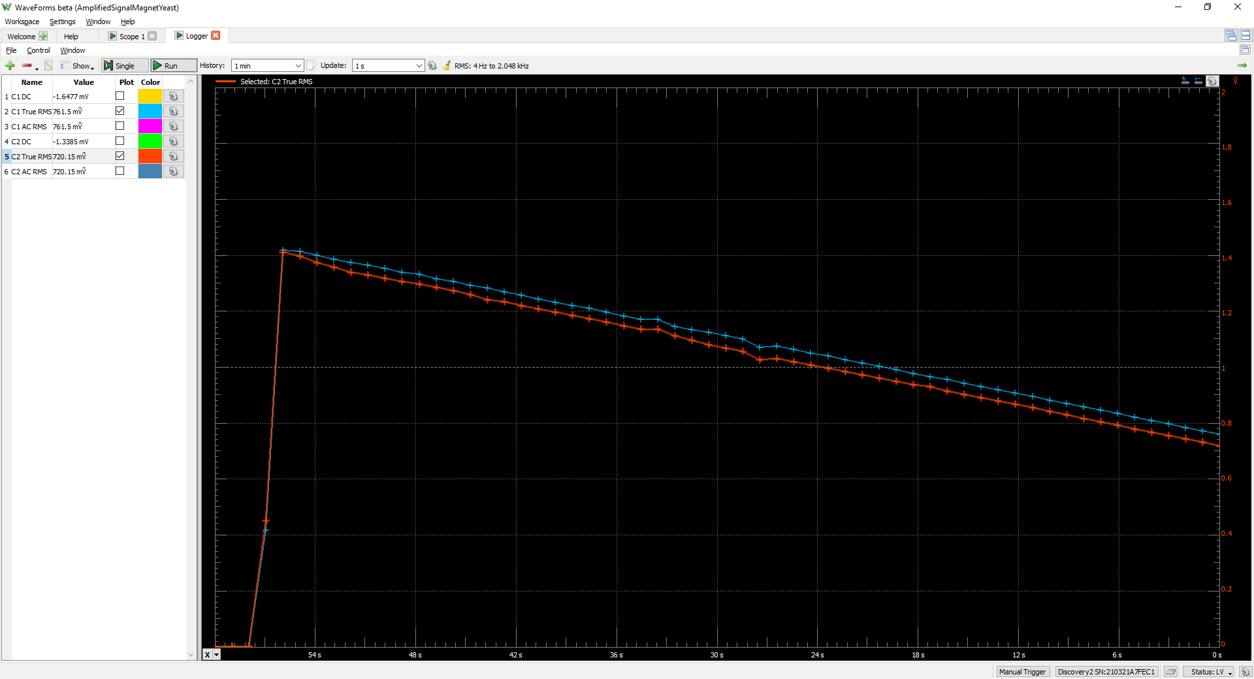
Measurements/WaveForms/Experiments/AmplifiedSignalMagnetYeast/02_5Vp2p-Signal_Vrms.png
