andrasfuchs/BioBalanceDetector/Measurements/WaveForms/Experiments/AmplifiedSignalMagnetYeast/03_5Vp2p-Signal_Spooky2GenX_Vrms.png

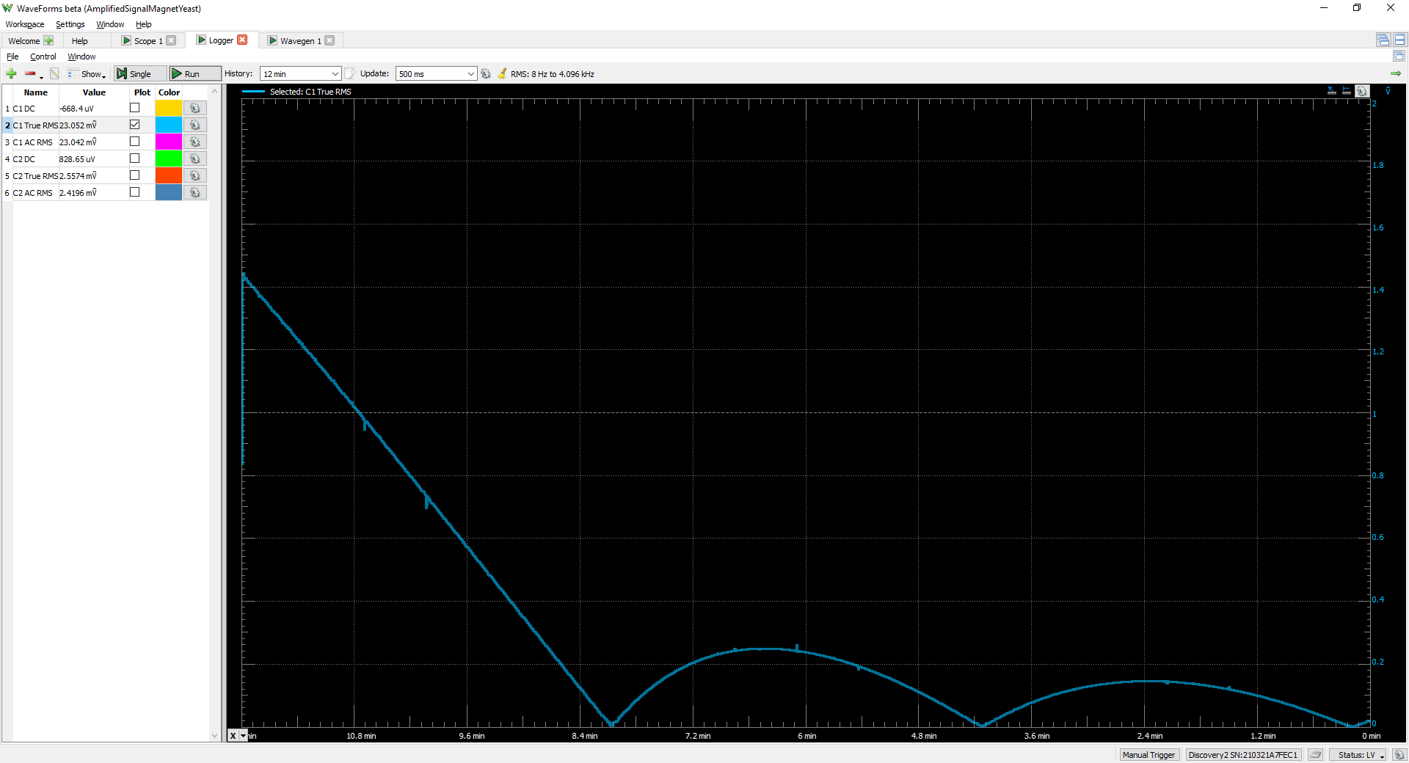
Measurements/WaveForms/Experiments/AmplifiedSignalMagnetYeast/03_5Vp2p-Signal_Spooky2GenX_Vrms.png
