andrasfuchs/BioBalanceDetector/Measurements/WaveForms/Experiments/AmplifiedSignalMagnetYeast/04_5Vp2p-Signal_AD2_Vrms.png

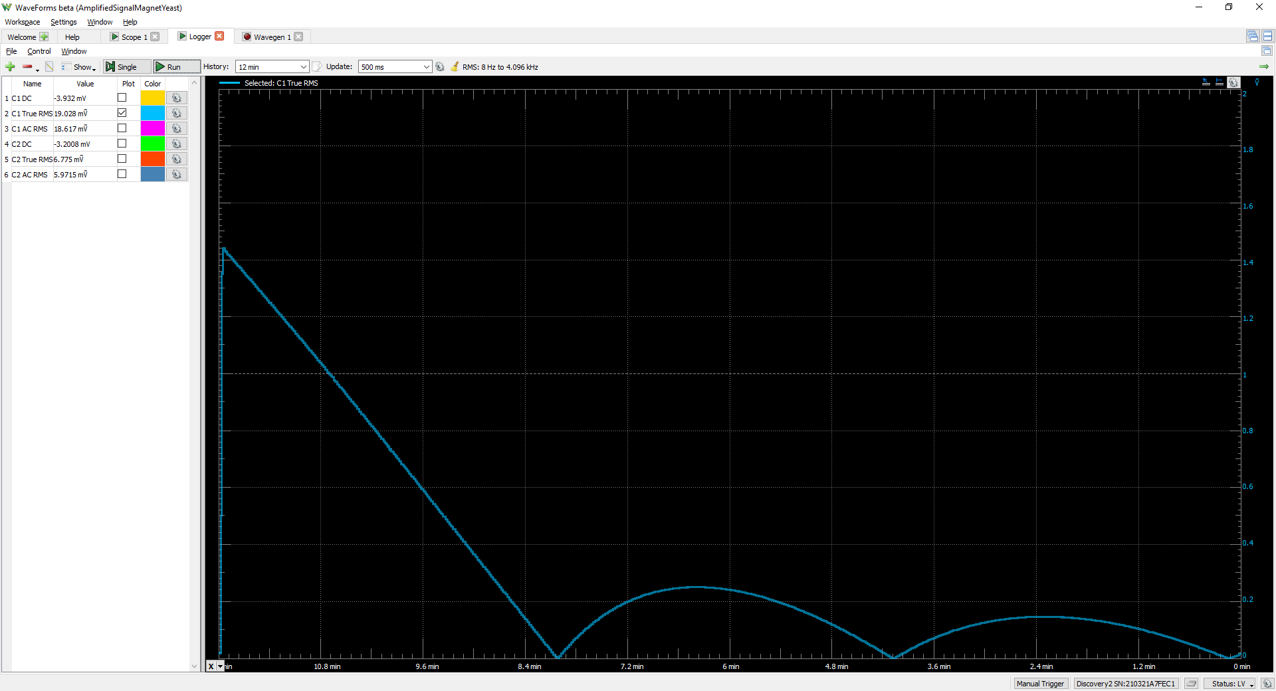
Measurements/WaveForms/Experiments/AmplifiedSignalMagnetYeast/04_5Vp2p-Signal_AD2_Vrms.png
