andrasfuchs/BioBalanceDetector/Measurements/WaveForms/Experiments/AmplifiedSignalMagnetYeast/IMG_20190823_113415.jpg

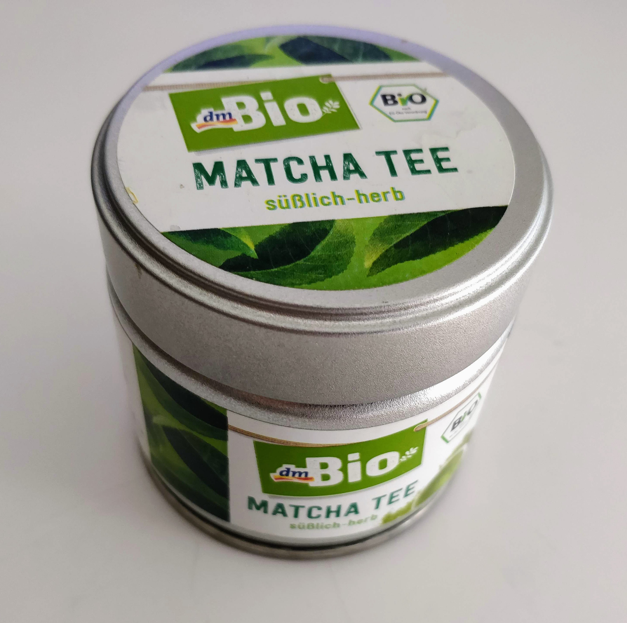
Measurements/WaveForms/Experiments/AmplifiedSignalMagnetYeast/IMG_20190823_113415.jpg
