andrasfuchs/BioBalanceDetector/Measurements/WaveForms/Experiments/AmplifiedSignalMagnetYeast/IMG_20190823_113858.jpg

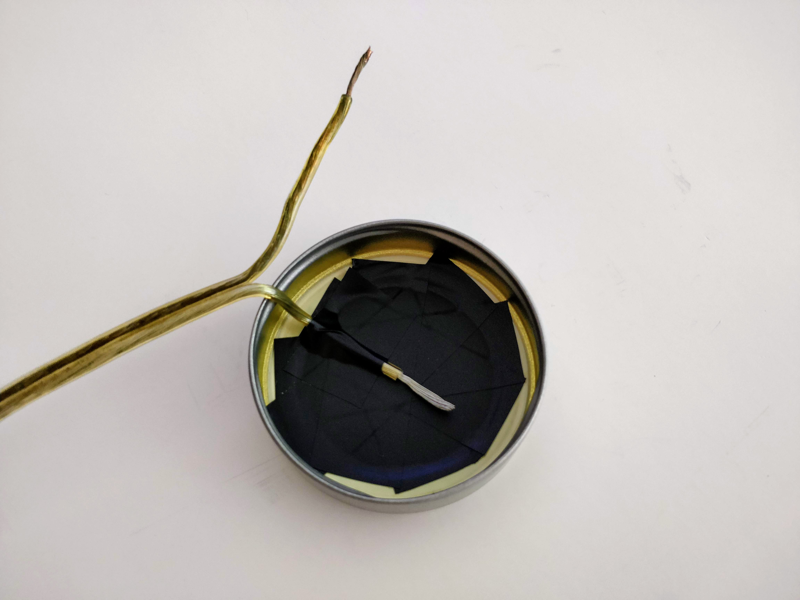
Measurements/WaveForms/Experiments/AmplifiedSignalMagnetYeast/IMG_20190823_113858.jpg
