andrasfuchs/BioBalanceDetector/Measurements/WaveForms/Experiments/AmplifiedSignalMagnetYeast/IMG_20190823_114153.jpg

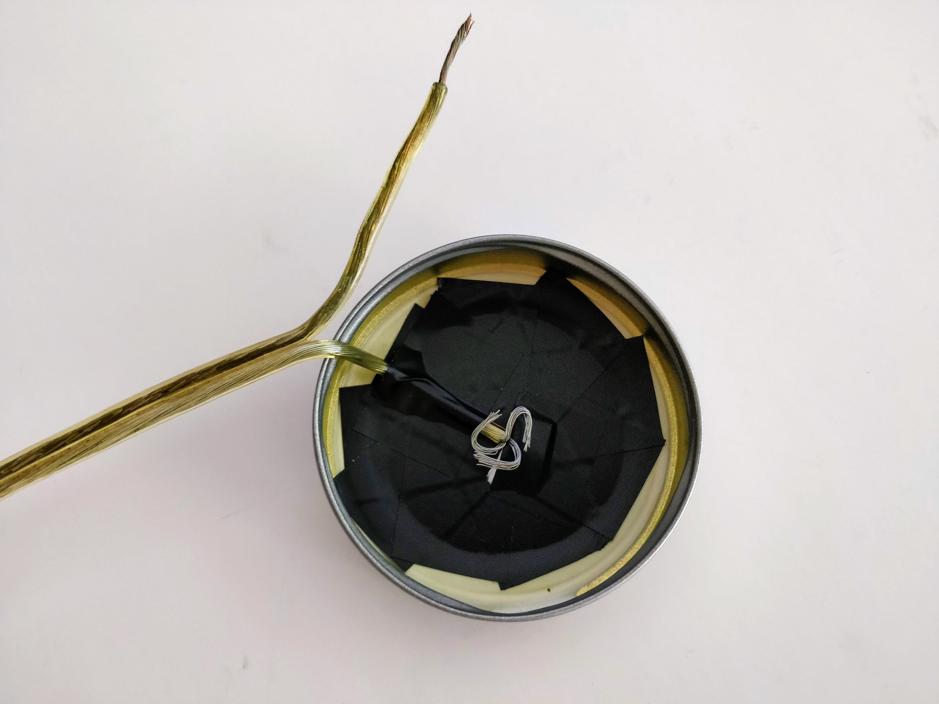
Measurements/WaveForms/Experiments/AmplifiedSignalMagnetYeast/IMG_20190823_114153.jpg
