andrasfuchs/BioBalanceDetector/Measurements/WaveForms/Experiments/AmplifiedSignalMagnetYeast/IMG_20190823_114414.jpg

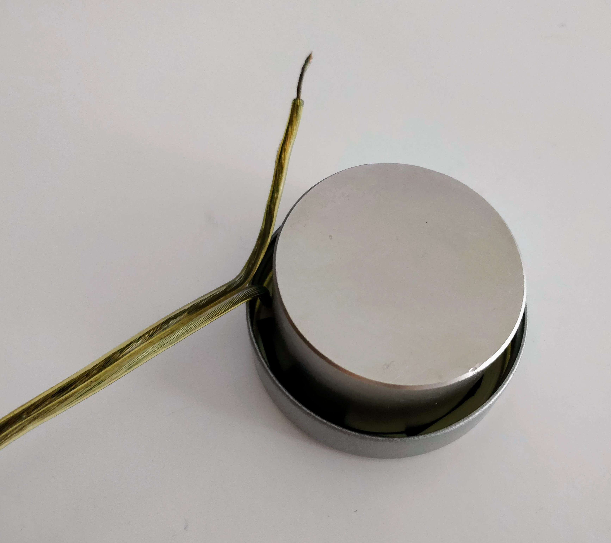
Measurements/WaveForms/Experiments/AmplifiedSignalMagnetYeast/IMG_20190823_114414.jpg
