andrasfuchs/BioBalanceDetector/Measurements/WaveForms/Experiments/AmplifierSignalGain/CaseA_AD2Direct.png

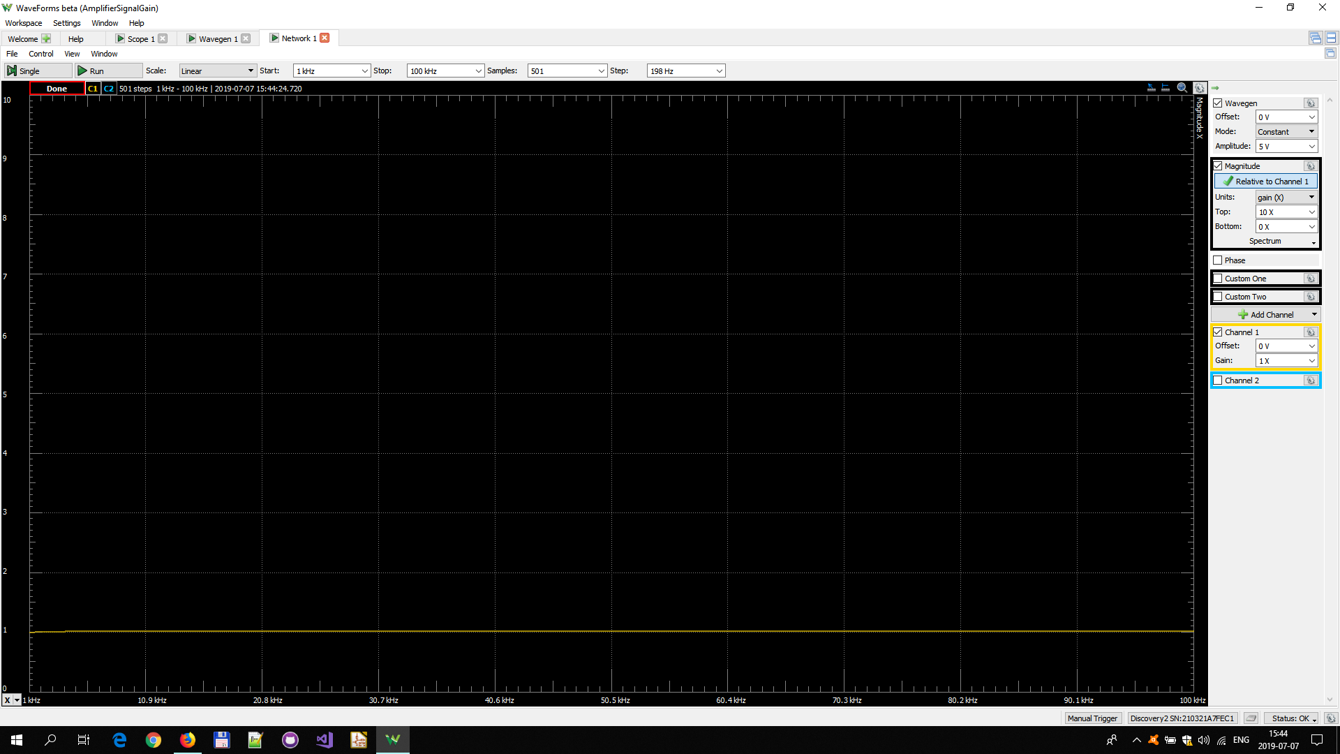
Measurements/WaveForms/Experiments/AmplifierSignalGain/CaseA_AD2Direct.png
