andrasfuchs/BioBalanceDetector/Measurements/WaveForms/Experiments/AmplifierSignalGain/CaseB.png

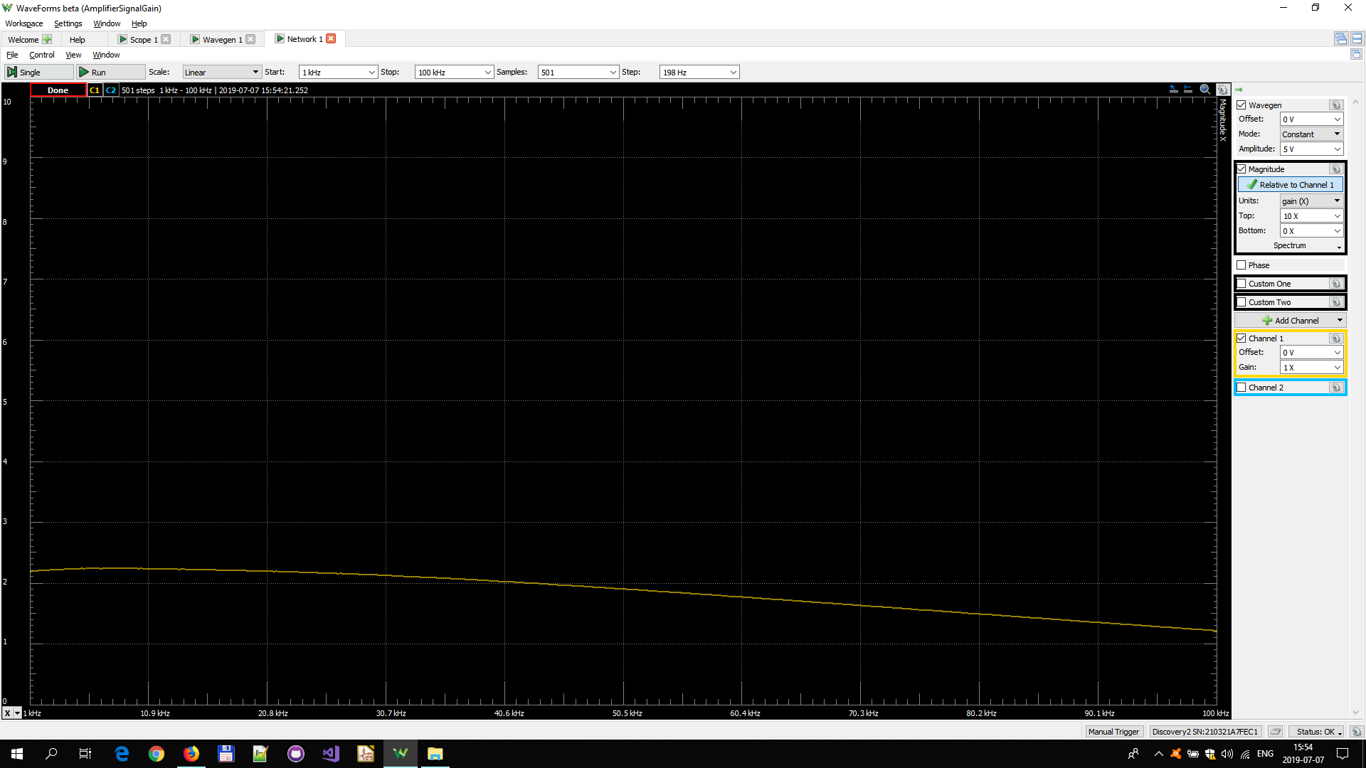
Measurements/WaveForms/Experiments/AmplifierSignalGain/CaseB.png
