andrasfuchs/BioBalanceDetector/Measurements/WaveForms/Experiments/AmplifierSignalGain/CaseC.png

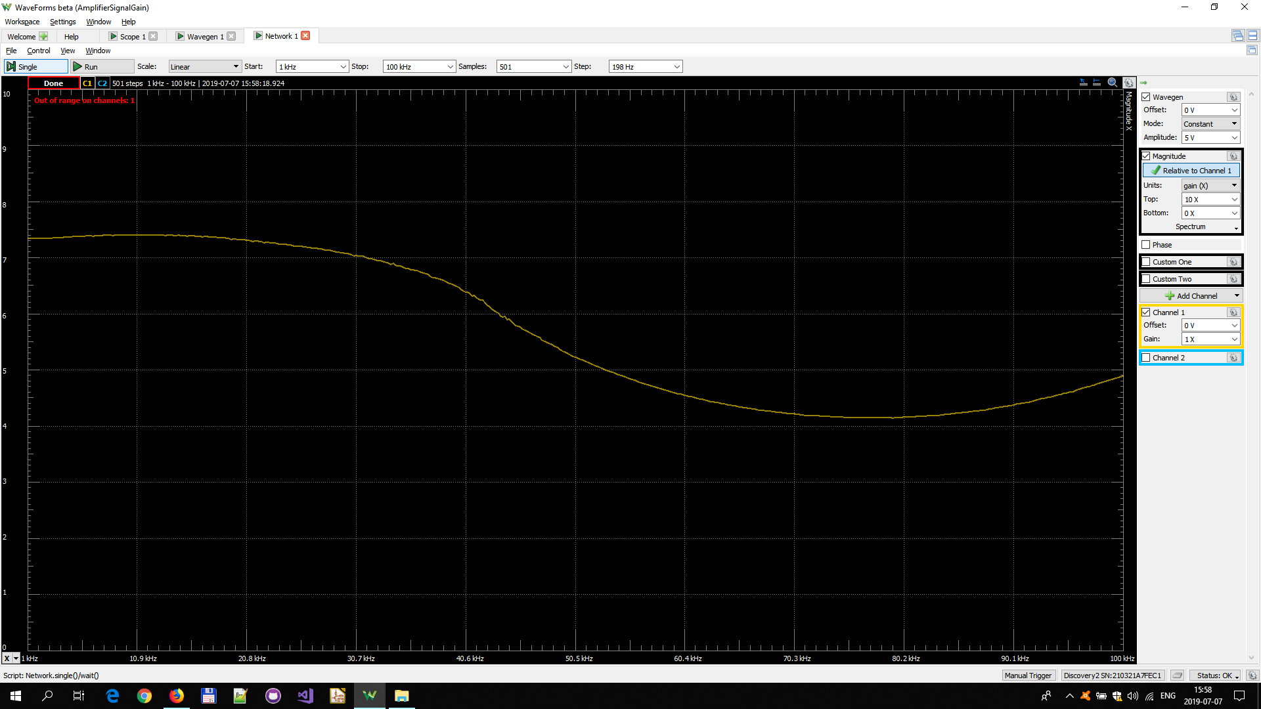
Measurements/WaveForms/Experiments/AmplifierSignalGain/CaseC.png
