andrasfuchs/BioBalanceDetector/Measurements/WaveForms/Experiments/AmplifierSignalGain/CaseD.png

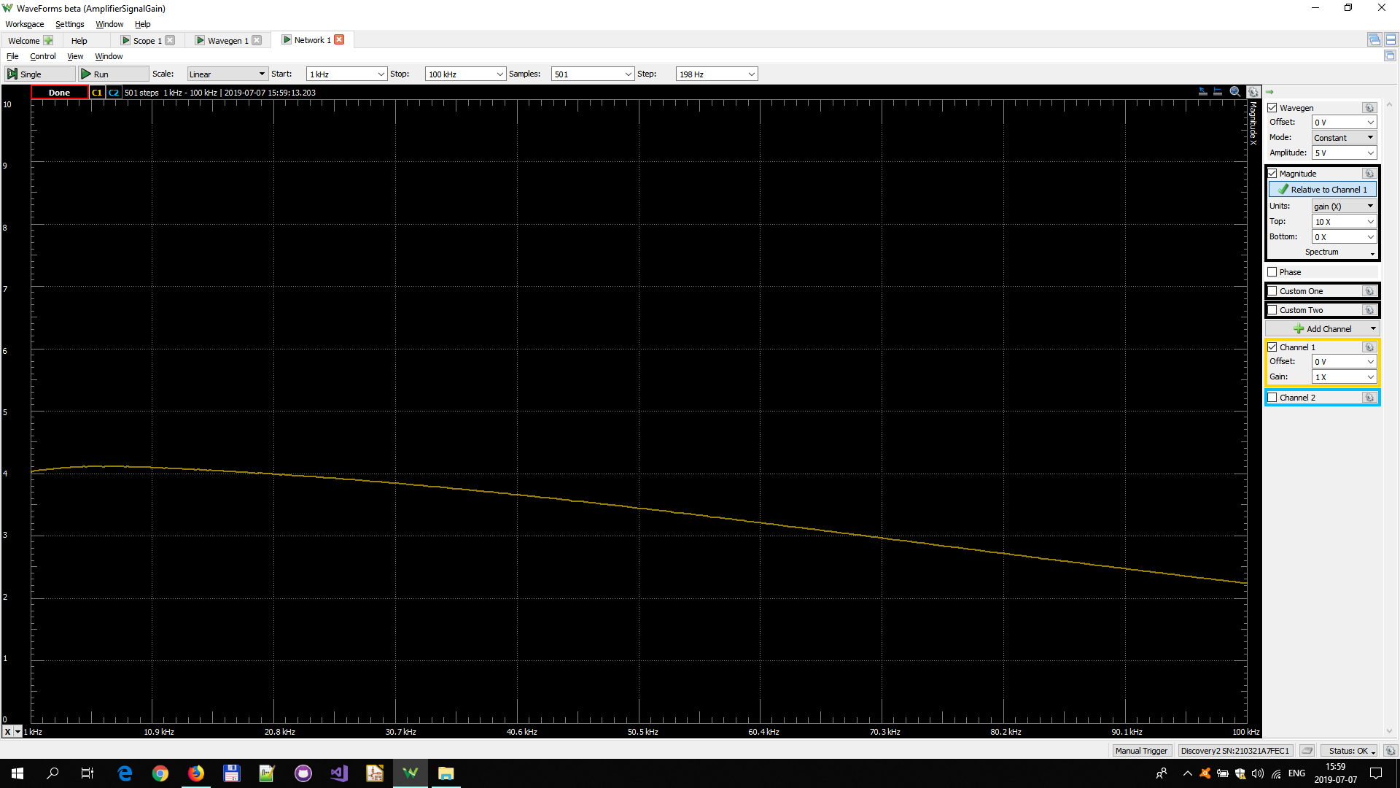
Measurements/WaveForms/Experiments/AmplifierSignalGain/CaseD.png
