andrasfuchs/BioBalanceDetector/Measurements/WaveForms/Experiments/AmplifierSignalGain/CaseE.png

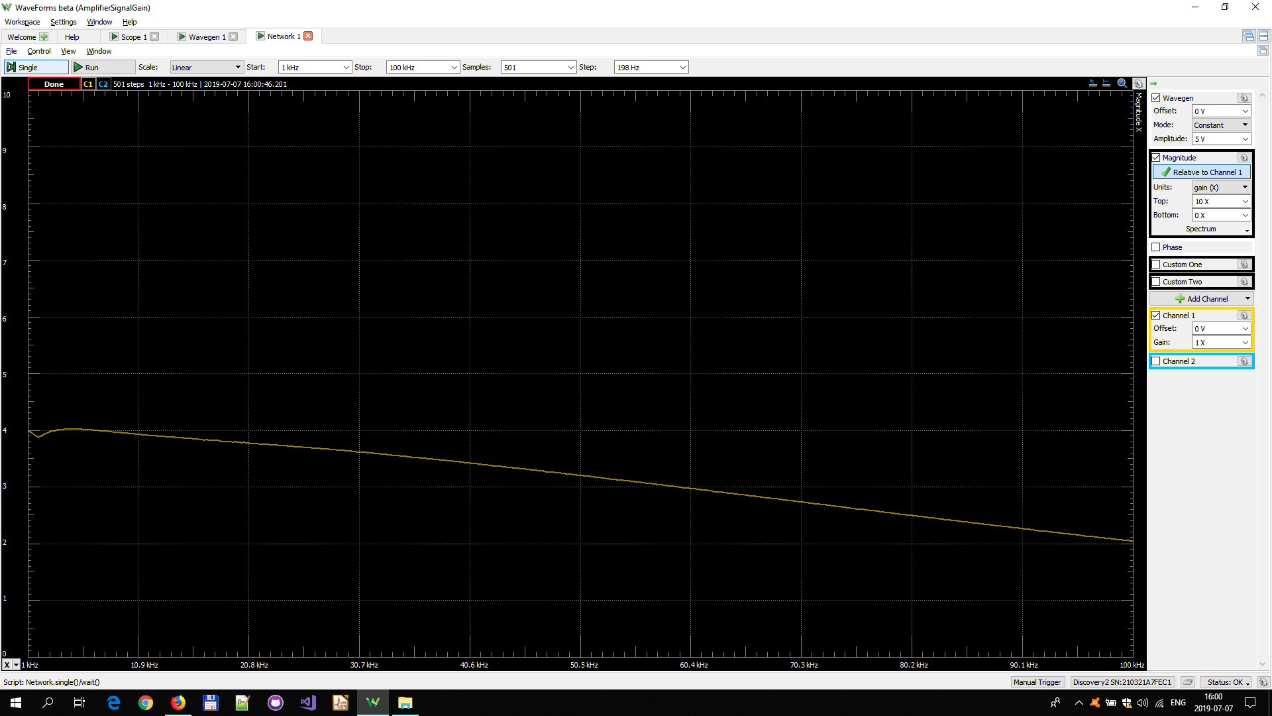
Measurements/WaveForms/Experiments/AmplifierSignalGain/CaseE.png
