andrasfuchs/BioBalanceDetector/Measurements/WaveForms/Experiments/AmplifierSignalGain/CaseF.png

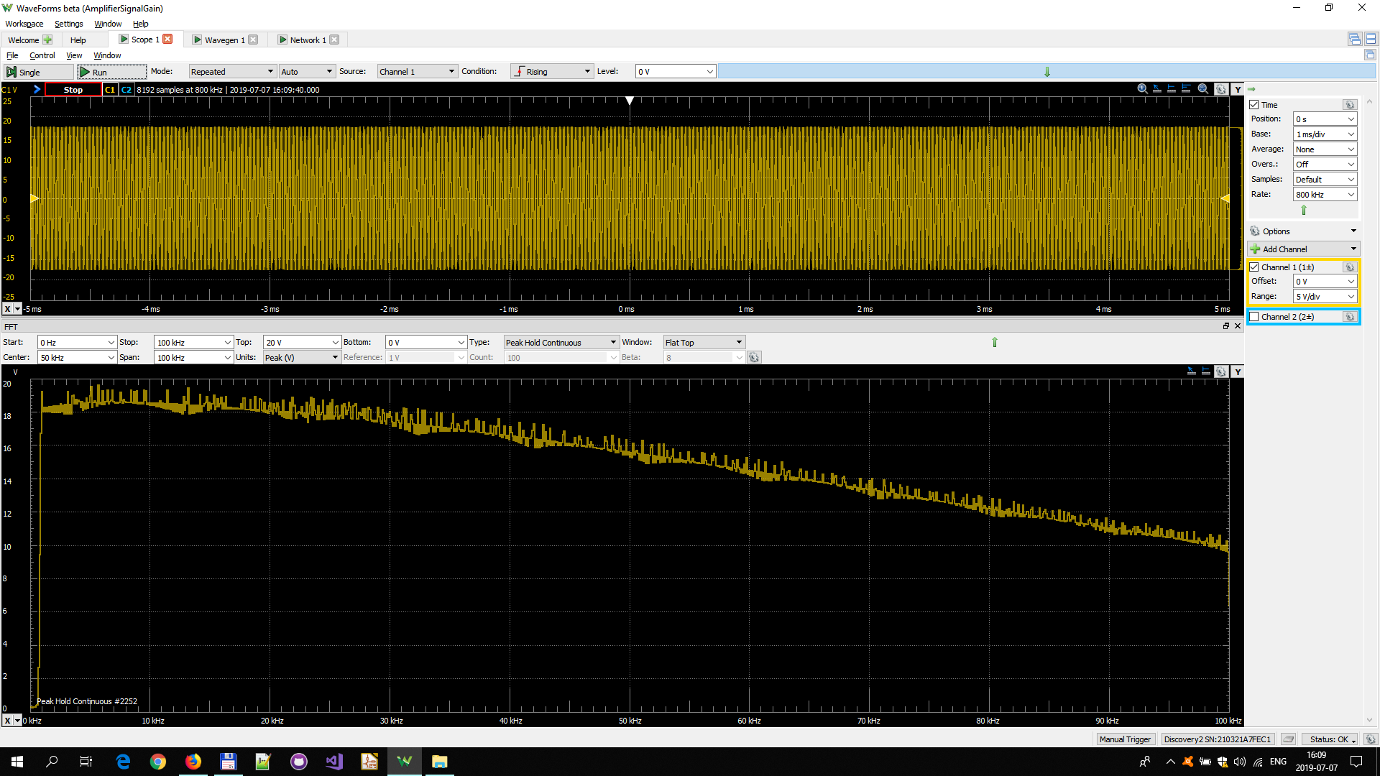
Measurements/WaveForms/Experiments/AmplifierSignalGain/CaseF.png
