andrasfuchs/BioBalanceDetector/Measurements/WaveForms/Experiments/Bemer/B.Body.jpg

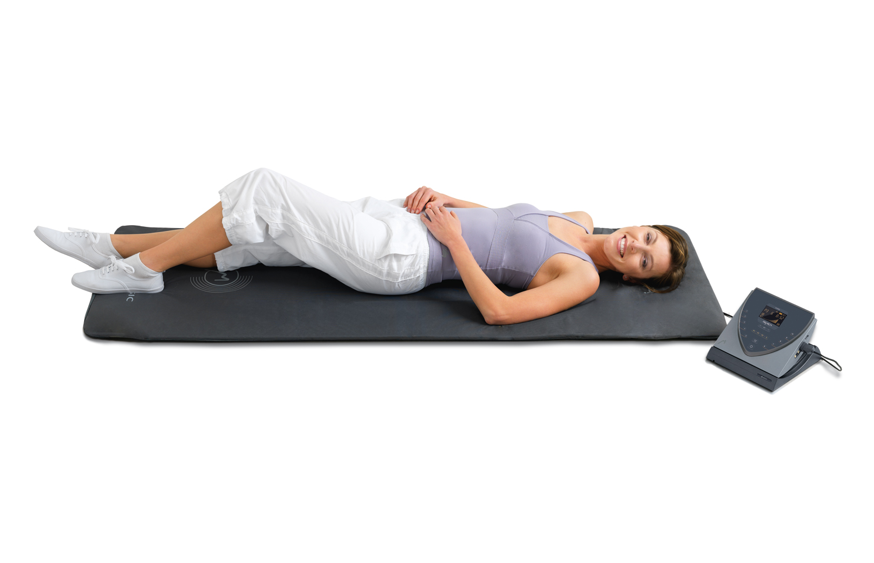
Measurements/WaveForms/Experiments/Bemer/B.Body.jpg
