andrasfuchs/BioBalanceDetector/Measurements/WaveForms/Experiments/Bemer/B.Spot.jpg

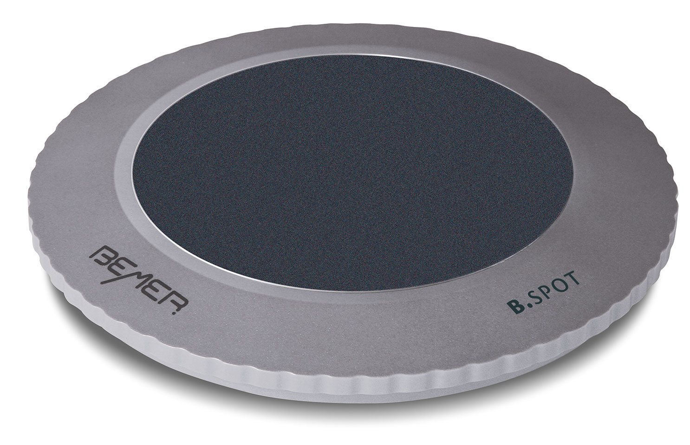
Measurements/WaveForms/Experiments/Bemer/B.Spot.jpg
