andrasfuchs/BioBalanceDetector/Measurements/WaveForms/Experiments/Bemer/Bemer_Classic-Set.png

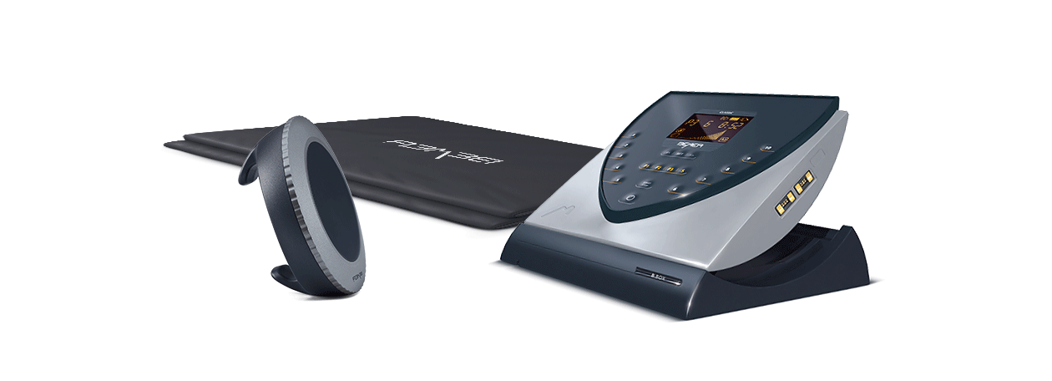
Measurements/WaveForms/Experiments/Bemer/Bemer_Classic-Set.png
