andrasfuchs/BioBalanceDetector/Measurements/WaveForms/Experiments/FluidImpedanceProfiles/AmplitudeTests/FluidImpedanceProfiles_20190304_CarbonFilteredWater_010mV.png

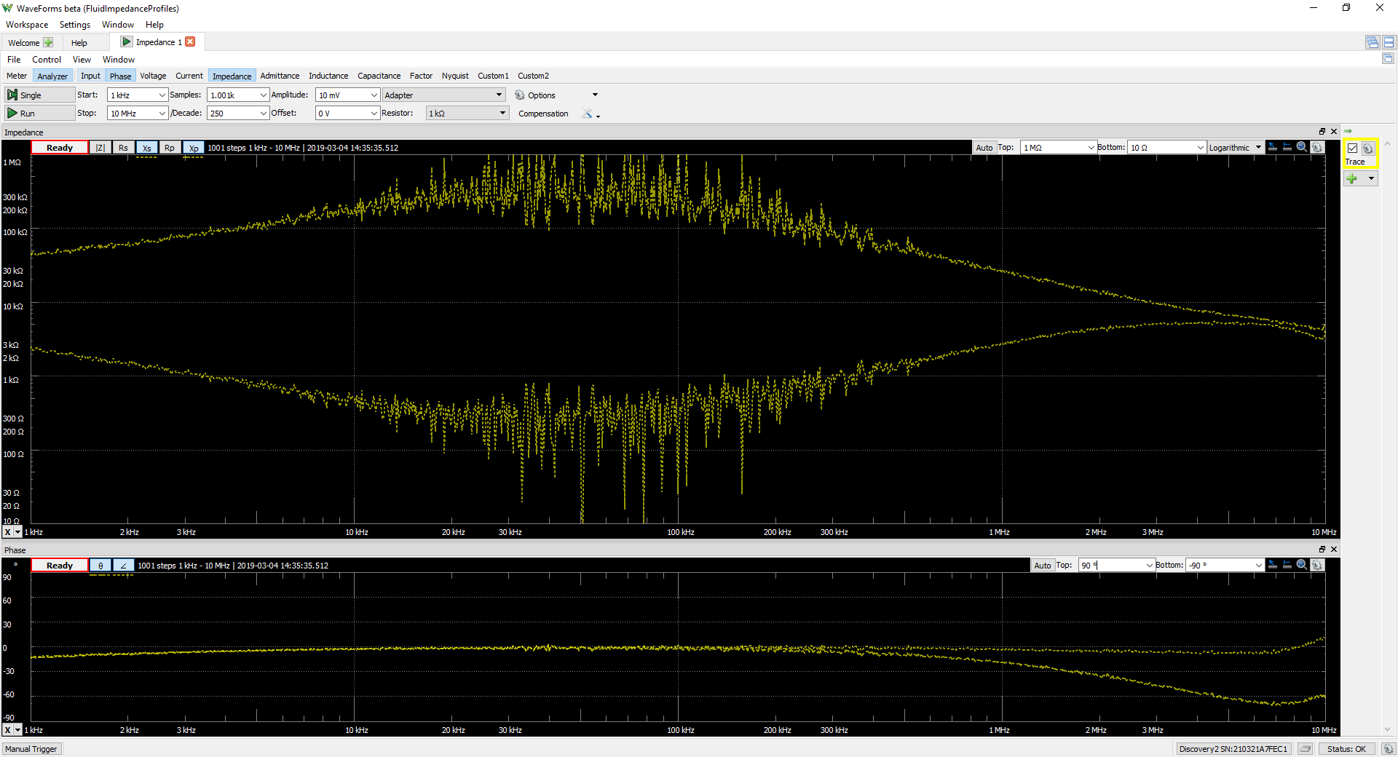
Measurements/WaveForms/Experiments/FluidImpedanceProfiles/AmplitudeTests/FluidImpedanceProfiles_20190304_CarbonFilteredWater_010mV.png
