andrasfuchs/BioBalanceDetector/Measurements/WaveForms/Experiments/FluidImpedanceProfiles/ConsistencyTest/FluidImpedanceProfiles_20190304_CarbonFilteredSaltyWater_R0010_A.png

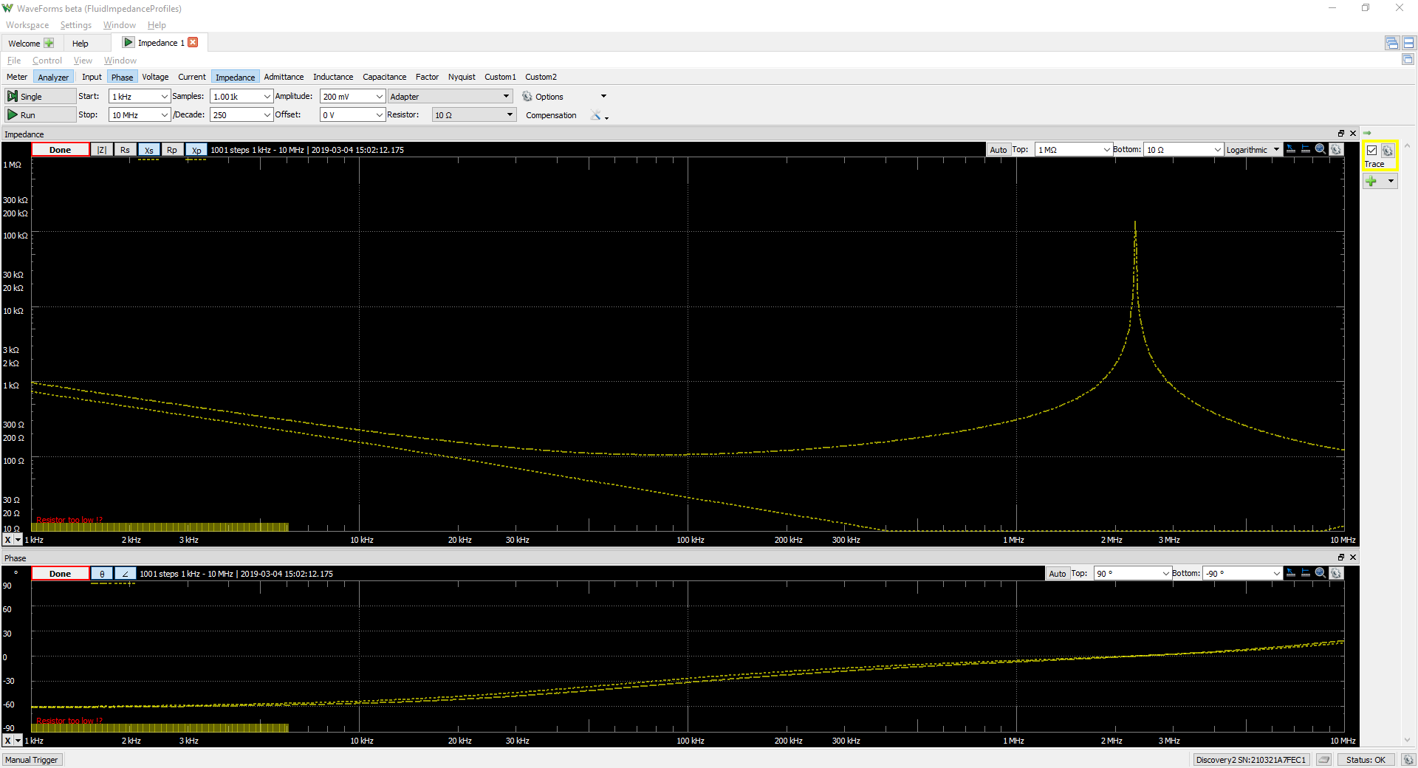
Measurements/WaveForms/Experiments/FluidImpedanceProfiles/ConsistencyTest/FluidImpedanceProfiles_20190304_CarbonFilteredSaltyWater_R0010_A.png
