andrasfuchs/BioBalanceDetector/Measurements/WaveForms/Experiments/FluidImpedanceProfiles/ConsistencyTest/FluidImpedanceProfiles_20190304_CarbonFilteredSaltyWater_R0100_B.png

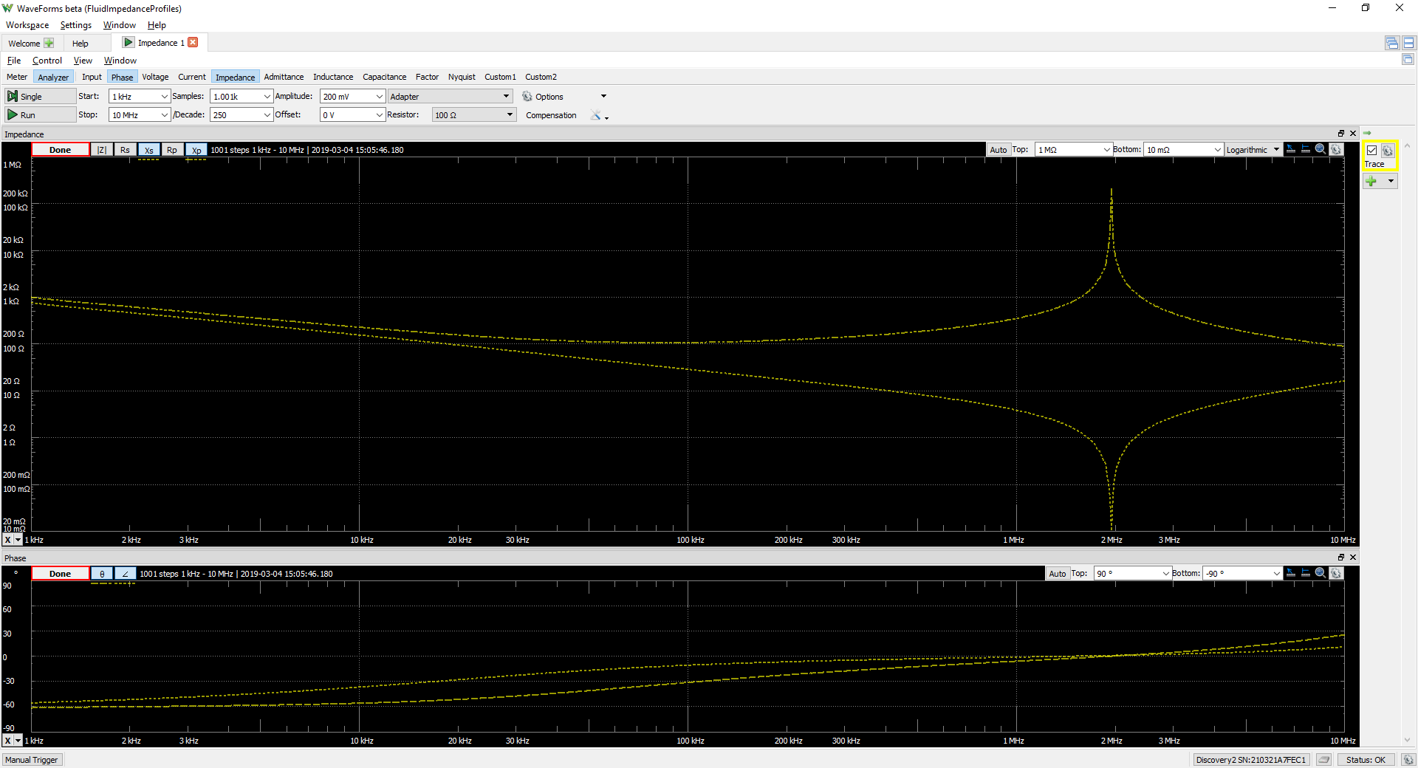
Measurements/WaveForms/Experiments/FluidImpedanceProfiles/ConsistencyTest/FluidImpedanceProfiles_20190304_CarbonFilteredSaltyWater_R0100_B.png
