andrasfuchs/BioBalanceDetector/Measurements/WaveForms/Experiments/FluidImpedanceProfiles/ConsistencyTest/FluidImpedanceProfiles_20190304_CarbonFilteredSaltyWater_R1000_A.png

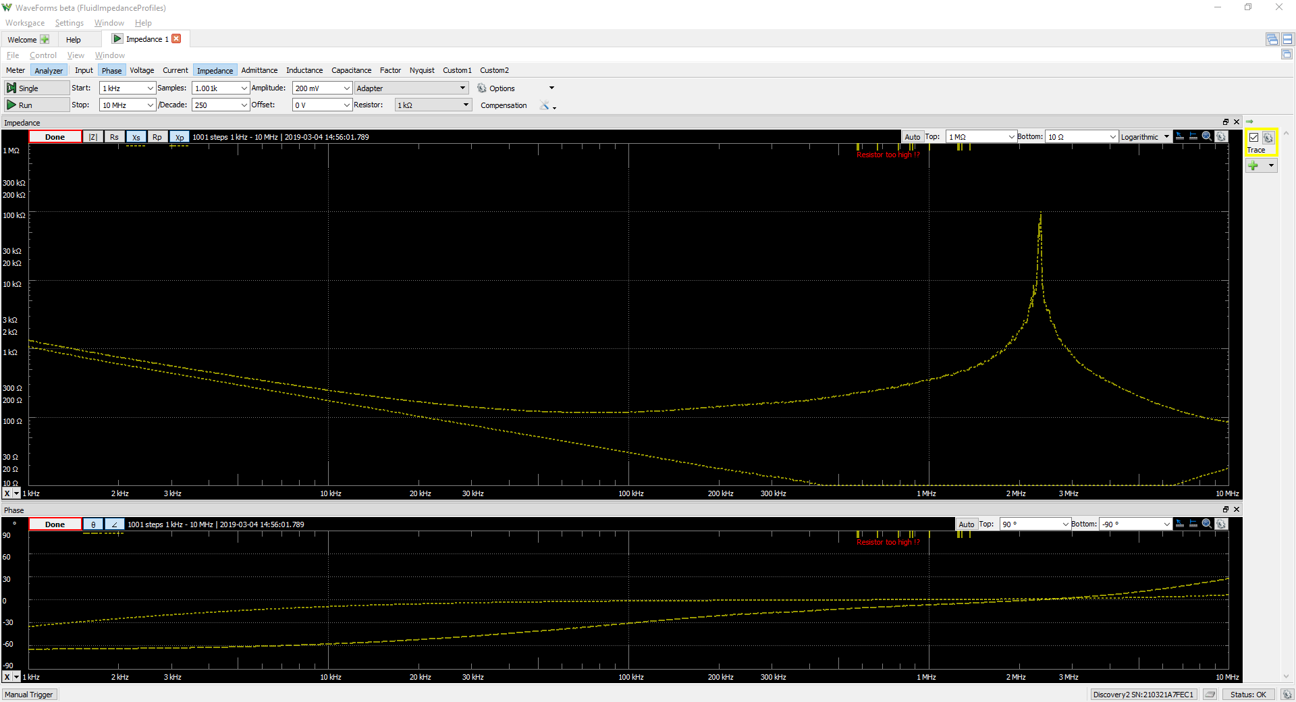
Measurements/WaveForms/Experiments/FluidImpedanceProfiles/ConsistencyTest/FluidImpedanceProfiles_20190304_CarbonFilteredSaltyWater_R1000_A.png
