andrasfuchs/BioBalanceDetector/Measurements/WaveForms/Experiments/FluidImpedanceProfiles/ElectrodesInCeramicContainer.jpg

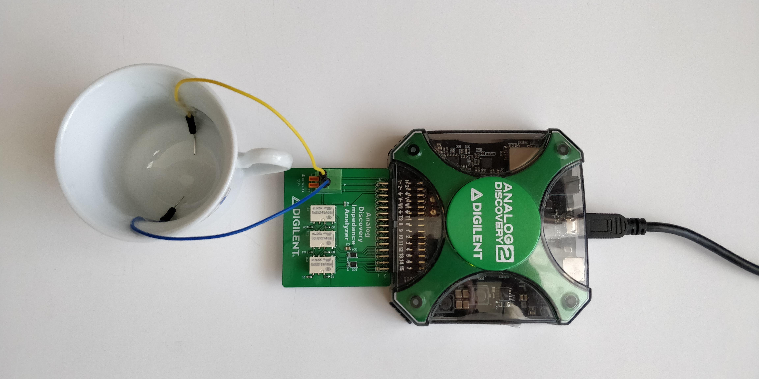
Measurements/WaveForms/Experiments/FluidImpedanceProfiles/ElectrodesInCeramicContainer.jpg
