andrasfuchs/BioBalanceDetector/Measurements/WaveForms/Experiments/FluidImpedanceProfiles/FluidImpedanceProfiles_BrewersYeast_v2.jpg

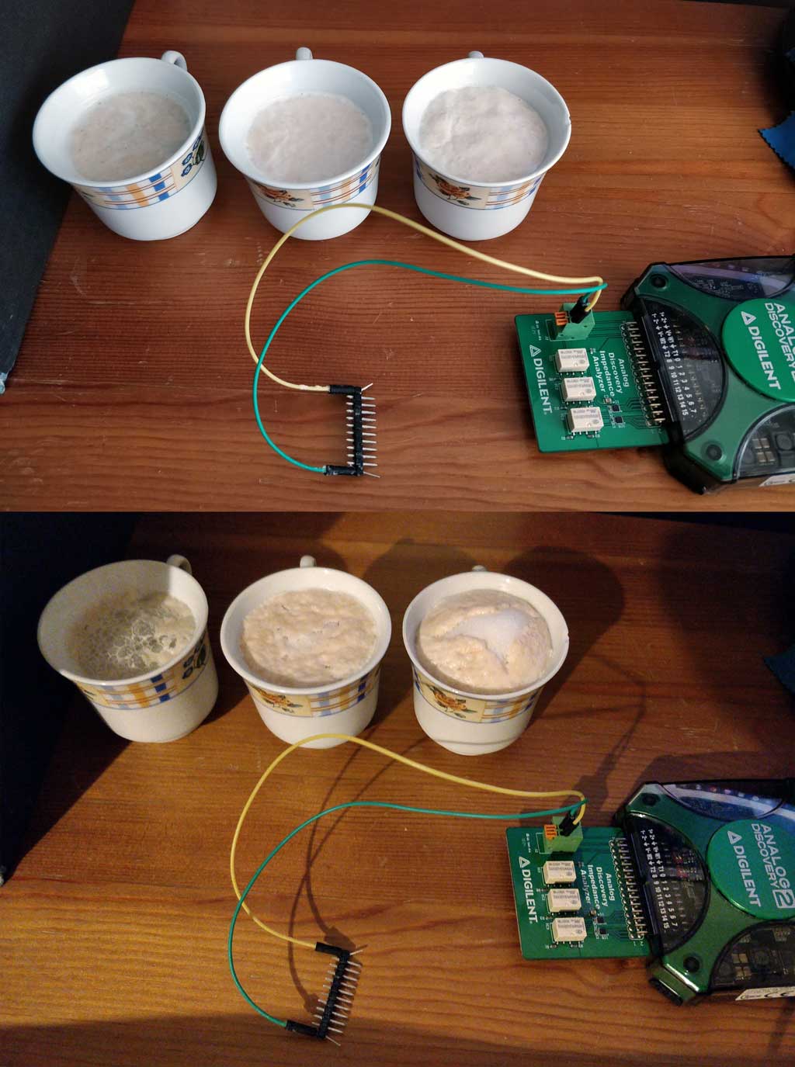
Measurements/WaveForms/Experiments/FluidImpedanceProfiles/FluidImpedanceProfiles_BrewersYeast_v2.jpg
