andrasfuchs/BioBalanceDetector/Measurements/WaveForms/Experiments/FluidImpedanceProfiles/FluidImpedanceProfiles_WaterAtDifferentTemperatures.png

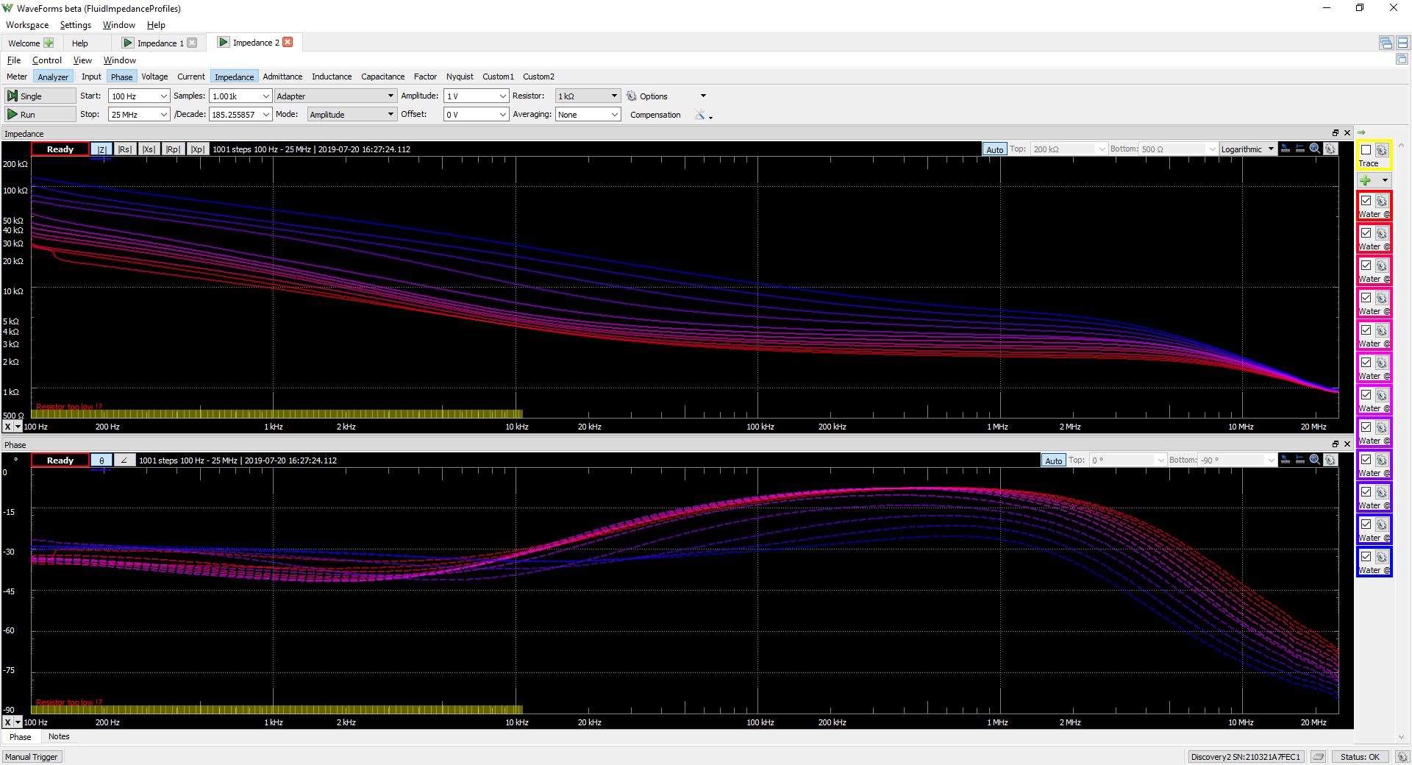
Measurements/WaveForms/Experiments/FluidImpedanceProfiles/FluidImpedanceProfiles_WaterAtDifferentTemperatures.png
