andrasfuchs/BioBalanceDetector/Measurements/WaveForms/Experiments/FluidImpedanceProfiles/HumanFingerTest/FluidImpedanceProfiles_20190304_CarbonFilteredWater_A_AFRightFinger.png

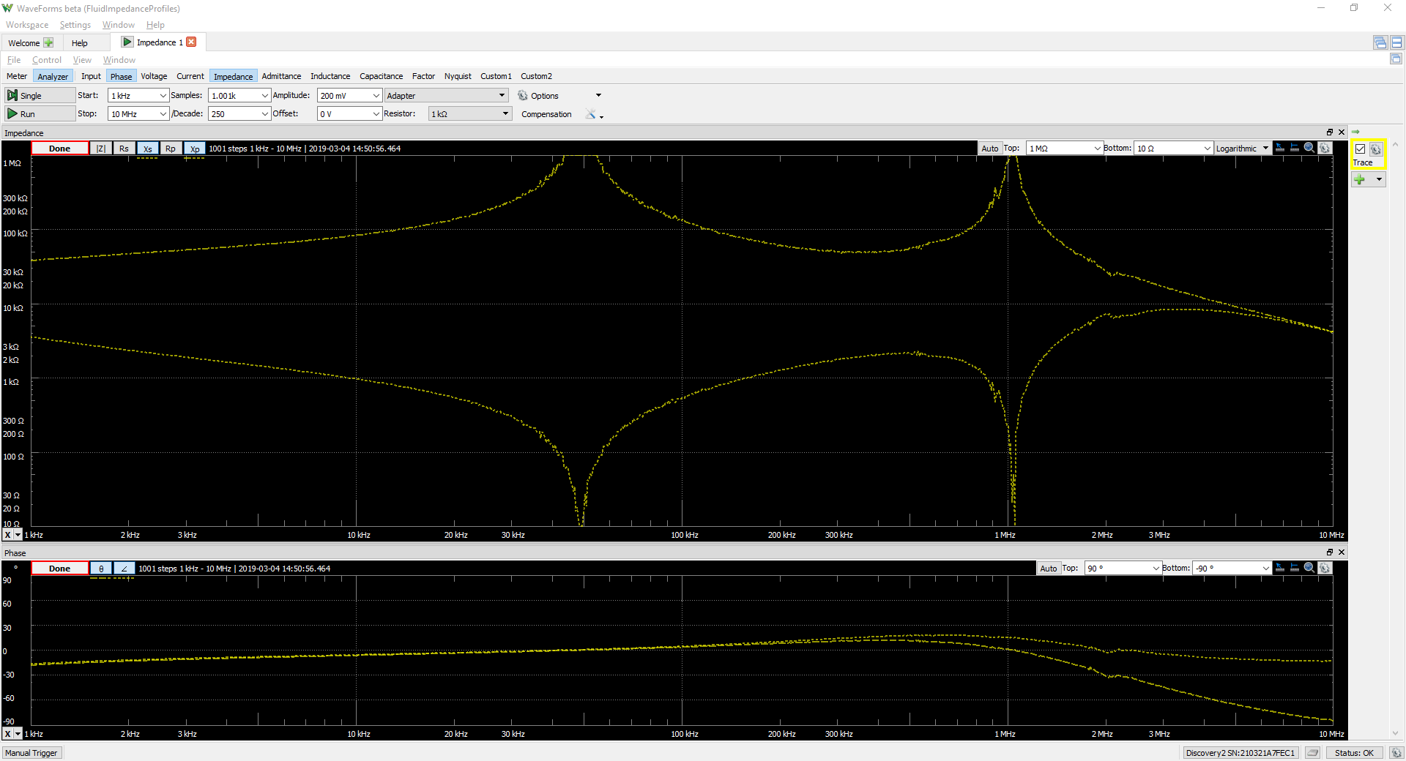
Measurements/WaveForms/Experiments/FluidImpedanceProfiles/HumanFingerTest/FluidImpedanceProfiles_20190304_CarbonFilteredWater_A_AFRightFinger.png
