andrasfuchs/BioBalanceDetector/Measurements/WaveForms/Experiments/FluidImpedanceProfiles/YeastWaterCapacitance/Yeast_170minutes.png

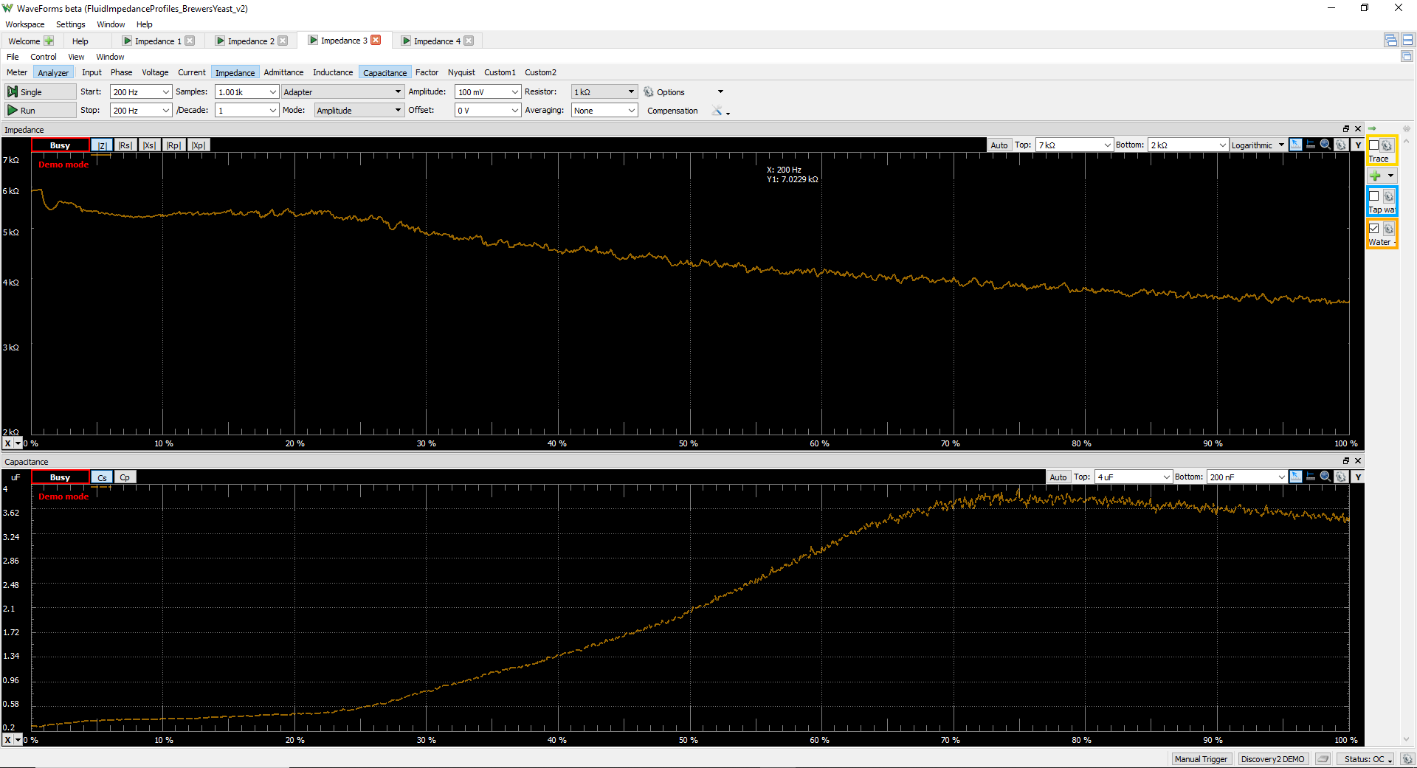
Measurements/WaveForms/Experiments/FluidImpedanceProfiles/YeastWaterCapacitance/Yeast_170minutes.png
