andrasfuchs/BioBalanceDetector/Measurements/WaveForms/Experiments/FluidImpedanceProfiles/YeastWaterCapacitance/YeastWater_3minutes.png

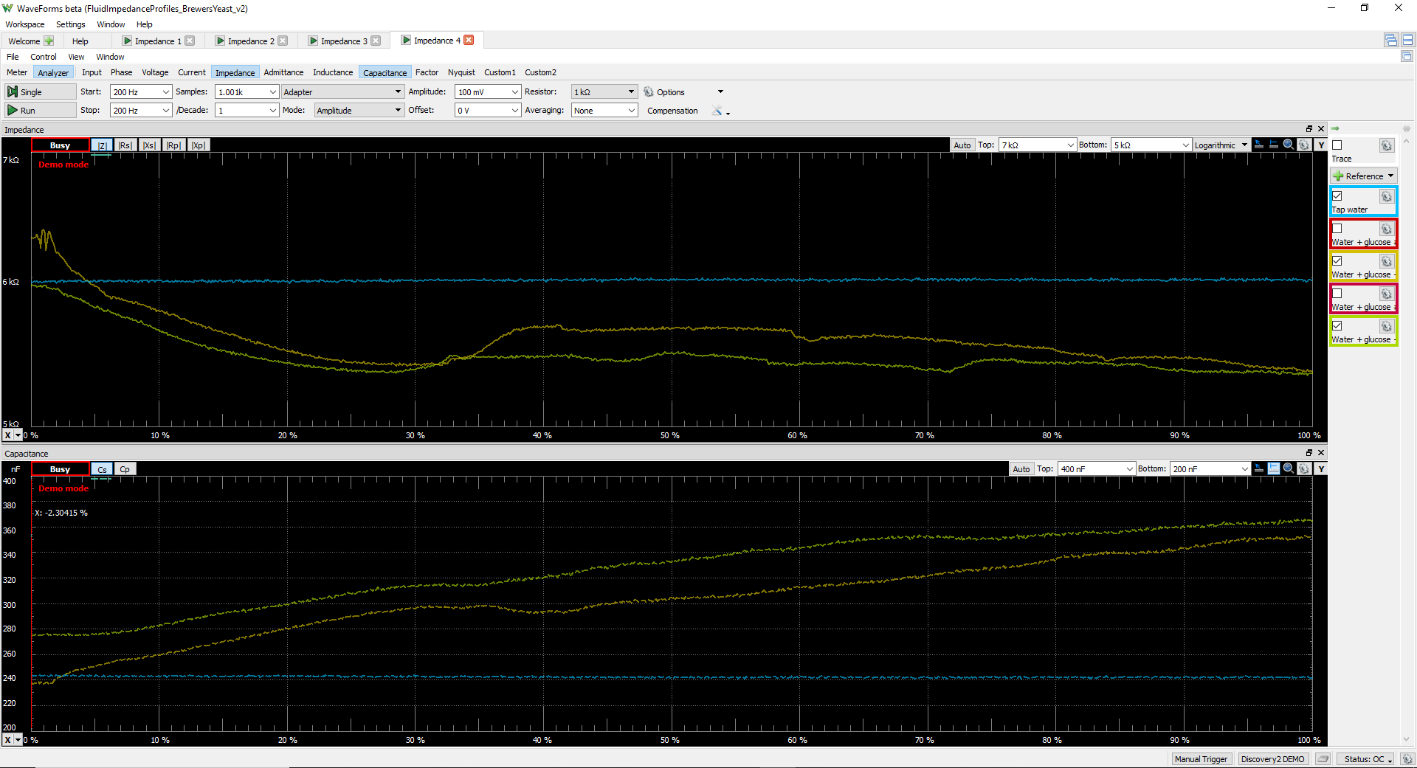
Measurements/WaveForms/Experiments/FluidImpedanceProfiles/YeastWaterCapacitance/YeastWater_3minutes.png
