andrasfuchs/BioBalanceDetector/Measurements/WaveForms/Experiments/Proto01emulator/IMG_20190521_Proto01emulator.jpg

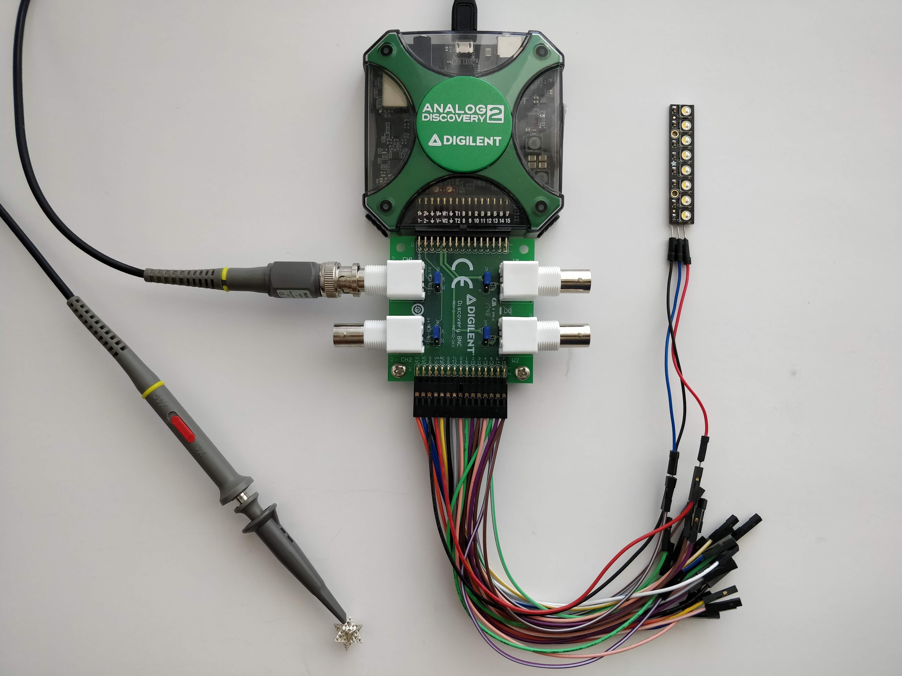
Measurements/WaveForms/Experiments/Proto01emulator/IMG_20190521_Proto01emulator.jpg
