andrasfuchs/BioBalanceDetector/Measurements/WaveForms/Experiments/Proto01emulator/IMG_20190622_PowerOutlet-AllColors.jpg

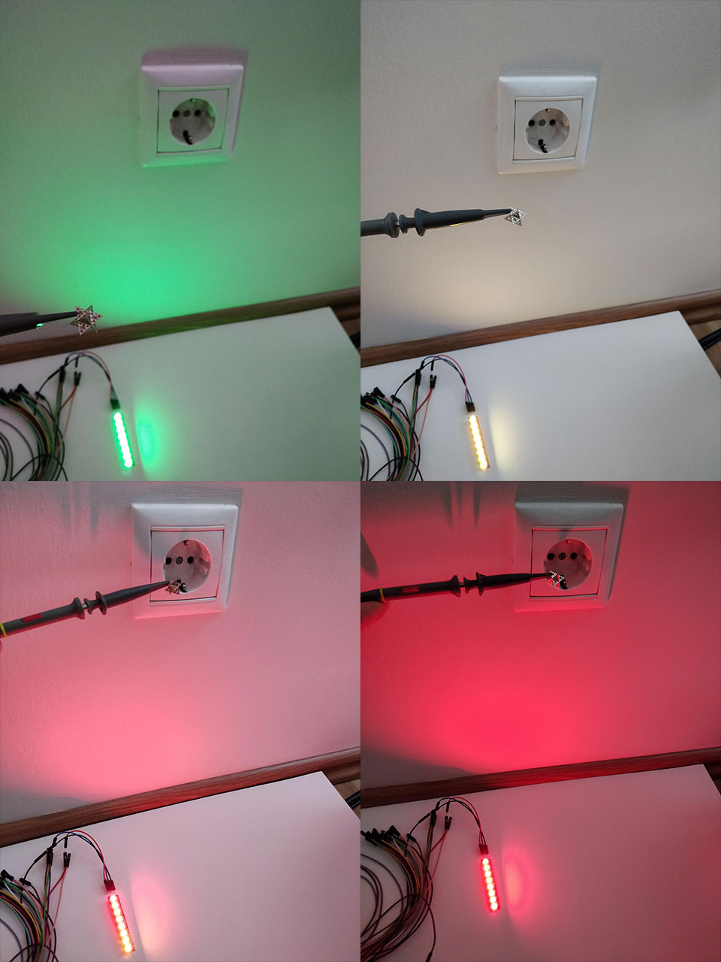
Measurements/WaveForms/Experiments/Proto01emulator/IMG_20190622_PowerOutlet-AllColors.jpg
