andrasfuchs/BioBalanceDetector/Measurements/WaveForms/Experiments/SignalStimulatedYeast/SignalStimulatedYeast_v1.png

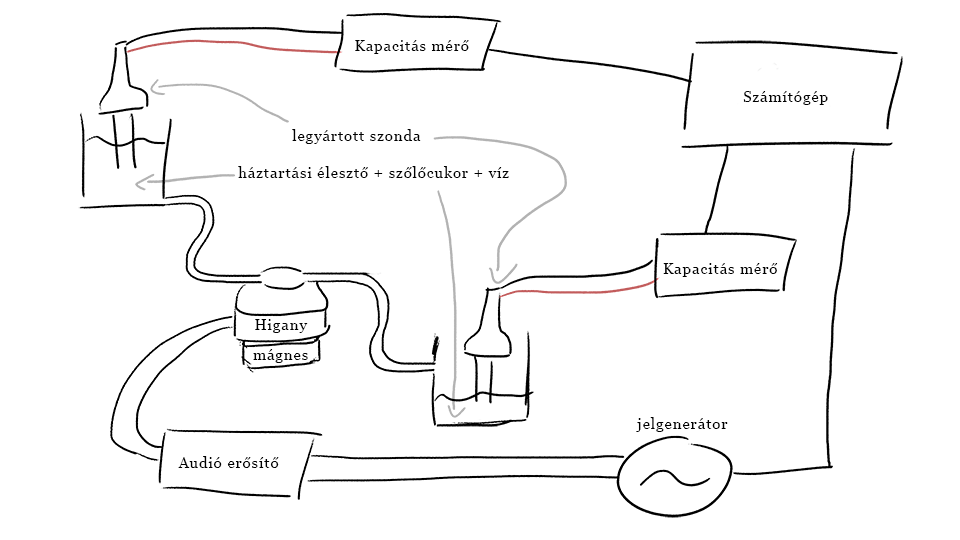
Measurements/WaveForms/Experiments/SignalStimulatedYeast/SignalStimulatedYeast_v1.png
