andrasfuchs/BioBalanceDetector/Measurements/WaveForms/Experiments/SignalStimulatedYeast/SignalStimulatedYeast_v2.png

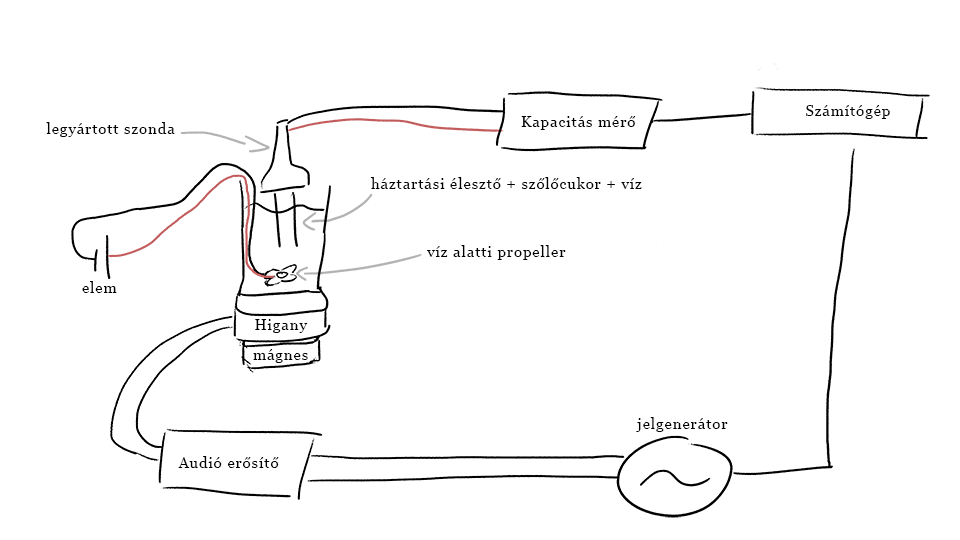
Measurements/WaveForms/Experiments/SignalStimulatedYeast/SignalStimulatedYeast_v2.png
