andrasfuchs/BioBalanceDetector/Measurements/WaveForms/Experiments/SignatureFrequency/v2/SignatureFrequency_AndrasFuchs_20181222-154632_MegszakitoFentAsztalirolHaloszoba.png

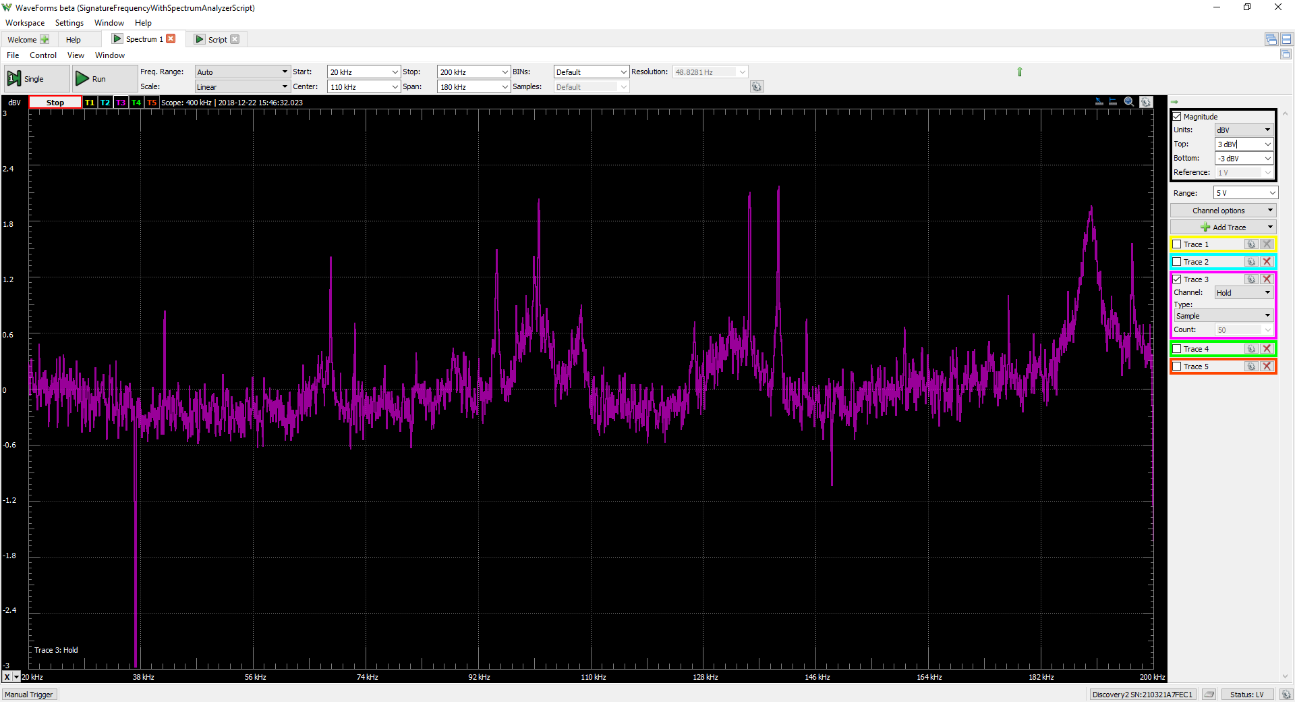
Measurements/WaveForms/Experiments/SignatureFrequency/v2/SignatureFrequency_AndrasFuchs_20181222-154632_MegszakitoFentAsztalirolHaloszoba.png
