andrasfuchs/BioBalanceDetector/Measurements/WaveForms/Experiments/SignatureFrequency/v2/SignatureFrequency_AndrasFuchs_20181222-155144_MegszakitoFentAsztalirolHaloszoba.png

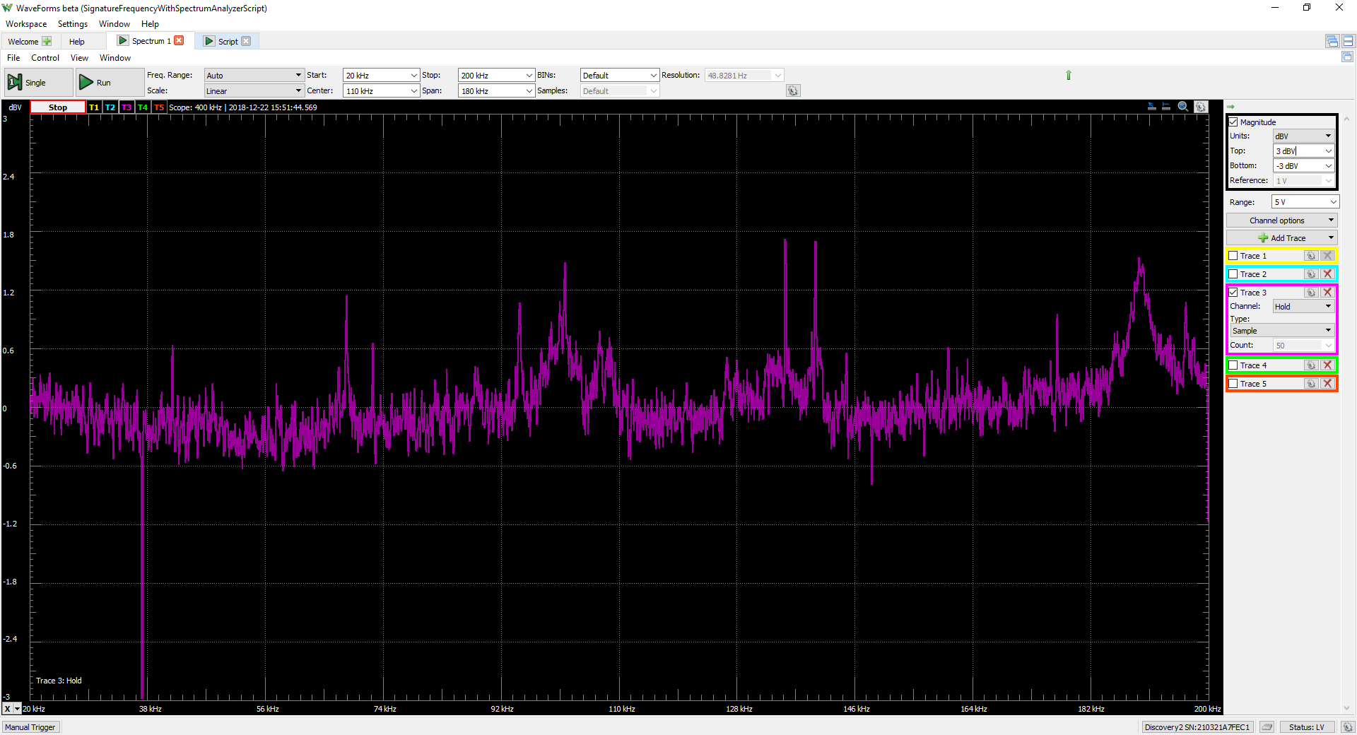
Measurements/WaveForms/Experiments/SignatureFrequency/v2/SignatureFrequency_AndrasFuchs_20181222-155144_MegszakitoFentAsztalirolHaloszoba.png
