andrasfuchs/BioBalanceDetector/Measurements/WaveForms/Experiments/SimpleNetworkAnalyzer/CrystalTest/SimpleNetworkAnalyzer_20190304_A_DirectlyConnected.png

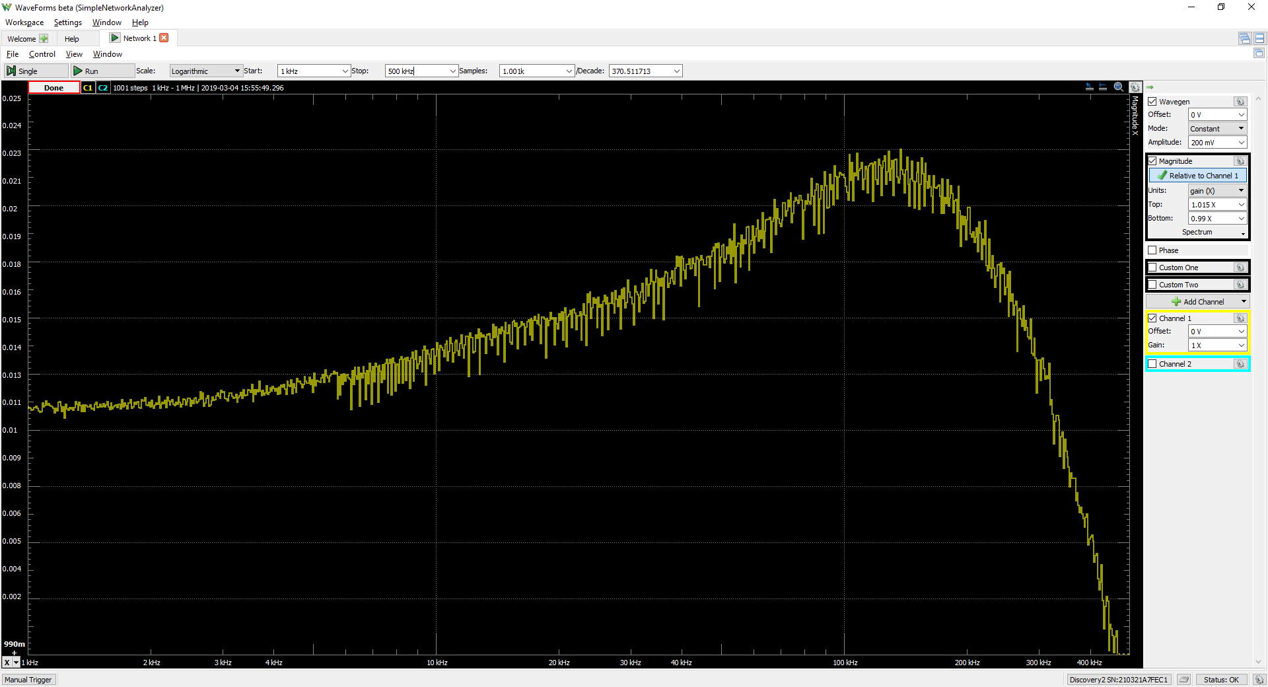
Measurements/WaveForms/Experiments/SimpleNetworkAnalyzer/CrystalTest/SimpleNetworkAnalyzer_20190304_A_DirectlyConnected.png
