andrasfuchs/BioBalanceDetector/Measurements/WaveForms/Experiments/SimpleNetworkAnalyzer/CrystalTest/SimpleNetworkAnalyzer_20190304_B_CarbonFilteredSaltyWater.png

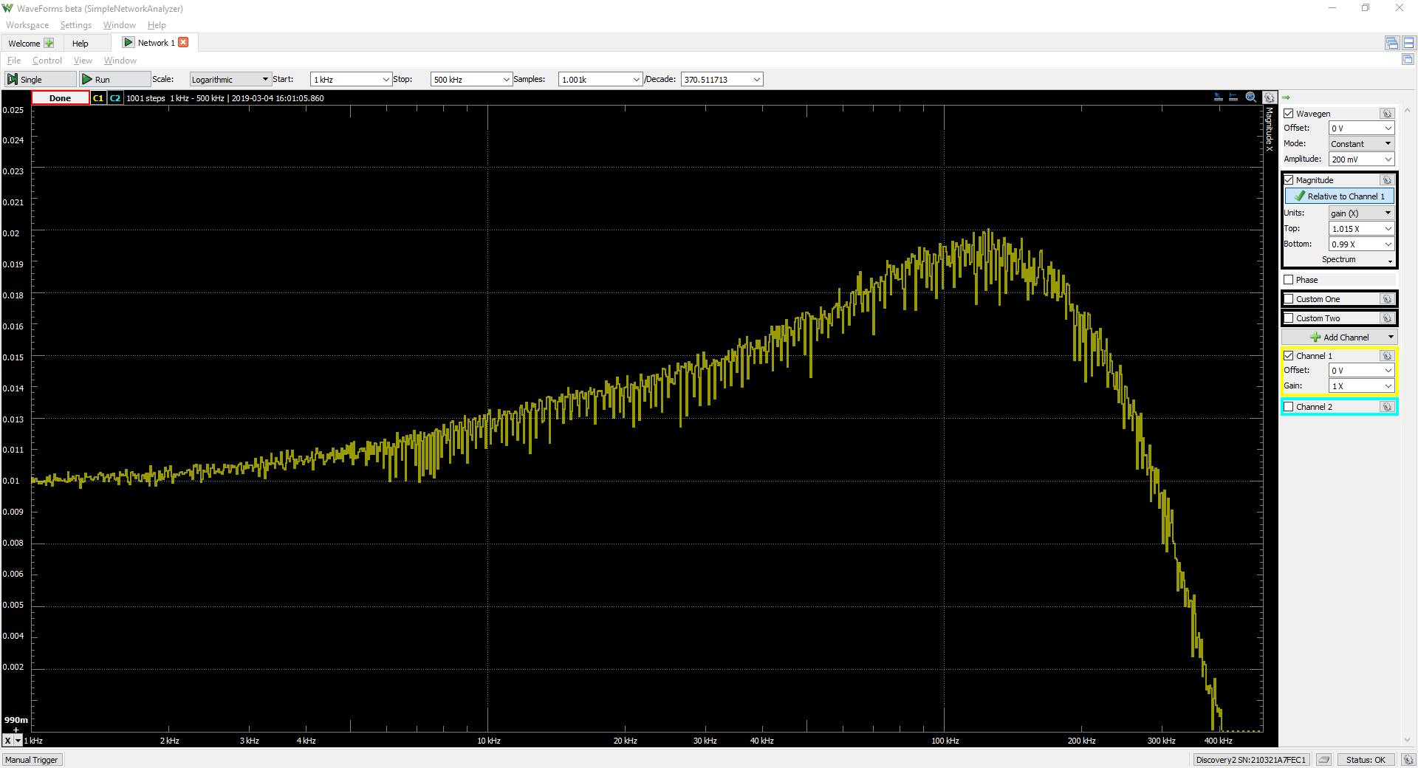
Measurements/WaveForms/Experiments/SimpleNetworkAnalyzer/CrystalTest/SimpleNetworkAnalyzer_20190304_B_CarbonFilteredSaltyWater.png
