andrasfuchs/BioBalanceDetector/Measurements/WaveForms/Experiments/SimpleNetworkAnalyzer/CrystalTest/SimpleNetworkAnalyzer_20190304_D_AFLeftFinger.png

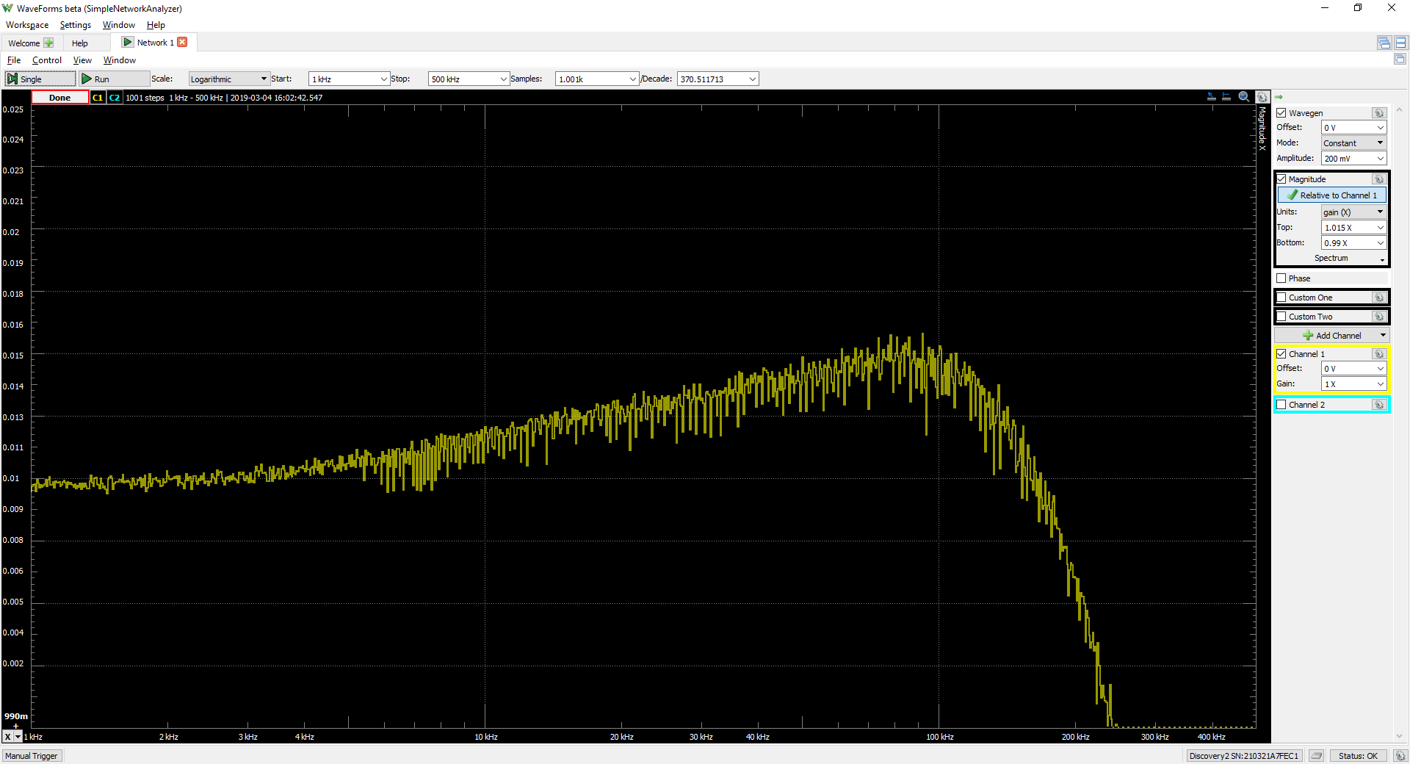
Measurements/WaveForms/Experiments/SimpleNetworkAnalyzer/CrystalTest/SimpleNetworkAnalyzer_20190304_D_AFLeftFinger.png
