andrasfuchs/BioBalanceDetector/Measurements/WaveForms/Experiments/SimpleNetworkAnalyzer/IMG_20190304_155727.jpg

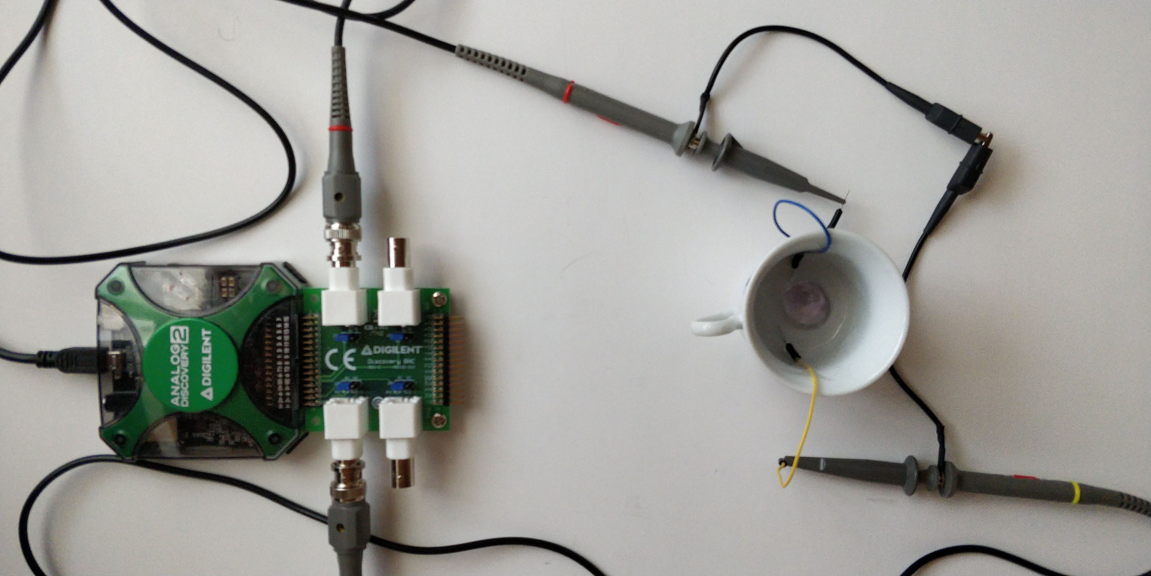
Measurements/WaveForms/Experiments/SimpleNetworkAnalyzer/IMG_20190304_155727.jpg
