andrasfuchs/BioBalanceDetector/Measurements/WaveForms/Experiments/SleepLogging/Meditations/Kundalini_Yoga_-_Chakra_Dhyana/Chakras01.jpg

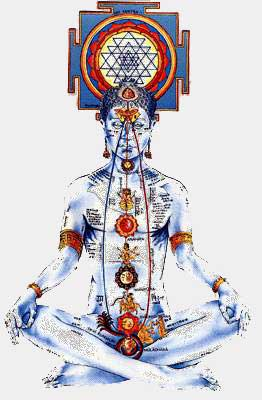
Measurements/WaveForms/Experiments/SleepLogging/Meditations/Kundalini_Yoga_-_Chakra_Dhyana/Chakras01.jpg
