andrasfuchs/BioBalanceDetector/Measurements/WaveForms/Experiments/SleepLogging/Meditations/Kundalini_Yoga_-_Chakra_Dhyana/Chakras02.jpg

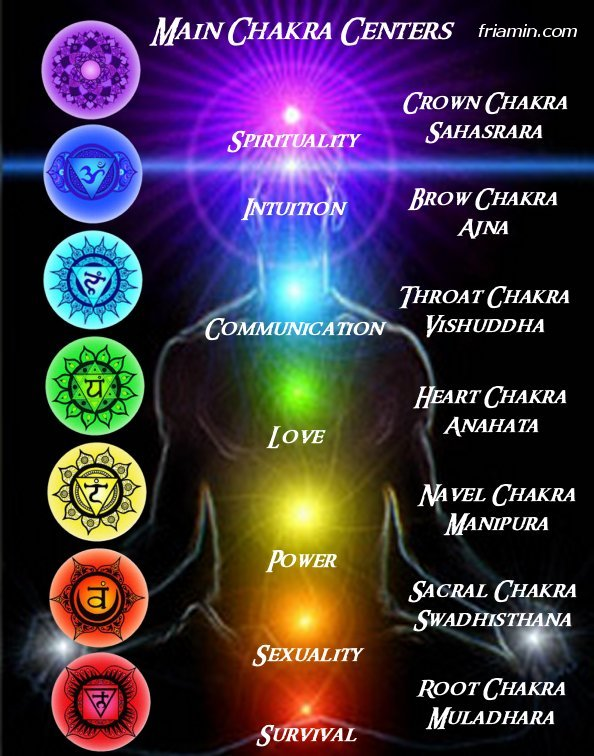
Measurements/WaveForms/Experiments/SleepLogging/Meditations/Kundalini_Yoga_-_Chakra_Dhyana/Chakras02.jpg
