andrasfuchs/BioBalanceDetector/Measurements/WaveForms/Experiments/SleepLogging/Meditations/Kundalini_Yoga_-_Chakra_Dhyana/Chakras06.jpg

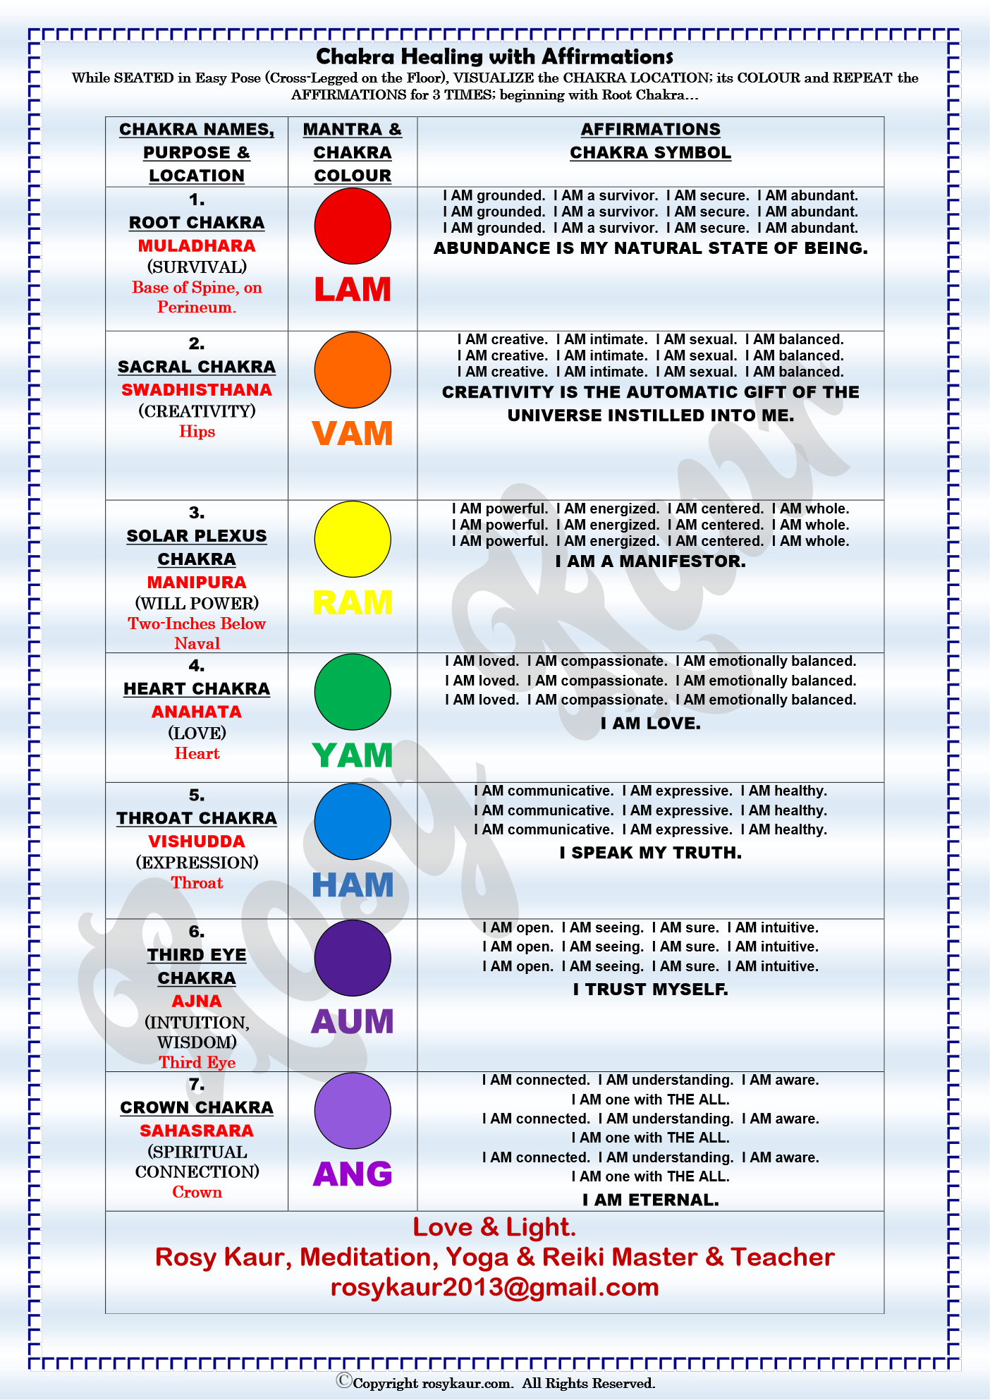
Measurements/WaveForms/Experiments/SleepLogging/Meditations/Kundalini_Yoga_-_Chakra_Dhyana/Chakras06.jpg
