andrasfuchs/BioBalanceDetector/Photos/Proto01/Tests_v3/image-20160119_134415.jpg

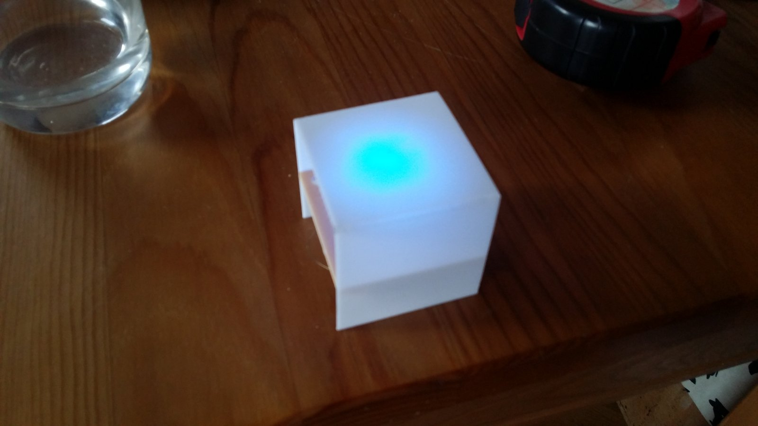
Photos/Proto01/Tests_v3/image-20160119_134415.jpg
