andrasfuchs/BioBalanceDetector/Hardware/Schematics/BBDProto07/Mars-64/HorvathJani-revB/Mars-64.pdf

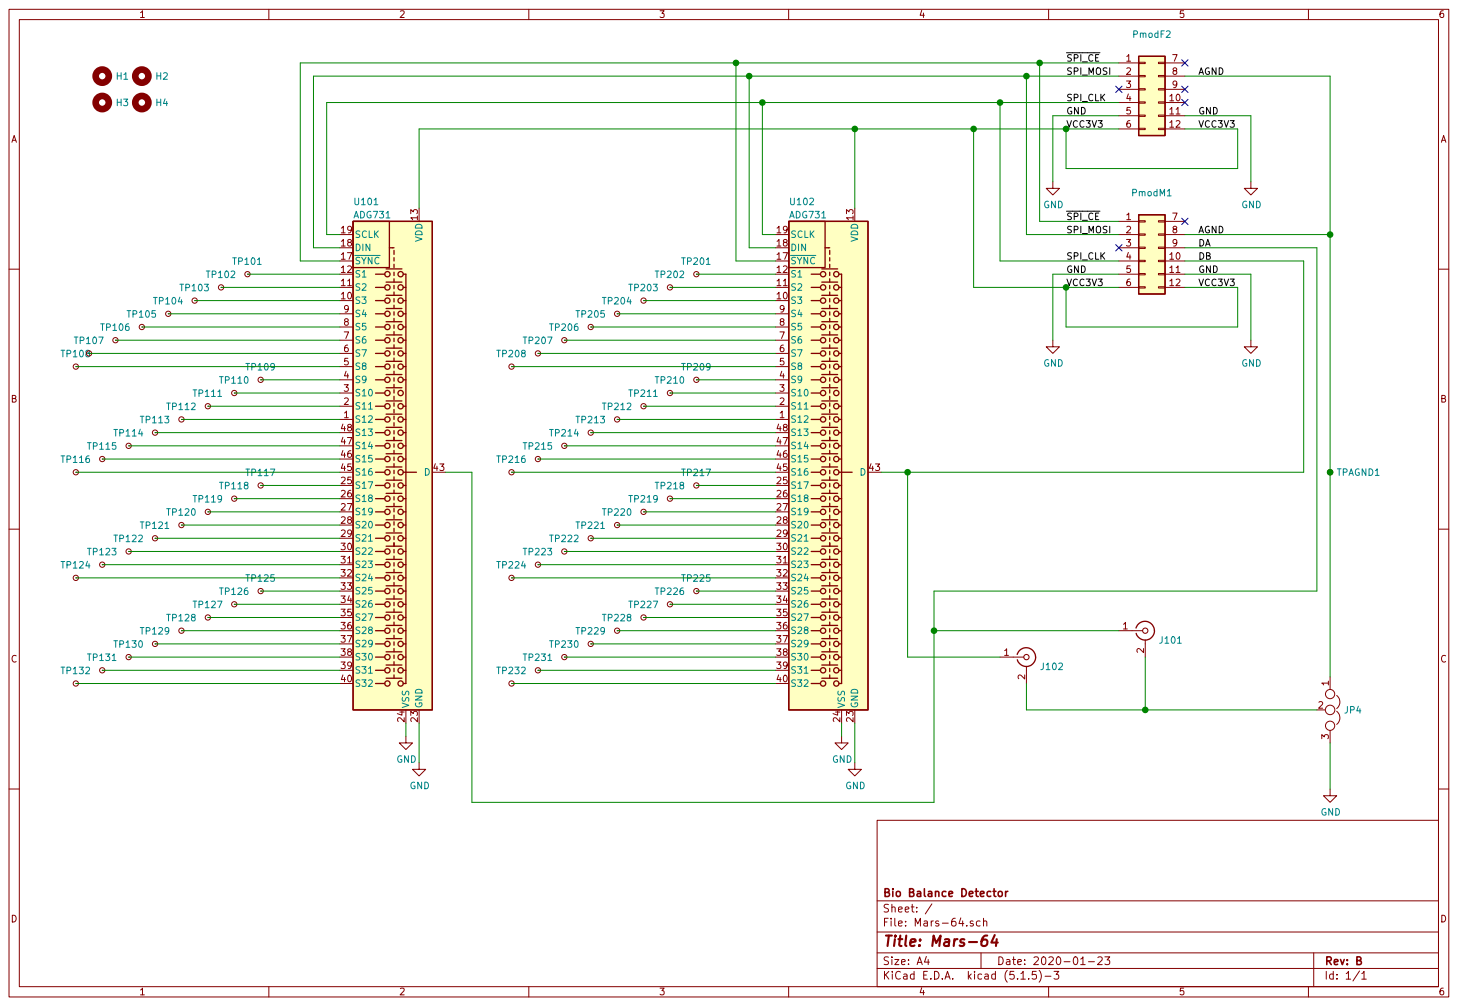
[picture p298: page 1]

3 4 | AGND GND 10 11

6 | 12

File: Mars-64.sch Sheet: / Bio Balance Detector GND
