andrasfuchs/BioBalanceDetector/Hardware/Fabrication/BBDProto04/ArduinoShield/BBDProto04-revC.pdf

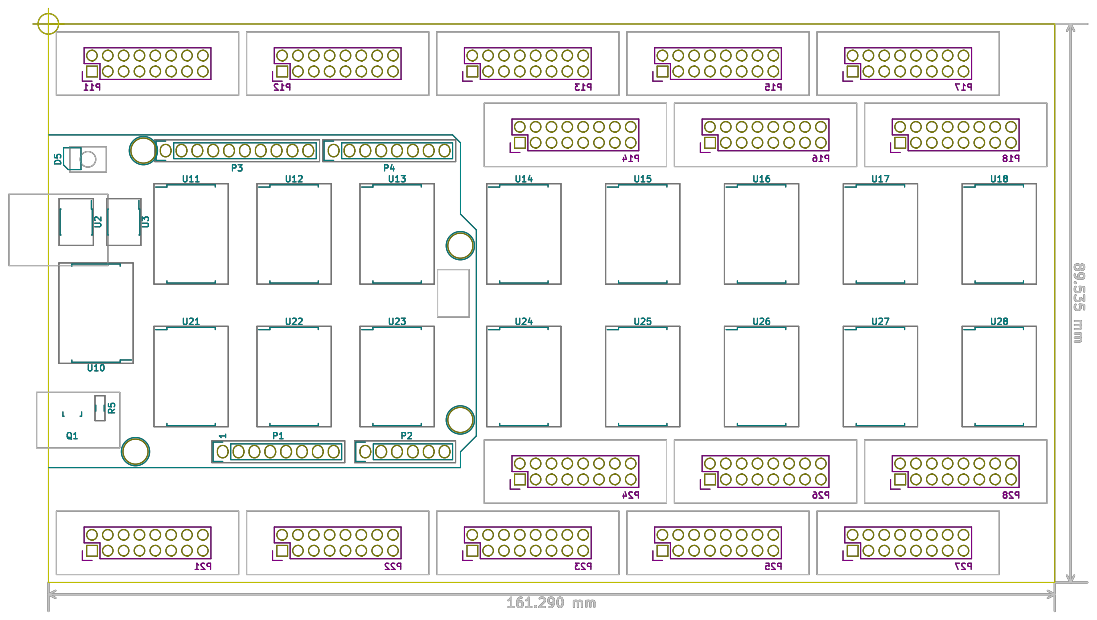
[picture p299: page 1]
