andrasfuchs/BioBalanceDetector/Hardware/Fabrication/BBDProto03/ArduinoShield/BBDProto03.pdf

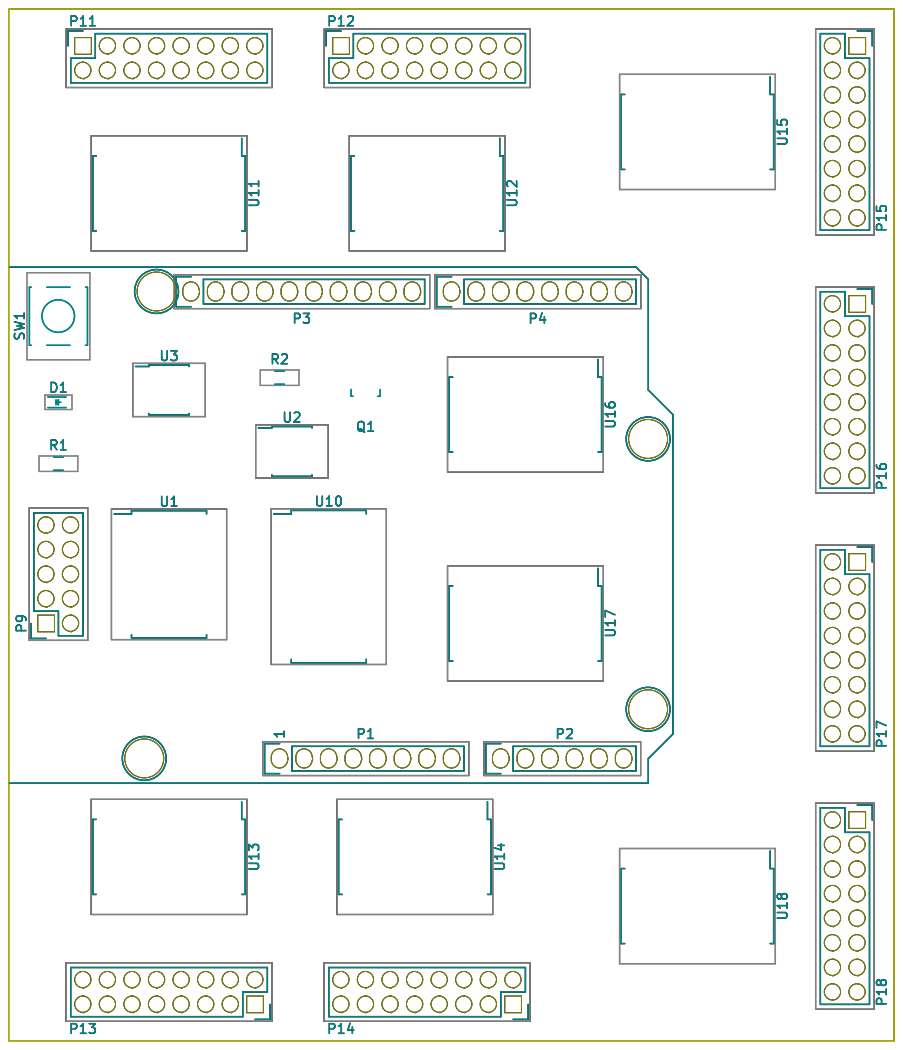
[picture p300: page 1]
