andrasfuchs/BioBalanceDetector/Business/Branding/Business-Cards_AndrasFuchs/horizontal_bc_front_02.pdf

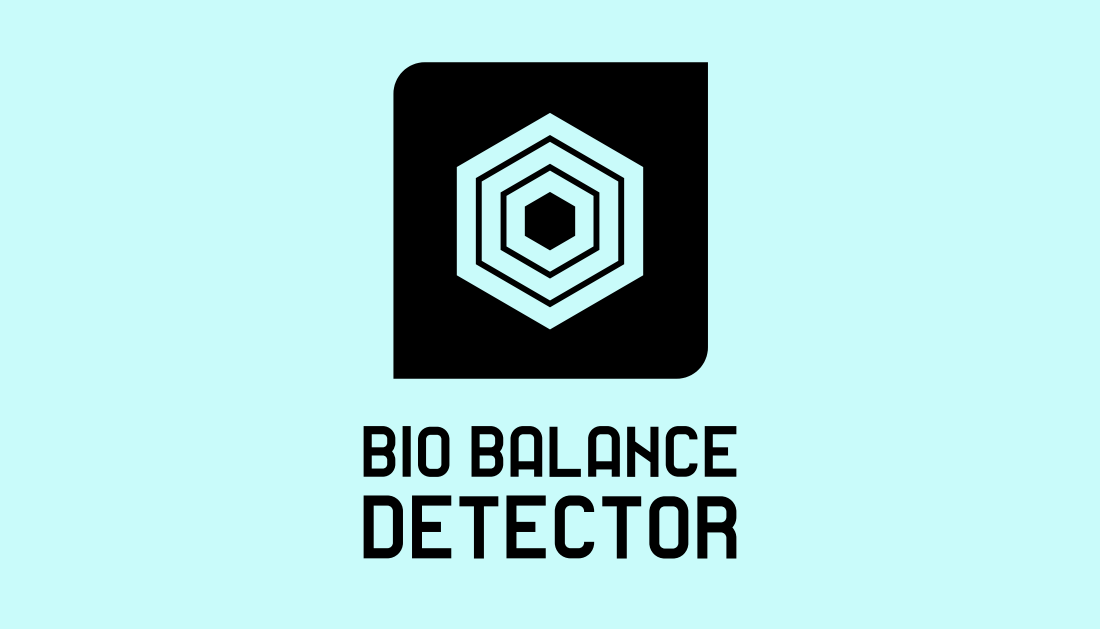
[picture p301: page 1]
