andrasfuchs/BioBalanceDetector/Software/Source/BBDProto05/Mercury/Mercury-16/src/config/conf_dac.h

/*
 * conf_dac.h
 *
 * Created: 2017-03-07 15:08:09
 *  Author: Andras
 */ 


#ifndef CONF_DAC_H_
#define CONF_DAC_H_

#define EMITTER_DAC            DACB
#define EMITTER_DAC_CHANNEL    DAC_CH0

#define SPEAKER_DAC            DACB
#define SPEAKER_DAC_CHANNEL    DAC_CH1

#endif /* CONF_DAC_H_ */
